Panda381/BarePi/_www/img/BarePi_TestLed5_m.jpg

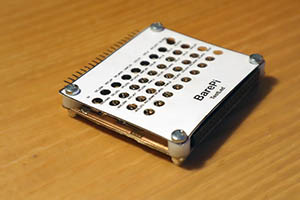
_www/img/BarePi_TestLed5_m.jpg
