Panda381/BarePi/_www/img/BarePi_TestLed1_m.jpg

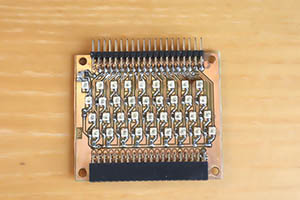
_www/img/BarePi_TestLed1_m.jpg
