Panda381/BarePi/_www/img/BarePi.jpg

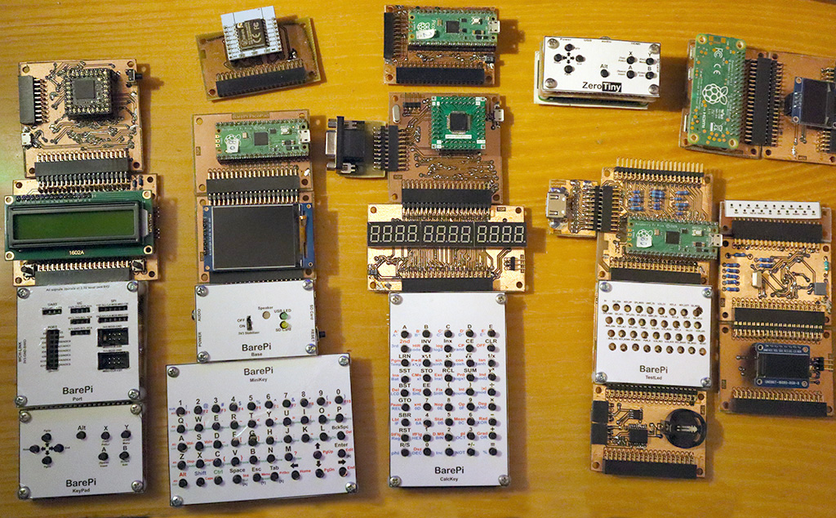
_www/img/BarePi.jpg
