Panda381/BarePi/_www/img/BarePi_Base1.jpg

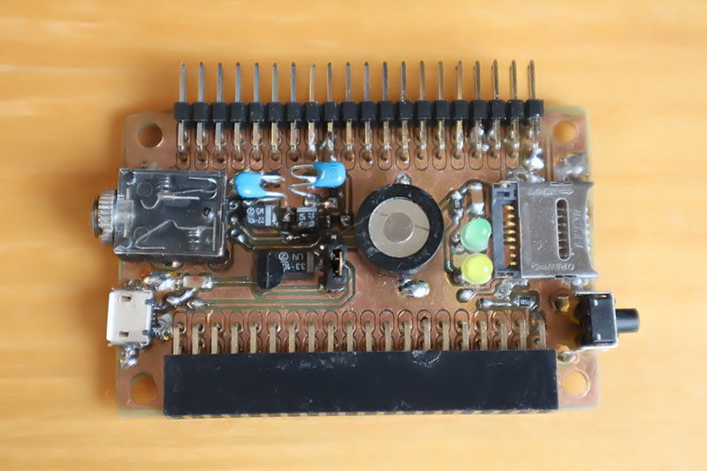
_www/img/BarePi_Base1.jpg
