Panda381/BarePi/_www/img/BarePi_Base3.jpg

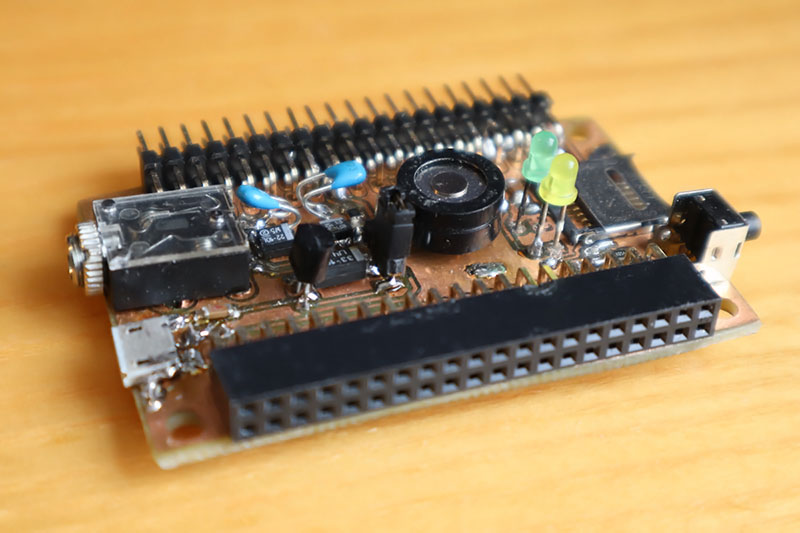
_www/img/BarePi_Base3.jpg
