Panda381/BarePi/Base/BarePi_Base_3D.jpg

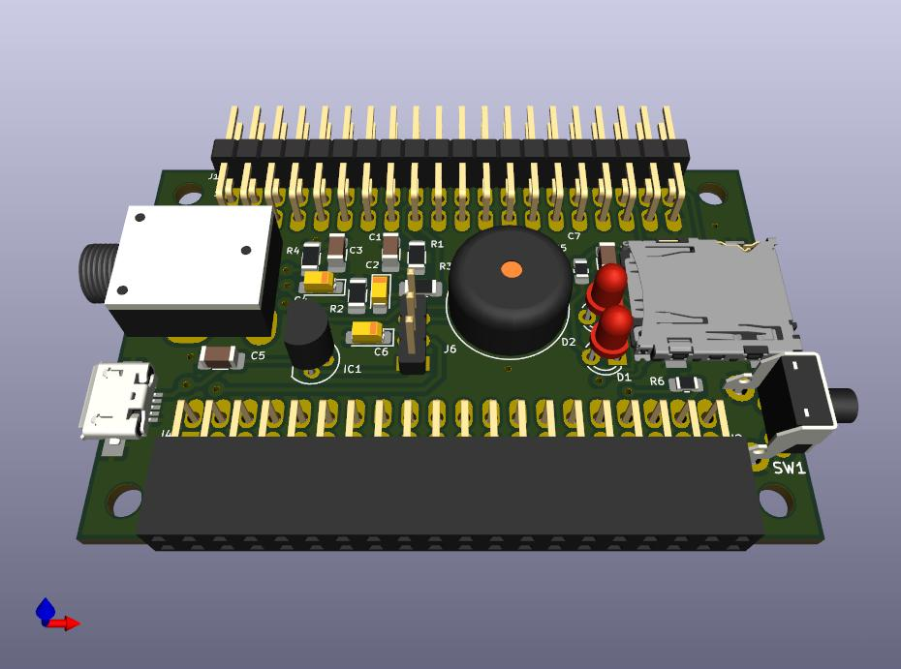
_www/img/BarePi_Base_3D.jpg
