Panda381/BarePi/_www/img/BarePi_Base_3D_bottom_m.jpg

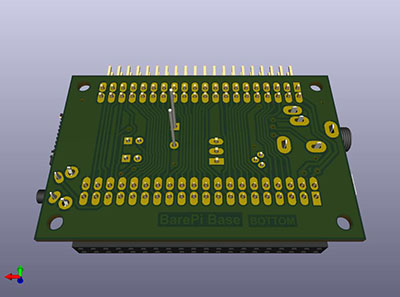
_www/img/BarePi_Base_3D_bottom_m.jpg
