Panda381/BarePi/Base/BarePi_Base_bottom.png

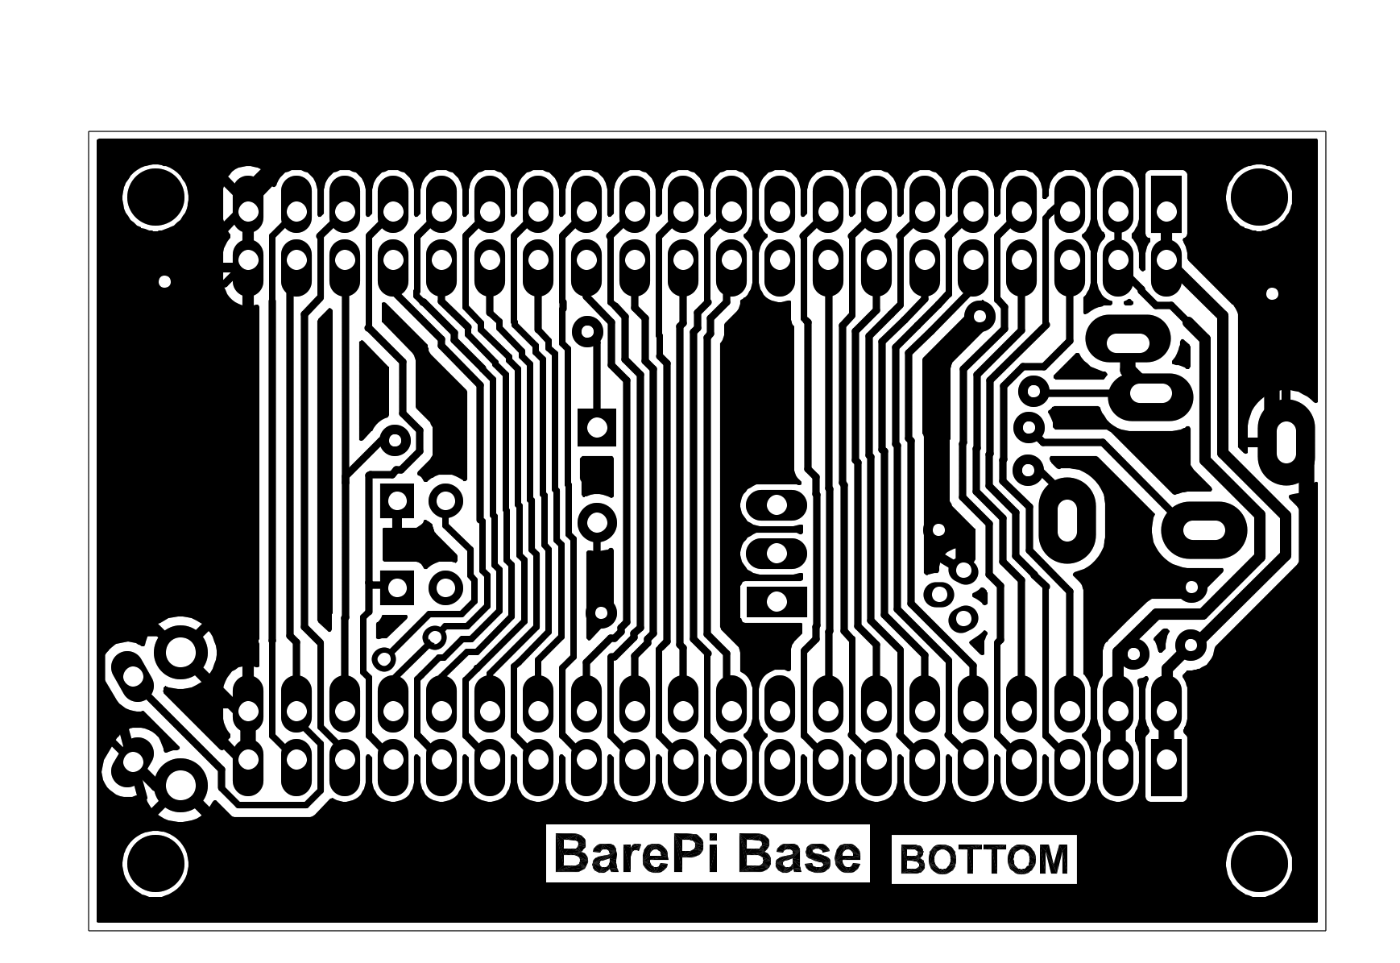
_www/img/BarePi_Base_bottom.png
