Panda381/BarePi/Base/BarePi_Base_diagram.png

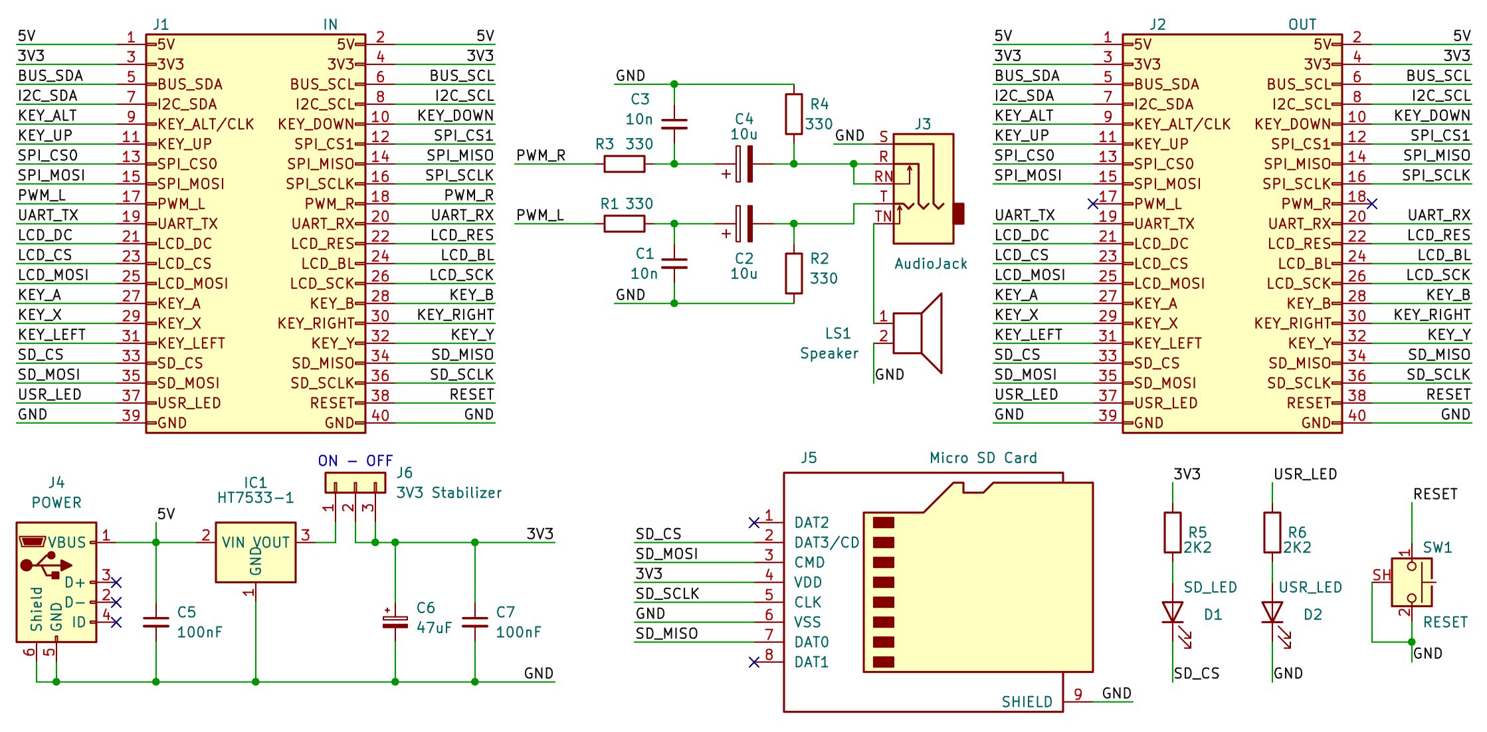
_www/img/BarePi_Base_diagram.png
