Panda381/BarePi/_www/img/BarePi_Base_label_m.jpg

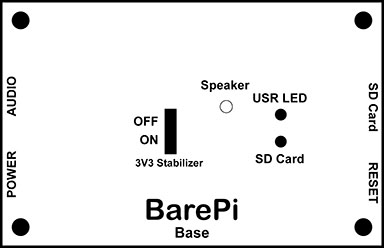
_www/img/BarePi_Base_label_m.jpg
