Panda381/BarePi/_www/img/BarePi_BusExp1.jpg

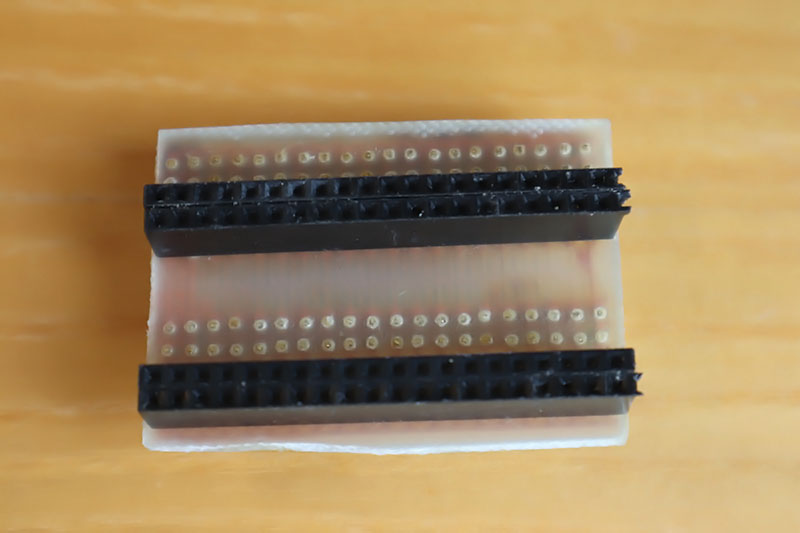
_www/img/BarePi_BusExp1.jpg
