Panda381/BarePi/_www/img/BarePi_BusExp2_m.jpg

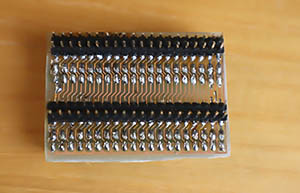
_www/img/BarePi_BusExp2_m.jpg
