Panda381/BarePi/_www/img/BarePi_BusExp3.jpg

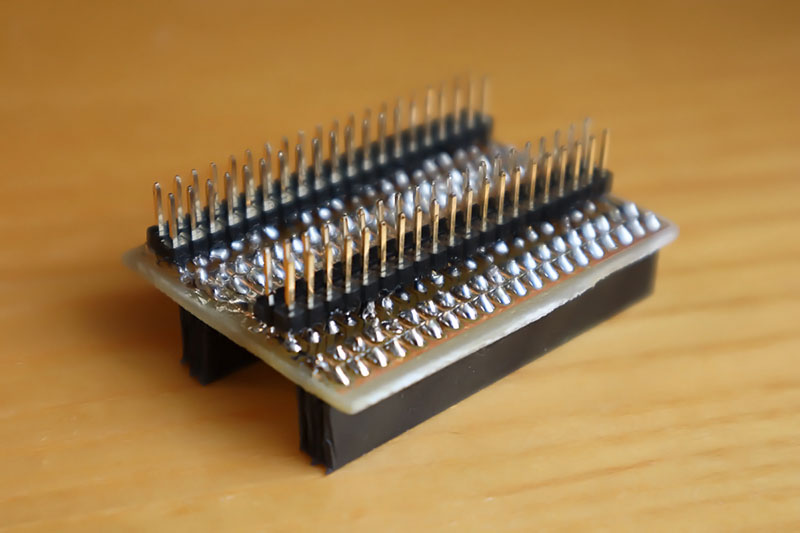
_www/img/BarePi_BusExp3.jpg
