Panda381/BarePi/BusExp/BarePi_BusExp_3D_bottom.jpg

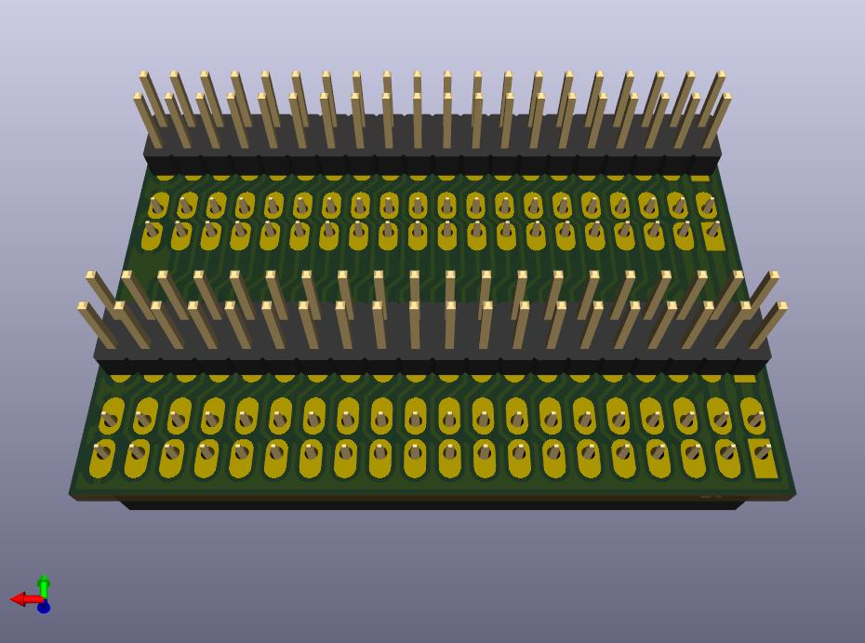
_www/img/BarePi_BusExp_3D_bottom.jpg
