Panda381/BarePi/_www/img/BarePi_BusExp_bottom_m.jpg

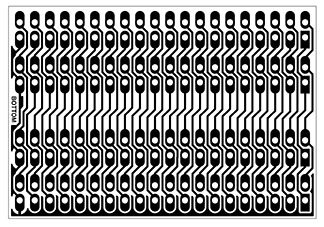
_www/img/BarePi_BusExp_bottom_m.jpg
