Panda381/BarePi/_www/img/BarePi_BusExp_diagram_m.jpg

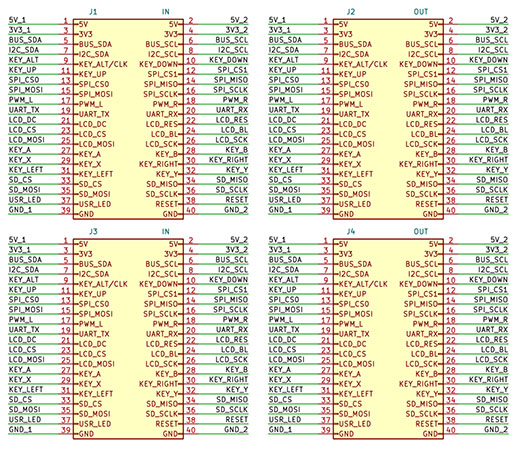
_www/img/BarePi_BusExp_diagram_m.jpg
