Panda381/BarePi/_www/img/BarePi_BusExp_top_m.jpg

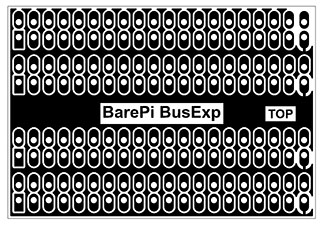
_www/img/BarePi_BusExp_top_m.jpg
