Panda381/BarePi/_www/img/BarePi_CalcKey2_m.jpg

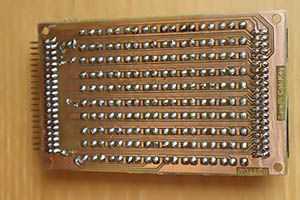
_www/img/BarePi_CalcKey2_m.jpg
