Panda381/BarePi/_www/img/BarePi_CalcKey3.jpg

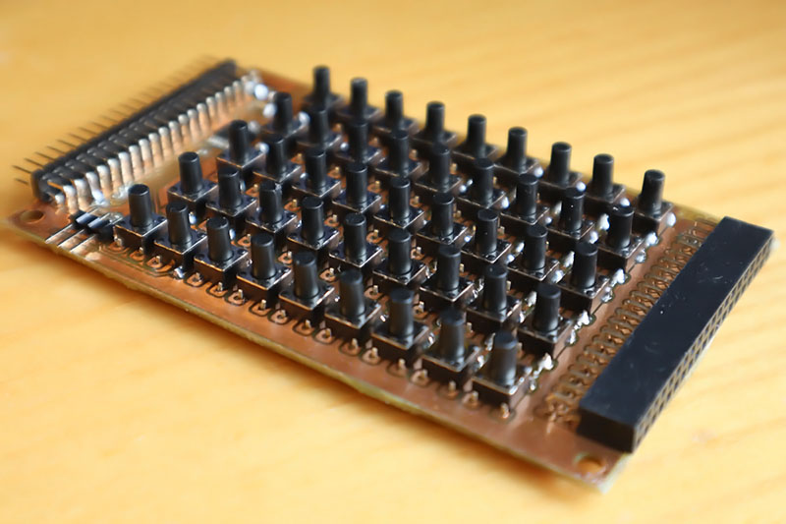
_www/img/BarePi_CalcKey3.jpg
