Panda381/BarePi/CalcKey/BarePi_CalcKey_bottom.png

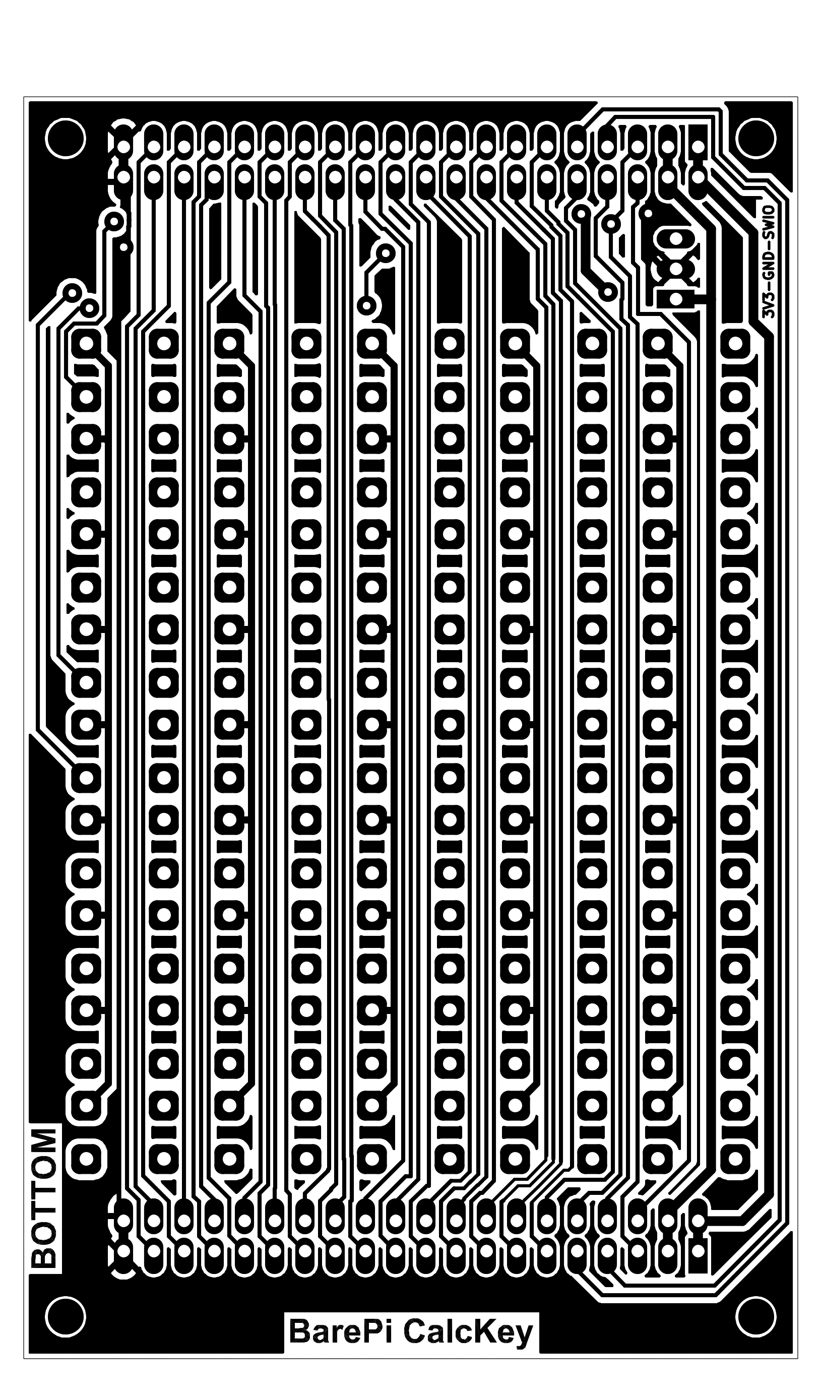
_www/img/BarePi_CalcKey_bottom.png
