Panda381/BarePi/_www/img/BarePi_CalcKey_mounting_m.jpg

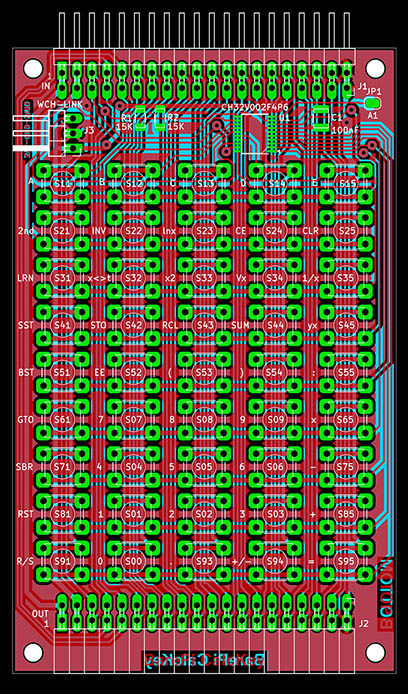
_www/img/BarePi_CalcKey_mounting_m.jpg
