Panda381/BarePi/CalcKey/BarePi_CalcKey_top.png

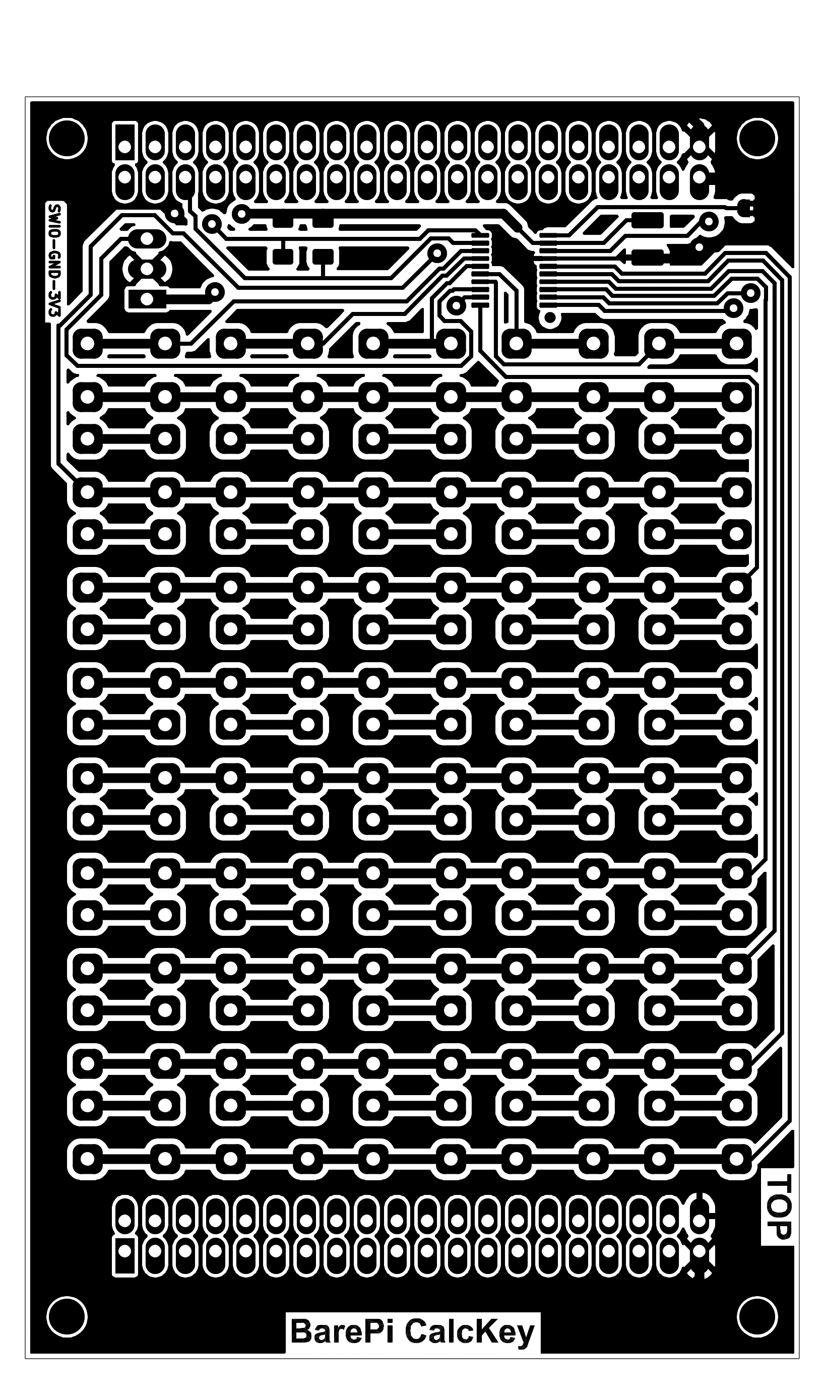
_www/img/BarePi_CalcKey_top.png
