Panda381/BarePi/_www/img/BarePi_DispHDMI1.jpg

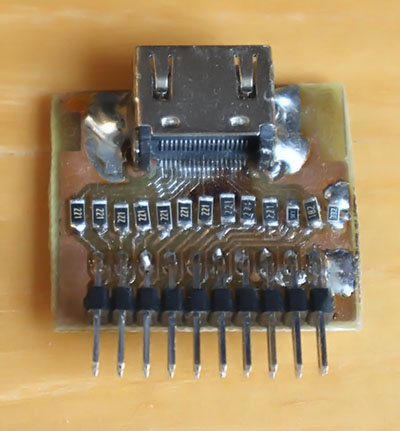
_www/img/BarePi_DispHDMI1.jpg
