Panda381/BarePi/DispHDMI/BarePi_DispHDMI_3D.jpg

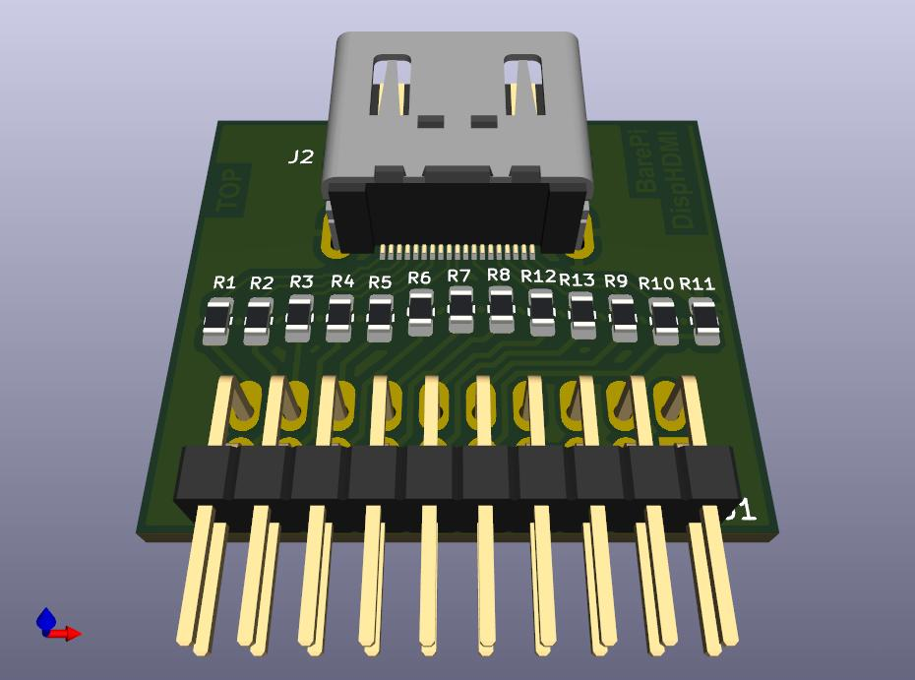
_www/img/BarePi_DispHDMI_3D.jpg
