Panda381/BarePi/DispHDMI/BarePi_DispHDMI_bottom.png

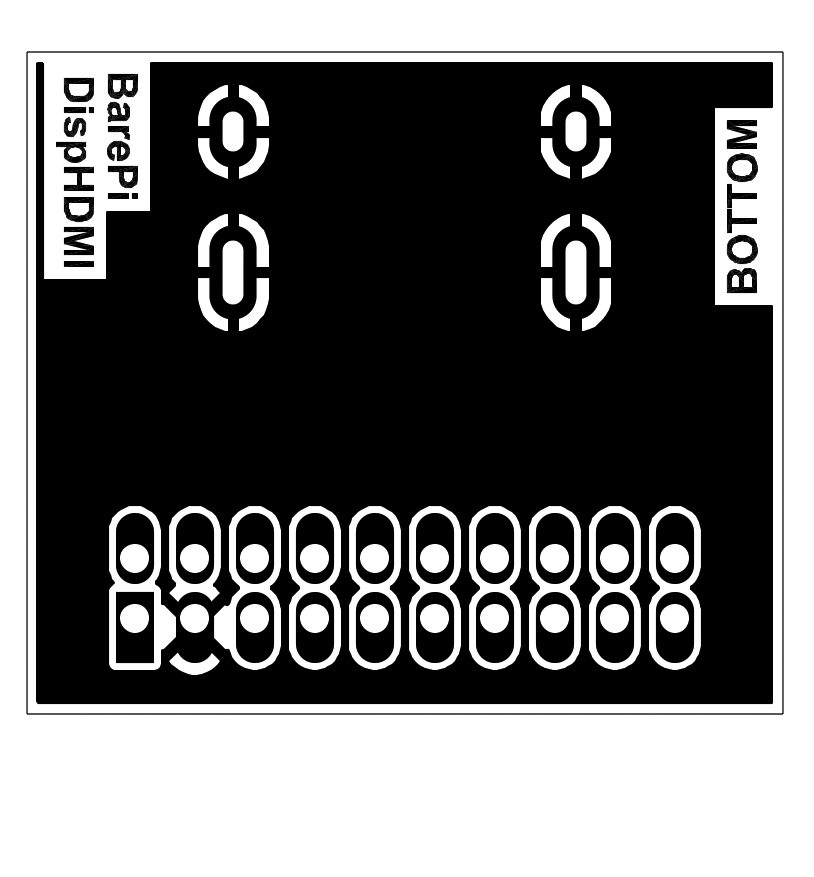
_www/img/BarePi_DispHDMI_bottom.png
