Panda381/BarePi/DispHDMI/BarePi_DispHDMI_diagram.png

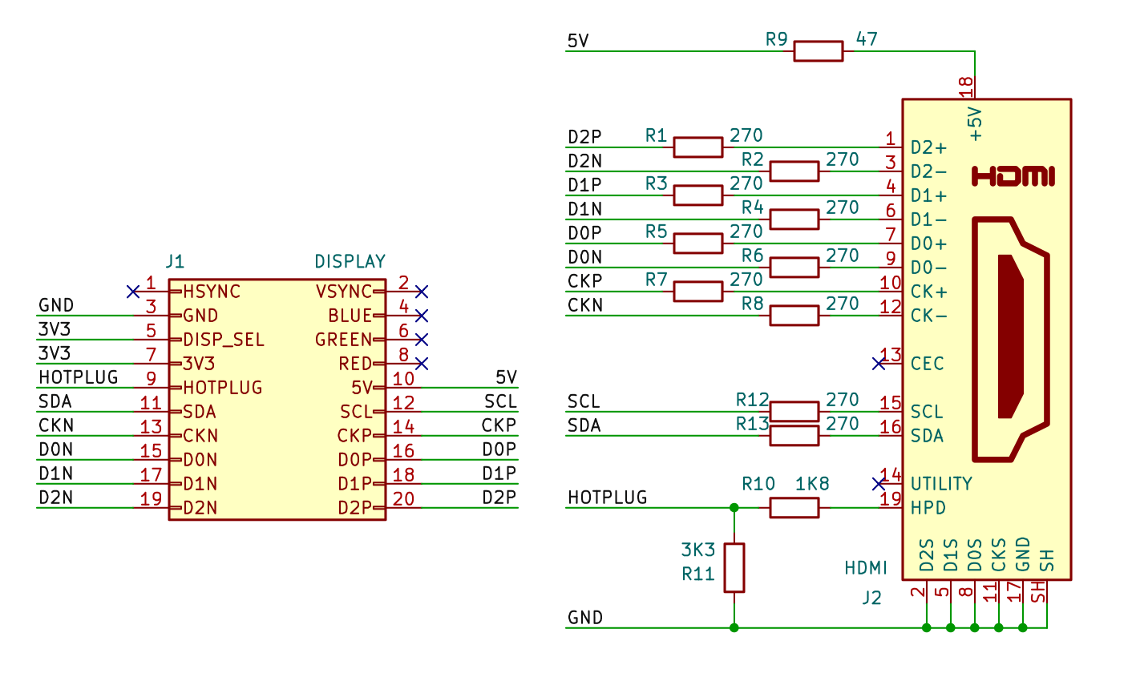
_www/img/BarePi_DispHDMI_diagram.png
