Panda381/BarePi/DispHDMI/BarePi_DispHDMI_mounting.jpg

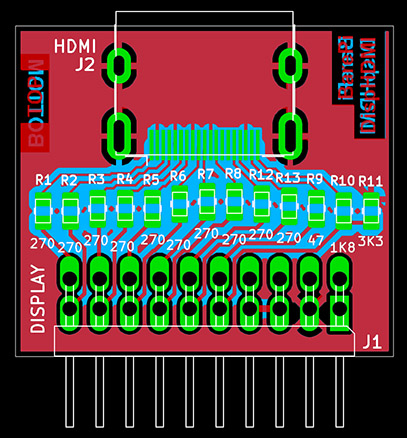
_www/img/BarePi_DispHDMI_mounting.jpg
