Panda381/BarePi/DispHDMI/BarePi_DispHDMI_top.png

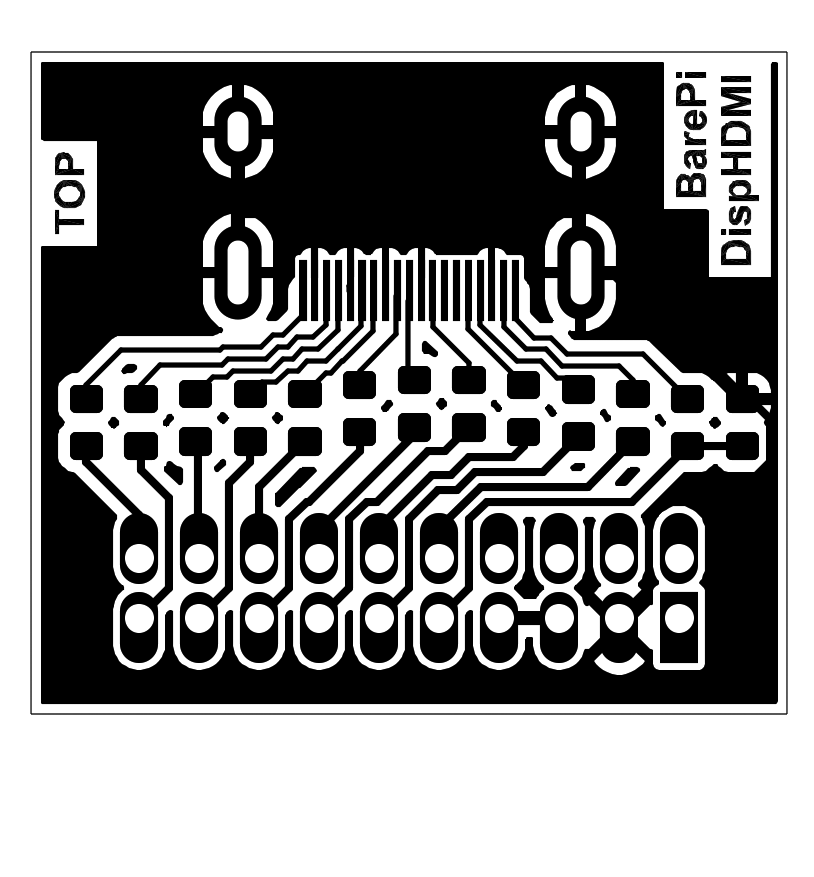
_www/img/BarePi_DispHDMI_top.png
