Panda381/BarePi/_www/img/BarePi_disppins2_m.jpg

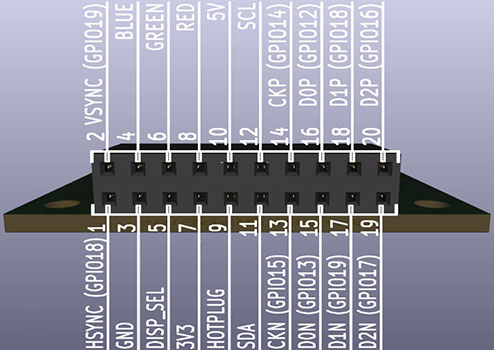
_www/img/BarePi_disppins2_m.jpg
