Panda381/BarePi/_www/img/BarePi_disppins.png

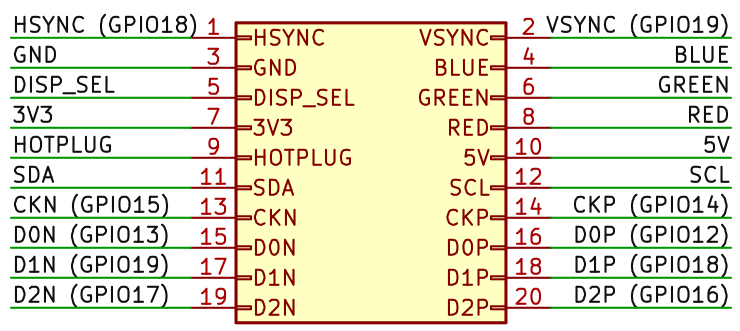
_www/img/BarePi_disppins.png
