Panda381/BarePi/_www/img/BarePi_DispVGA1_m.jpg

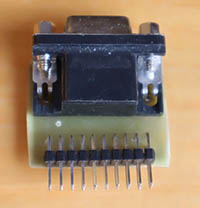
_www/img/BarePi_DispVGA1_m.jpg
