Panda381/BarePi/_www/img/BarePi_DispVGA2.jpg

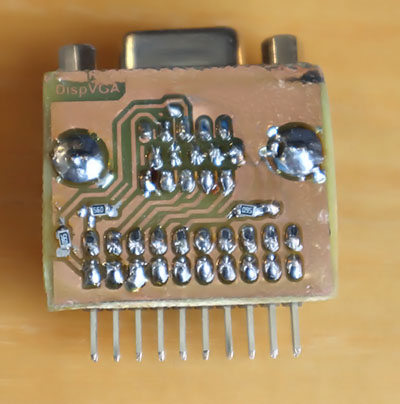
_www/img/BarePi_DispVGA2.jpg
