Panda381/BarePi/_www/img/BarePi_DispVGA_3D_bottom_m.jpg

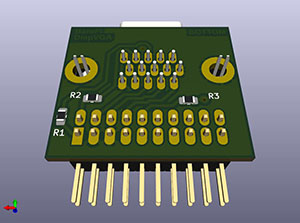
_www/img/BarePi_DispVGA_3D_bottom_m.jpg
