Panda381/BarePi/_www/img/BarePi_DispVGA_diagram_m.jpg

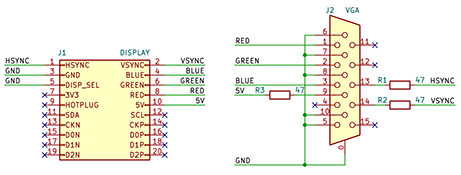
_www/img/BarePi_DispVGA_diagram_m.jpg
