Panda381/BarePi/DispVGA/BarePi_DispVGA_mounting.jpg

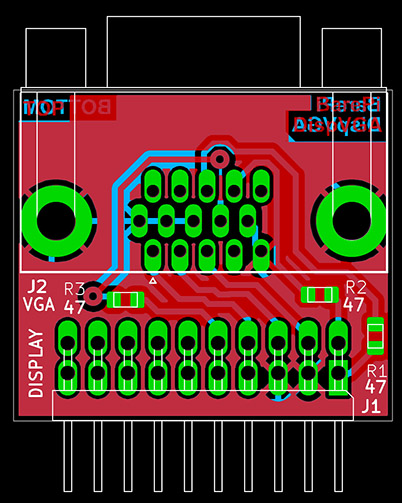
_www/img/BarePi_DispVGA_mounting.jpg
