Panda381/BarePi/_www/img/BarePi_ExtDisp1.jpg

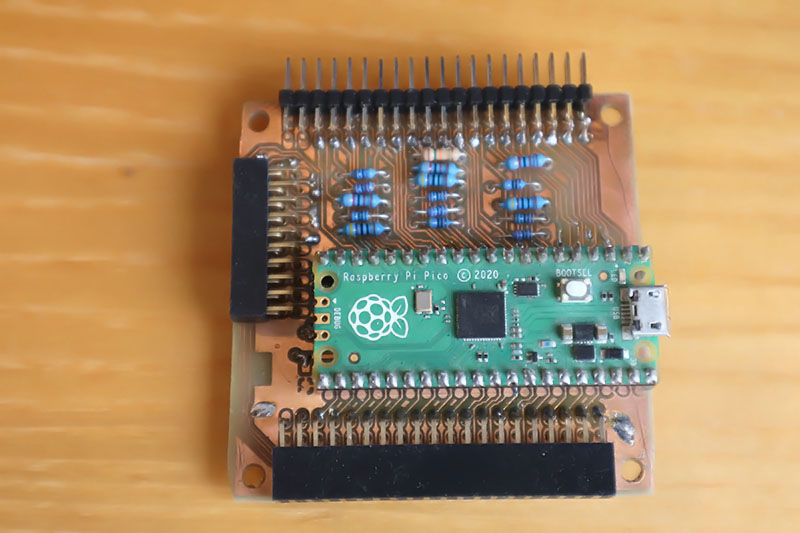
_www/img/BarePi_ExtDisp1.jpg
