Panda381/BarePi/_www/img/BarePi_ExtDisp3_m.jpg

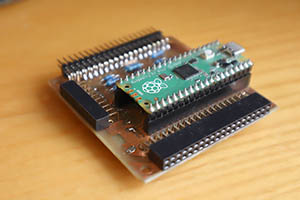
_www/img/BarePi_ExtDisp3_m.jpg
