Panda381/BarePi/_www/img/BarePi_ExtDisp.jpg

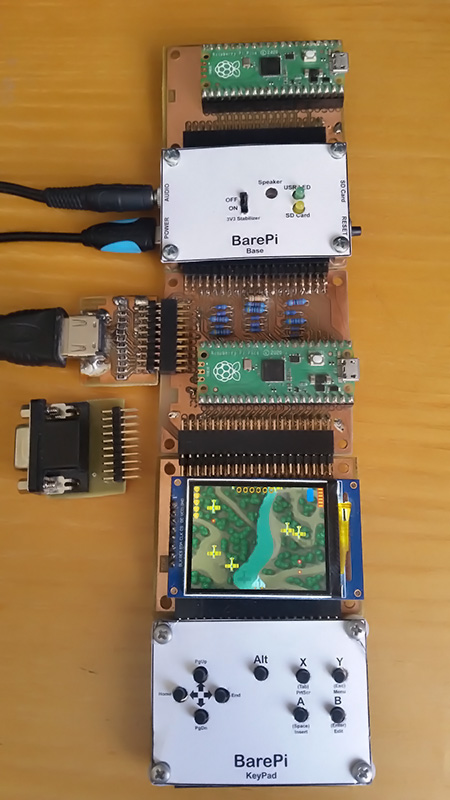
_www/img/BarePi_ExtDisp.jpg
