Panda381/BarePi/ExtDisp/BarePi_ExtDisp_3D.jpg

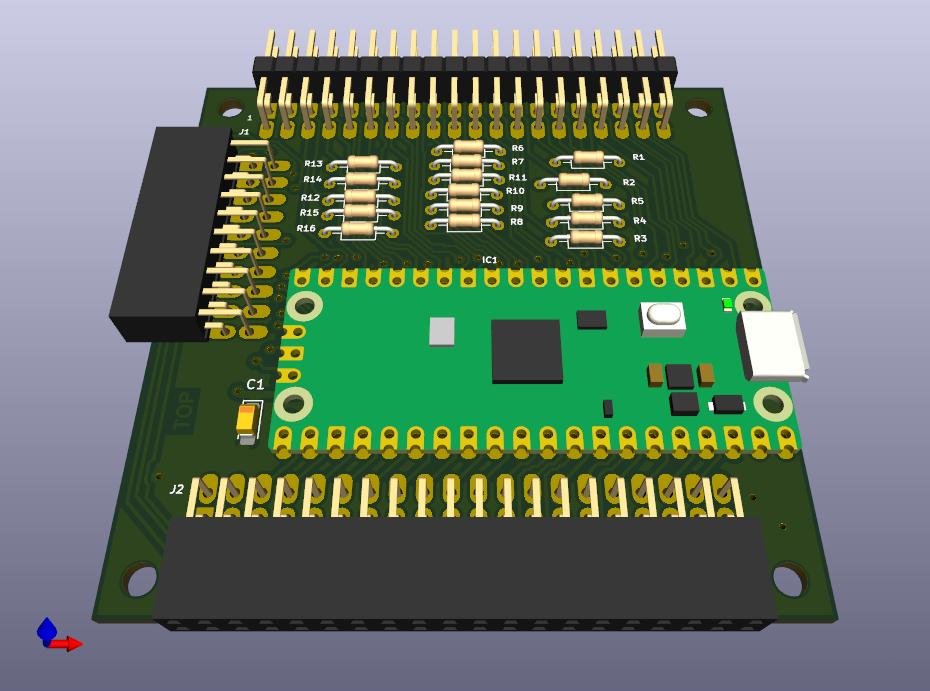
_www/img/BarePi_ExtDisp_3D.jpg
