Panda381/BarePi/ExtDisp/BarePi_ExtDisp_bottom.png

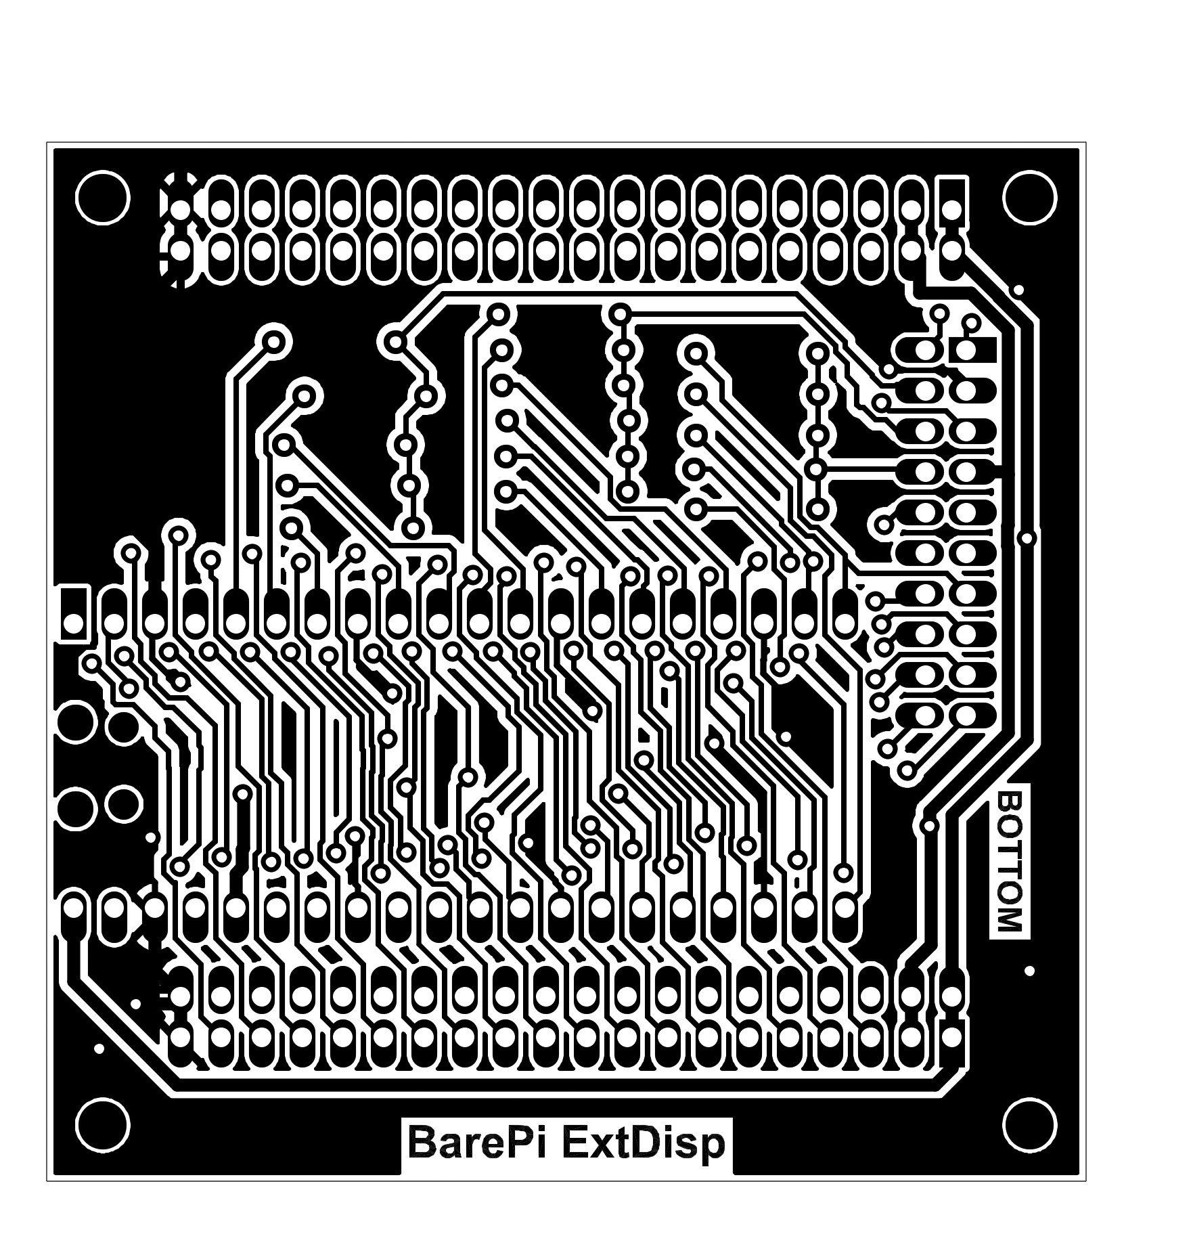
_www/img/BarePi_ExtDisp_bottom.png
