Panda381/BarePi/ExtDisp/BarePi_ExtDisp_diagram.png

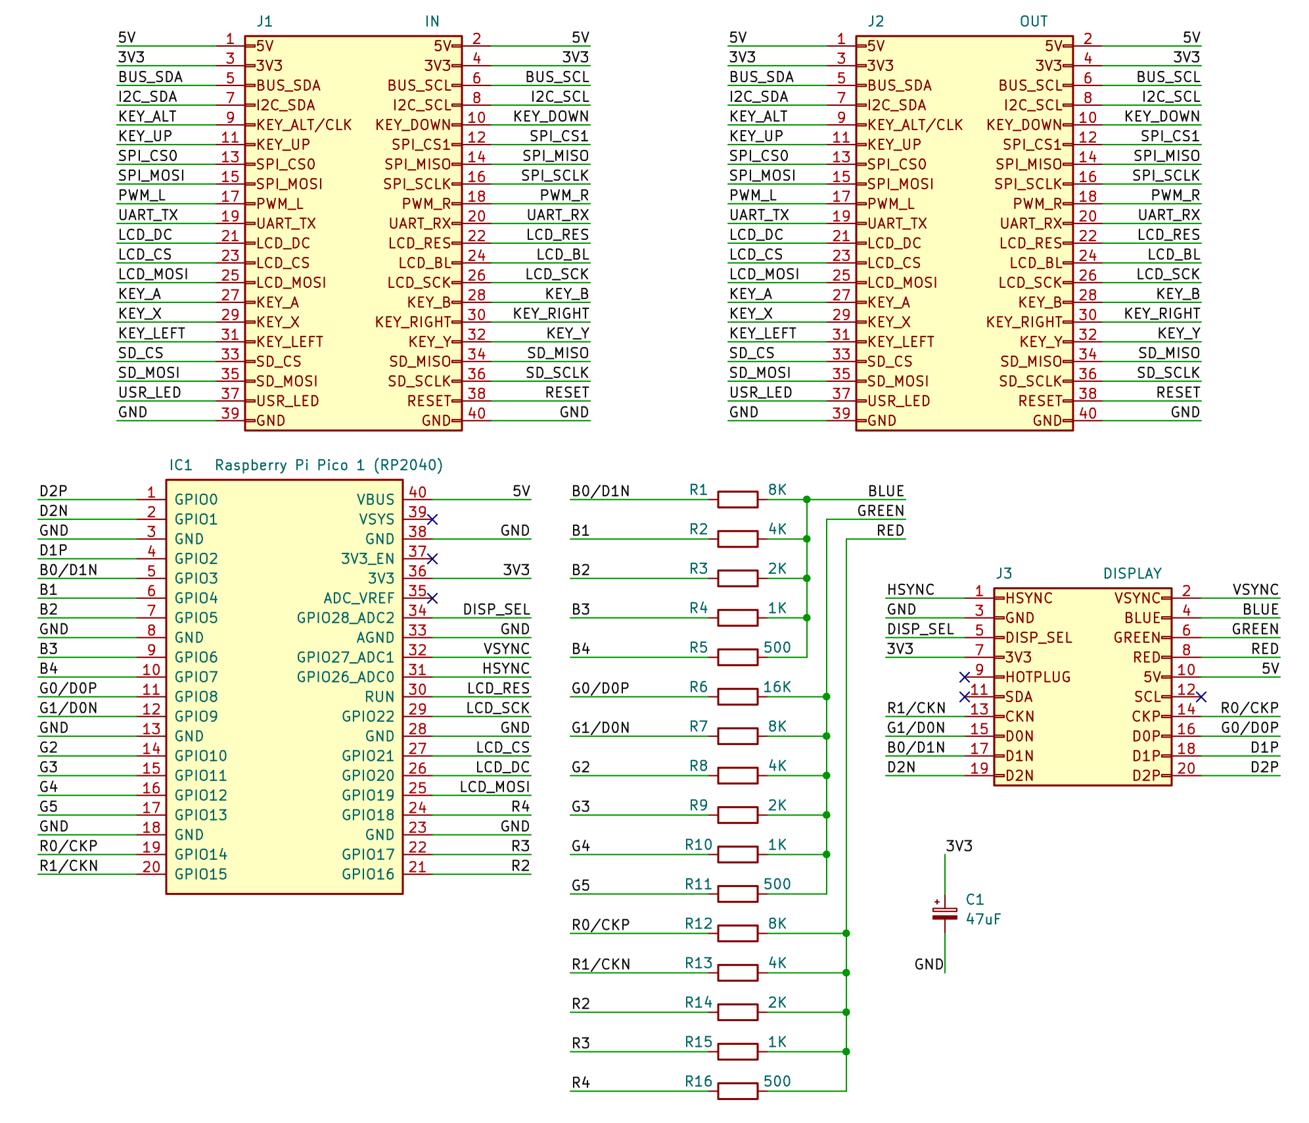
_www/img/BarePi_ExtDisp_diagram.png
