Panda381/BarePi/_www/img/BarePi_ExtDisp_label_m.jpg

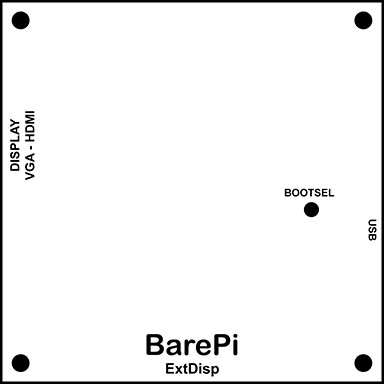
_www/img/BarePi_ExtDisp_label_m.jpg
