Panda381/BarePi/ExtDisp/BarePi_ExtDisp_mounting.jpg

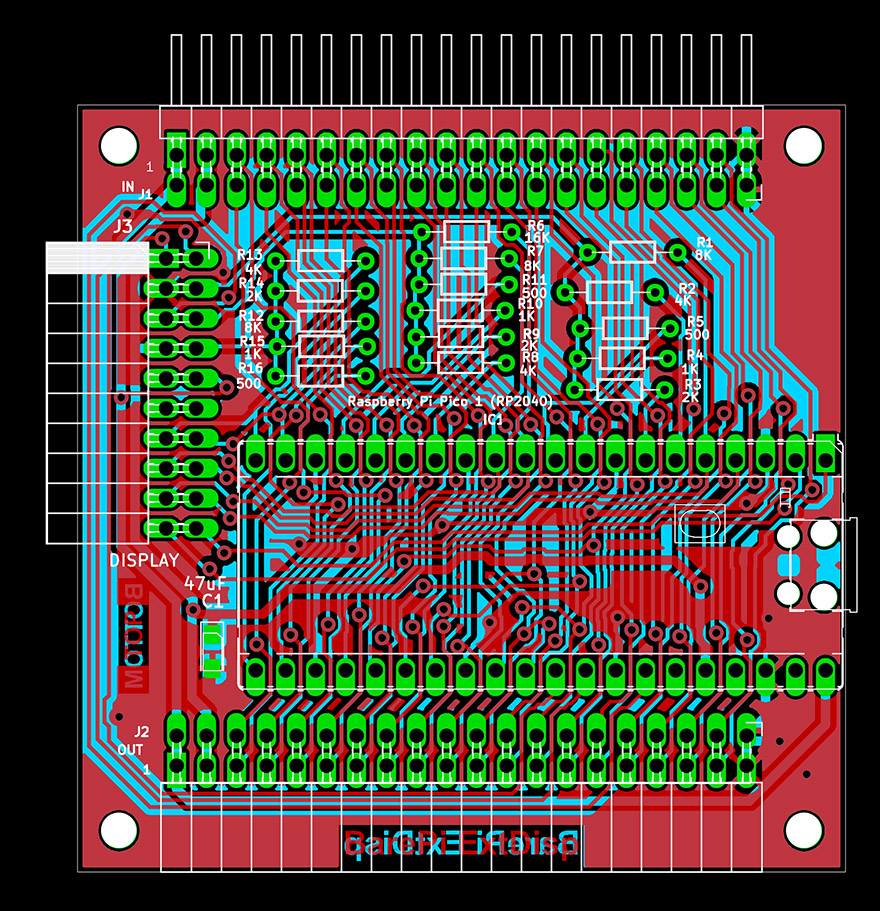
_www/img/BarePi_ExtDisp_mounting.jpg
