Panda381/BarePi/_www/img/BarePi_ExtDisp_top_m.jpg

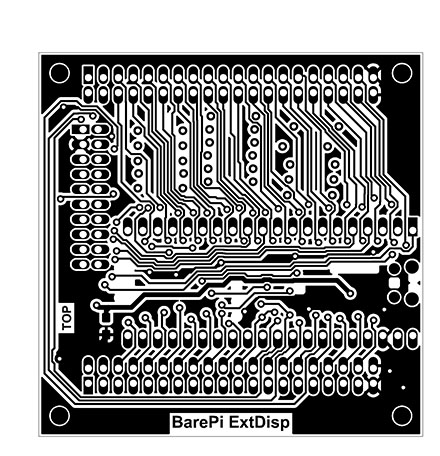
_www/img/BarePi_ExtDisp_top_m.jpg
