Panda381/BarePi/_www/img/BarePi_KeyPad1_m.jpg

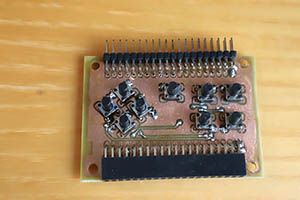
_www/img/BarePi_KeyPad1_m.jpg
