Panda381/BarePi/_www/img/BarePi_KeyPad2.jpg

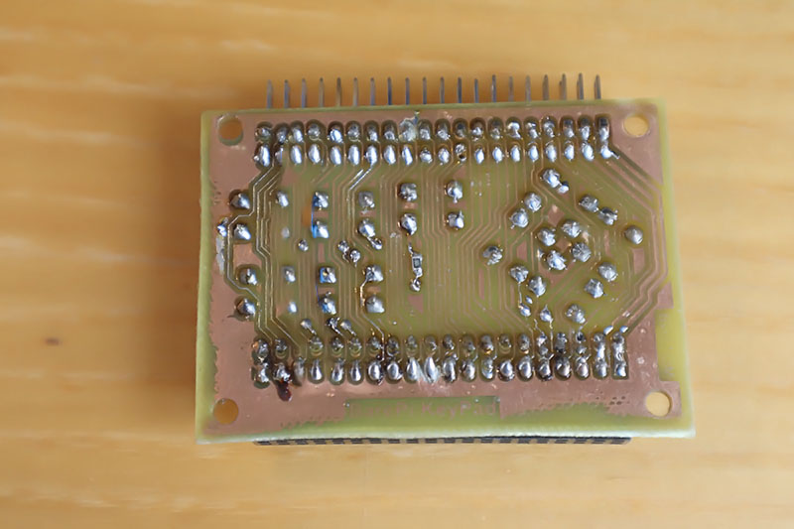
_www/img/BarePi_KeyPad2.jpg
