Panda381/BarePi/_www/img/BarePi_KeyPad3_m.jpg

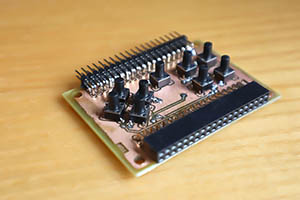
_www/img/BarePi_KeyPad3_m.jpg
