Panda381/BarePi/_www/img/BarePi_KeyPad5.jpg

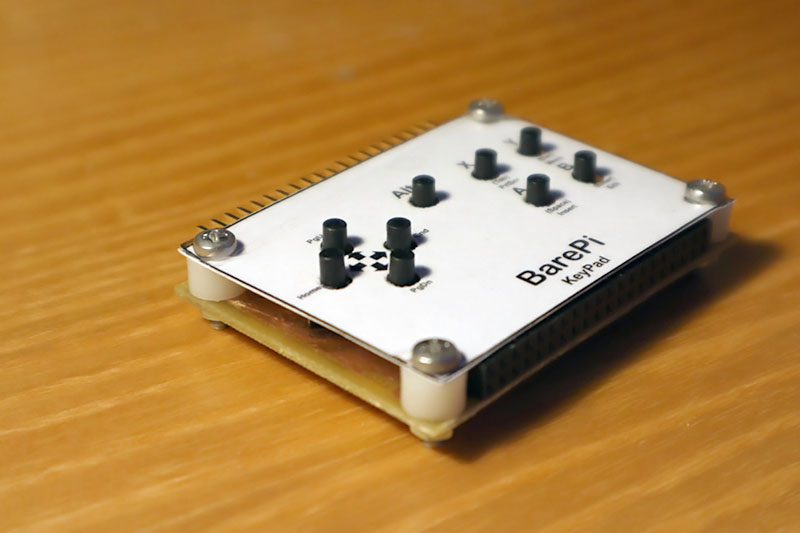
_www/img/BarePi_KeyPad5.jpg
