Panda381/BarePi/_www/img/BarePi_KeyPad_3D_bottom_m.jpg

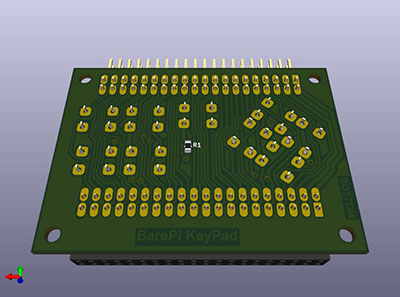
_www/img/BarePi_KeyPad_3D_bottom_m.jpg
