Panda381/BarePi/KeyPad/BarePi_KeyPad_bottom.png

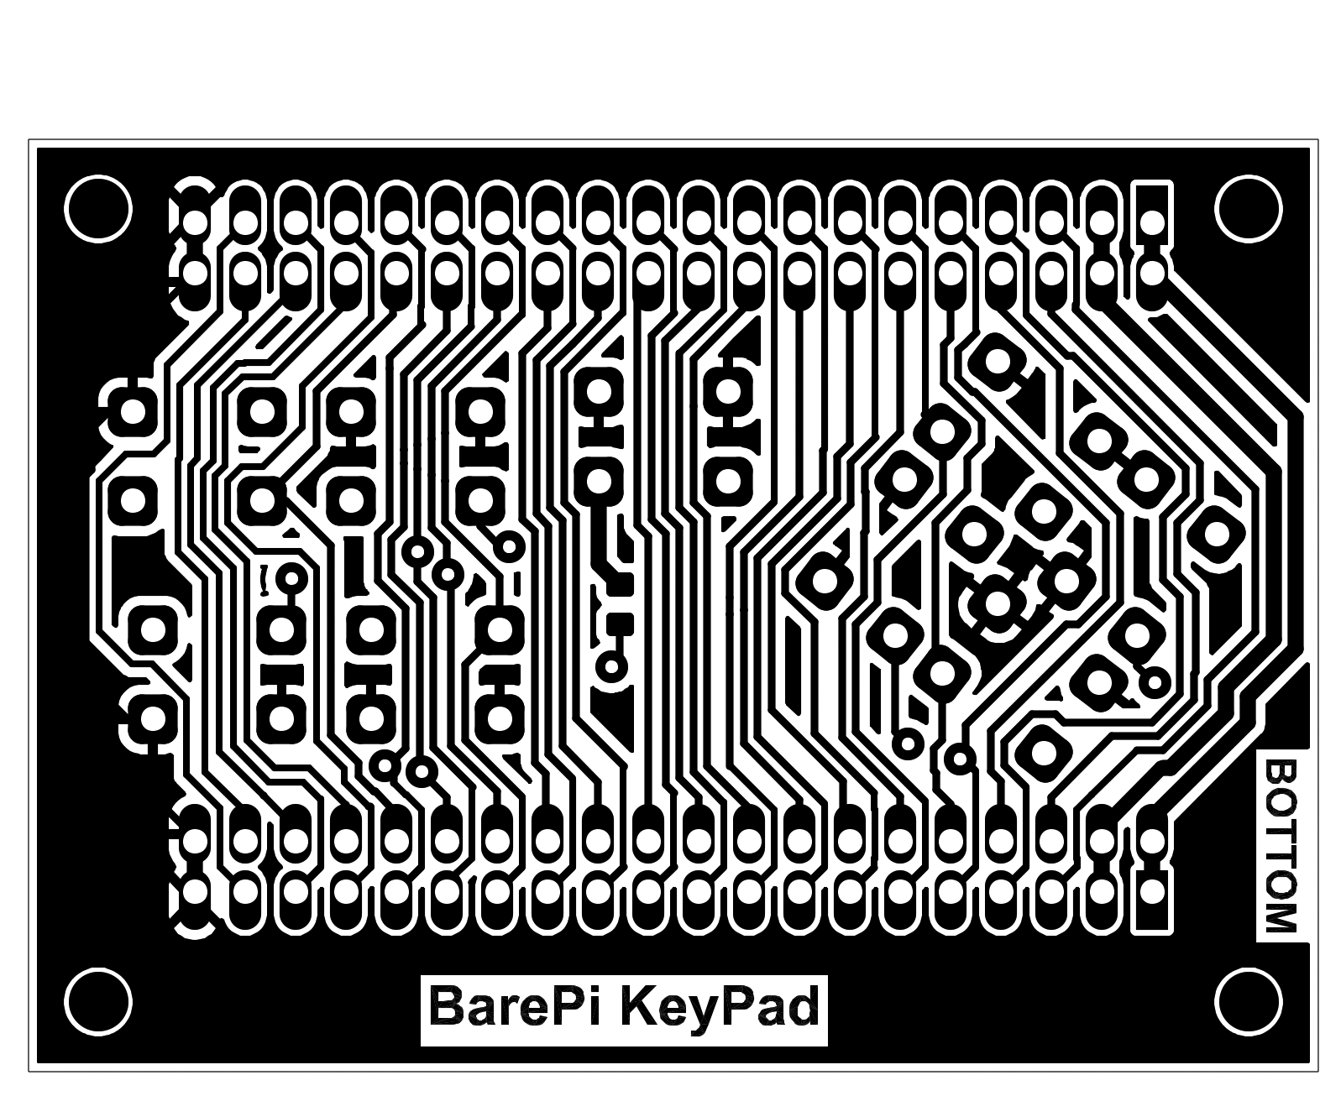
_www/img/BarePi_KeyPad_bottom.png
