Panda381/BarePi/KeyPad/BarePi_KeyPad_label.png

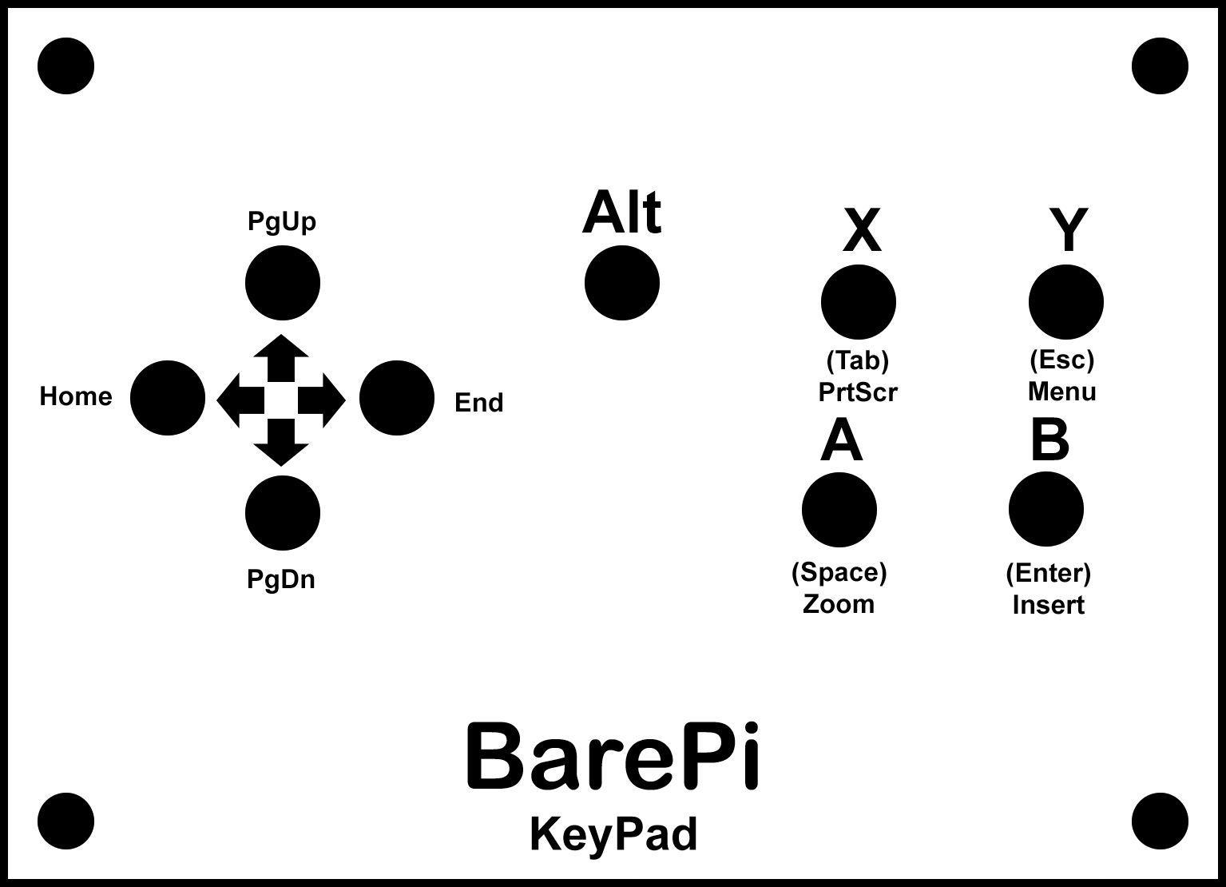
_www/img/BarePi_KeyPad_label.png
