Panda381/BarePi/_www/img/BarePi_KeyPad_mounting_m.jpg

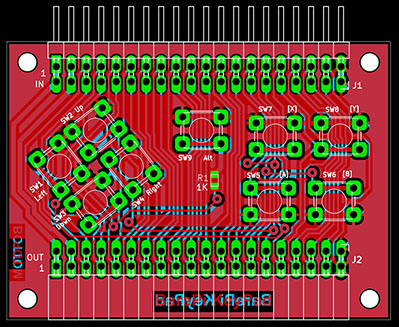
_www/img/BarePi_KeyPad_mounting_m.jpg
