Panda381/BarePi/KeyPad/BarePi_KeyPad_top.png

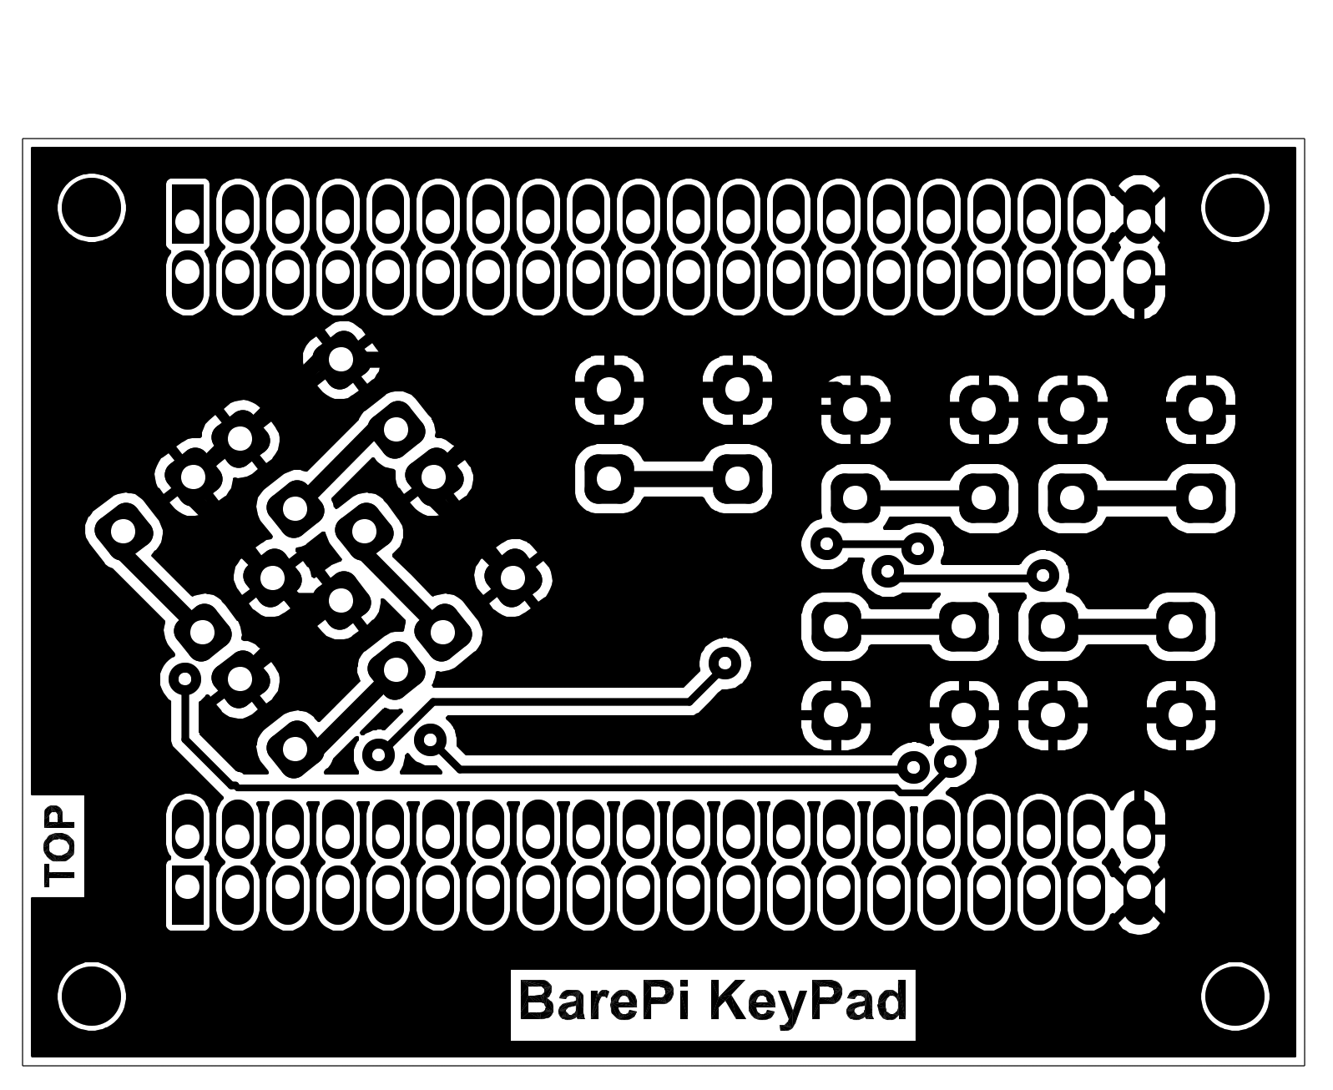
_www/img/BarePi_KeyPad_top.png
