Panda381/BarePi/LCD16x2/BarePi_LCD16x2_3D_bottom.jpg

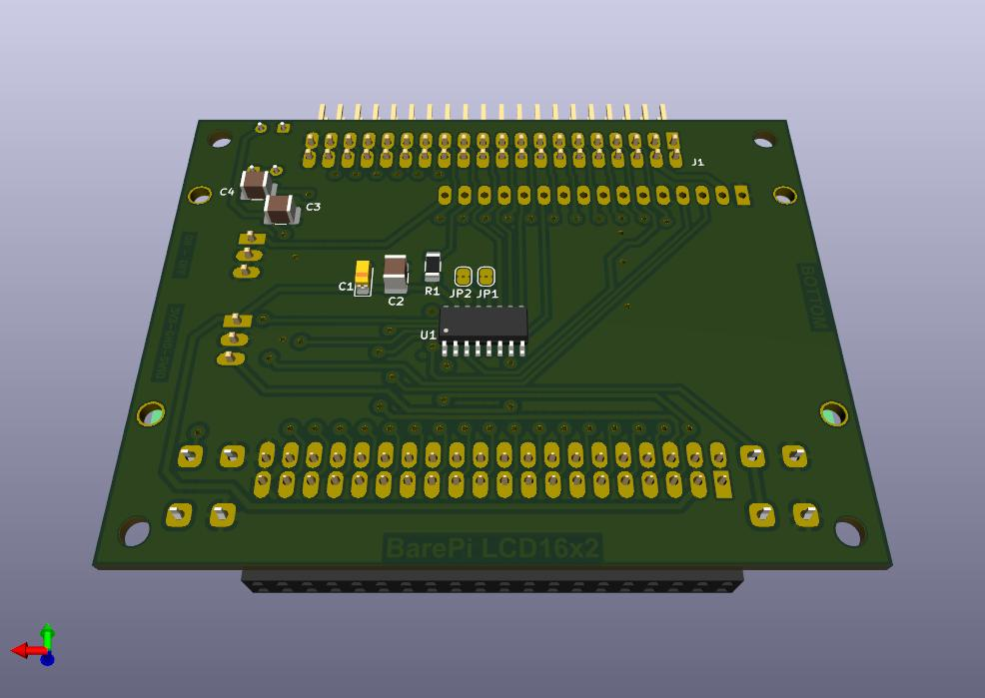
_www/img/BarePi_LCD16x2_3D_bottom.jpg
