Panda381/BarePi/LCD16x2/BarePi_LCD16x2_bottom.png

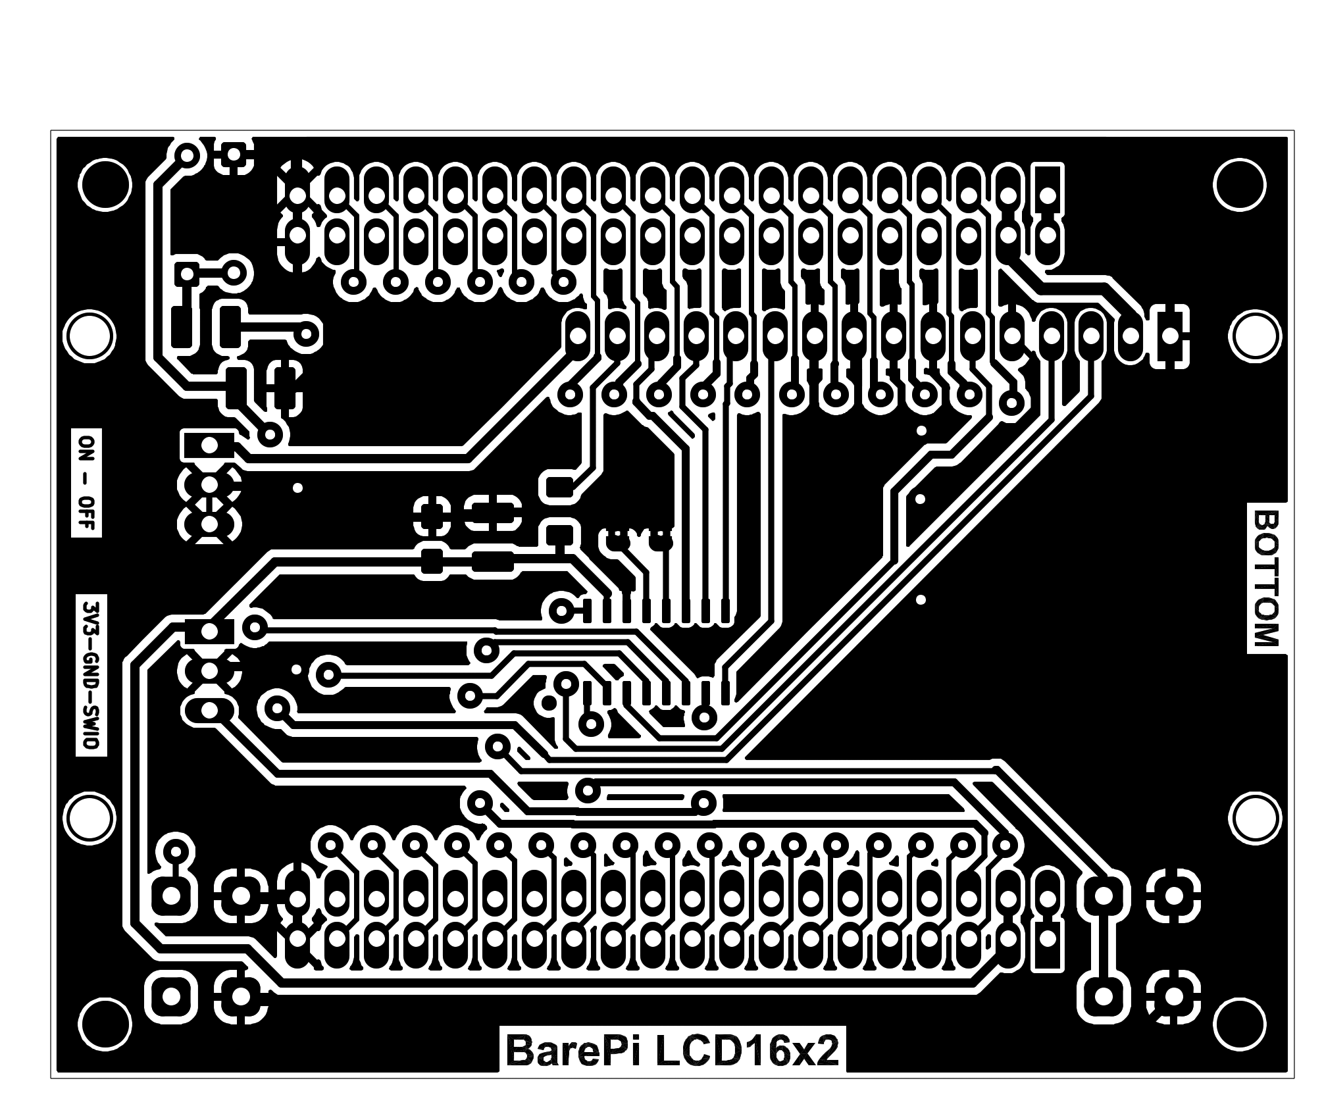
_www/img/BarePi_LCD16x2_bottom.png
