Panda381/BarePi/_www/img/BarePi_LCD16x21.jpg

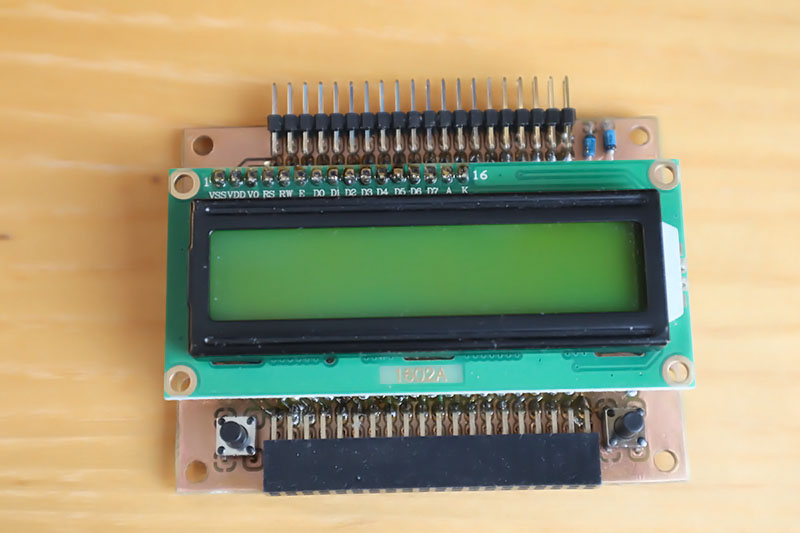
_www/img/BarePi_LCD16x21.jpg
