Panda381/BarePi/_www/img/BarePi_LCD16x23.jpg

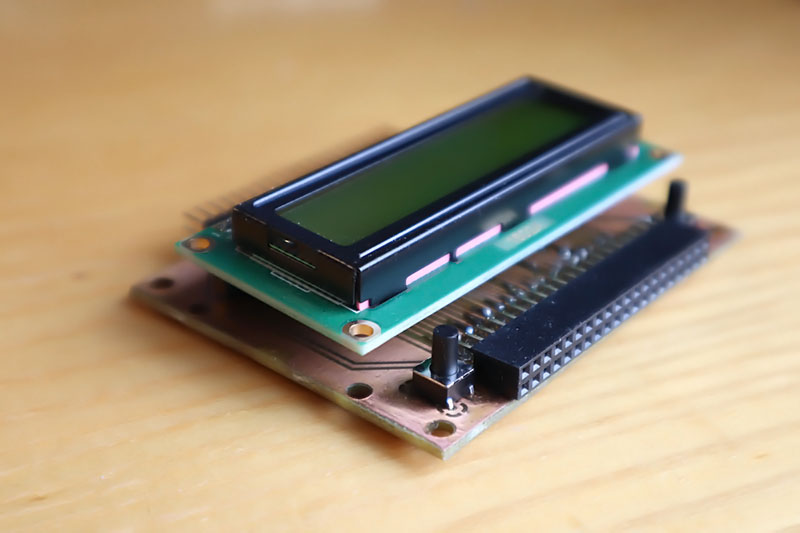
_www/img/BarePi_LCD16x23.jpg
