Panda381/BarePi/LCD160x80/BarePi_LCD160x80_3D.jpg

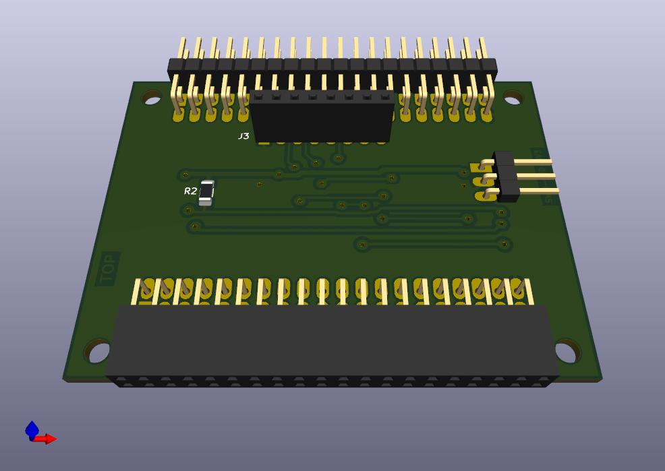
_www/img/BarePi_LCD160x80_3D.jpg
