Panda381/BarePi/LCD160x80/BarePi_LCD160x80_label.png

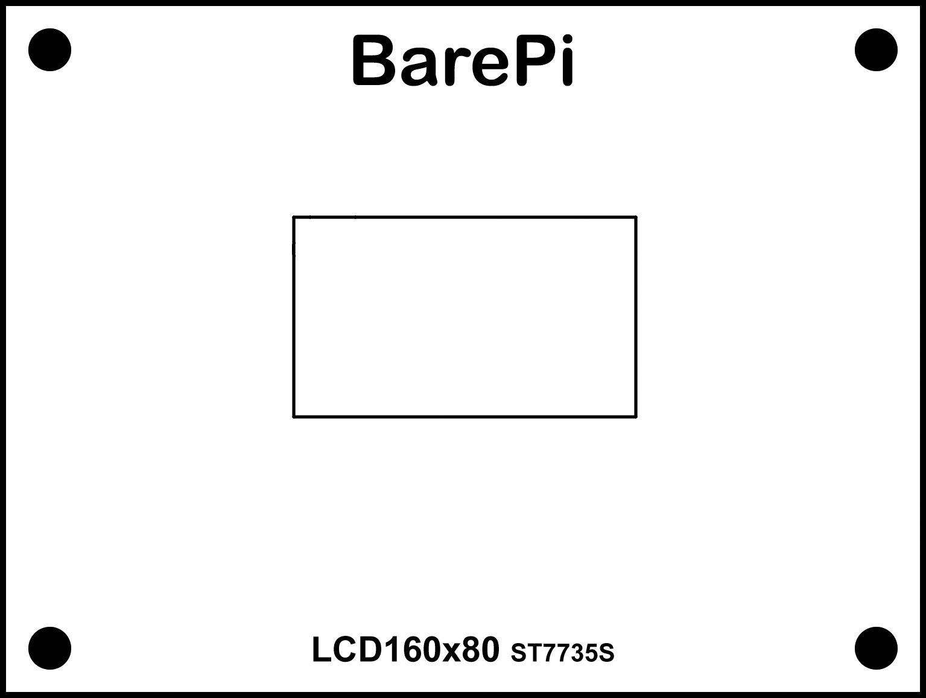
_www/img/BarePi_LCD160x80_label.png
