Panda381/BarePi/_www/img/BarePi_LCD160x80_mounting_m.jpg

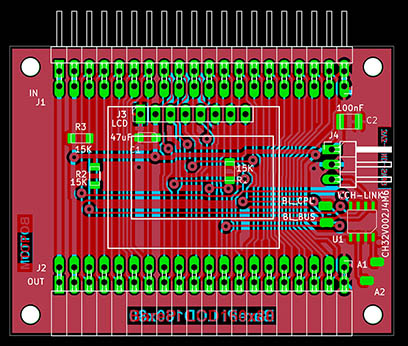
_www/img/BarePi_LCD160x80_mounting_m.jpg
