Panda381/BarePi/_www/img/BarePi_LCD160x801_m.jpg

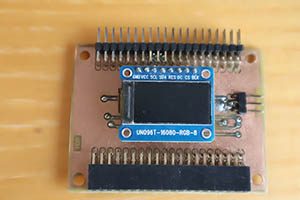
_www/img/BarePi_LCD160x801_m.jpg
