Panda381/BarePi/_www/img/BarePi_LCD160x802.jpg

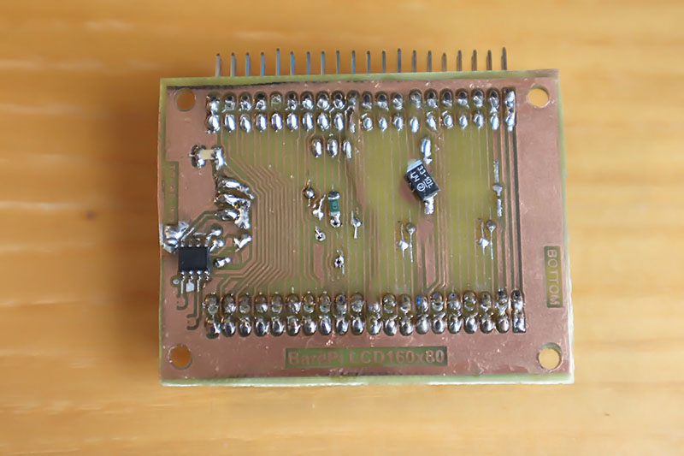
_www/img/BarePi_LCD160x802.jpg
