Panda381/BarePi/_www/img/BarePi_LCD160x803.jpg

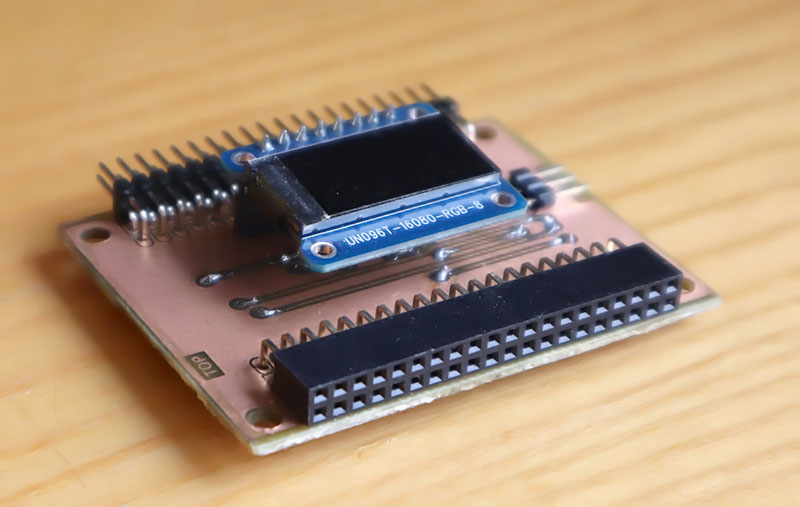
_www/img/BarePi_LCD160x803.jpg
