Panda381/BarePi/LCD320x240/BarePi_LCD320x240_3D.jpg

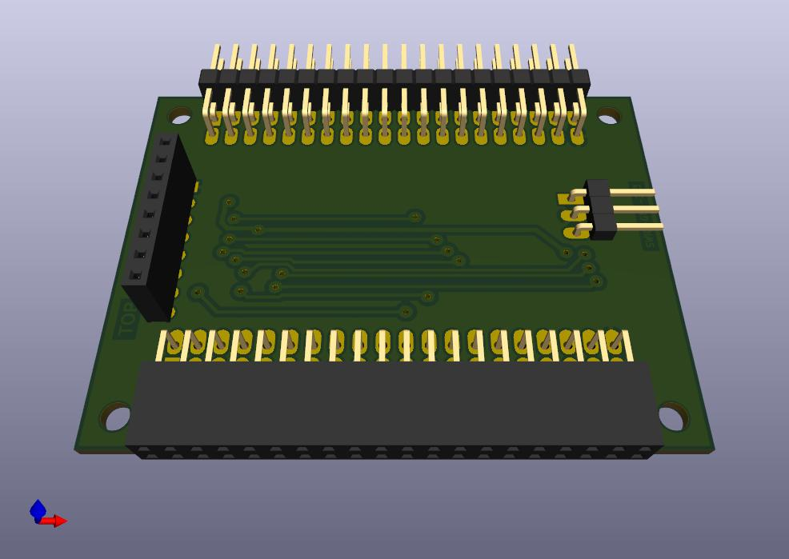
_www/img/BarePi_LCD320x240_3D.jpg
