Panda381/BarePi/LCD320x240/BarePi_LCD320x240_bottom.png

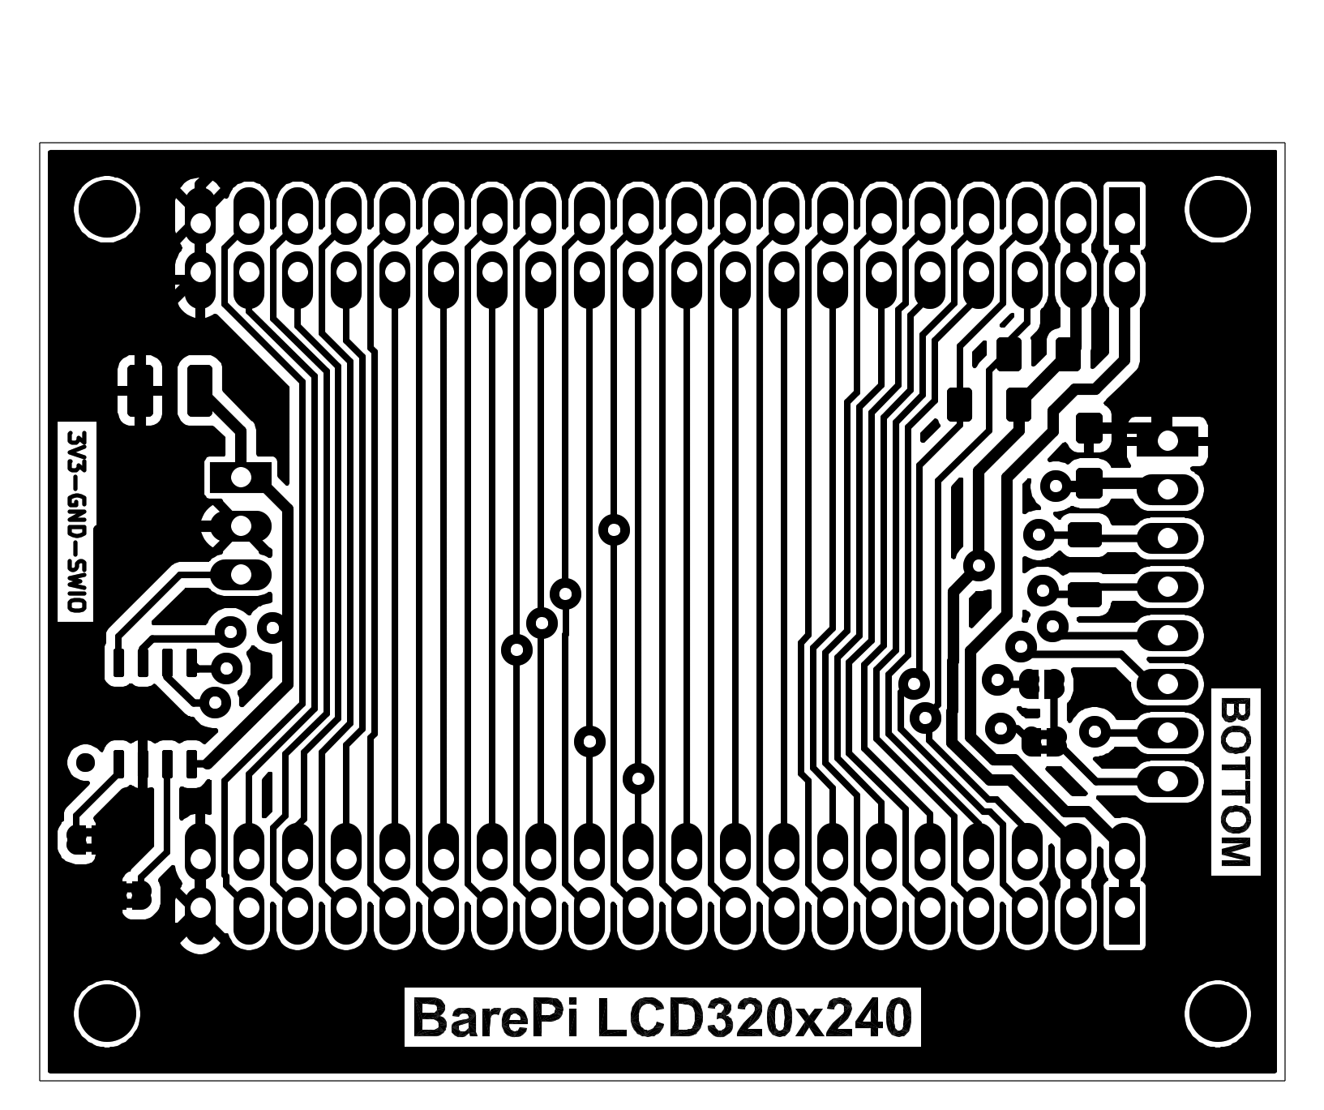
_www/img/BarePi_LCD320x240_bottom.png
