Panda381/BarePi/_www/img/BarePi_LCD320x240_mounting.jpg

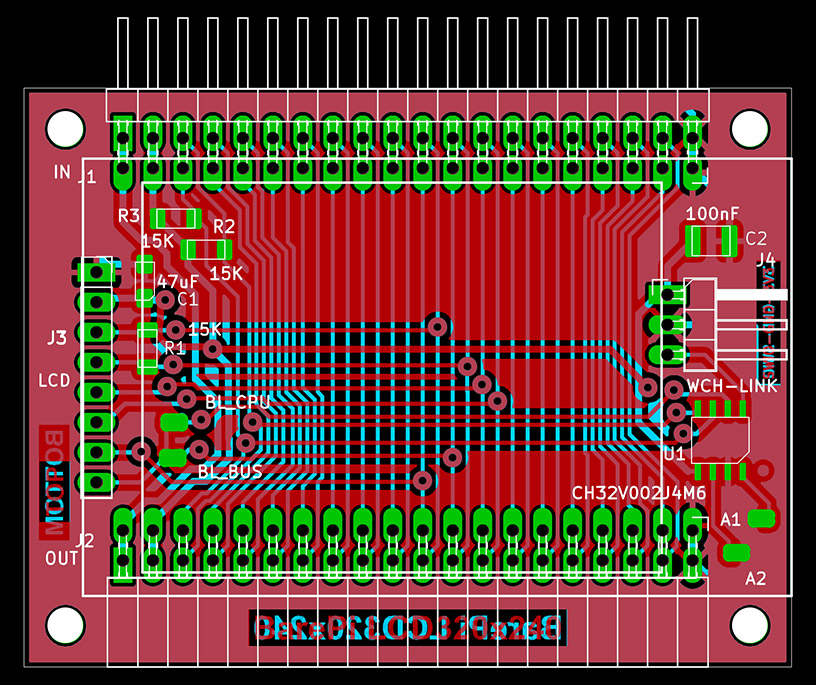
_www/img/BarePi_LCD320x240_mounting.jpg
