Panda381/BarePi/_www/img/BarePi_LCD320x2401_m.jpg

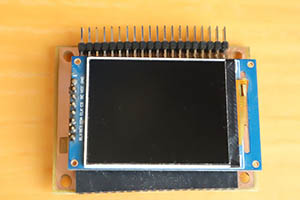
_www/img/BarePi_LCD320x2401_m.jpg
