Panda381/BarePi/LED12/BarePi_LED12_3D.jpg

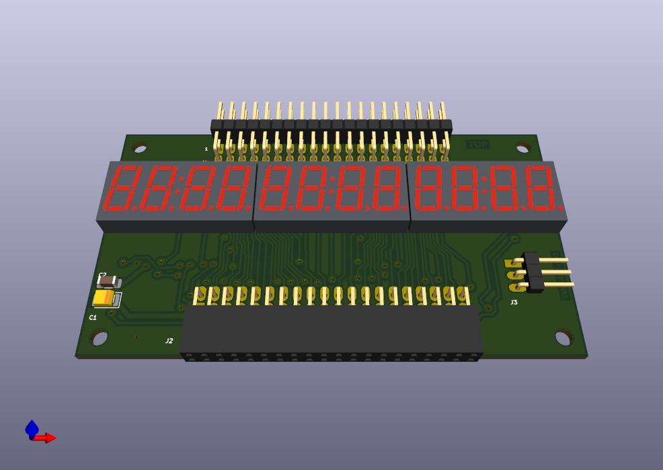
_www/img/BarePi_LED12_3D.jpg
