Panda381/BarePi/LED12/BarePi_LED12_bottom.png

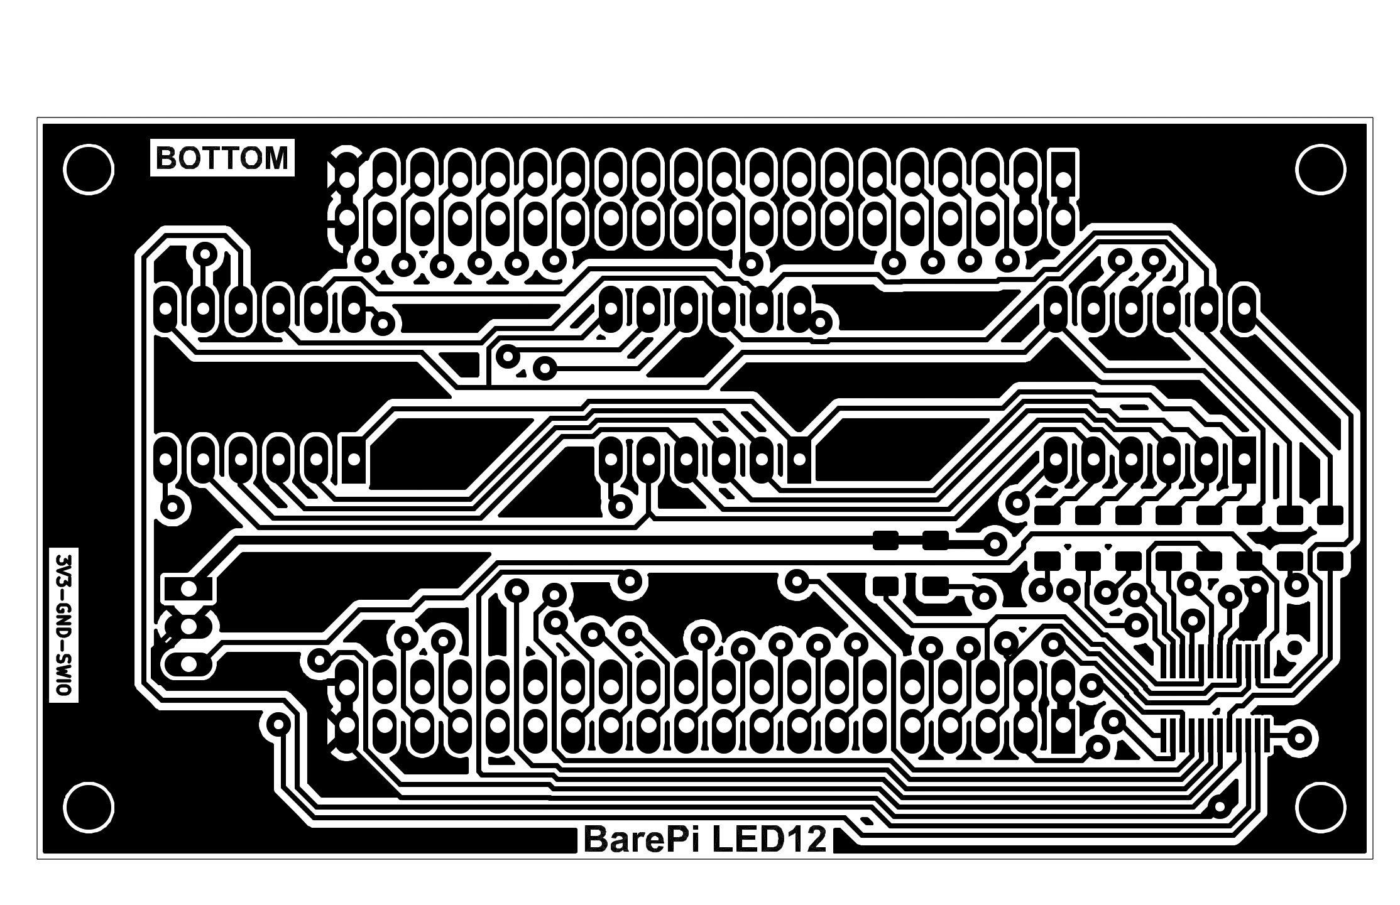
_www/img/BarePi_LED12_bottom.png
