Panda381/BarePi/_www/img/BarePi_LED12_diagram_m.jpg

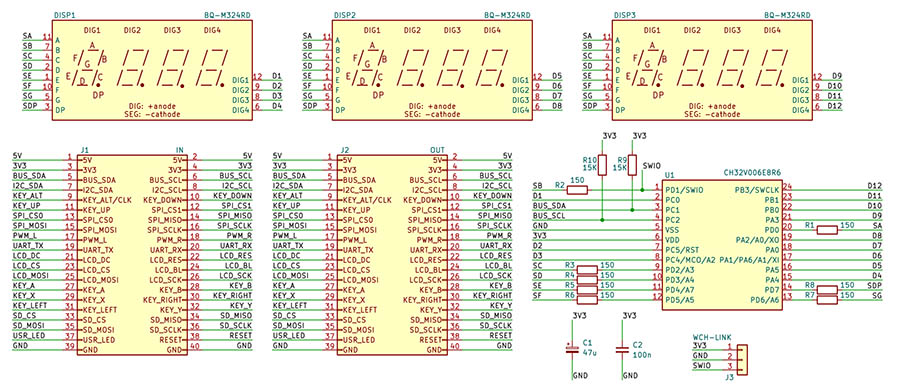
_www/img/BarePi_LED12_diagram_m.jpg
