Panda381/BarePi/_www/img/BarePi_LED121.jpg

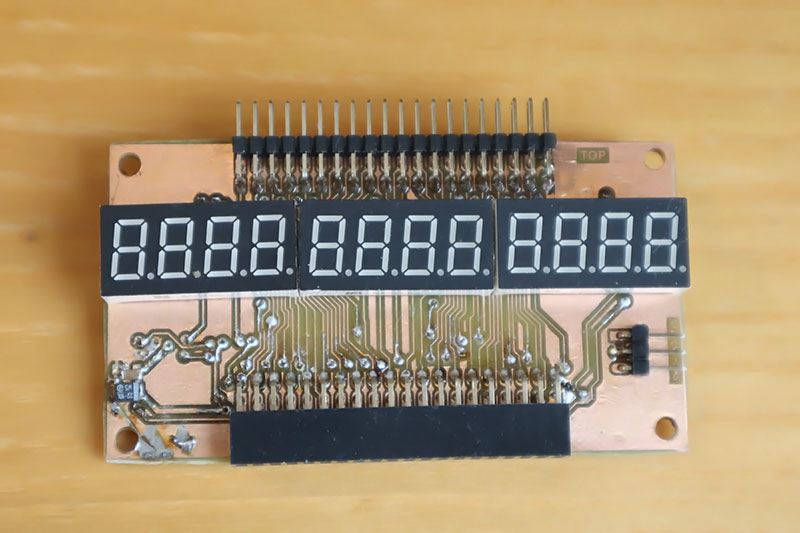
_www/img/BarePi_LED121.jpg
