Panda381/BarePi/_www/img/BarePi_LED123.jpg

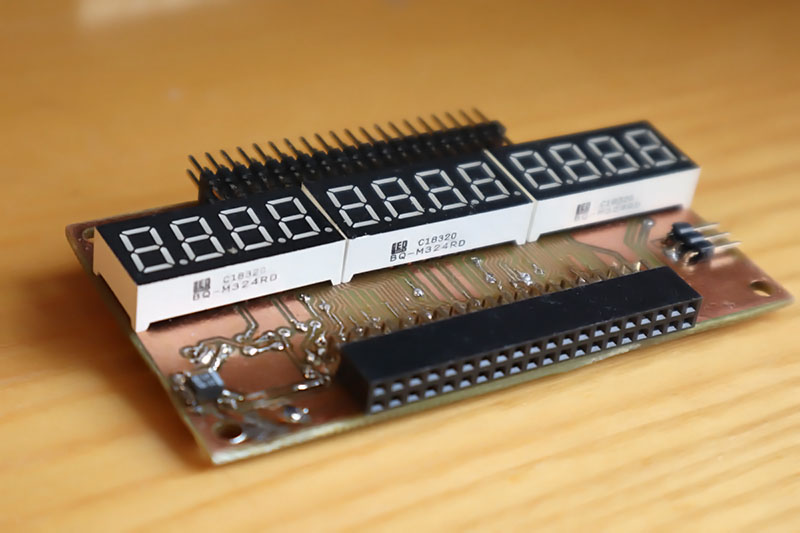
_www/img/BarePi_LED123.jpg
