Panda381/BarePi/_www/img/BarePi_MegaTinyJoypad2.jpg

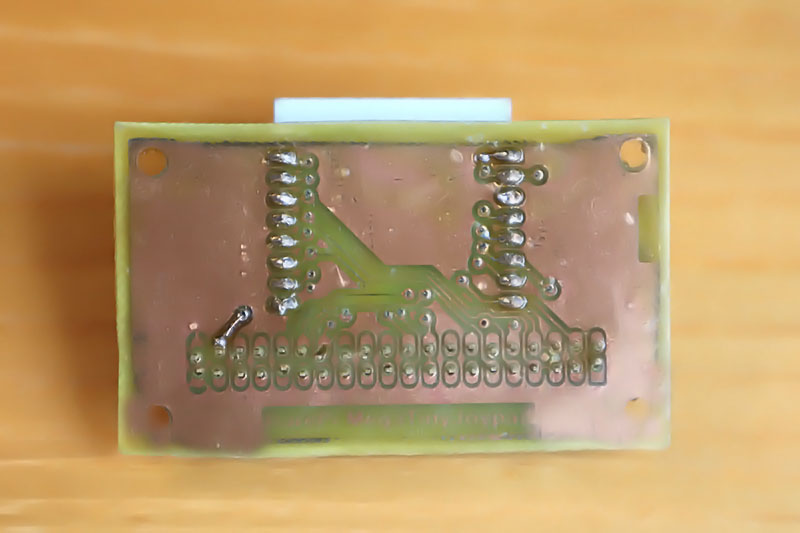
_www/img/BarePi_MegaTinyJoypad2.jpg
