Panda381/BarePi/_www/img/BarePi_MegaTinyJoypad3.jpg

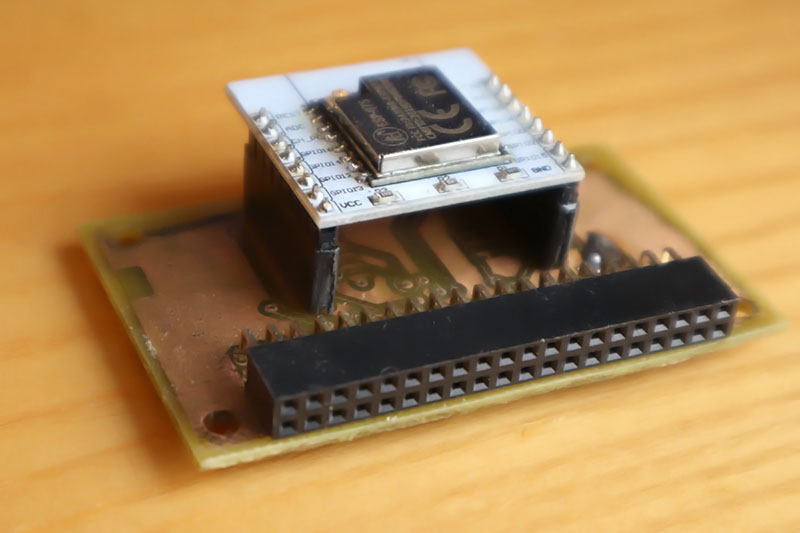
_www/img/BarePi_MegaTinyJoypad3.jpg
