Panda381/BarePi/MegaTinyJoypad/BarePi_MegaTinyJoypad_bottom.png

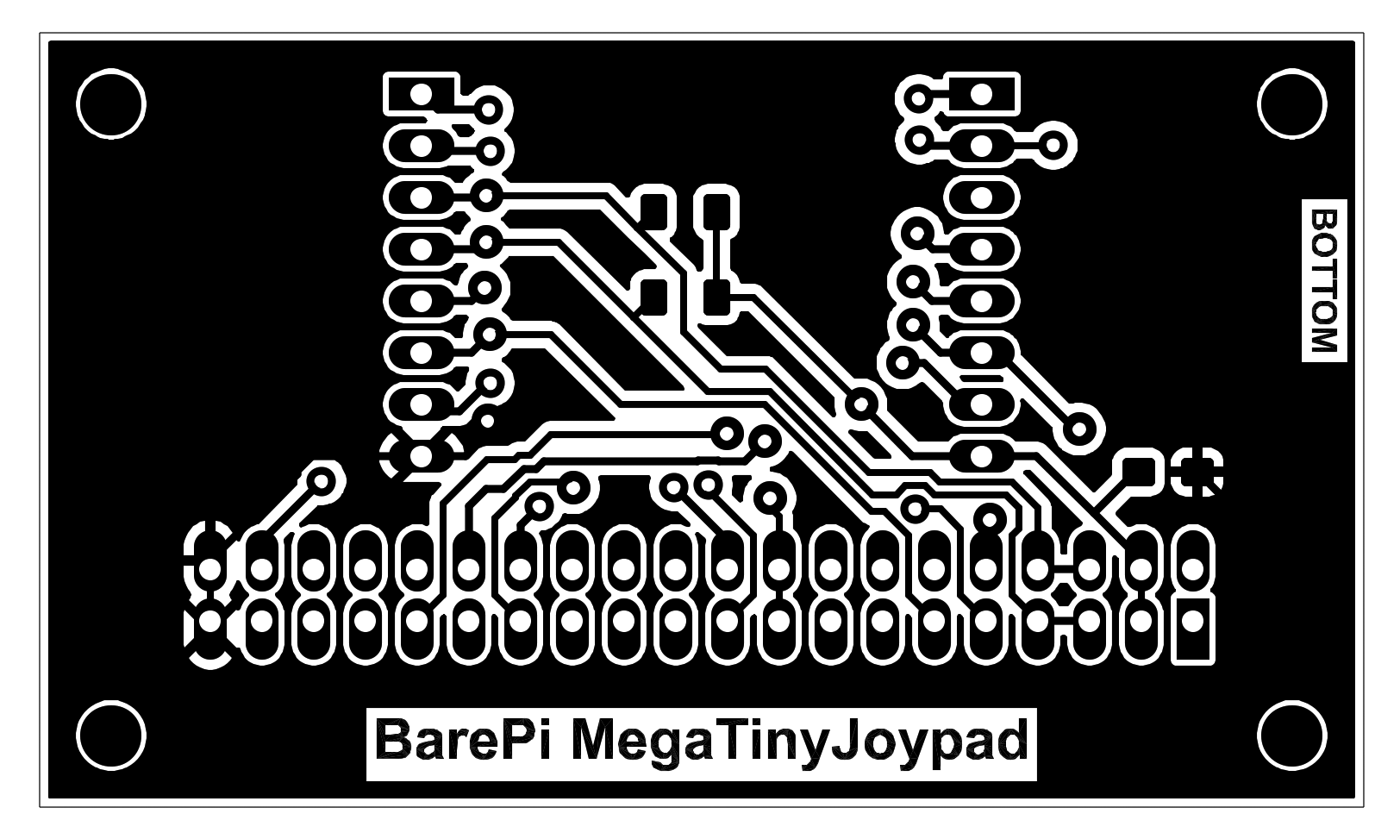
_www/img/BarePi_MegaTinyJoypad_bottom.png
