Panda381/BarePi/MegaTinyJoypad/BarePi_MegaTinyJoypad_diagram.png

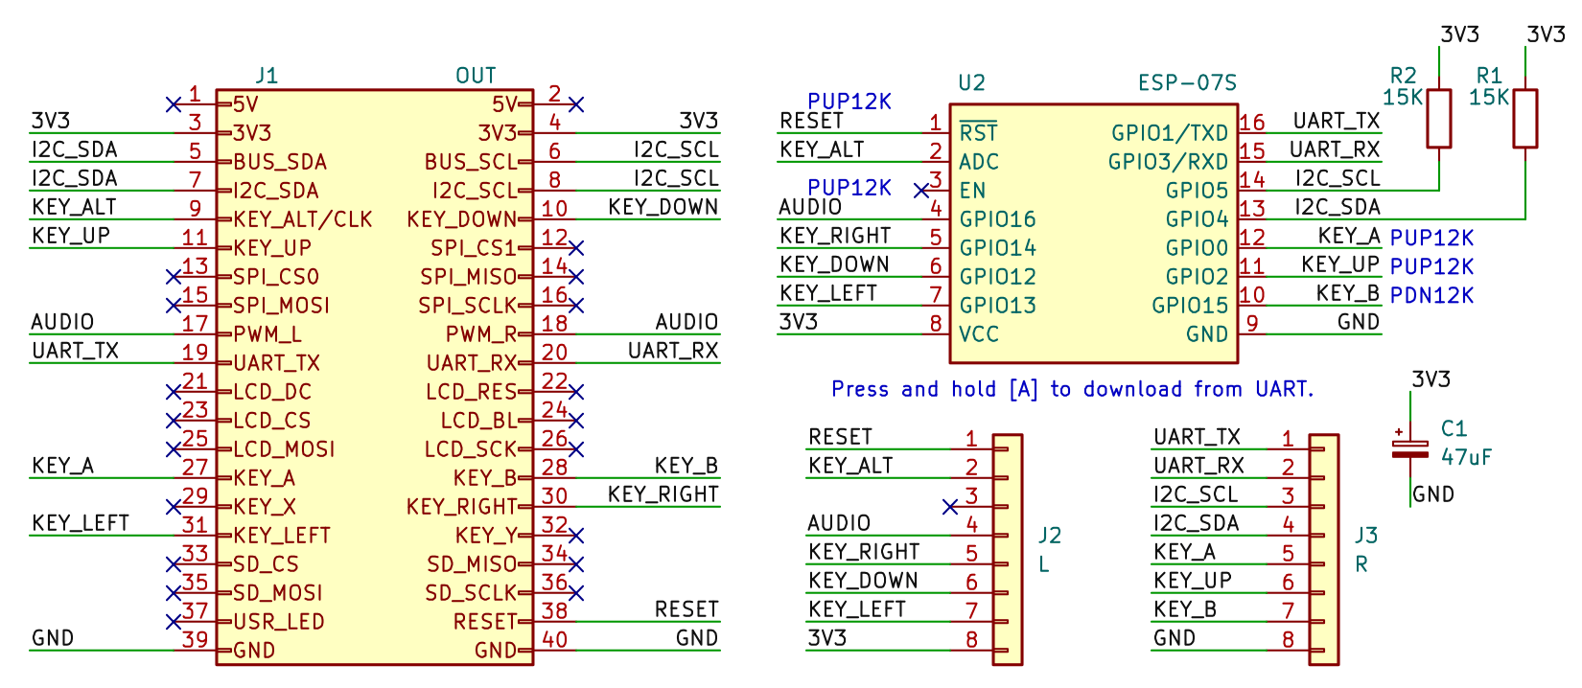
_www/img/BarePi_MegaTinyJoypad_diagram.png
