Panda381/BarePi/_www/img/BarePi_MegaTinyJoypad_mounting_m.jpg

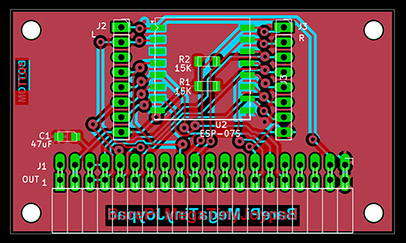
_www/img/BarePi_MegaTinyJoypad_mounting_m.jpg
