Panda381/BarePi/_www/img/BarePi_MegaTinyJoypad_panel_m.jpg

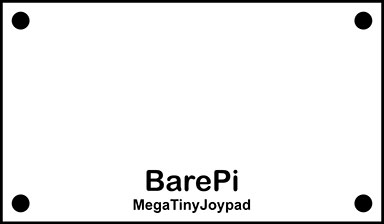
_www/img/BarePi_MegaTinyJoypad_panel_m.jpg
