Panda381/BarePi/_www/img/BarePi_MiniKey1.jpg

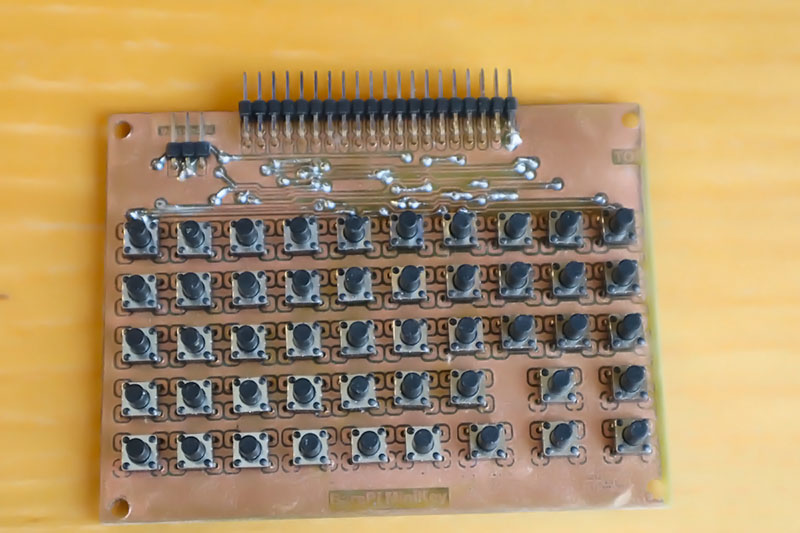
_www/img/BarePi_MiniKey1.jpg
