Panda381/BarePi/_www/img/BarePi_MiniKey3.jpg

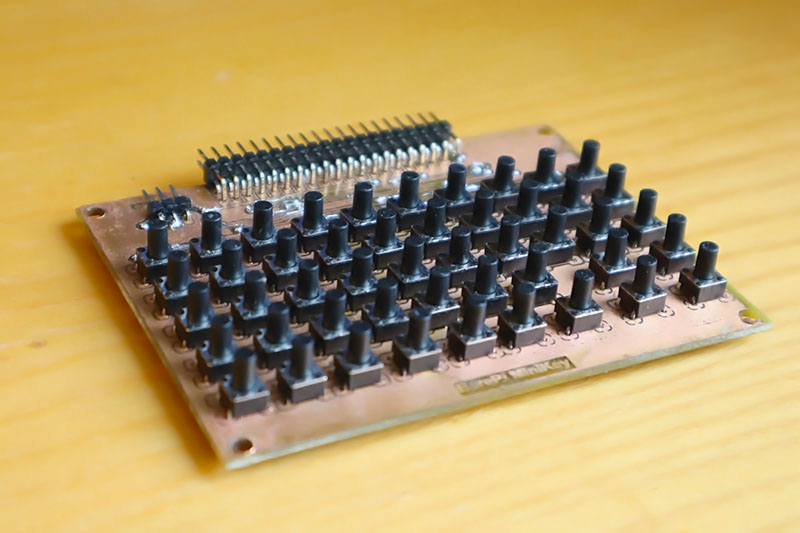
_www/img/BarePi_MiniKey3.jpg
