Panda381/BarePi/_www/img/BarePi_MiniKey5.jpg

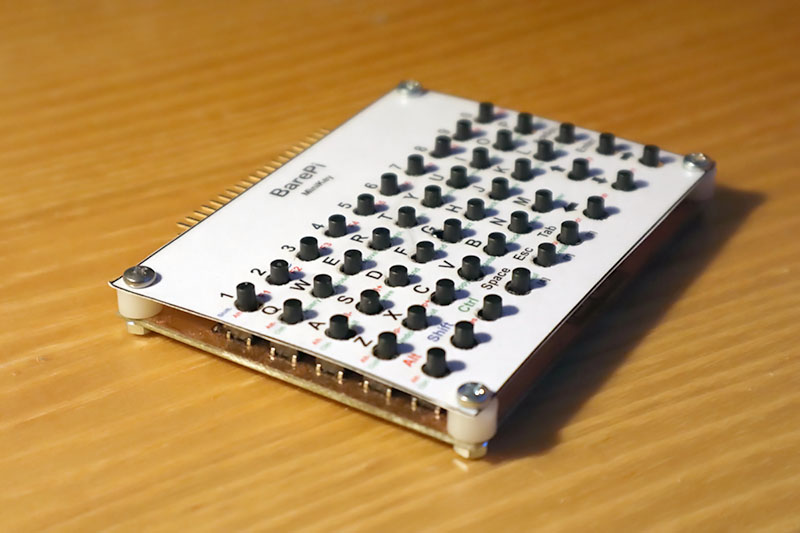
_www/img/BarePi_MiniKey5.jpg
