Panda381/BarePi/MiniKey/BarePi_MiniKey_3D.jpg

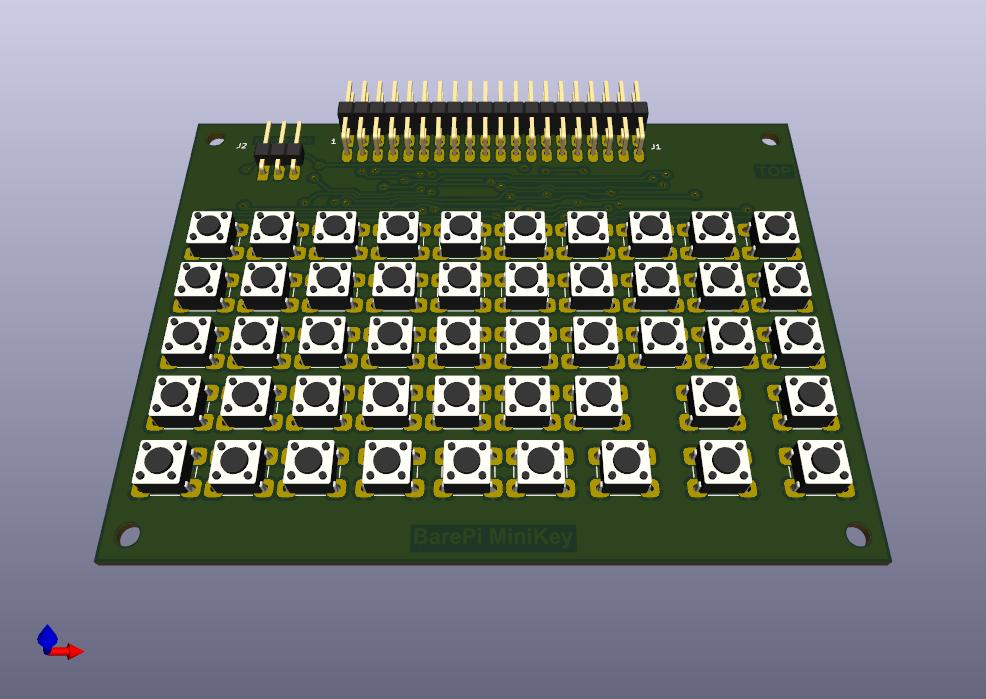
_www/img/BarePi_MiniKey_3D.jpg
