Panda381/BarePi/MiniKey/BarePi_MiniKey_bottom.png

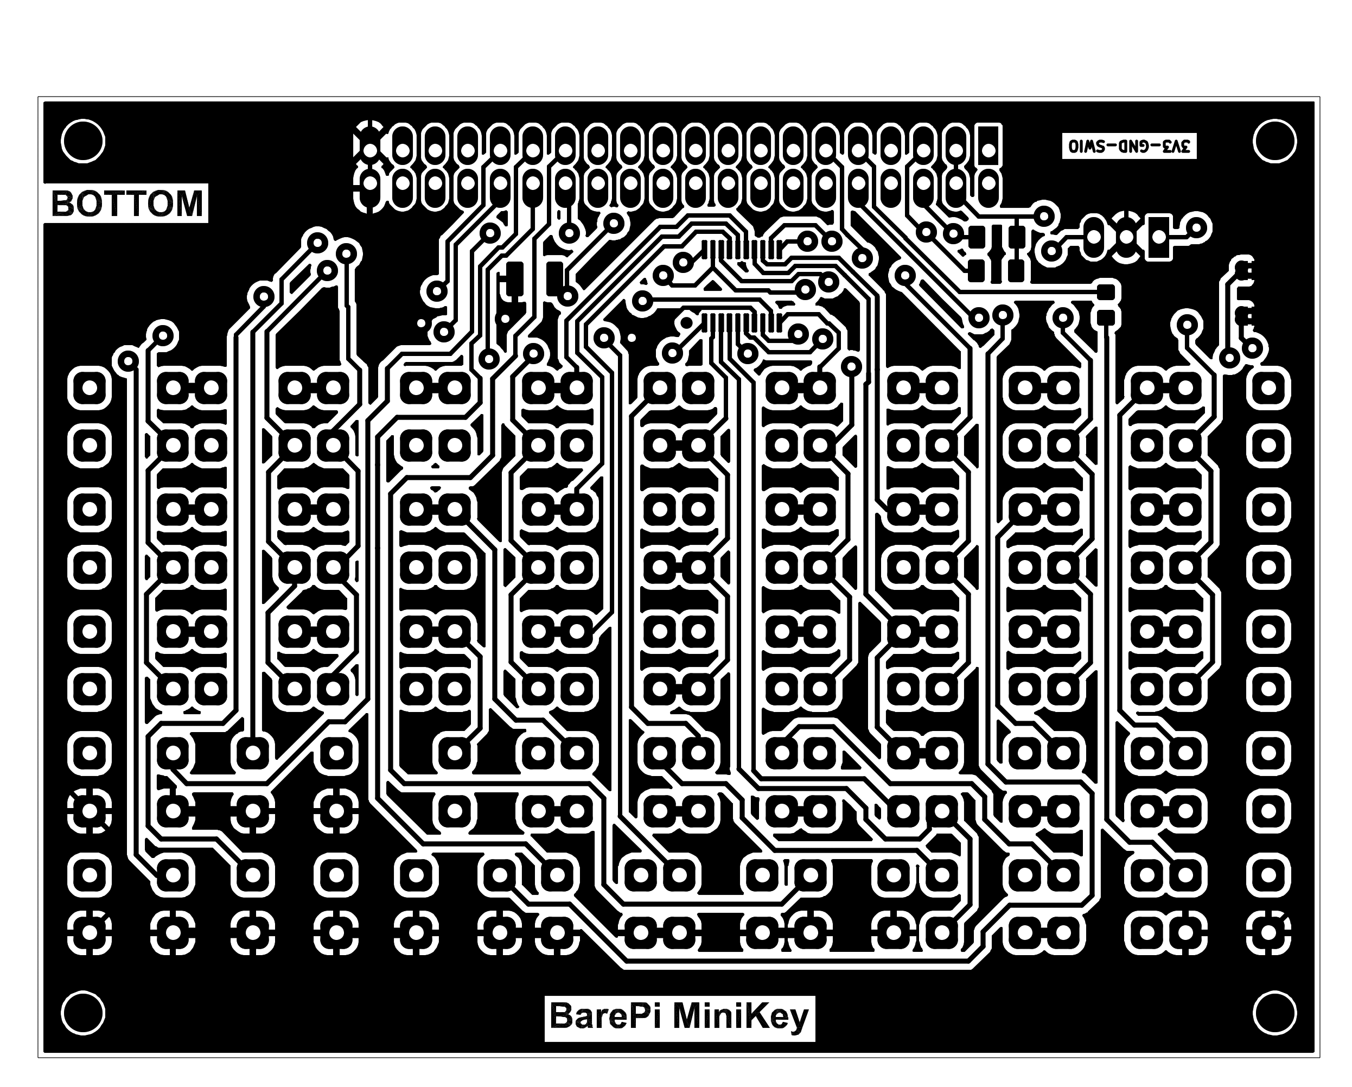
_www/img/BarePi_MiniKey_bottom.png
