Panda381/BarePi/MiniKey/BarePi_MiniKey_mounting.jpg

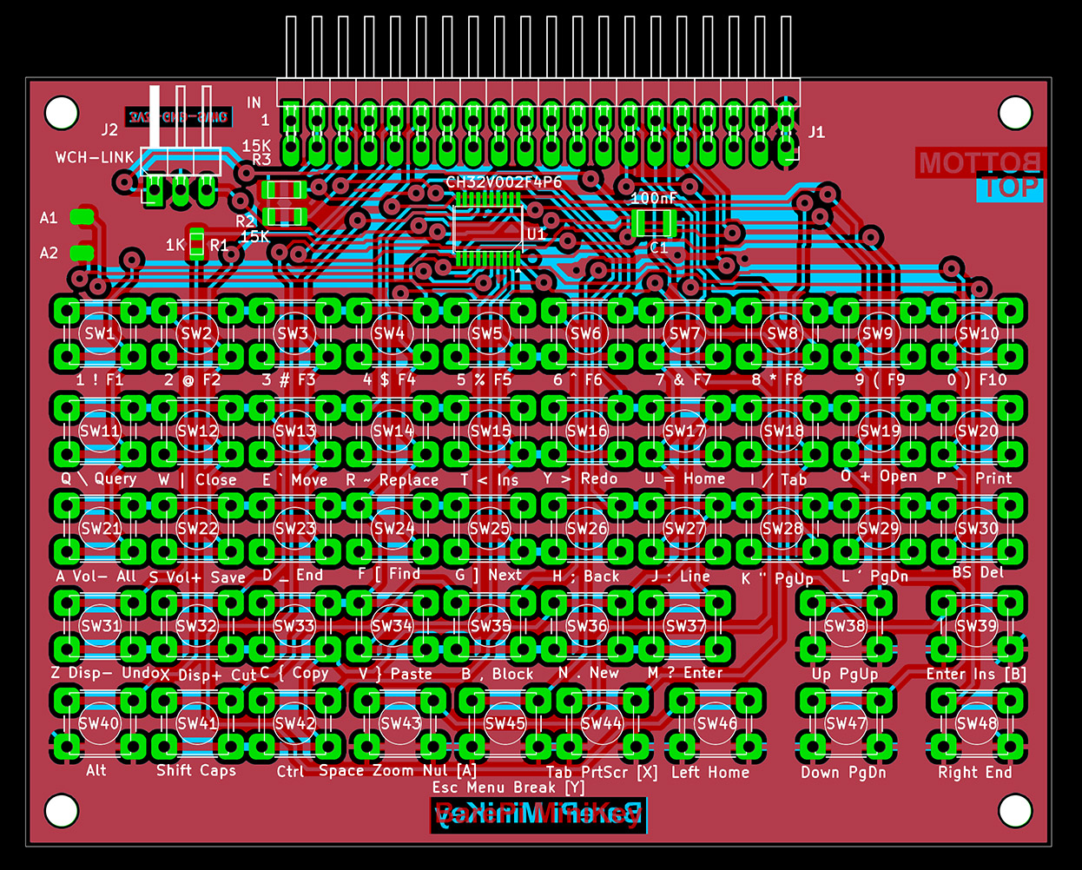
_www/img/BarePi_MiniKey_mounting.jpg
