Panda381/BarePi/_www/img/BarePi_MiniKey_panel_m.jpg

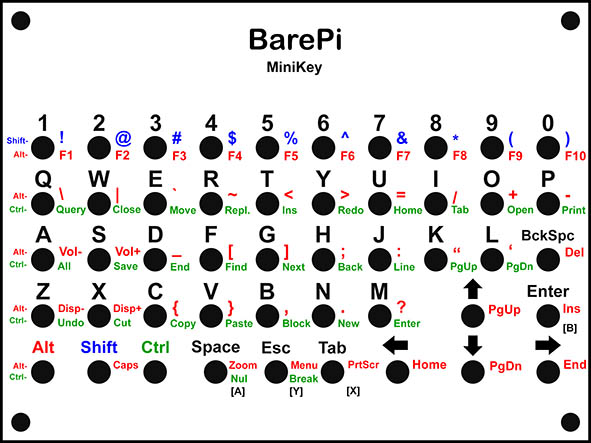
_www/img/BarePi_MiniKey_panel_m.jpg
