Panda381/BarePi/MiniKey/BarePi_MiniKey_top.png

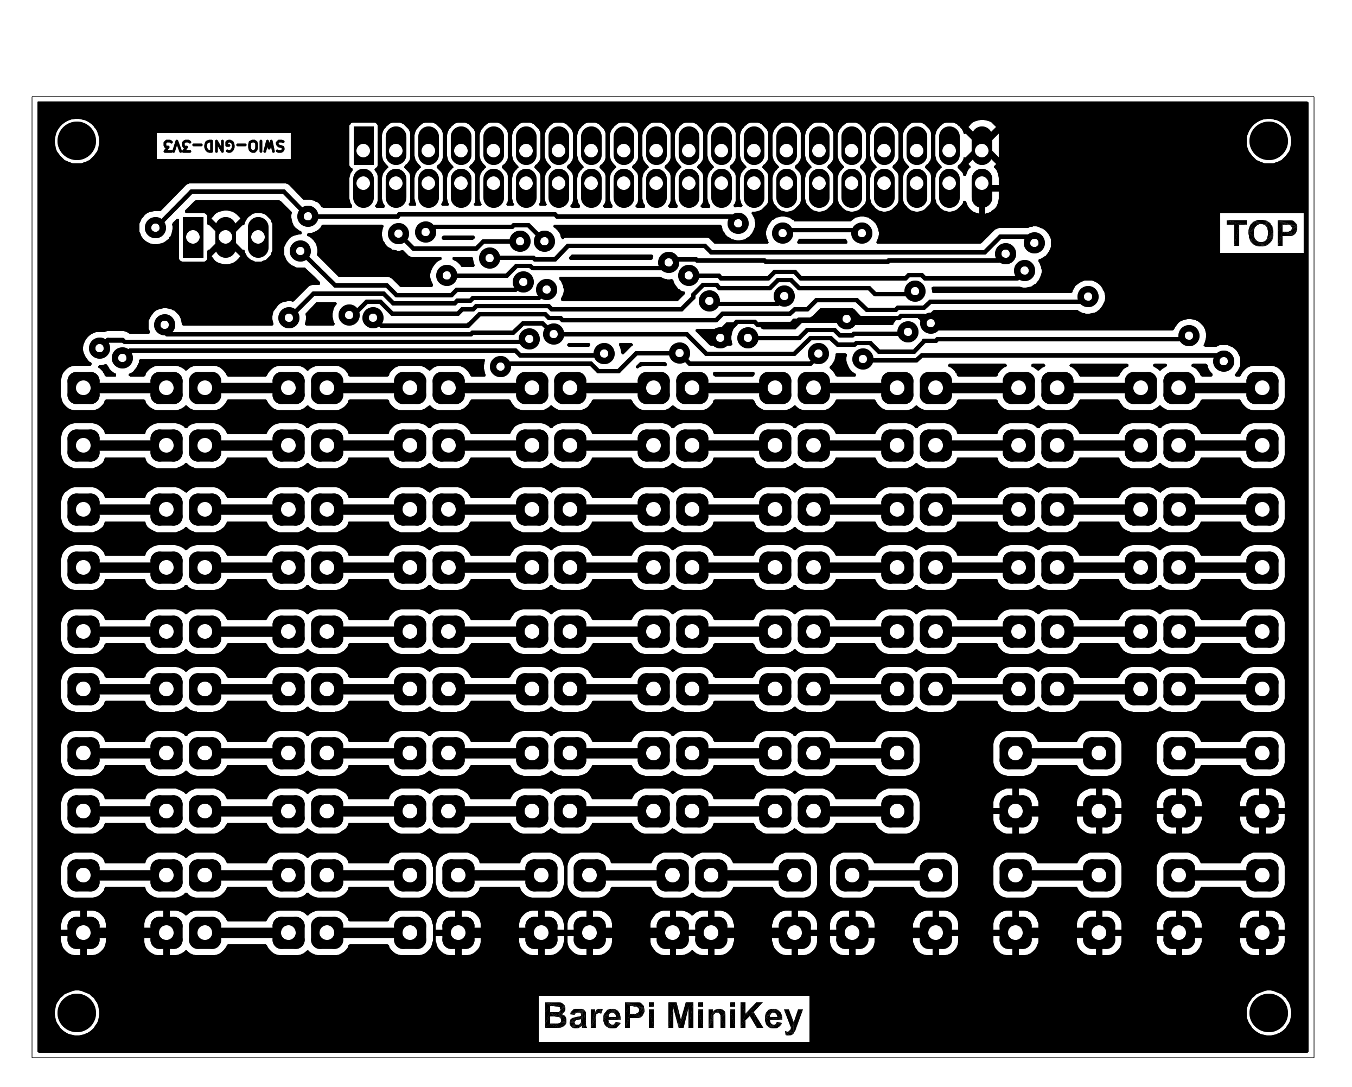
_www/img/BarePi_MiniKey_top.png
