Panda381/BarePi/OLED128x64/BarePi_OLED128x64_3D_bottom.jpg

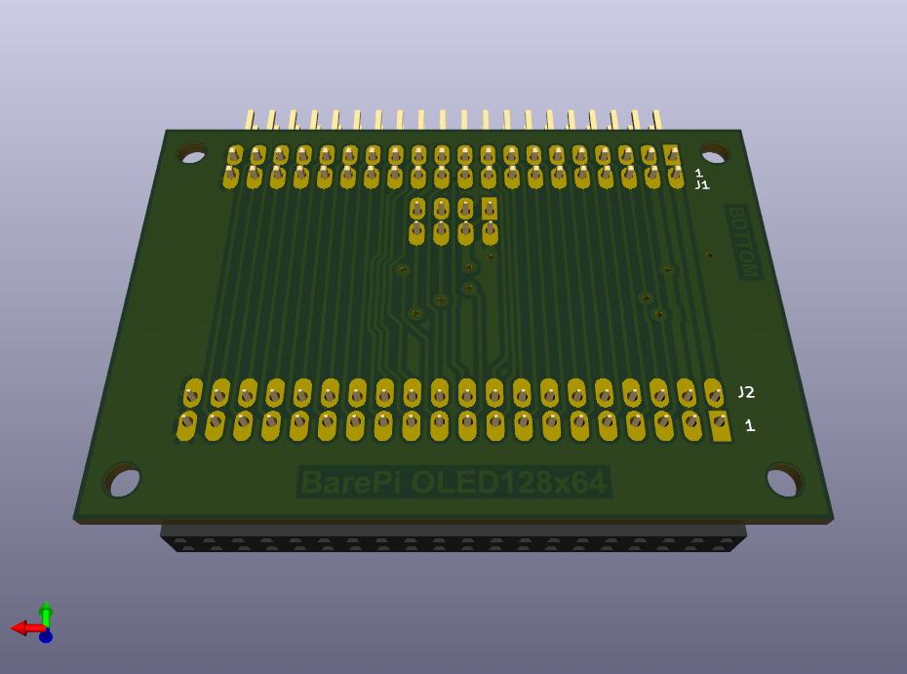
_www/img/BarePi_OLED128x64_3D_bottom.jpg
