Panda381/BarePi/_www/img/BarePi_OLED128x64_3D_m.jpg

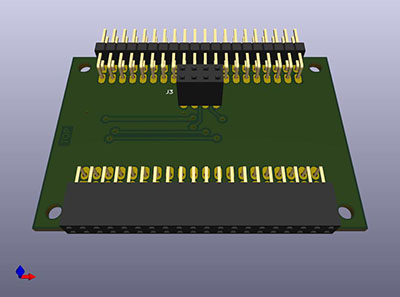
_www/img/BarePi_OLED128x64_3D_m.jpg
