Panda381/BarePi/OLED128x64/BarePi_OLED128x64_label_GND_VDD.png

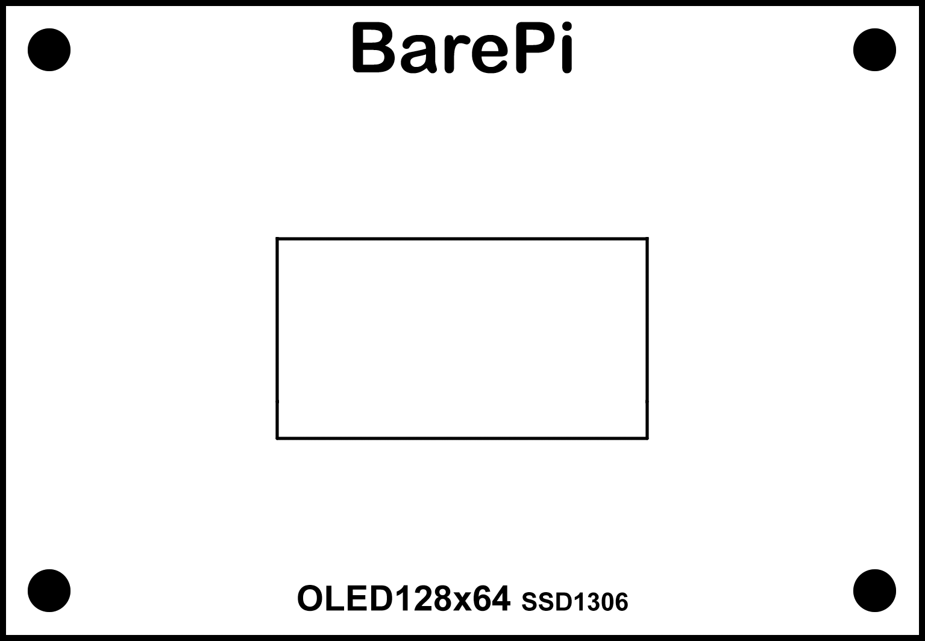
_www/img/BarePi_OLED128x64_label_GND_VDD.png
