Panda381/BarePi/OLED128x64/BarePi_OLED128x64_top.png

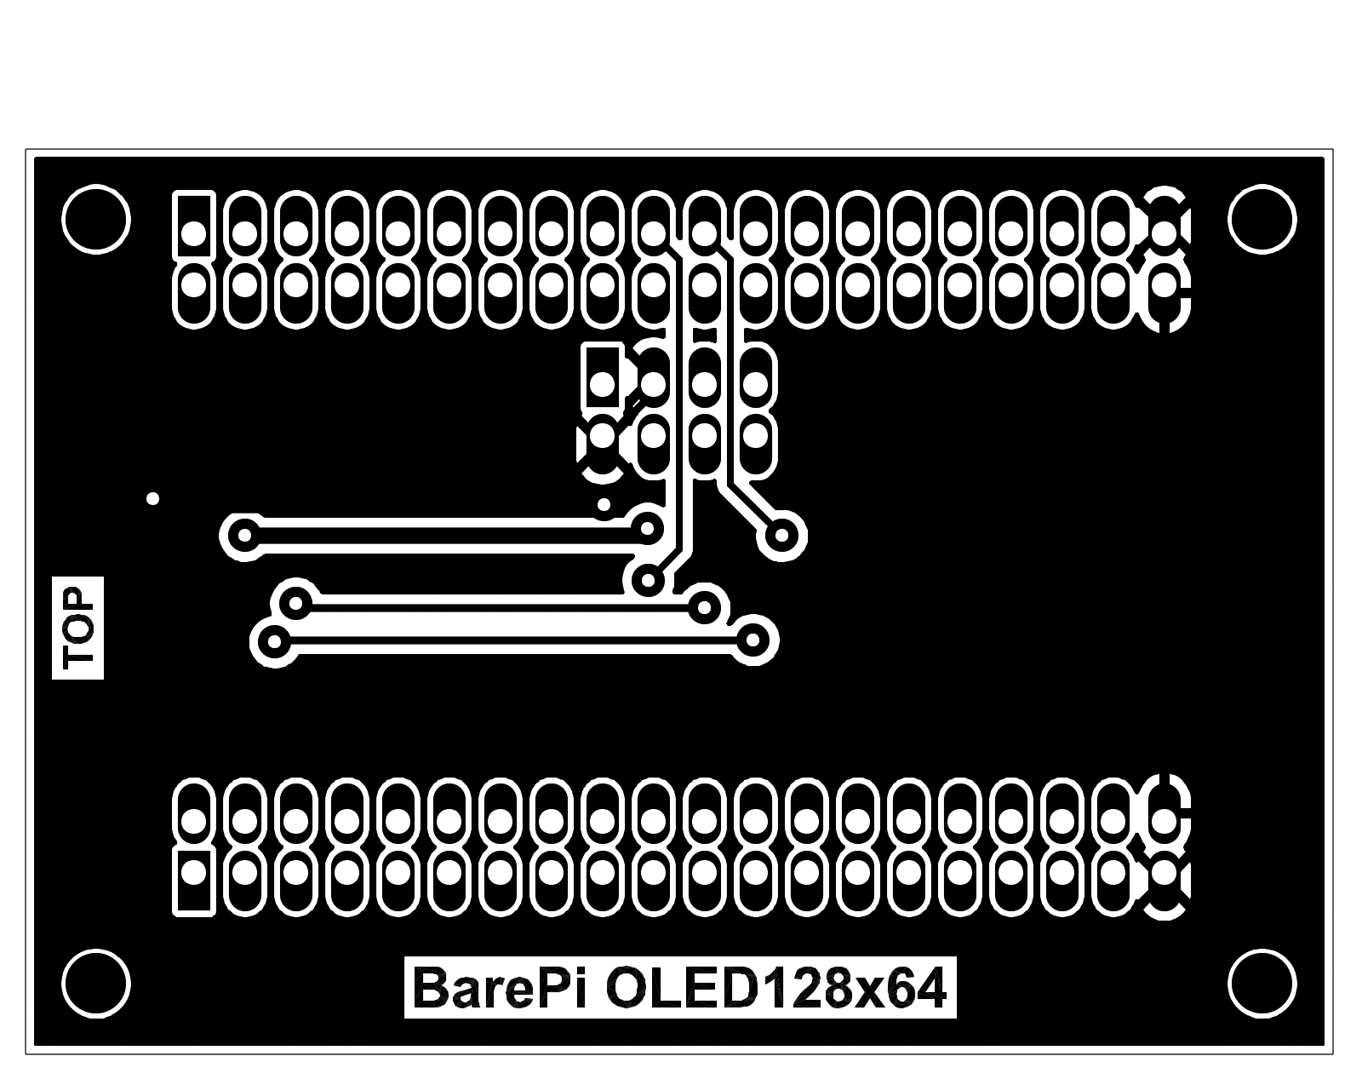
_www/img/BarePi_OLED128x64_top.png
