Panda381/BarePi/_www/img/BarePi_OLED128x641_m.jpg

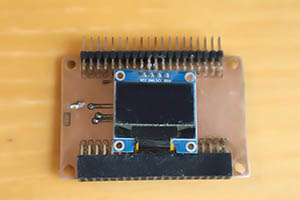
_www/img/BarePi_OLED128x641_m.jpg
