Panda381/BarePi/_www/img/BarePi_OLED128x642_m.jpg

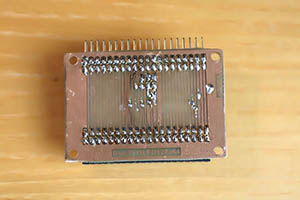
_www/img/BarePi_OLED128x642_m.jpg
