Panda381/BarePi/_www/img/BarePi_PGA2350_m.jpg

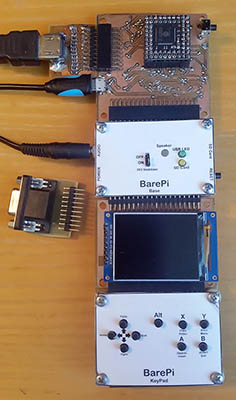
_www/img/BarePi_PGA2350_m.jpg
