Panda381/BarePi/PGA2350/BarePi_PGA2350_top.png

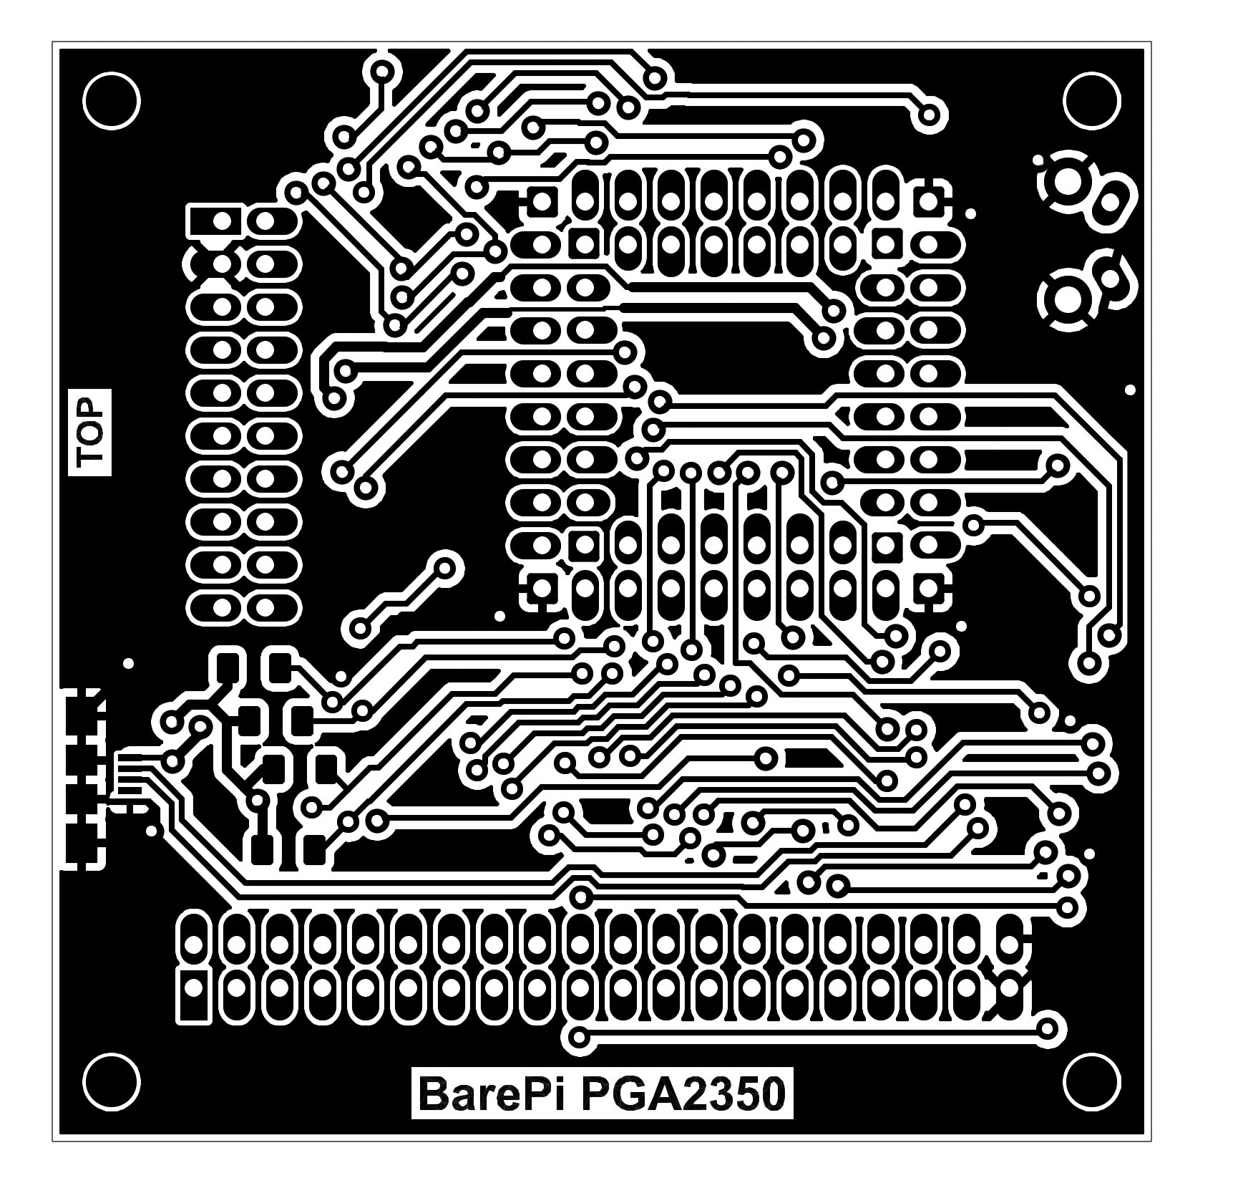
_www/img/BarePi_PGA2350_top.png
