Panda381/BarePi/_www/img/BarePi_PGA23501_m.jpg

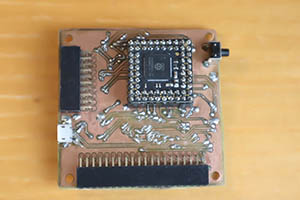
_www/img/BarePi_PGA23501_m.jpg
