Panda381/BarePi/_www/img/BarePi_PGA23503.jpg

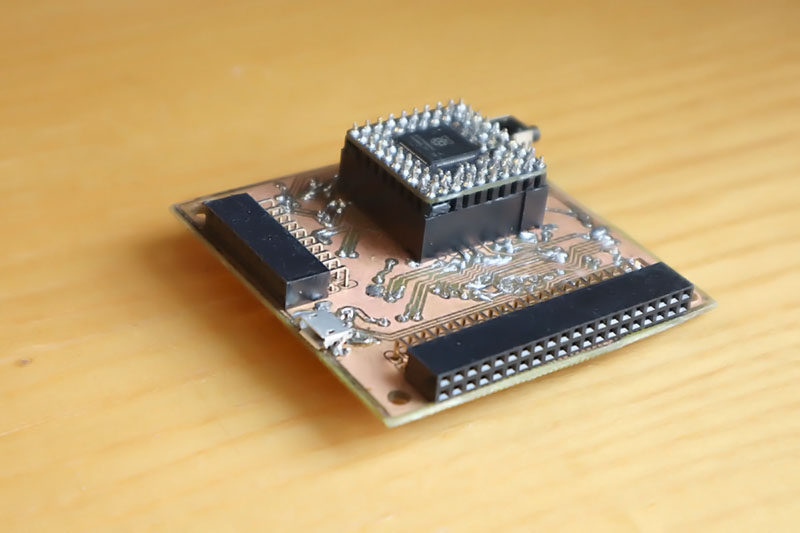
_www/img/BarePi_PGA23503.jpg
