Panda381/BarePi/_www/img/BarePi_PicoPad3.jpg

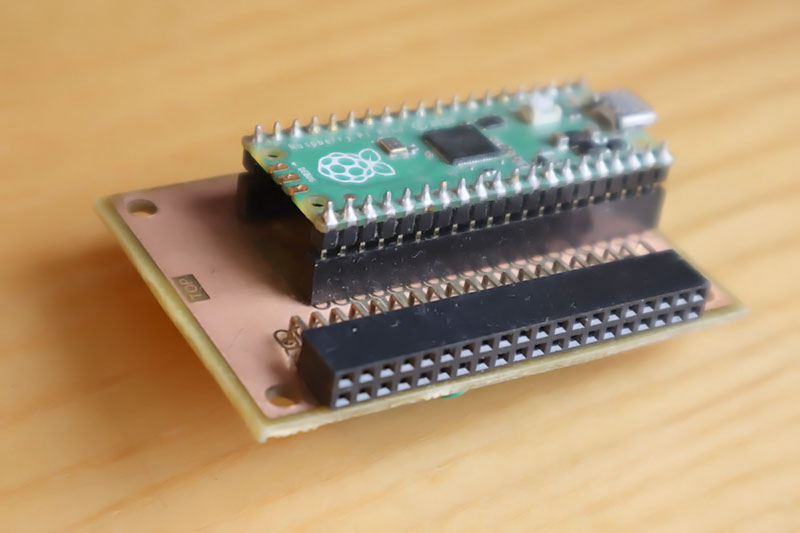
_www/img/BarePi_PicoPad3.jpg
