Panda381/BarePi/_www/img/BarePi_PicoPad.jpg

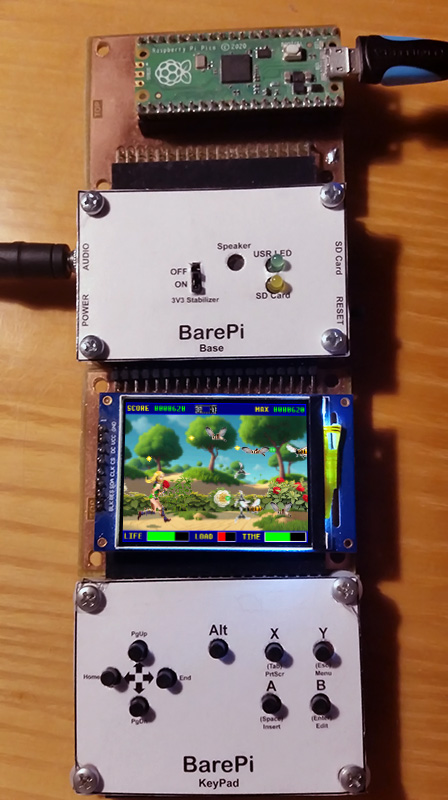
_www/img/BarePi_PicoPad.jpg
