Panda381/BarePi/_www/img/BarePi_PicoPad_bottom_m.jpg

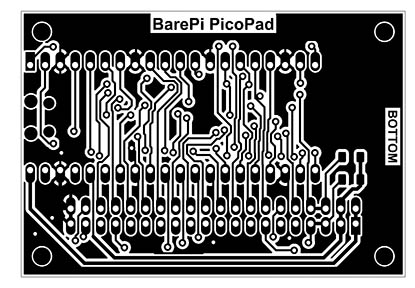
_www/img/BarePi_PicoPad_bottom_m.jpg
