Panda381/BarePi/_www/img/BarePi_PicoPad_diagram_m.jpg

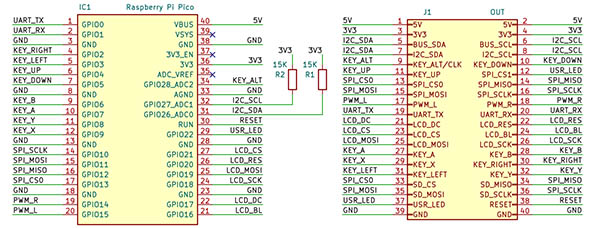
_www/img/BarePi_PicoPad_diagram_m.jpg
