Panda381/BarePi/_www/img/BarePi_PicoPadApps_m.jpg

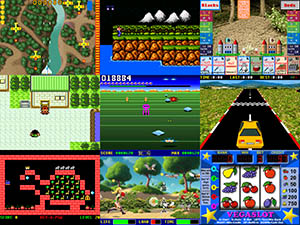
_www/img/BarePi_PicoPadApps_m.jpg
