Panda381/BarePi/_www/img/BarePi_PicoPadHSTX1.jpg

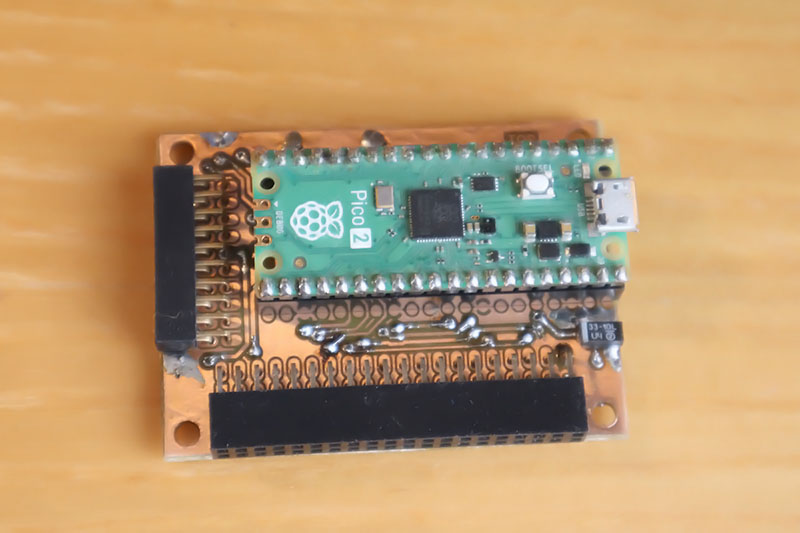
_www/img/BarePi_PicoPadHSTX1.jpg
