Panda381/BarePi/_www/img/BarePi_PicoPadHSTX2_m.jpg

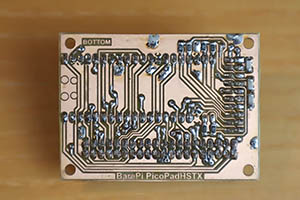
_www/img/BarePi_PicoPadHSTX2_m.jpg
