Panda381/BarePi/_www/img/BarePi_PicoPadHSTX3.jpg

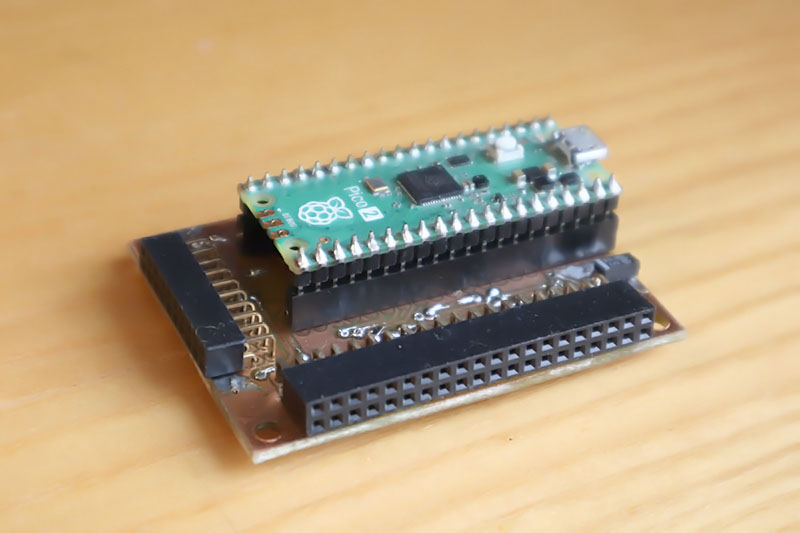
_www/img/BarePi_PicoPadHSTX3.jpg
