Panda381/BarePi/PicoPadHSTX/BarePi_PicoPadHSTX_3D_bottom.jpg

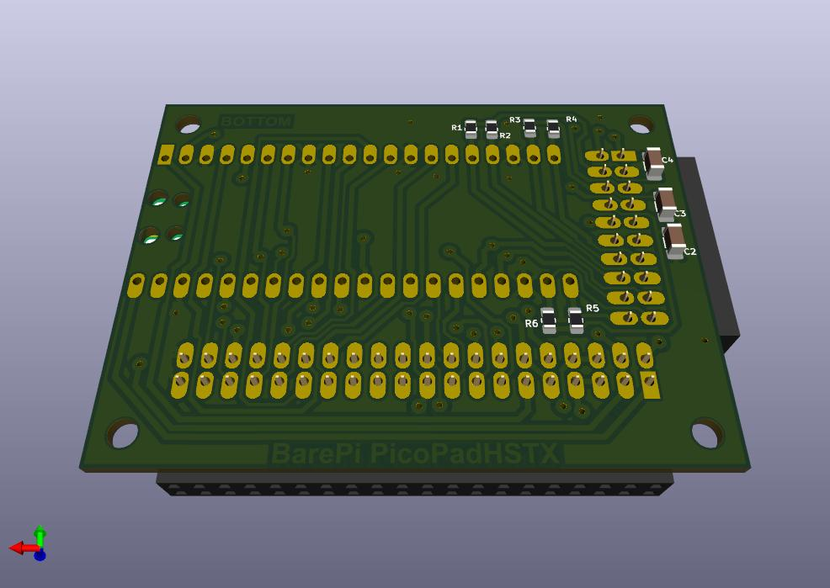
_www/img/BarePi_PicoPadHSTX_3D_bottom.jpg
