Panda381/BarePi/PicoPadHSTX/BarePi_PicoPadHSTX_bottom.png

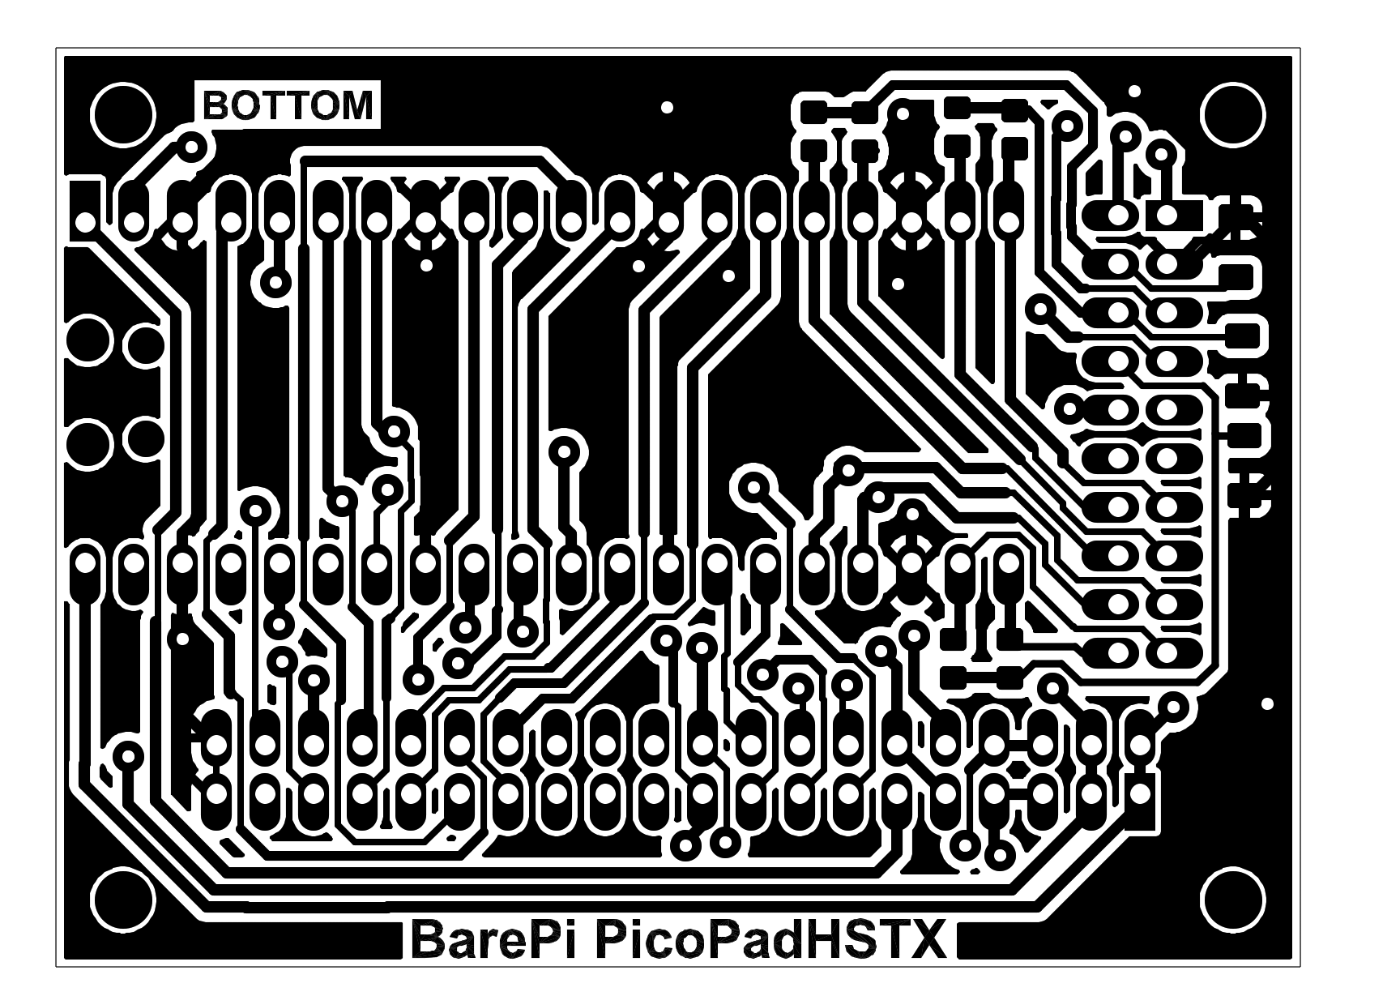
_www/img/BarePi_PicoPadHSTX_bottom.png
