Panda381/BarePi/_www/img/BarePi_PicoPadHSTX_diagram_m.jpg

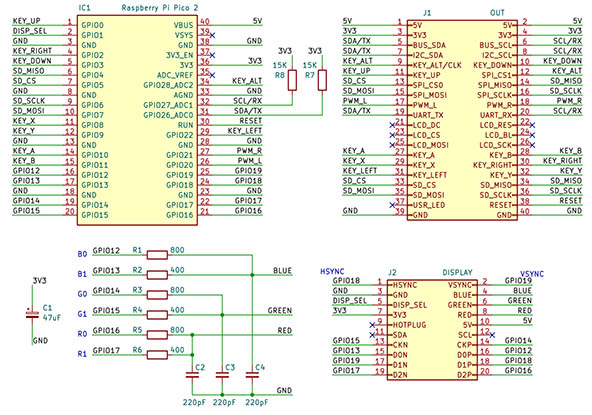
_www/img/BarePi_PicoPadHSTX_diagram_m.jpg
