Panda381/BarePi/PicoPadHSTX/BarePi_PicoPadHSTX_label.png

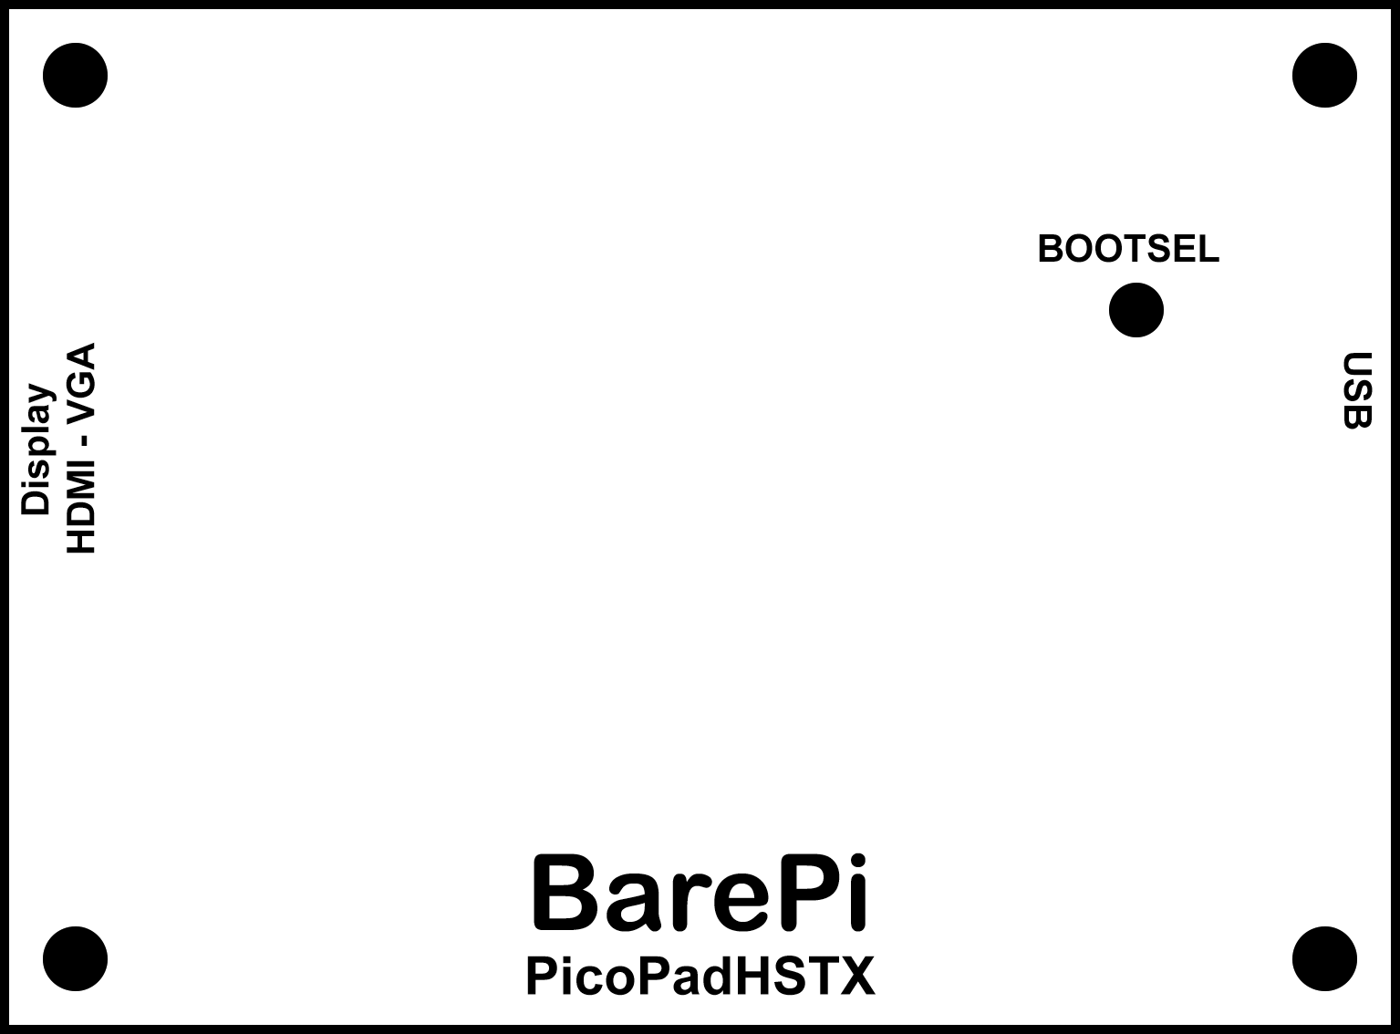
_www/img/BarePi_PicoPadHSTX_label.png
