Panda381/BarePi/_www/img/BarePi_PicoPadHSTX_m.jpg

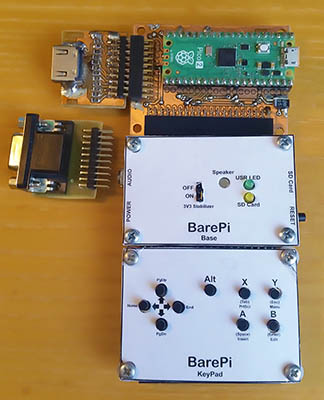
_www/img/BarePi_PicoPadHSTX_m.jpg
