Panda381/BarePi/_www/img/BarePi_PicoPadHSTX_top_m.jpg

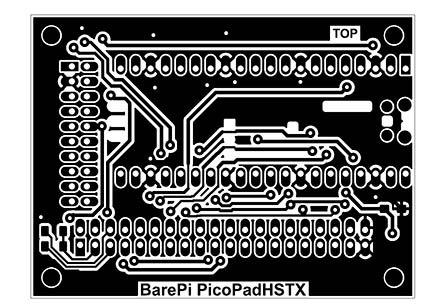
_www/img/BarePi_PicoPadHSTX_top_m.jpg
