Panda381/BarePi/_www/img/BarePi_PidiBoy2_m.jpg

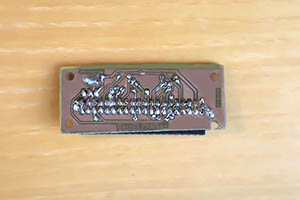
_www/img/BarePi_PidiBoy2_m.jpg
