Panda381/BarePi/_www/img/BarePi_PidiBoy.jpg

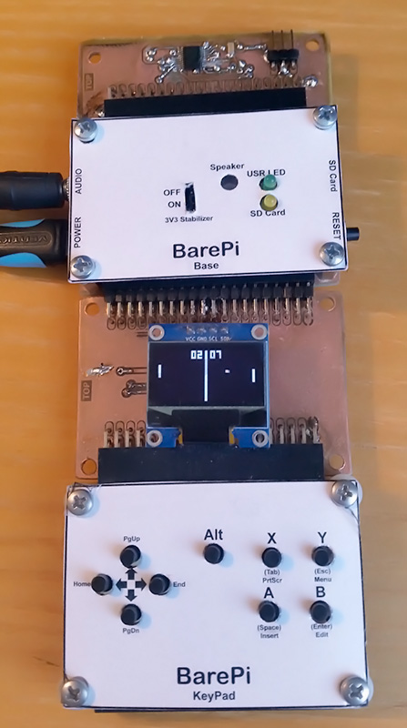
_www/img/BarePi_PidiBoy.jpg
