Panda381/BarePi/PidiBoy/BarePi_PidiBoy_3D.jpg

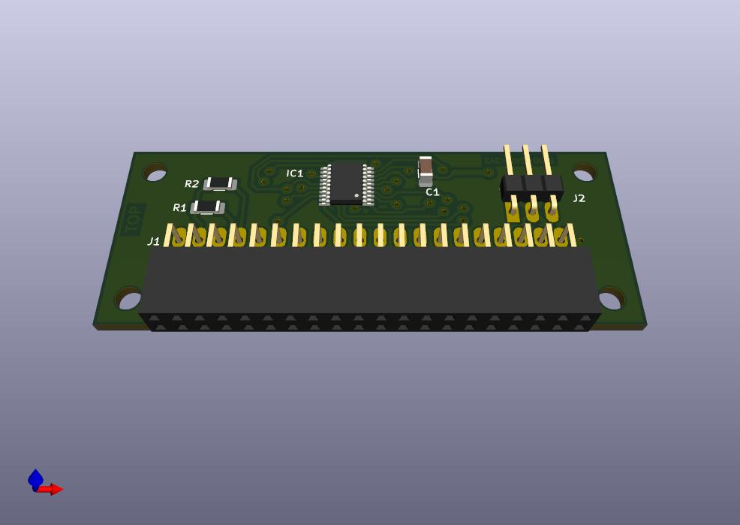
_www/img/BarePi_PidiBoy_3D.jpg
