Panda381/BarePi/PidiBoy/BarePi_PidiBoy_bottom.png

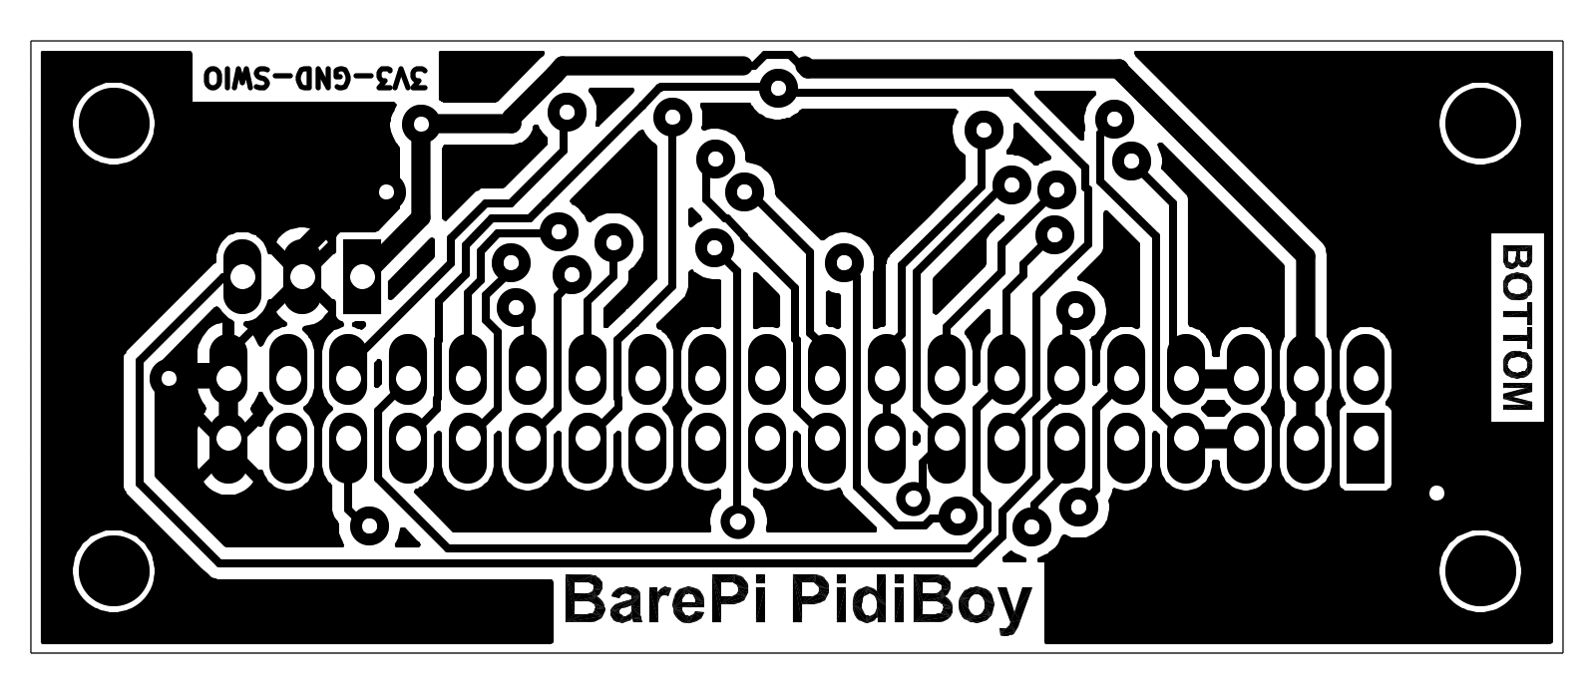
_www/img/BarePi_PidiBoy_bottom.png
