Panda381/BarePi/PidiBoy/BarePi_PidiBoy_diagram.png

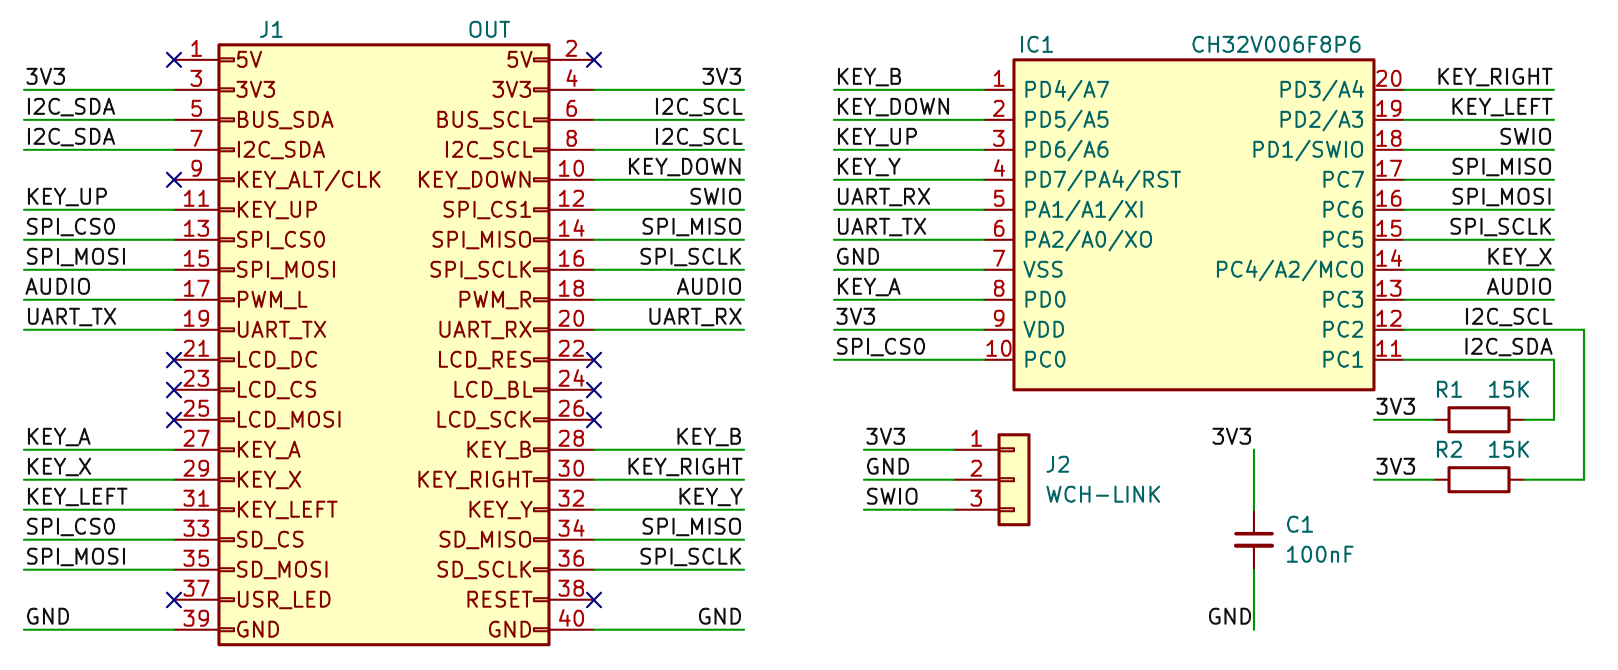
_www/img/BarePi_PidiBoy_diagram.png
