Panda381/BarePi/_www/img/BarePi_PidiBoy_mounting_m.jpg

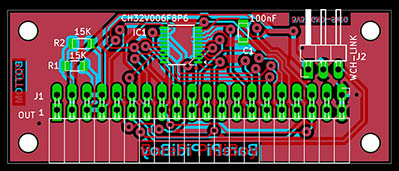
_www/img/BarePi_PidiBoy_mounting_m.jpg
