Panda381/BarePi/PidiBoy/BarePi_PidiBoy_top.png

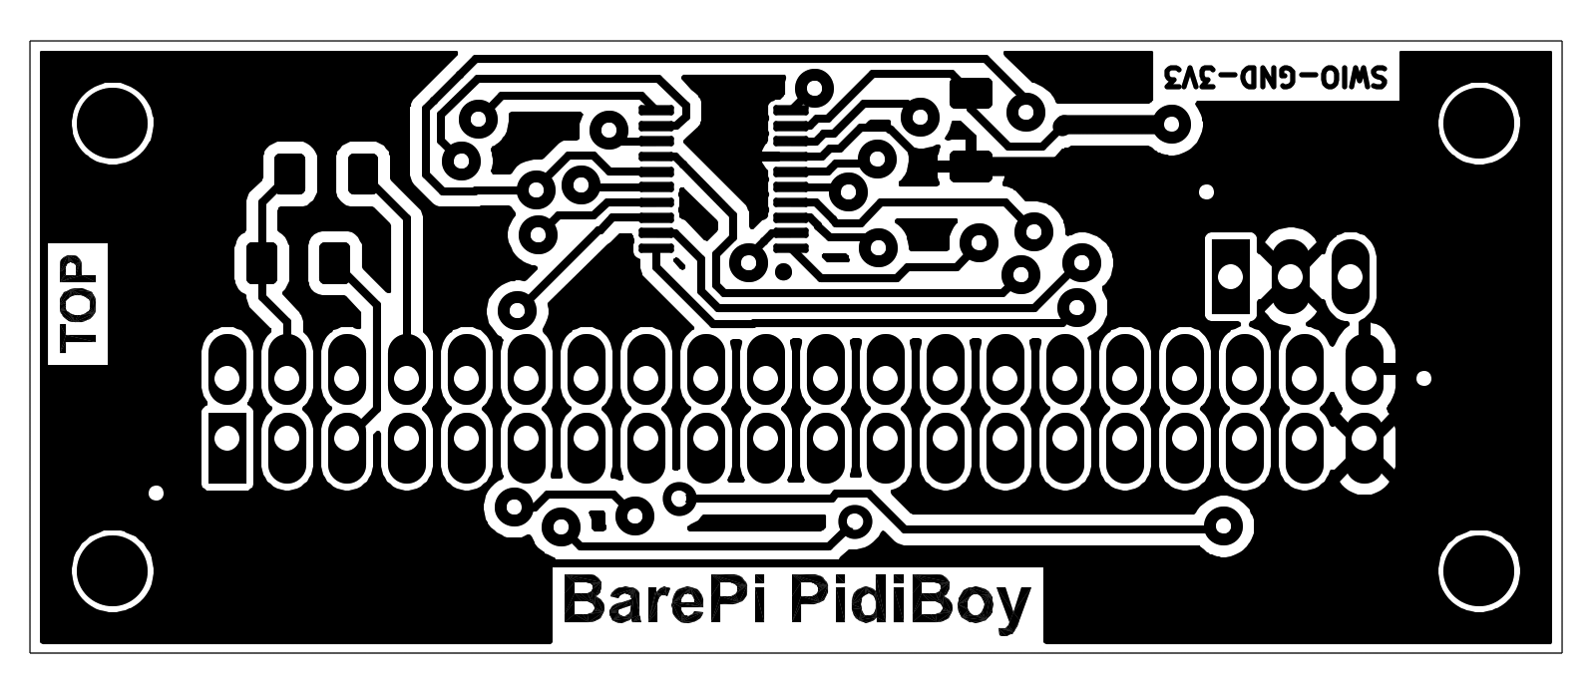
_www/img/BarePi_PidiBoy_top.png
