Panda381/BarePi/_www/img/BarePi_PidiBoyApps.jpg

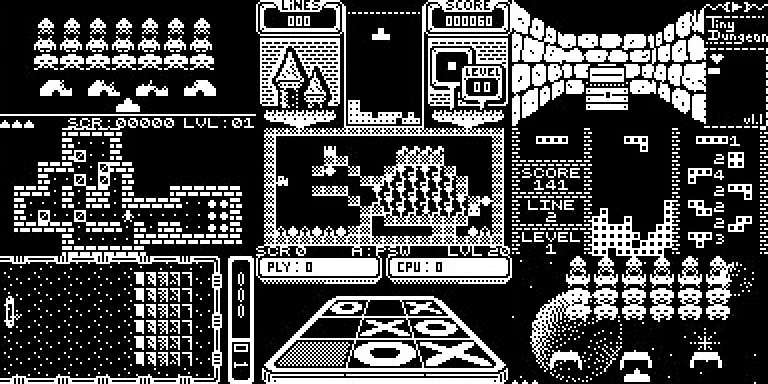
_www/img/BarePi_PidiBoyApps.jpg
