Panda381/BarePi/_www/img/BarePi_PidiMet1.jpg

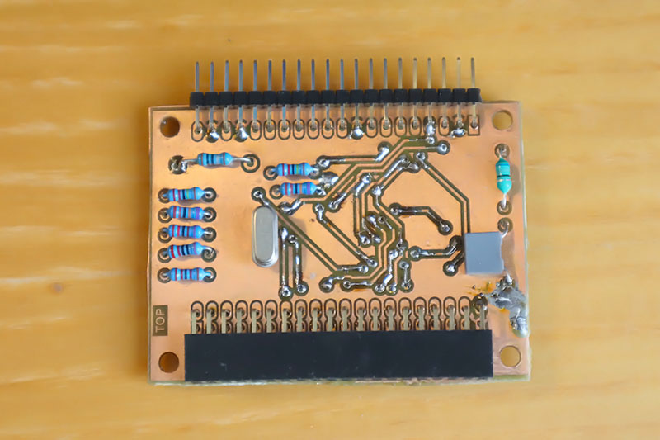
_www/img/BarePi_PidiMet1.jpg
