Panda381/BarePi/_www/img/BarePi_PidiMet2.jpg

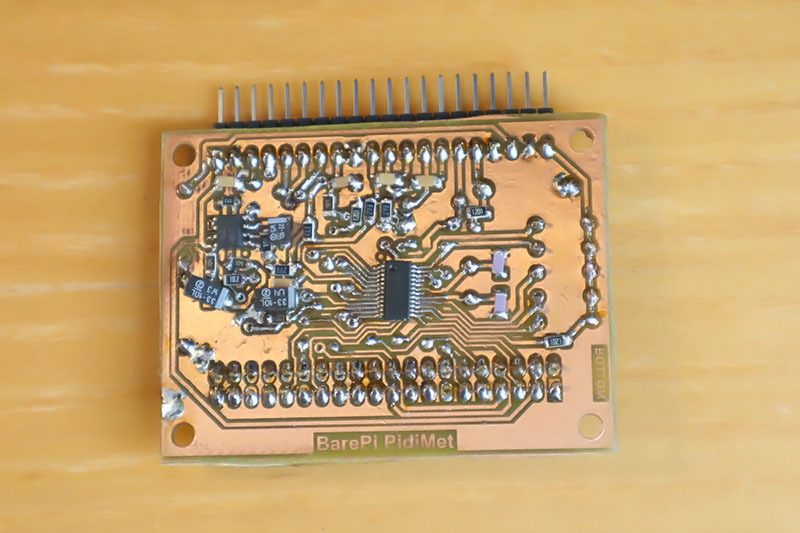
_www/img/BarePi_PidiMet2.jpg
