Panda381/BarePi/PidiMet/BarePi_PidiMet_3D_bottom.jpg

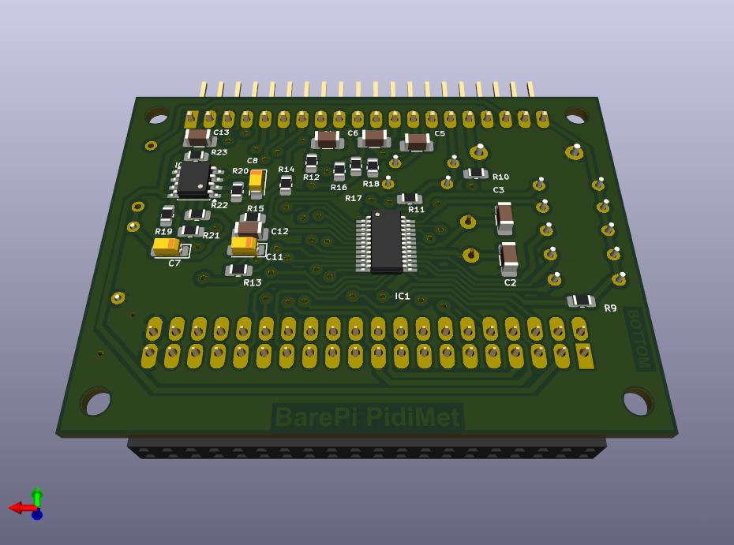
_www/img/BarePi_PidiMet_3D_bottom.jpg
