Panda381/BarePi/PidiMet/BarePi_PidiMet_bottom.png

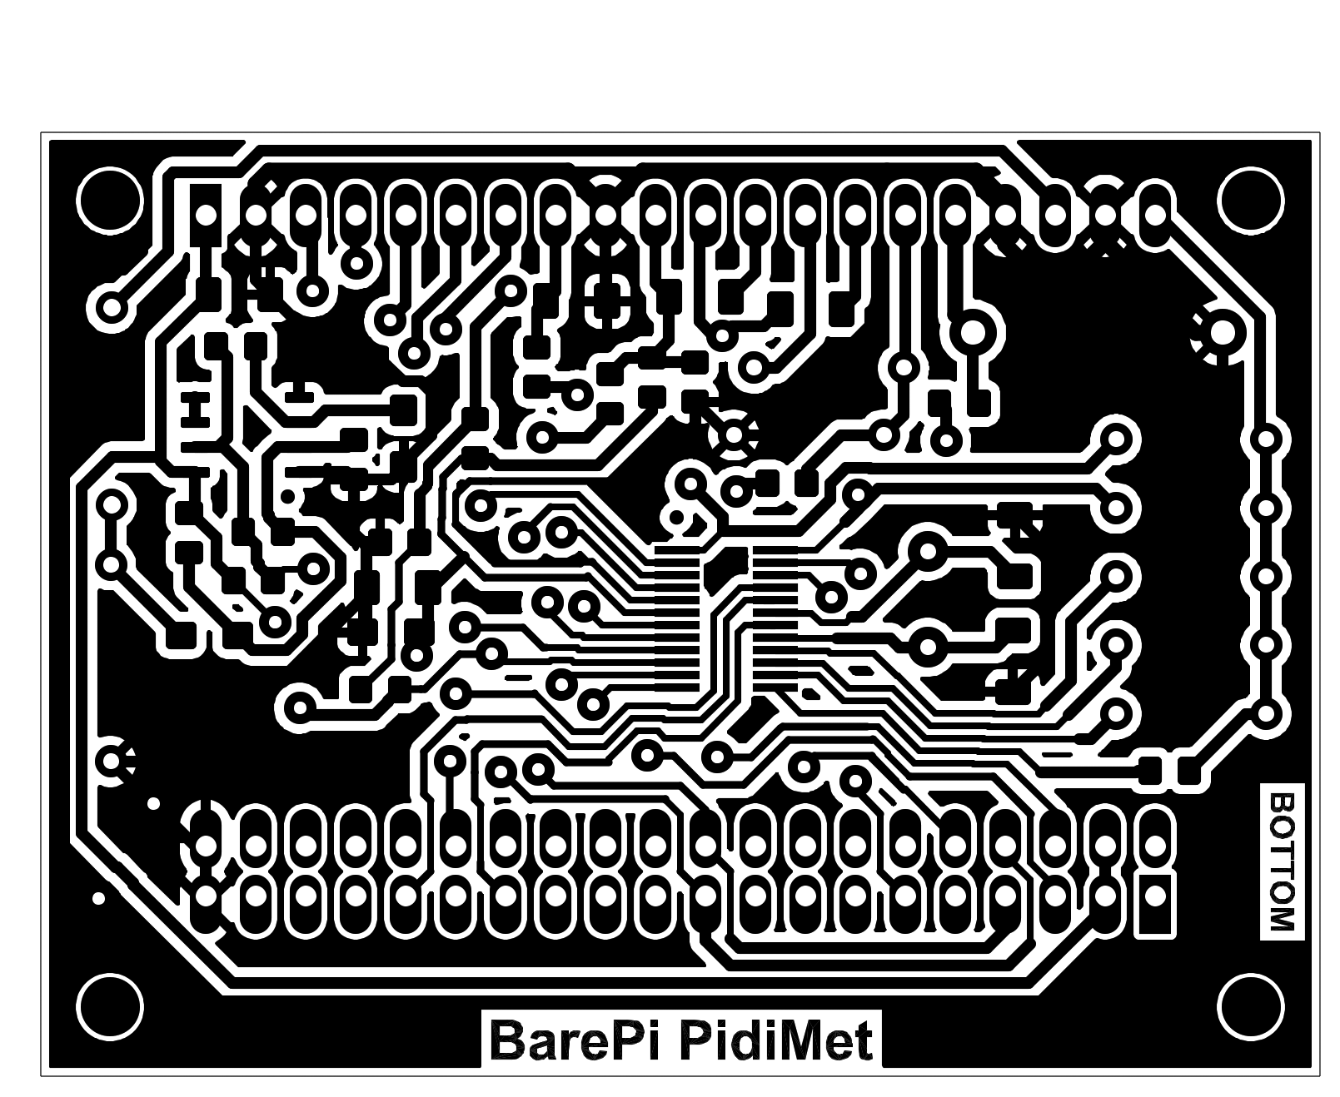
_www/img/BarePi_PidiMet_bottom.png
