Panda381/BarePi/PidiMet/BarePi_PidiMet_diagram.png

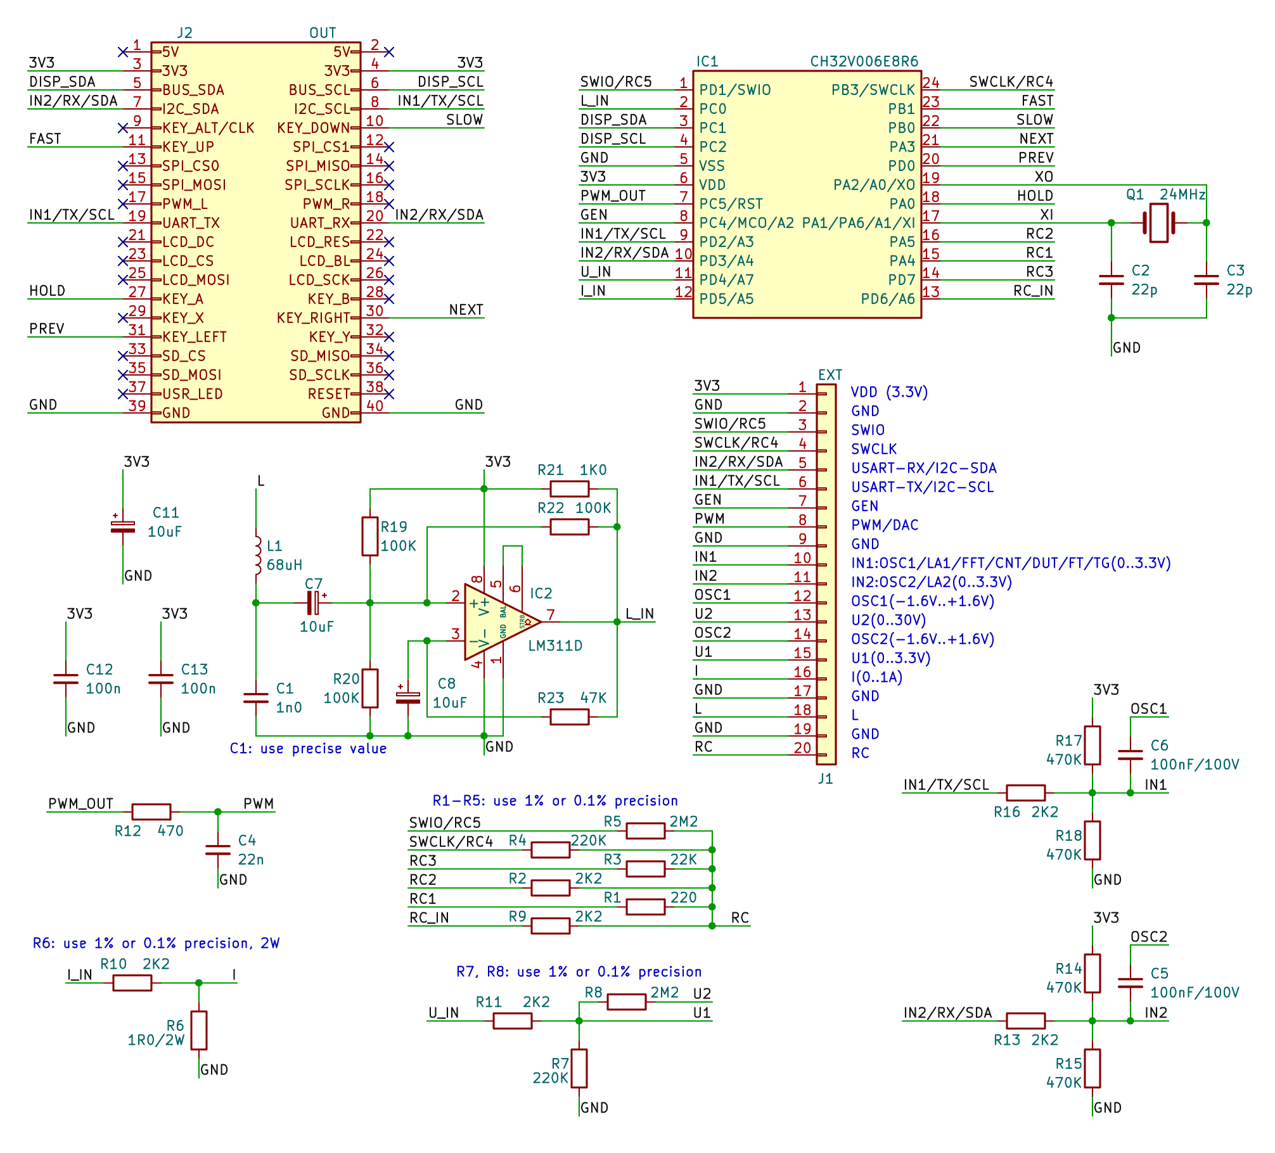
_www/img/BarePi_PidiMet_diagram.png
