Panda381/BarePi/_www/img/BarePi_PidiMet_m.jpg

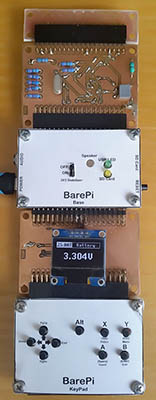
_www/img/BarePi_PidiMet_m.jpg
