Panda381/BarePi/PidiMet/BarePi_PidiMet_mounting.jpg

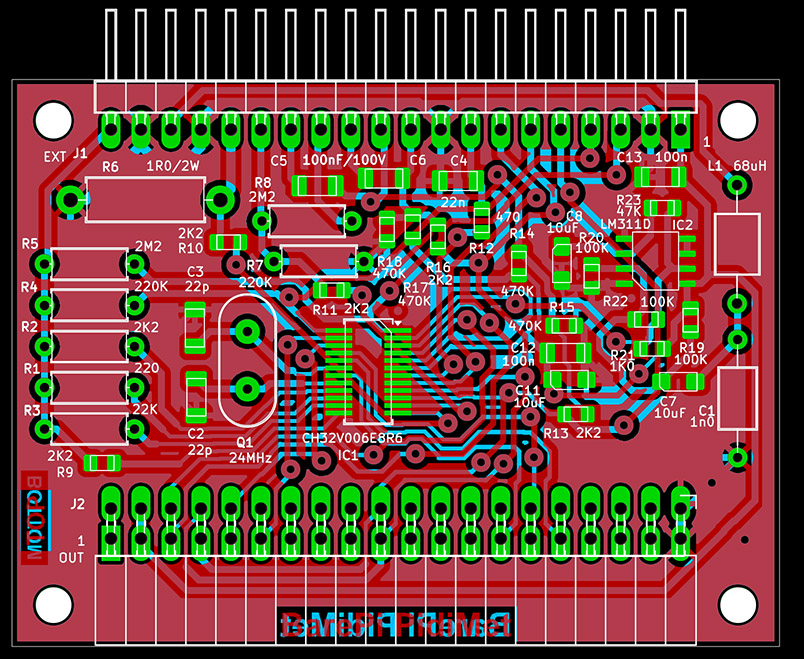
_www/img/BarePi_PidiMet_mounting.jpg
