Panda381/BarePi/_www/img/BarePi_PidiMetAdapter1_m.jpg

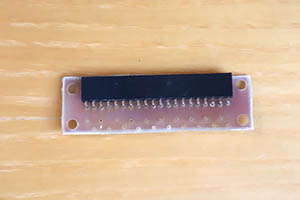
_www/img/BarePi_PidiMetAdapter1_m.jpg
