Panda381/BarePi/_www/img/BarePi_PidiMetAdapter3.jpg

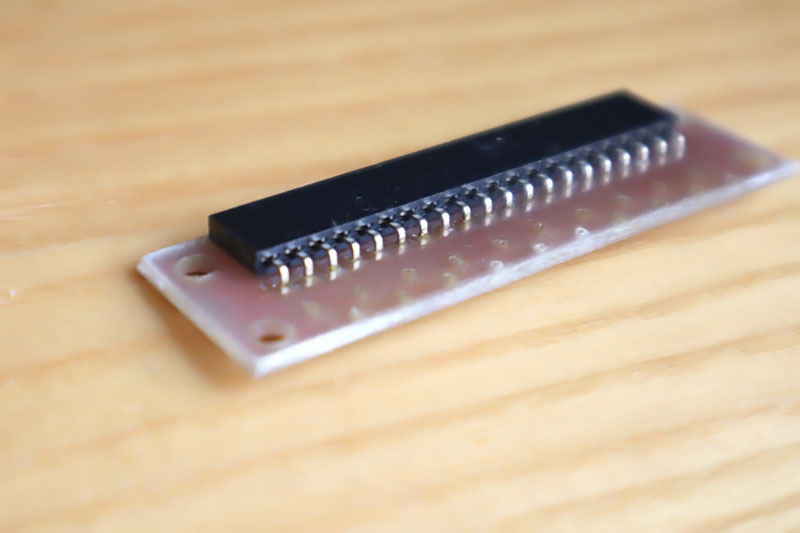
_www/img/BarePi_PidiMetAdapter3.jpg
