Panda381/BarePi/_www/img/BarePi_PidiMetAdapter_diagram_m.jpg

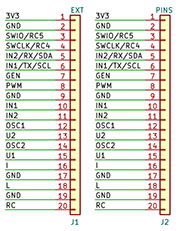
_www/img/BarePi_PidiMetAdapter_diagram_m.jpg
