Panda381/BarePi/_www/img/BarePi_PidiMetAdapter_mounting_m.jpg

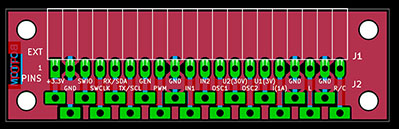
_www/img/BarePi_PidiMetAdapter_mounting_m.jpg
