Panda381/BarePi/_www/img/BarePi_PidiMetAdapter_top_m.jpg

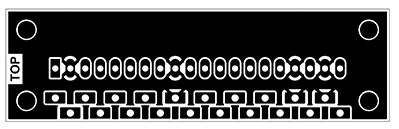
_www/img/BarePi_PidiMetAdapter_top_m.jpg
