Panda381/BarePi/_www/img/BarePi_PidiMetModes.jpg

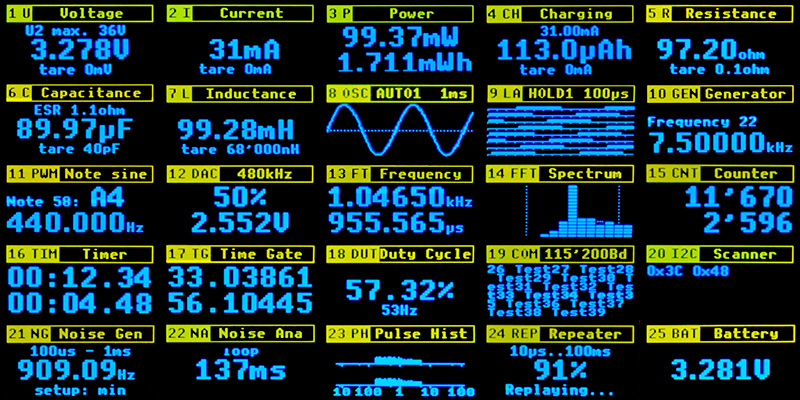
_www/img/BarePi_PidiMetModes.jpg
