Panda381/BarePi/_www/img/BarePi_PidiPad2.jpg

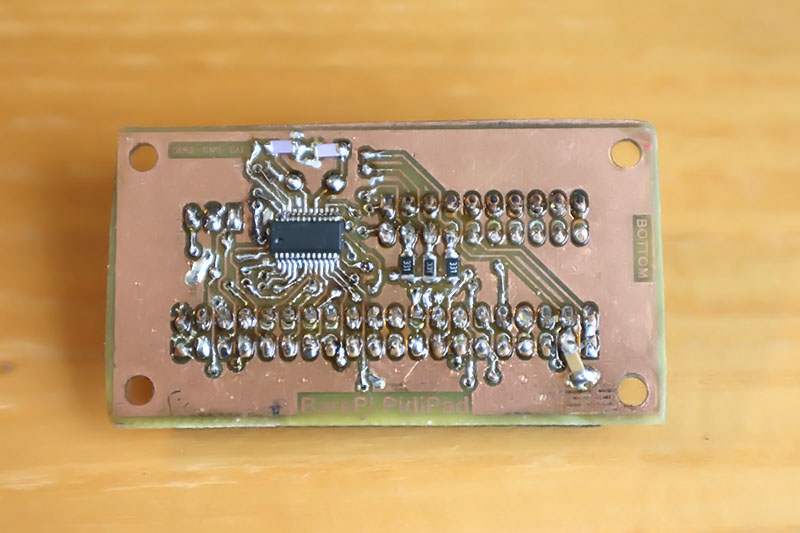
_www/img/BarePi_PidiPad2.jpg
