Panda381/BarePi/_www/img/BarePi_PidiPad3_m.jpg

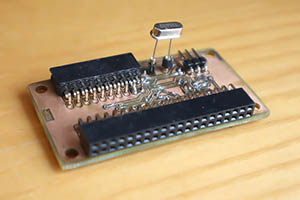
_www/img/BarePi_PidiPad3_m.jpg
