Panda381/BarePi/_www/img/BarePi_PidiPad.jpg

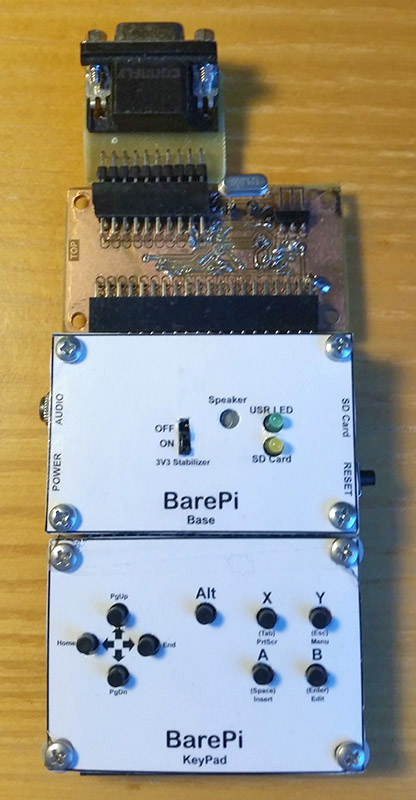
_www/img/BarePi_PidiPad.jpg
