Panda381/BarePi/_www/img/BarePi_PidiPad_diagram.png

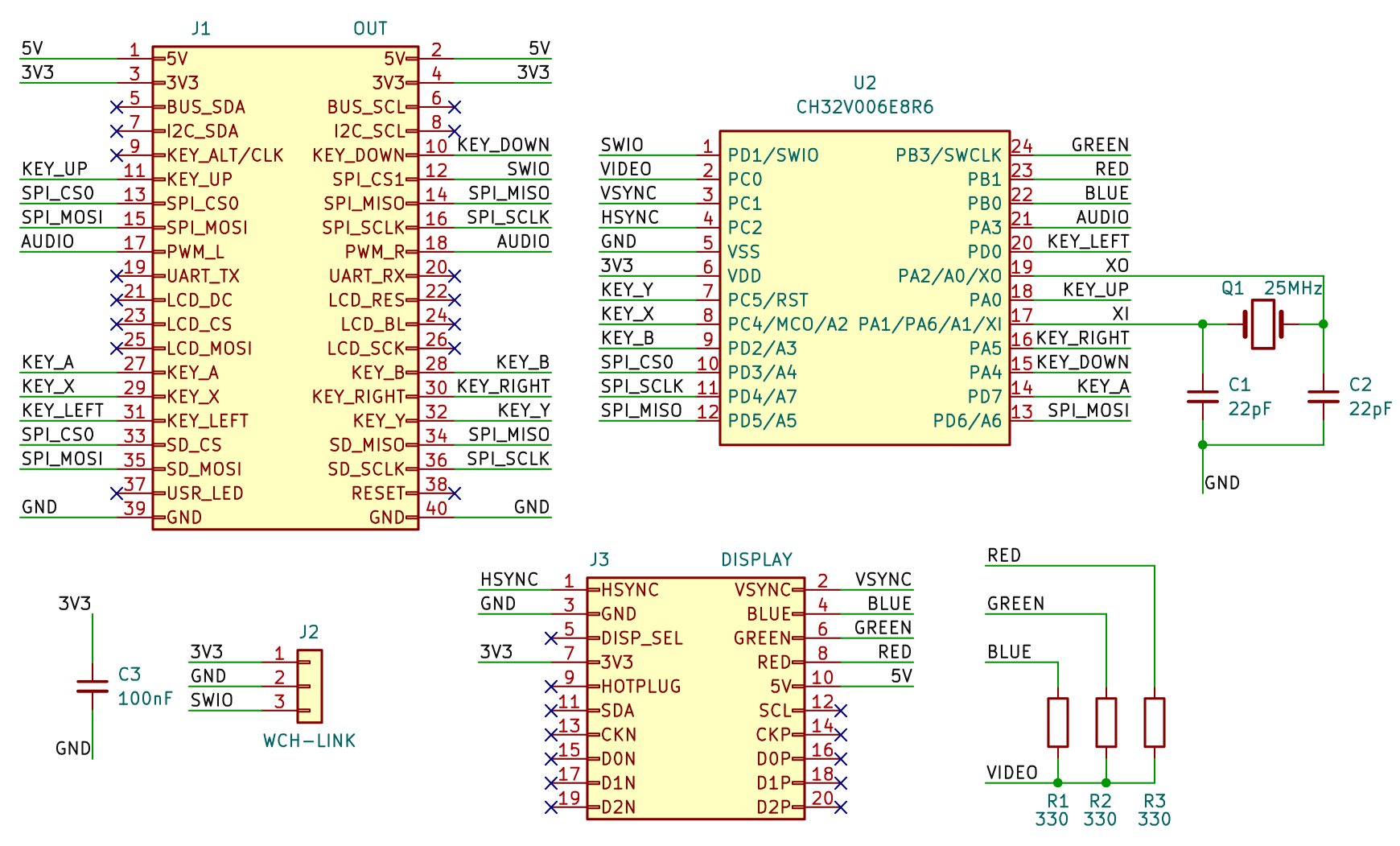
_www/img/BarePi_PidiPad_diagram.png
