Panda381/BarePi/PidiPad/BarePi_PidiPad_mounting.jpg

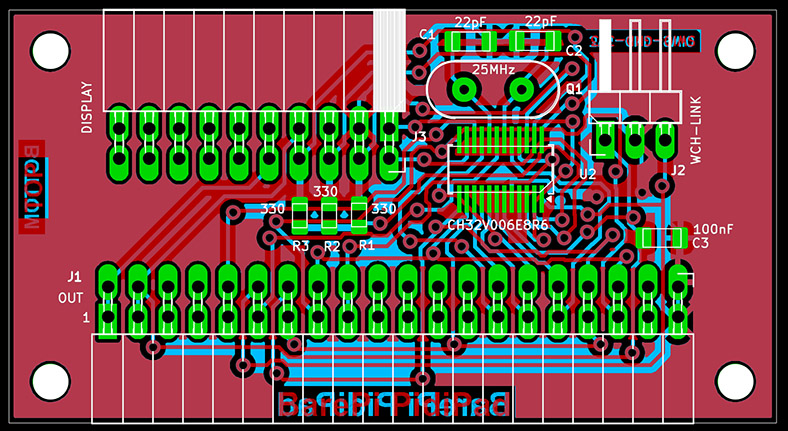
_www/img/BarePi_PidiPad_mounting.jpg
