Panda381/BarePi/_www/img/BarePi_PidiPad_mounting_m.jpg

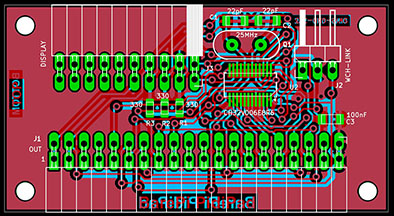
_www/img/BarePi_PidiPad_mounting_m.jpg
