Panda381/BarePi/PidiPad/BarePi_PidiPad_panel.png

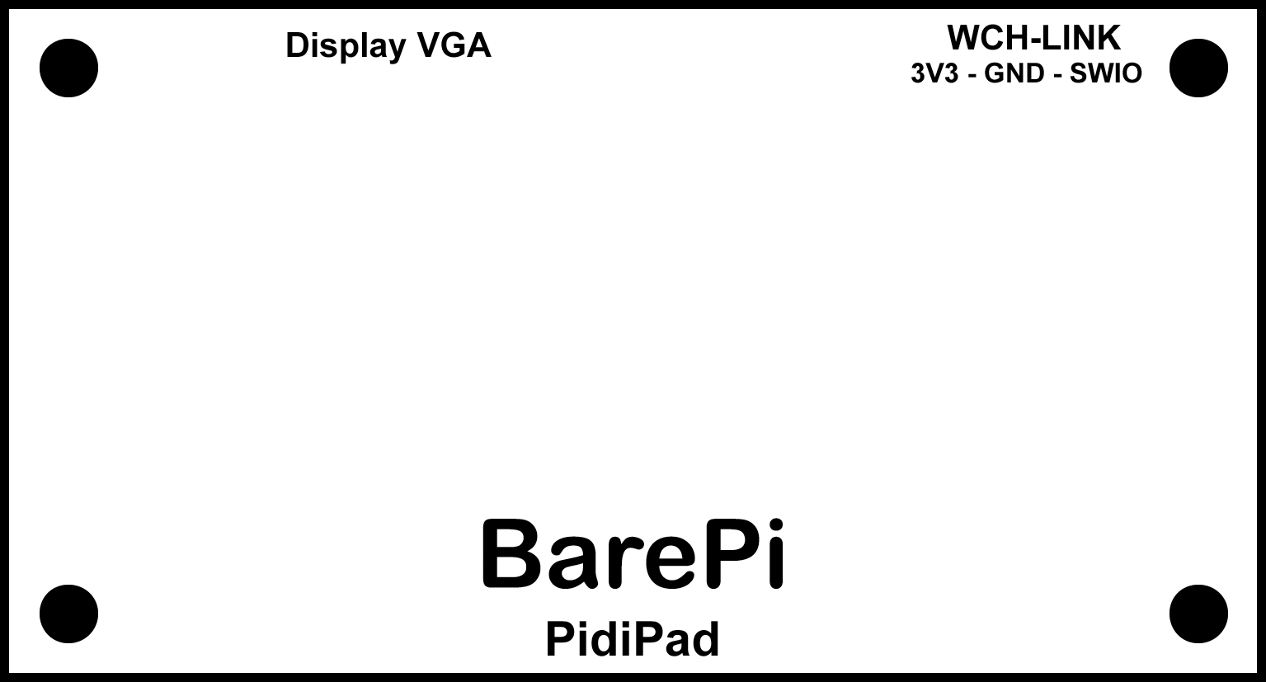
_www/img/BarePi_PidiPad_panel.png
