Panda381/BarePi/_www/img/BarePi_PidiPadAps.jpg

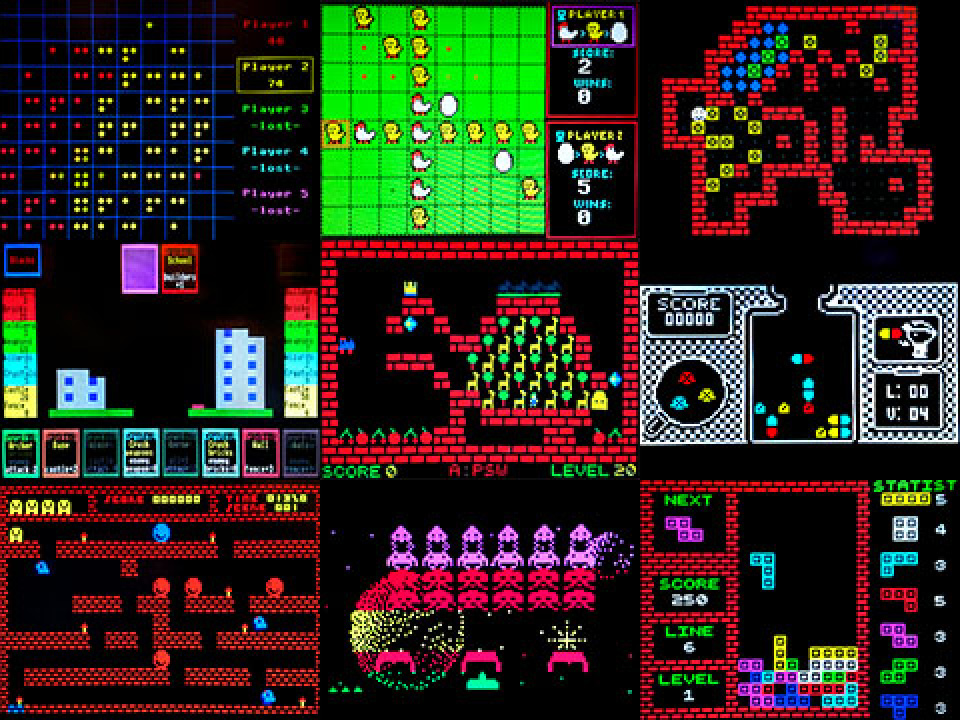
_www/img/BarePi_PidiPadAps.jpg
