Panda381/BarePi/_www/img/BarePi_pins2.jpg

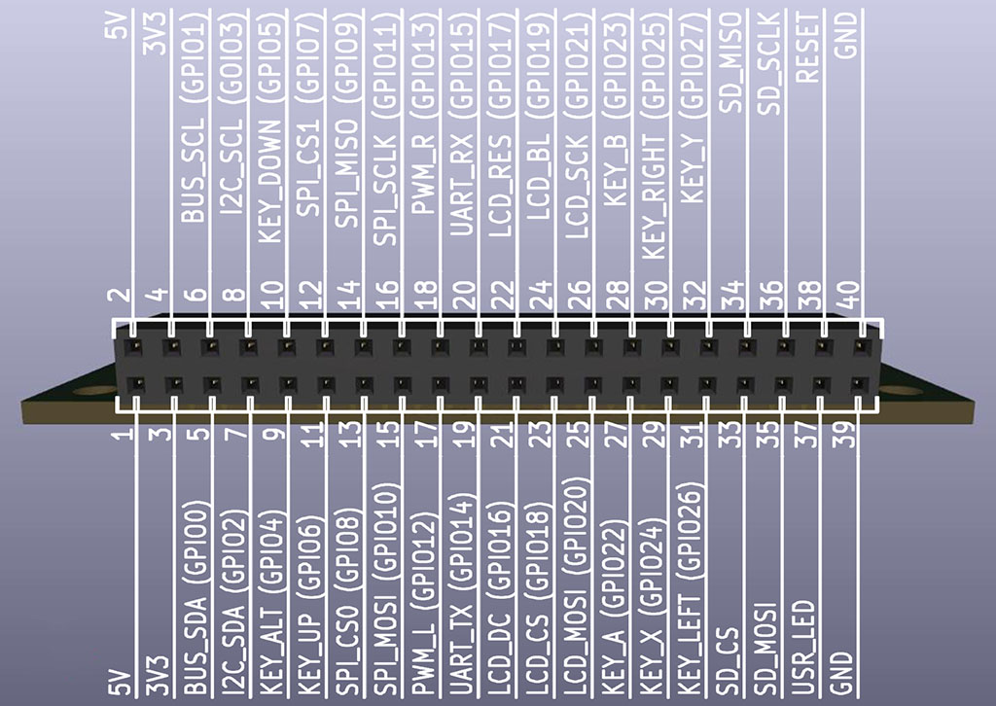
_www/img/BarePi_pins2.jpg
