Panda381/BarePi/_www/img/BarePi_Port3.jpg

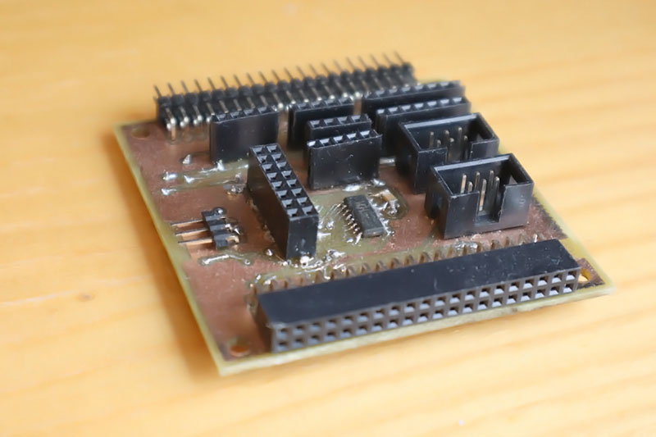
_www/img/BarePi_Port3.jpg
