Panda381/BarePi/_www/img/BarePi_Port5.jpg

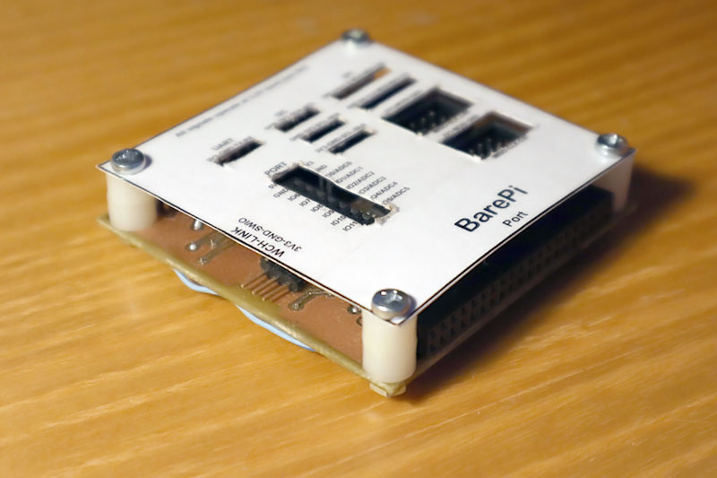
_www/img/BarePi_Port5.jpg
