Panda381/BarePi/Port/BarePi_Port_3D.jpg

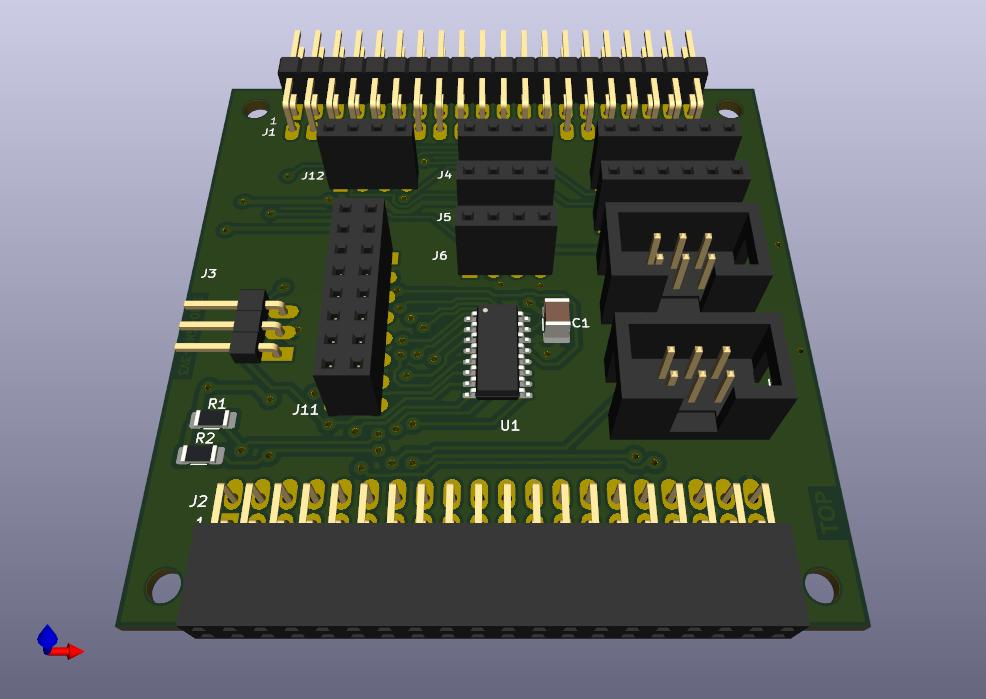
_www/img/BarePi_Port_3D.jpg
