Panda381/BarePi/Port/BarePi_Port_bottom.png

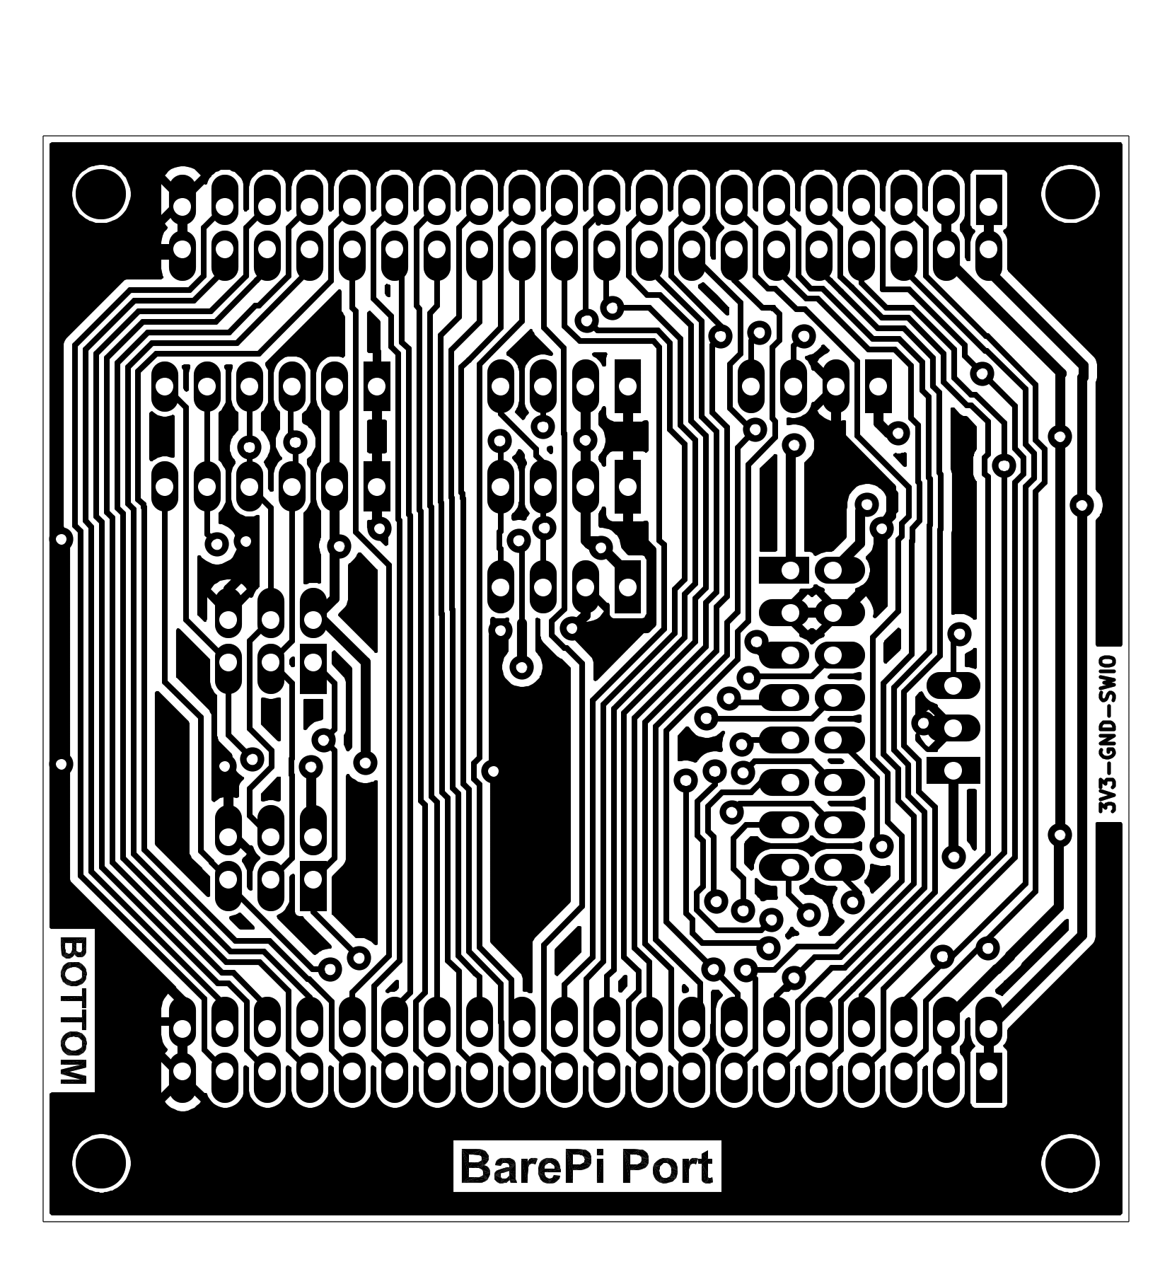
_www/img/BarePi_Port_bottom.png
