Panda381/BarePi/Port/BarePi_Port_label.png

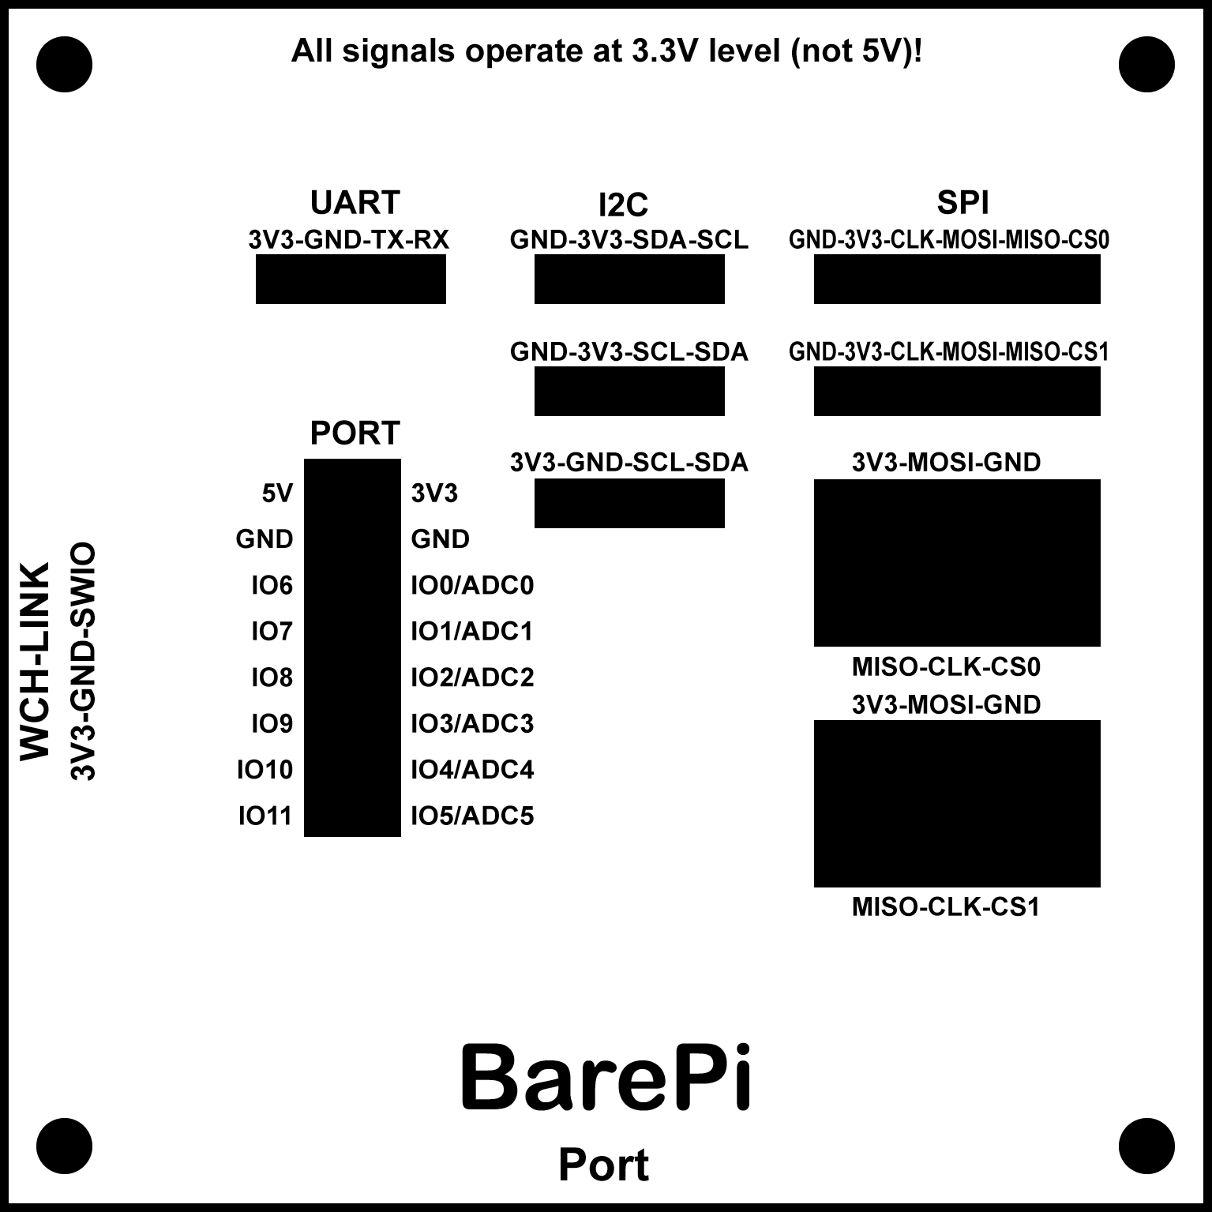
_www/img/BarePi_Port_label.png
