Panda381/BarePi/Port/BarePi_Port_mounting.jpg

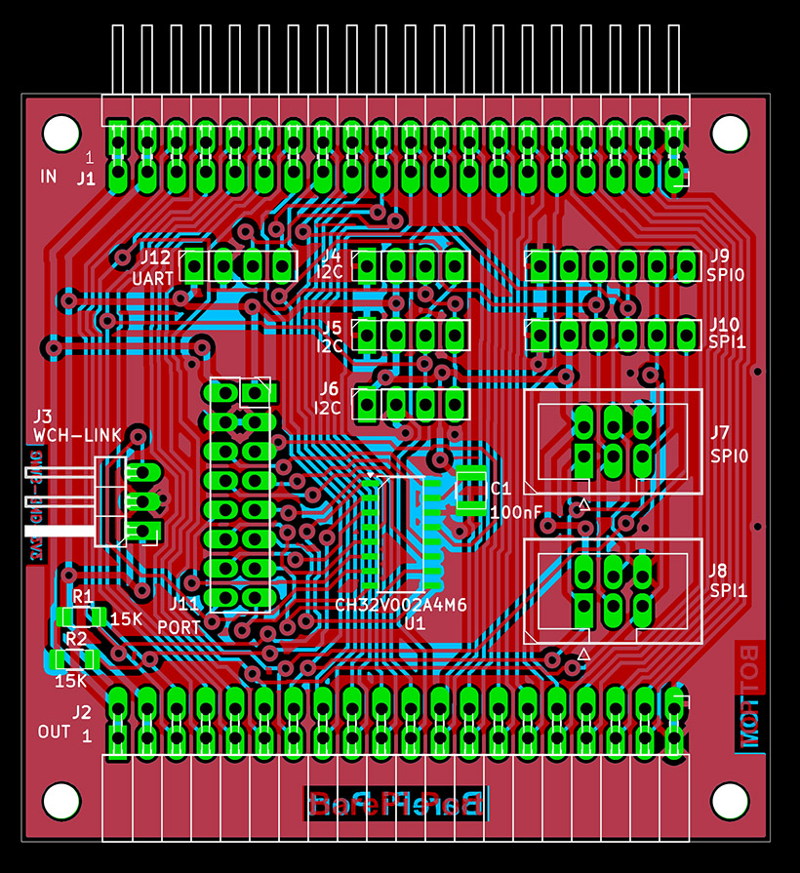
_www/img/BarePi_Port_mounting.jpg
