Panda381/BarePi/_www/img/BarePi_Port_top_m.jpg

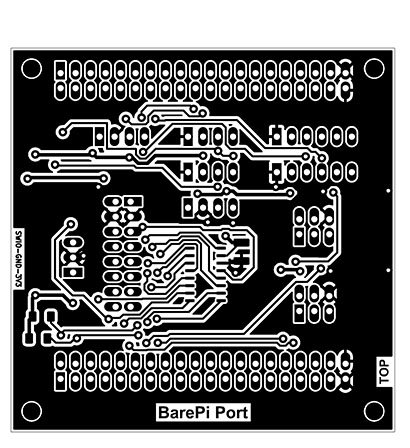
_www/img/BarePi_Port_top_m.jpg
