Panda381/BarePi/_www/img/BarePi_RTC1_m.jpg

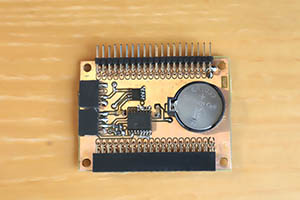
_www/img/BarePi_RTC1_m.jpg
