Panda381/BarePi/_www/img/BarePi_RTC_3D.jpg

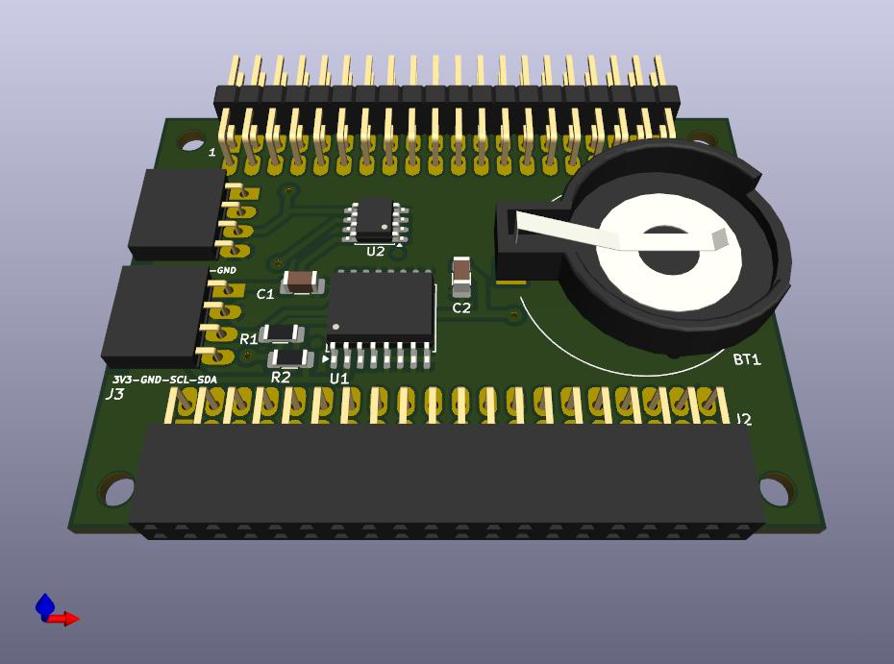
_www/img/BarePi_RTC_3D.jpg
