Panda381/BarePi/_www/img/BarePi_RTC_3D_bottom.jpg

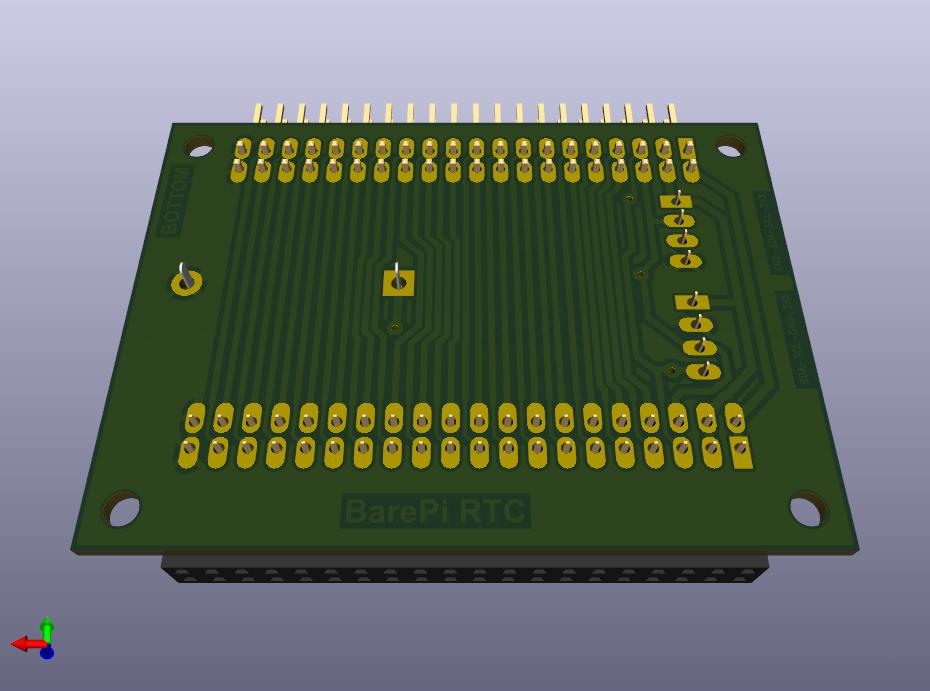
_www/img/BarePi_RTC_3D_bottom.jpg
