Panda381/BarePi/_www/img/BarePi_RTC_diagram.png

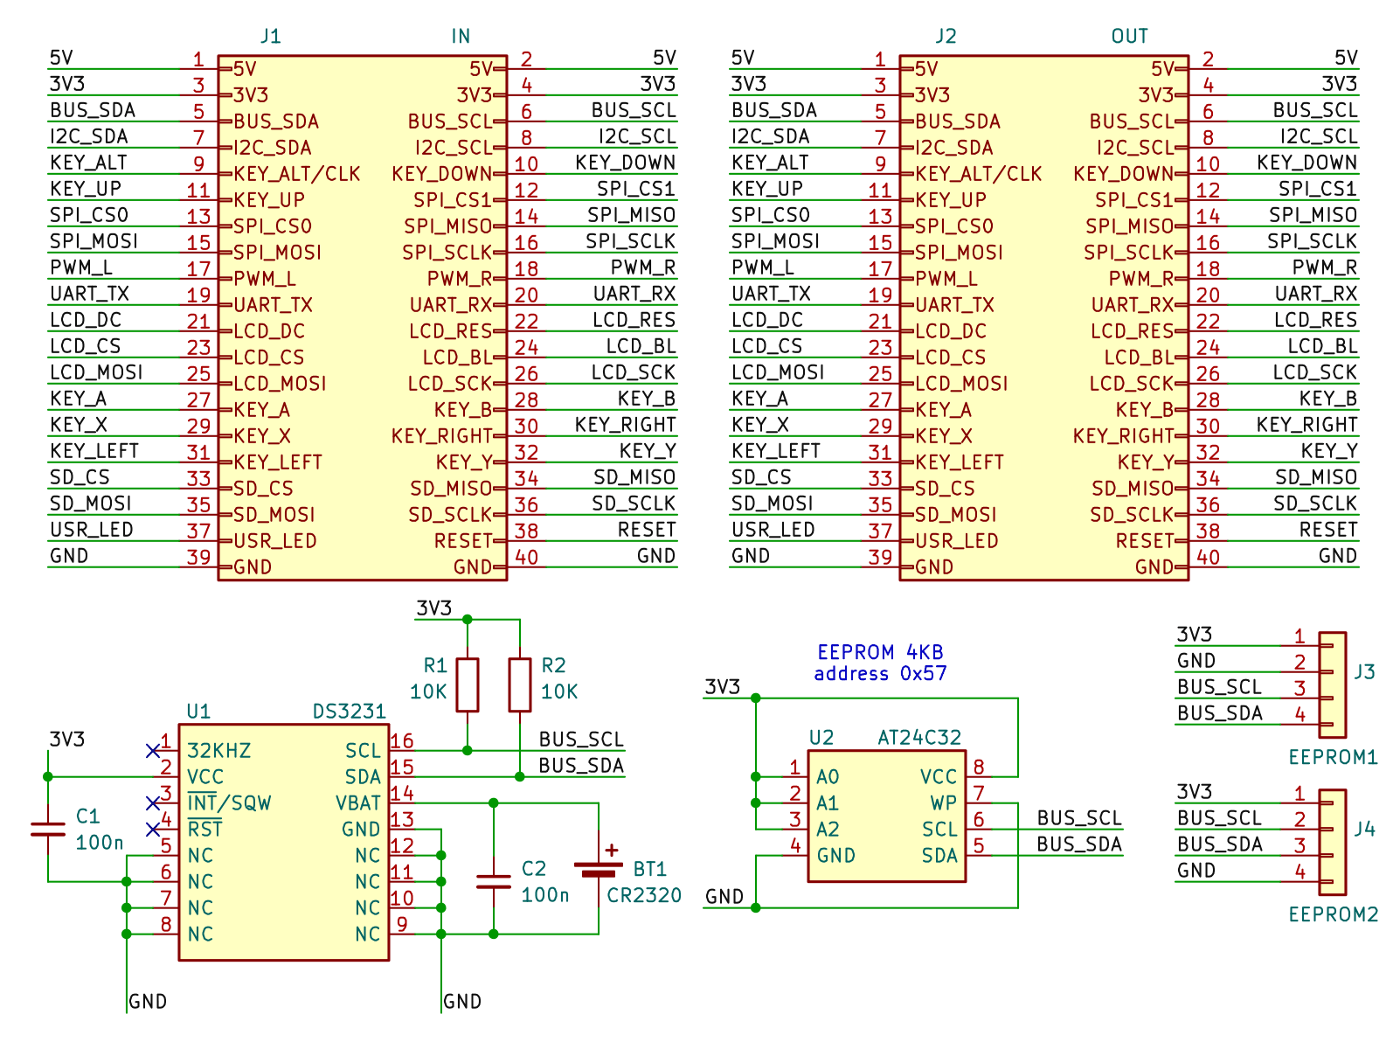
_www/img/BarePi_RTC_diagram.png
