Panda381/BarePi/_www/img/BarePi_RTC_top_m.jpg

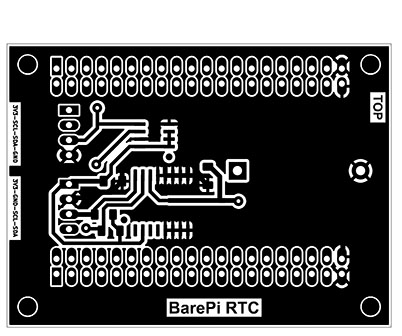
_www/img/BarePi_RTC_top_m.jpg
