Panda381/BarePi/_www/img/BarePi_SumoPad1_m.jpg

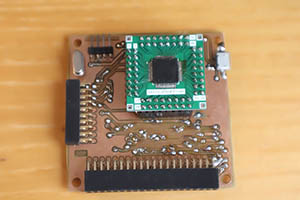
_www/img/BarePi_SumoPad1_m.jpg
