Panda381/BarePi/_www/img/BarePi_SumoPad3_m.jpg

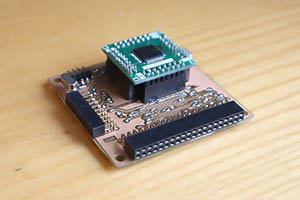
_www/img/BarePi_SumoPad3_m.jpg
