Panda381/BarePi/SumoPad/BarePi_SumoPad_3D_bottom.jpg

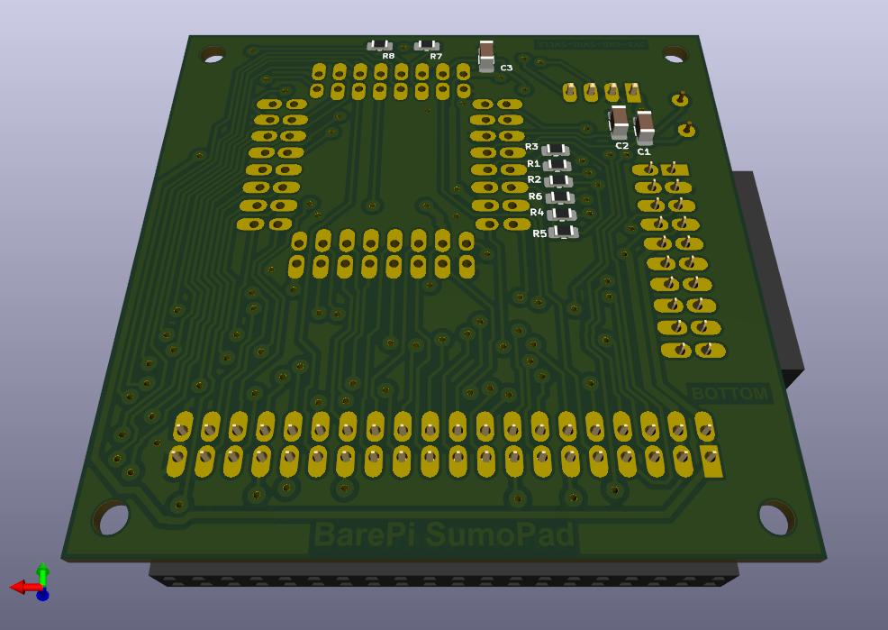
_www/img/BarePi_SumoPad_3D_bottom.jpg
