Panda381/BarePi/SumoPad/BarePi_SumoPad_bottom.png

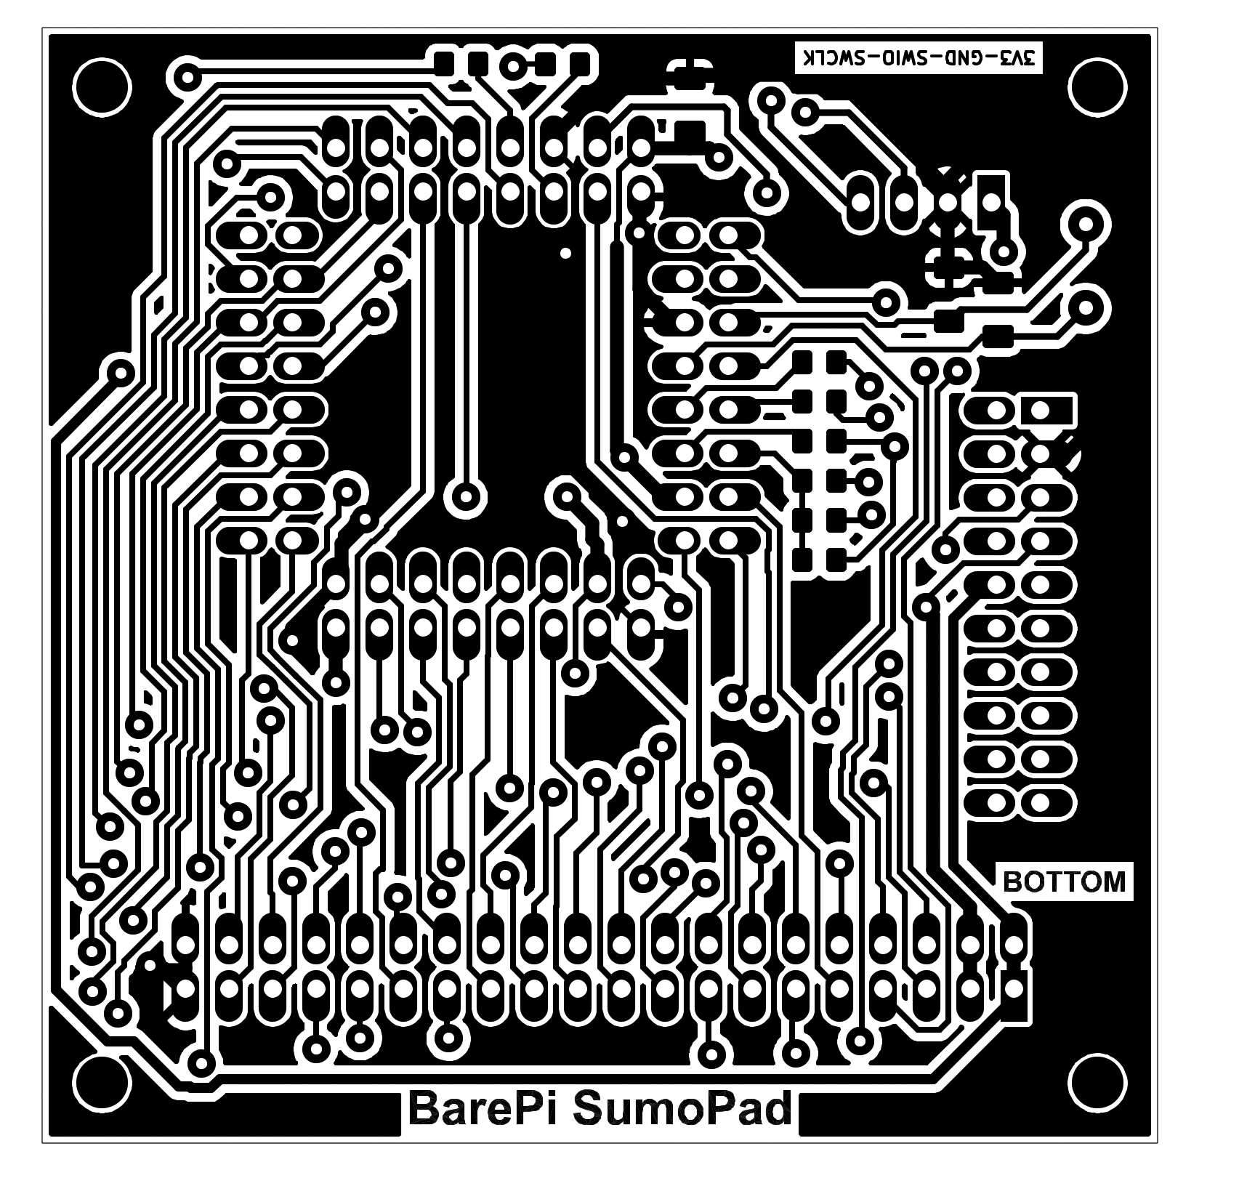
_www/img/BarePi_SumoPad_bottom.png
