Panda381/BarePi/_www/img/BarePi_SumoPad_mounting_m.jpg

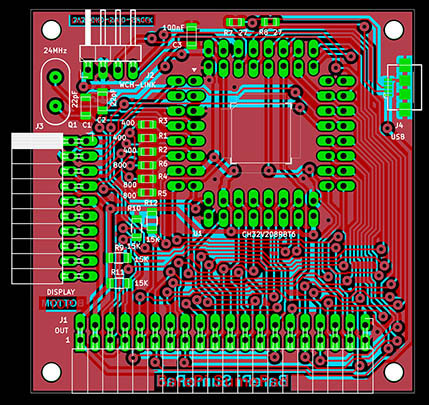
_www/img/BarePi_SumoPad_mounting_m.jpg
