Panda381/BarePi/_www/img/BarePi_TinyJoypad1.jpg

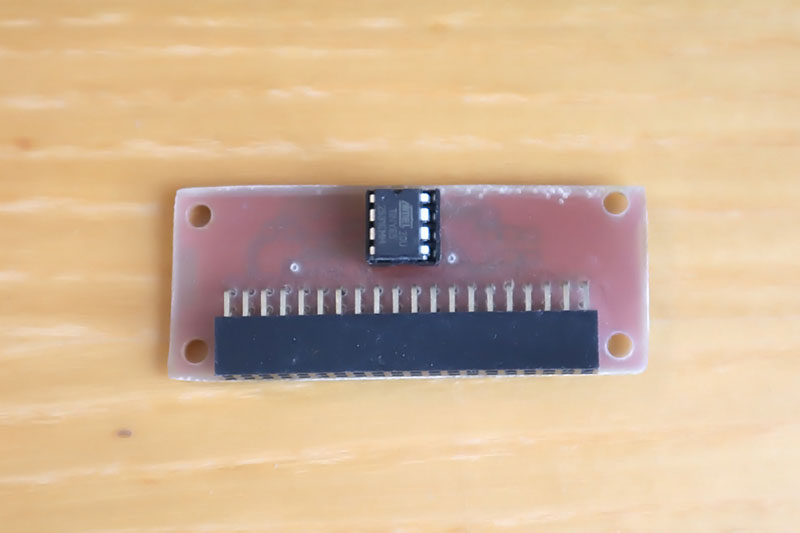
_www/img/BarePi_TinyJoypad1.jpg
