Panda381/BarePi/_www/img/BarePi_TinyJoypad3_m.jpg

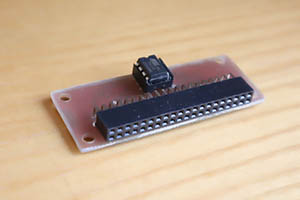
_www/img/BarePi_TinyJoypad3_m.jpg
