Panda381/BarePi/_www/img/BarePi_TinyJoypad.jpg

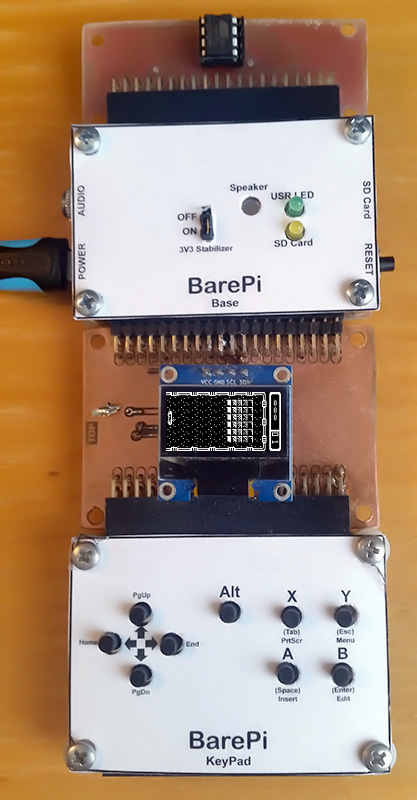
_www/img/BarePi_TinyJoypad.jpg
