Panda381/BarePi/TinyJoypad/BarePi_TinyJoypad_3D.jpg

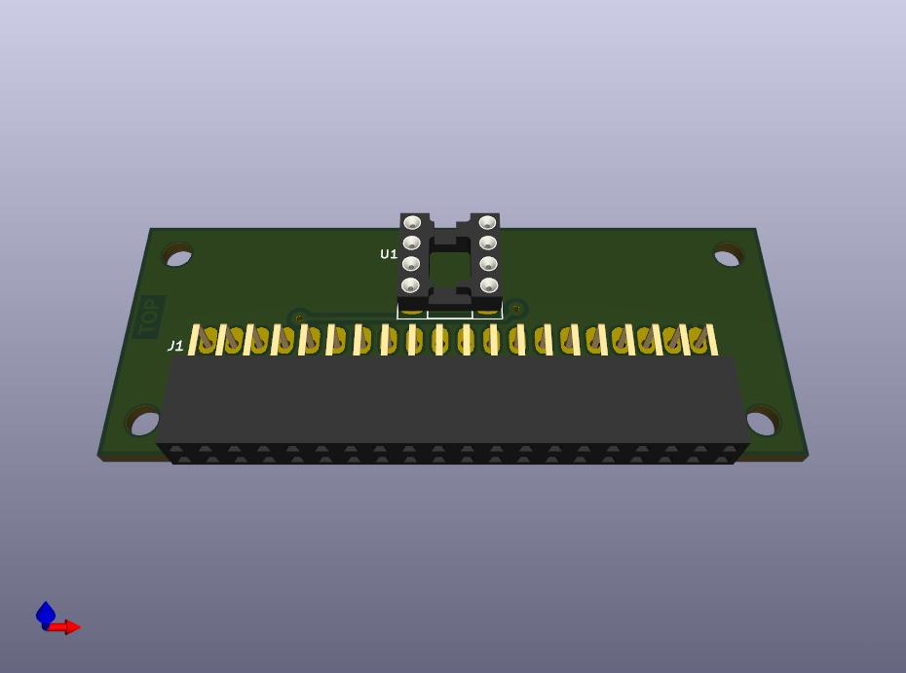
_www/img/BarePi_TinyJoypad_3D.jpg
