Panda381/BarePi/_www/img/BarePi_TinyJoypad_3D_m.jpg

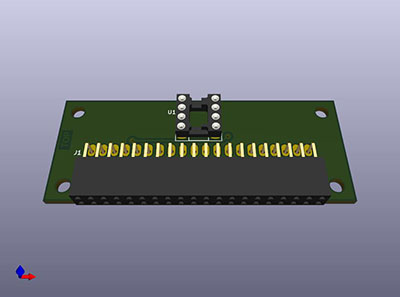
_www/img/BarePi_TinyJoypad_3D_m.jpg
