Panda381/BarePi/_www/img/BarePi_TinyJoypad_bottom_m.jpg

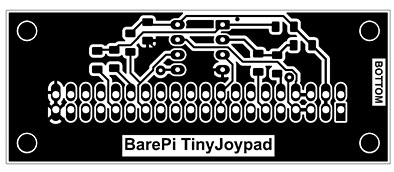
_www/img/BarePi_TinyJoypad_bottom_m.jpg
