Panda381/BarePi/TinyJoypad/BarePi_TinyJoypad_top.png

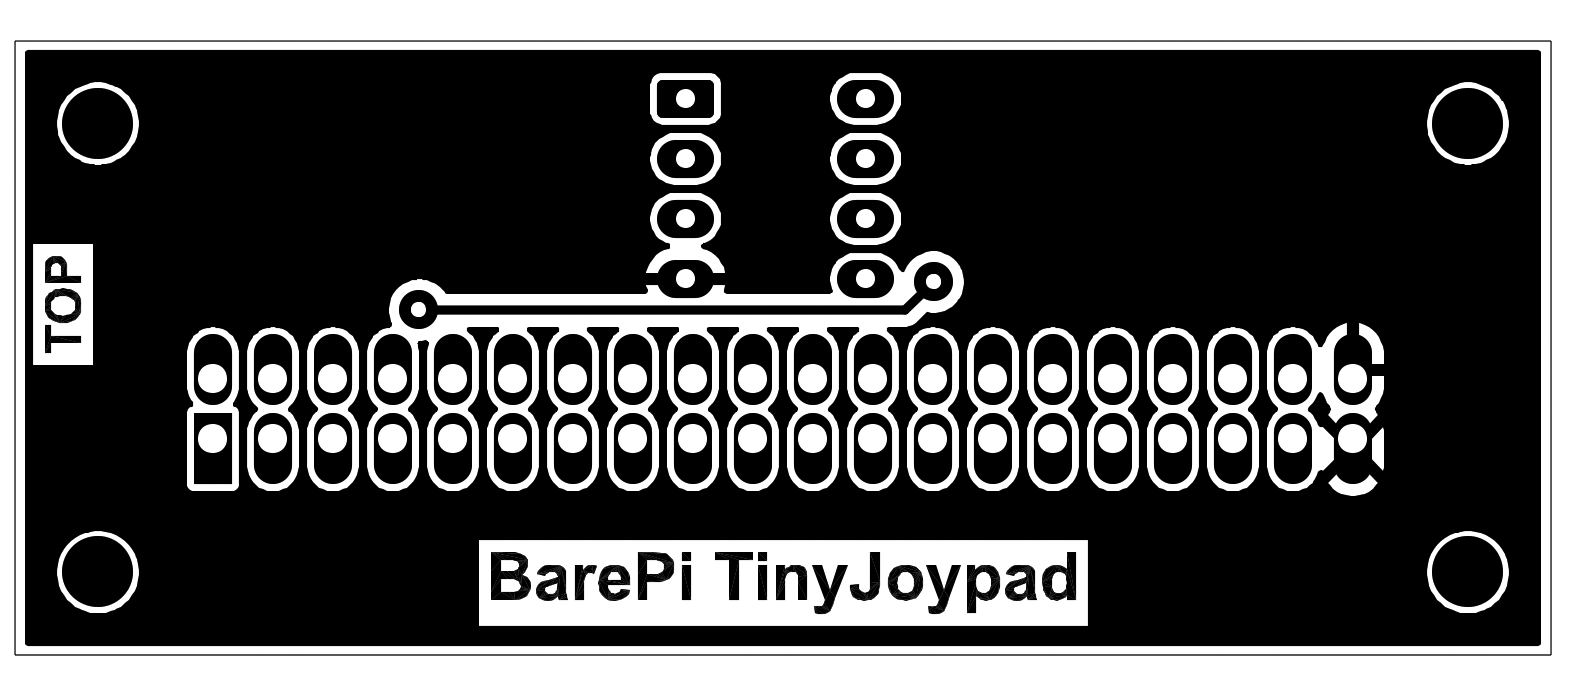
_www/img/BarePi_TinyJoypad_top.png
