Panda381/BarePi/_www/img/BarePi_TinyJoypadApps.jpg

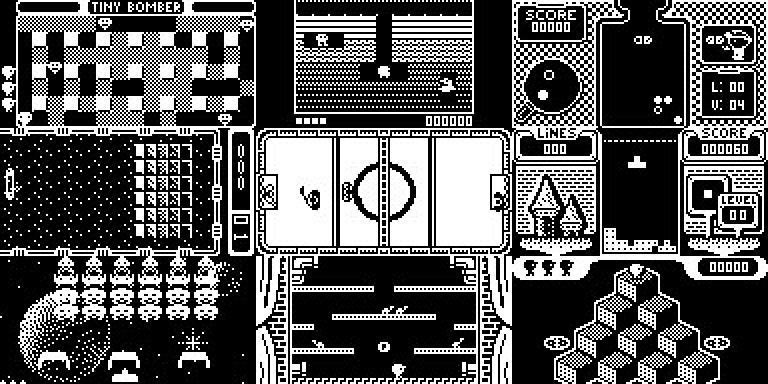
_www/img/BarePi_TinyJoypadApps.jpg
