Panda381/BarePi/_www/img/BarePi_TweetyBoy1_m.jpg

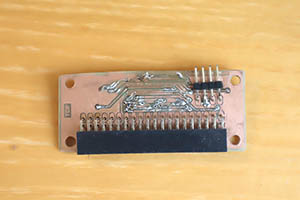
_www/img/BarePi_TweetyBoy1_m.jpg
