Panda381/BarePi/_www/img/BarePi_TweetyBoy2_m.jpg

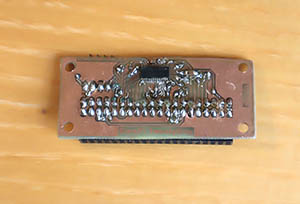
_www/img/BarePi_TweetyBoy2_m.jpg
