Panda381/BarePi/_www/img/BarePi_TweetyBoy3_m.jpg

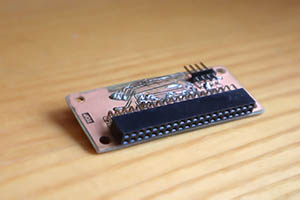
_www/img/BarePi_TweetyBoy3_m.jpg
