Panda381/BarePi/TweetyBoy/BarePi_TweetyBoy_bottom.png

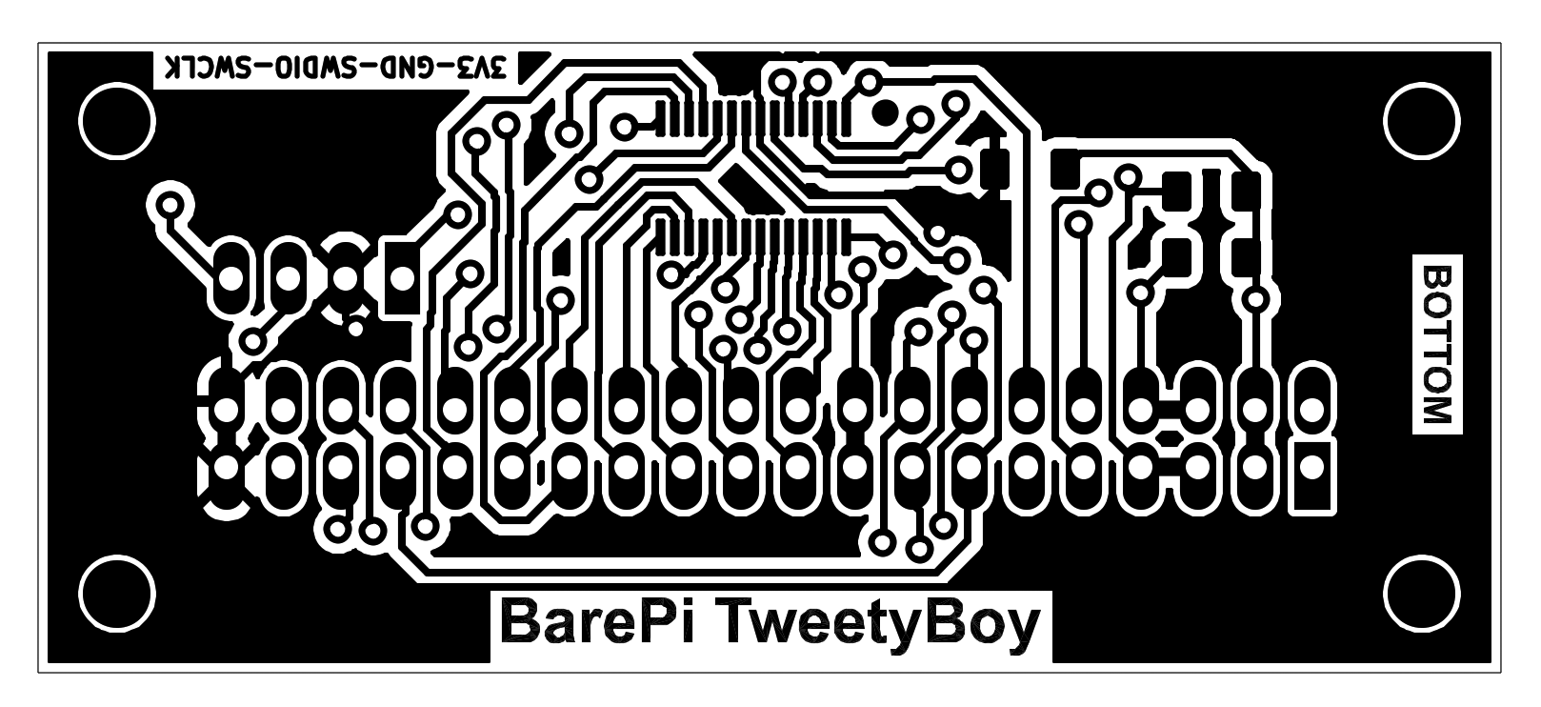
_www/img/BarePi_TweetyBoy_bottom.png
