Panda381/BarePi/TweetyBoy/BarePi_TweetyBoy_diagram.png

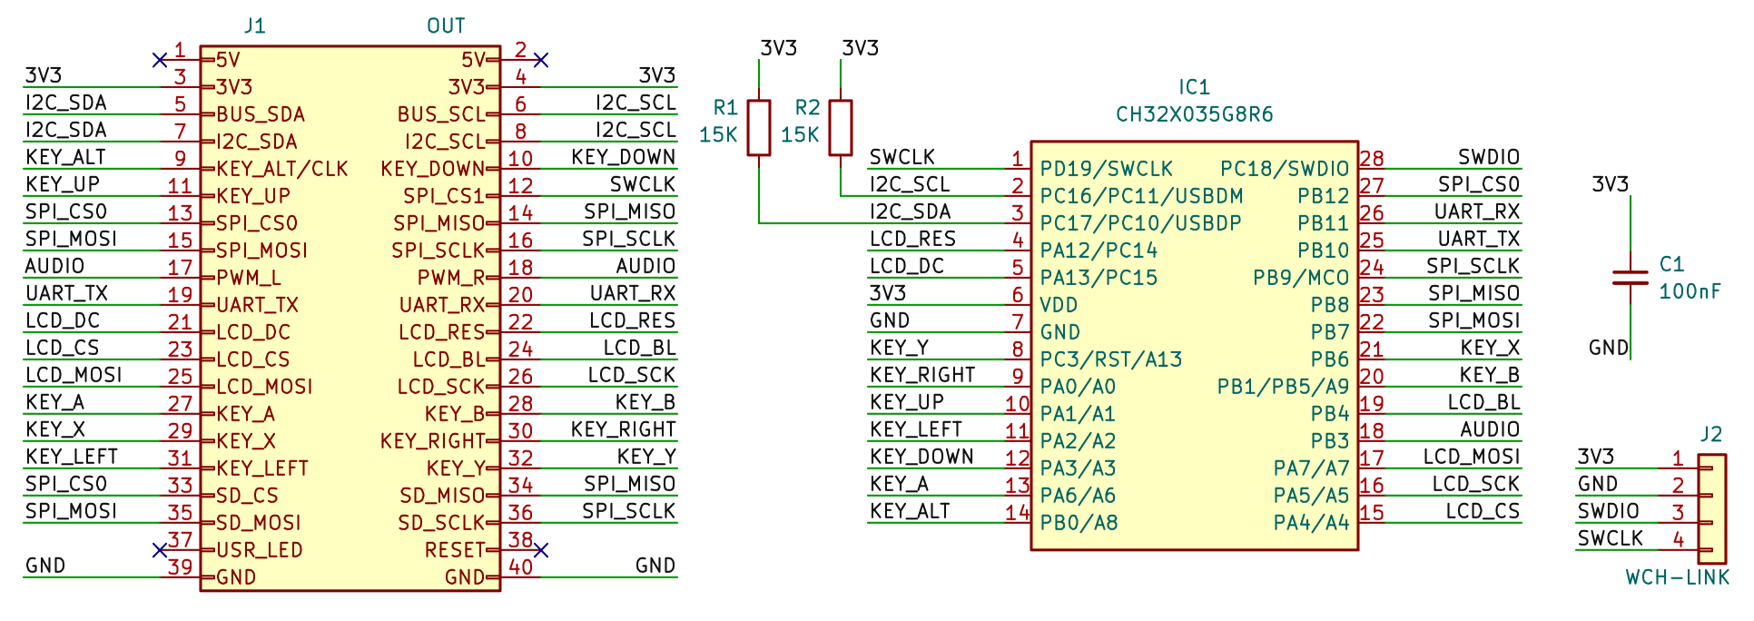
_www/img/BarePi_TweetyBoy_diagram.png
