Panda381/BarePi/_www/img/BarePi_TweetyBoy_mounting_m.jpg

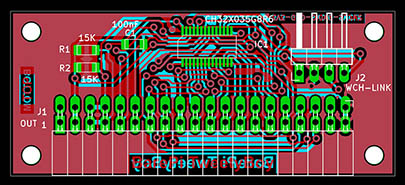
_www/img/BarePi_TweetyBoy_mounting_m.jpg
