Panda381/BarePi/_www/img/BarePi_TweetyBoy_panel_m.jpg

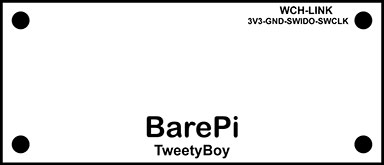
_www/img/BarePi_TweetyBoy_panel_m.jpg
