Panda381/BarePi/TweetyBoy/BarePi_TweetyBoy_top.png

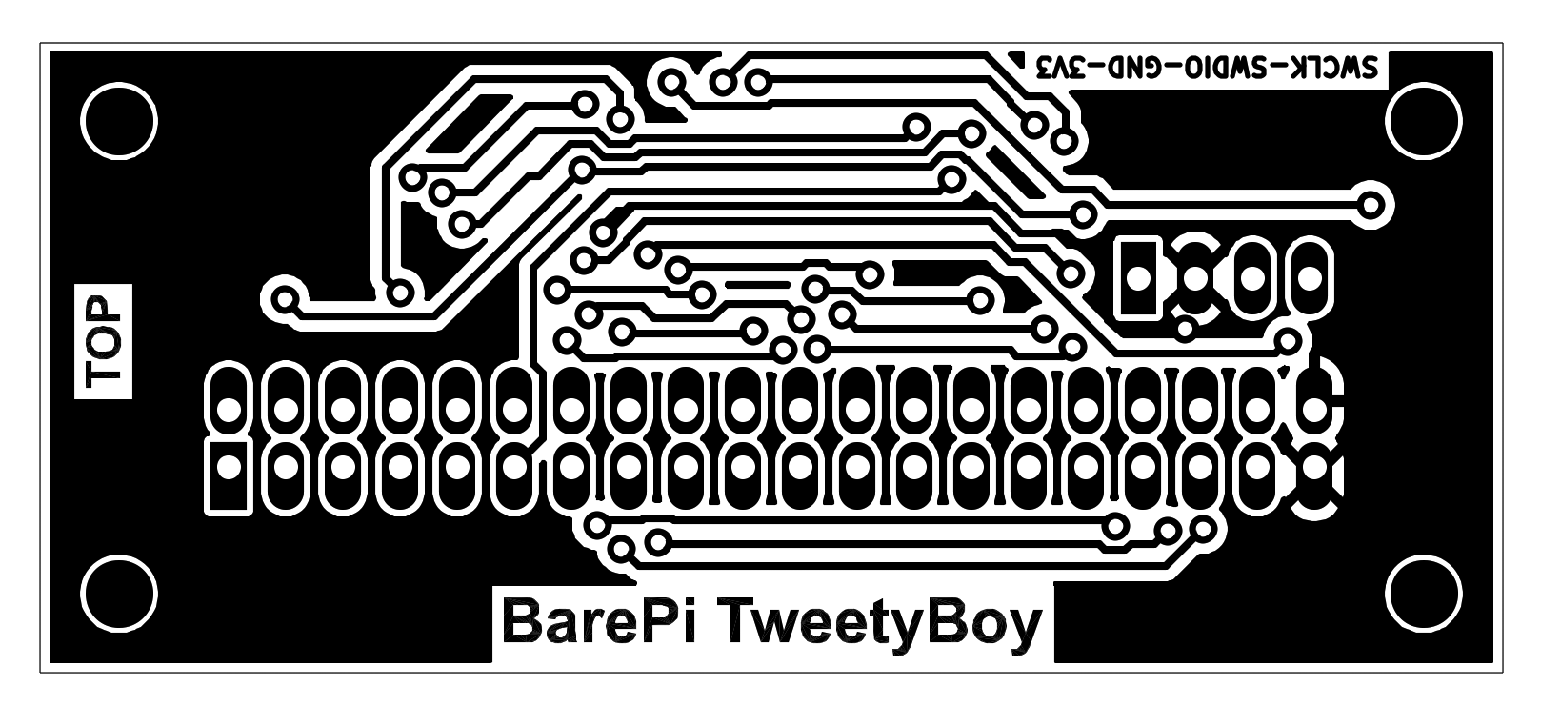
_www/img/BarePi_TweetyBoy_top.png
