Panda381/BarePi/_www/img/BarePi_TweetyBoyApps.jpg

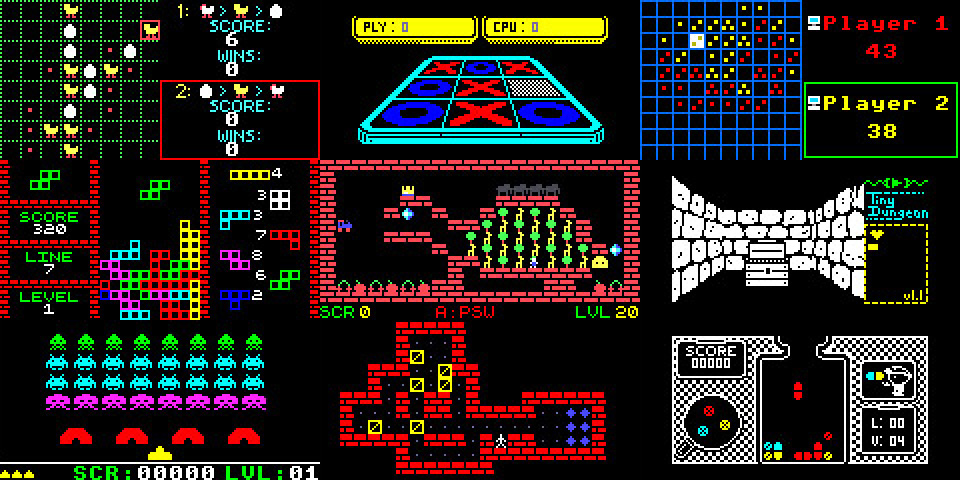
_www/img/BarePi_TweetyBoyApps.jpg
