Panda381/BarePi/_www/img/BarePi_Zero1.jpg

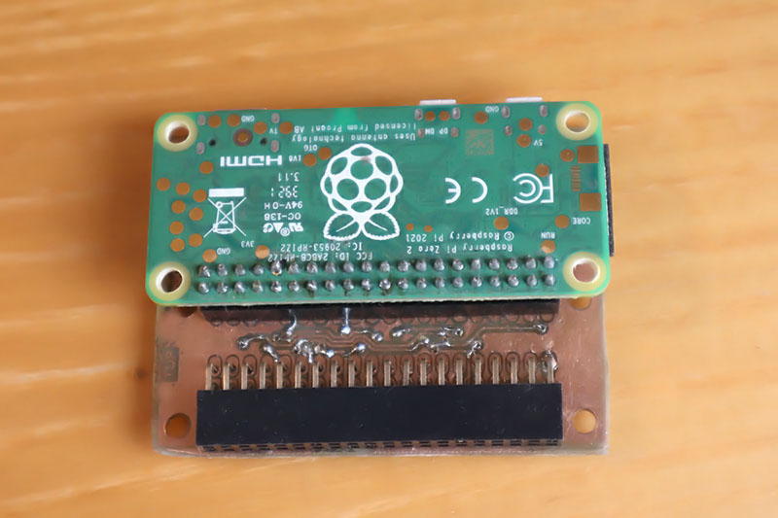
_www/img/BarePi_Zero1.jpg
