Panda381/BarePi/_www/img/BarePi_Zero2.jpg

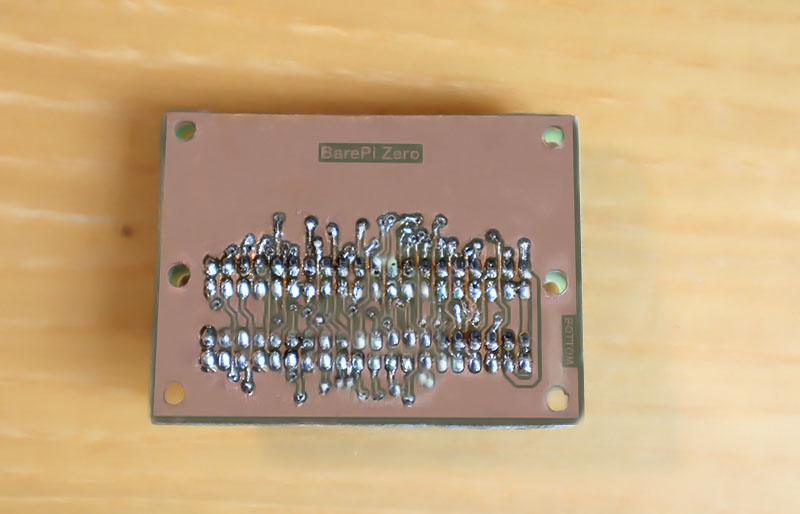
_www/img/BarePi_Zero2.jpg
