Panda381/BarePi/_www/img/BarePi_Zero4.jpg

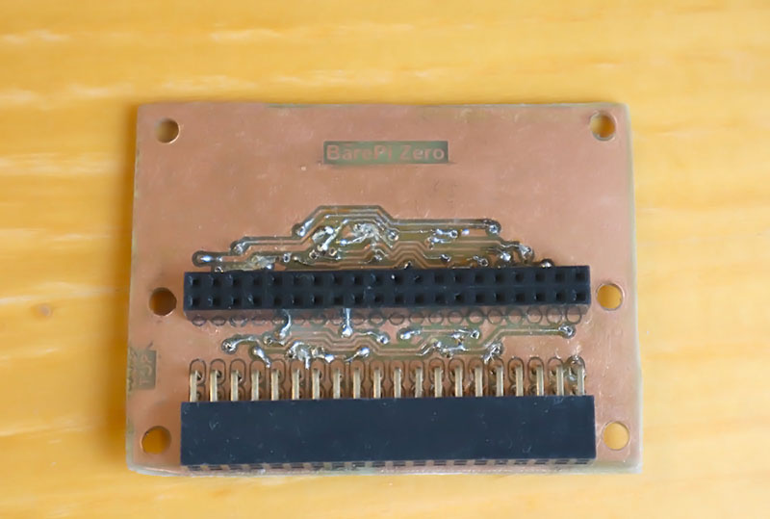
_www/img/BarePi_Zero4.jpg
