Panda381/BarePi/Zero/BarePi_Zero_3D.jpg

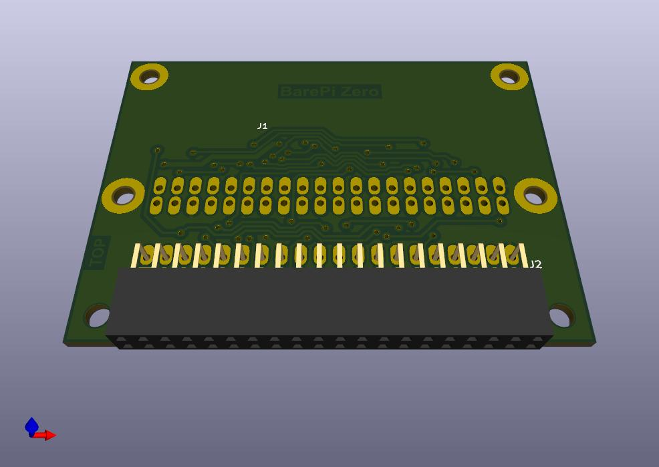
_www/img/BarePi_Zero_3D.jpg
