Panda381/BarePi/Zero/BarePi_Zero_3D_bottom.jpg

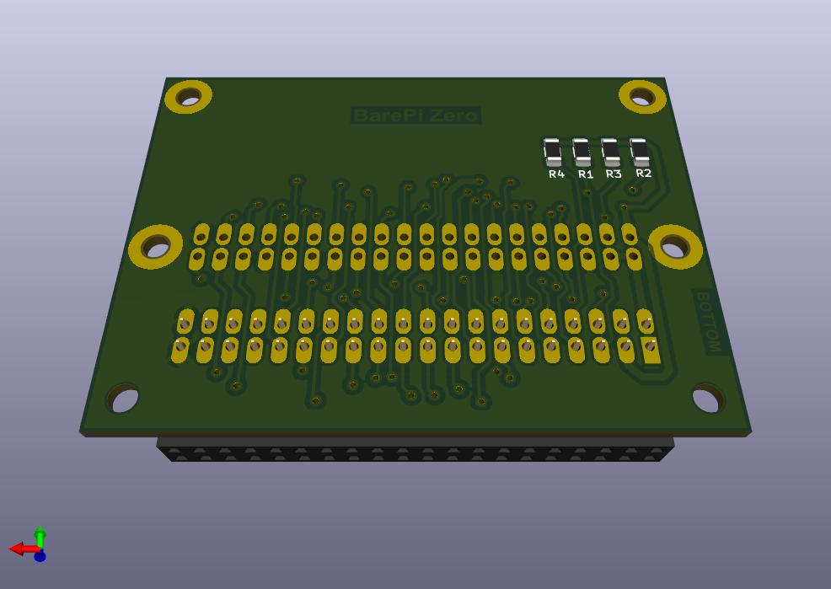
_www/img/BarePi_Zero_3D_bottom.jpg
