Panda381/BarePi/_www/img/BarePi_Zero_bottom_m.jpg

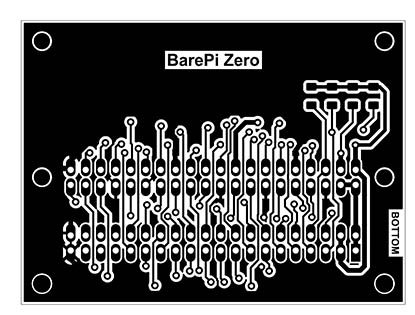
_www/img/BarePi_Zero_bottom_m.jpg
