Panda381/BarePi/Zero/BarePi_Zero_diagram.png

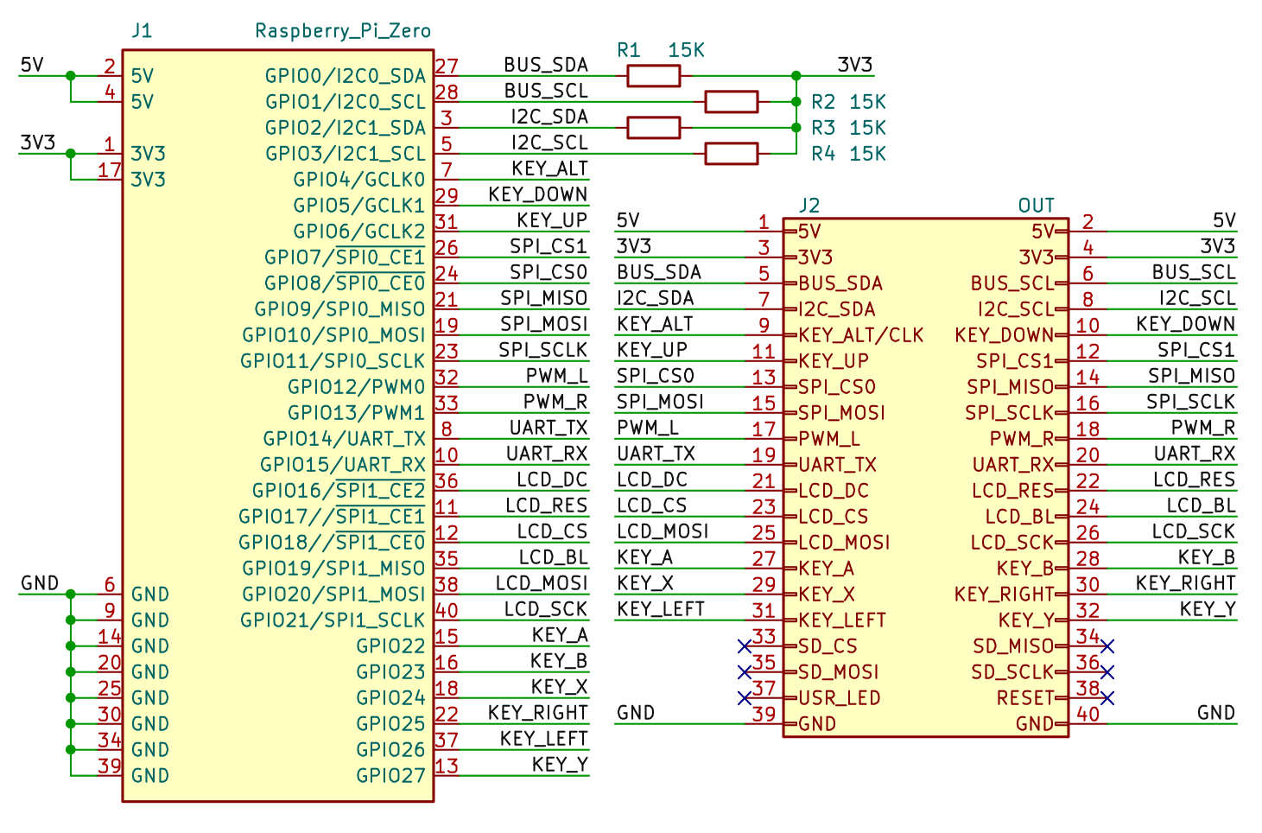
_www/img/BarePi_Zero_diagram.png
