Panda381/BarePi/_www/img/BarePi_Zero_label_m.jpg

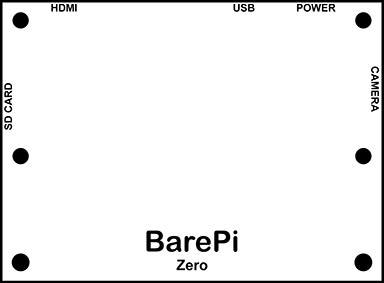
_www/img/BarePi_Zero_label_m.jpg
