Panda381/BarePi/_www/img/BarePi_Zero_mounting_m.jpg

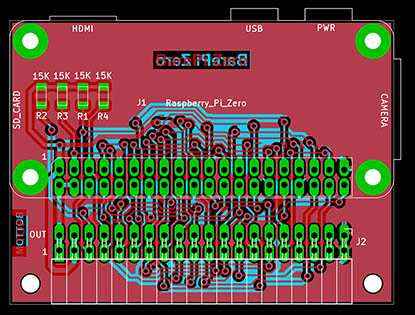
_www/img/BarePi_Zero_mounting_m.jpg
