Panda381/BarePi/_www/img/BarePi_Zero_top_m.jpg

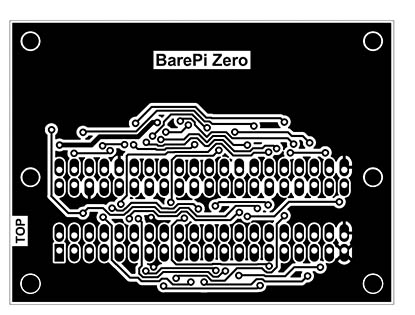
_www/img/BarePi_Zero_top_m.jpg
