Panda381/BarePi/_www/img/BarePi_ZeroTiny2.jpg

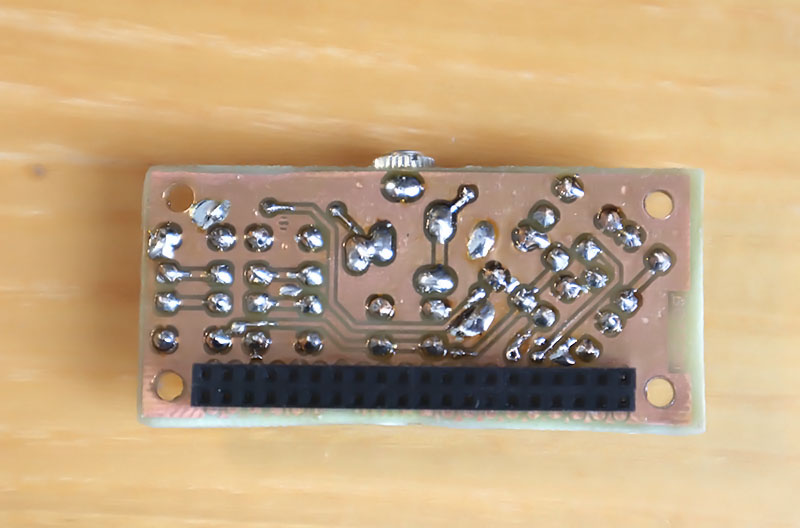
_www/img/BarePi_ZeroTiny2.jpg
