Panda381/BarePi/_www/img/BarePi_ZeroTiny3.jpg

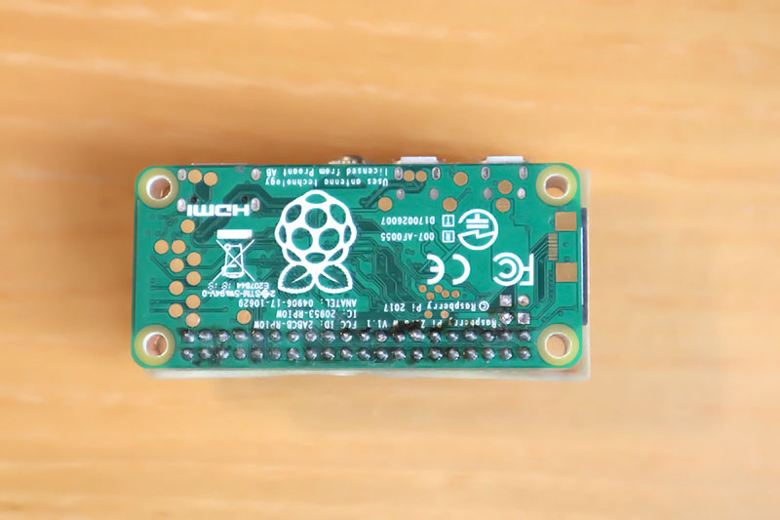
_www/img/BarePi_ZeroTiny3.jpg
