Panda381/BarePi/_www/img/MegaTinyJoypad_diagram.jpg

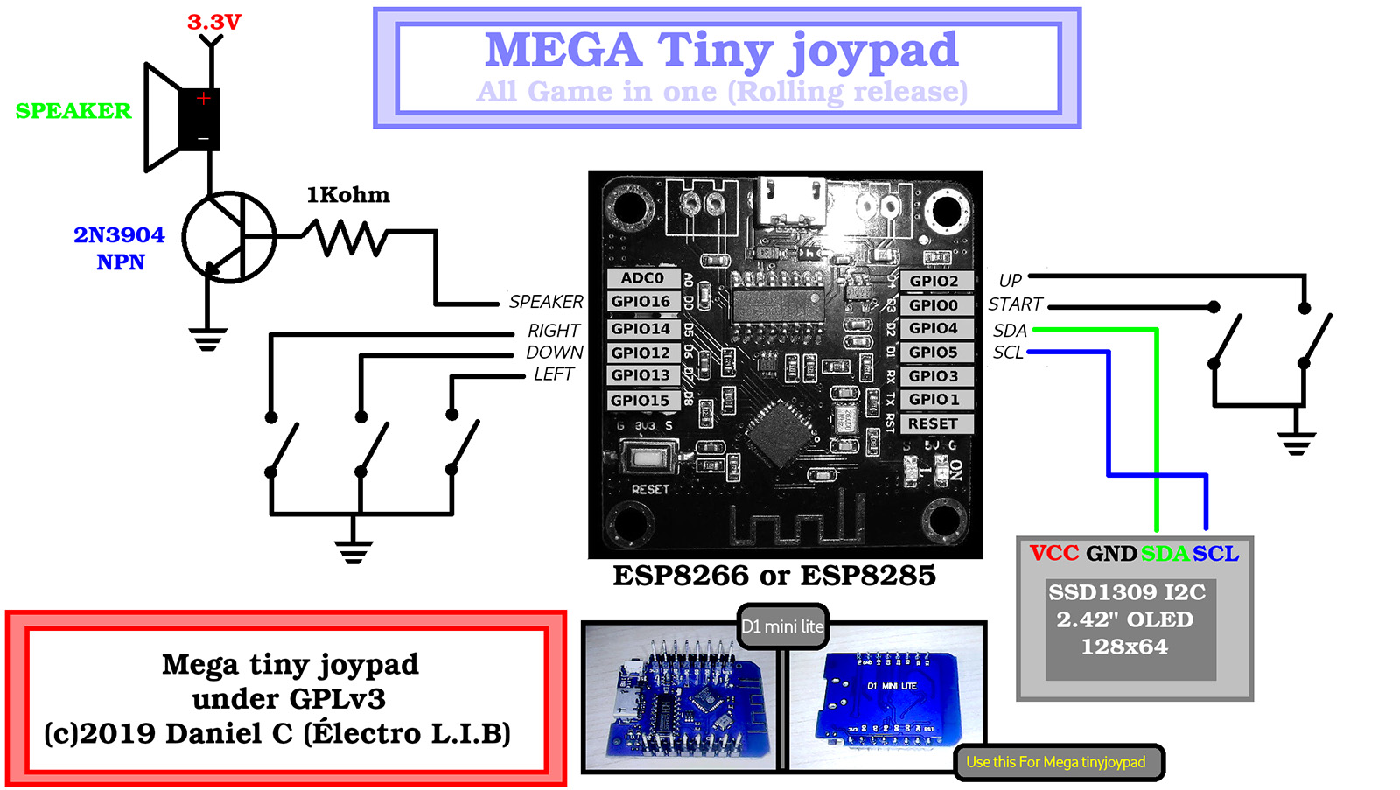
_www/img/MegaTinyJoypad_diagram.jpg
