Panda381/BarePi/_www/img/PicoPad_diagram_m.jpg

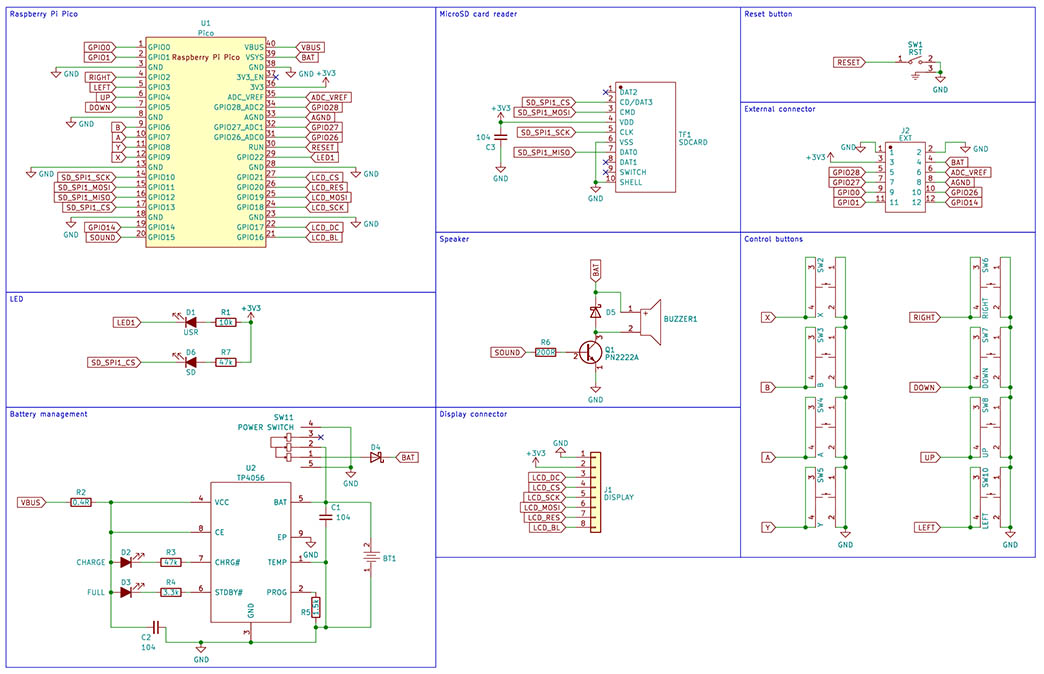
_www/img/PicoPad_diagram_m.jpg
