Panda381/BarePi/_www/img/PidiMet_diagram.png

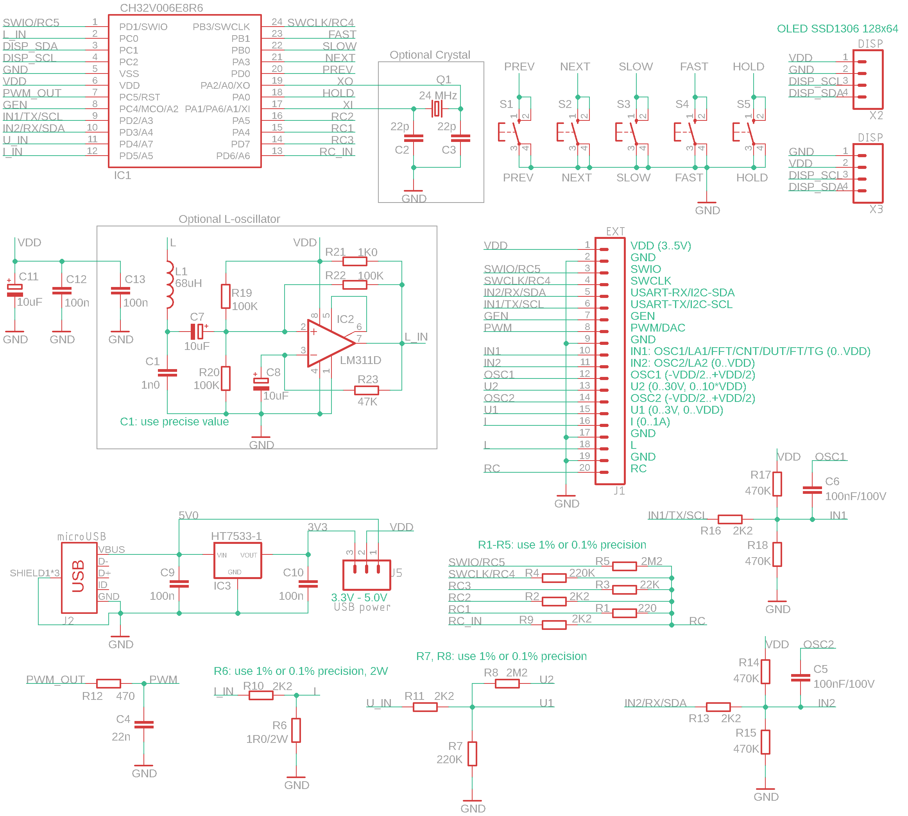
_www/img/PidiMet_diagram.png
