Panda381/BarePi/_www/img/TinyJoypad_diagram_m.jpg

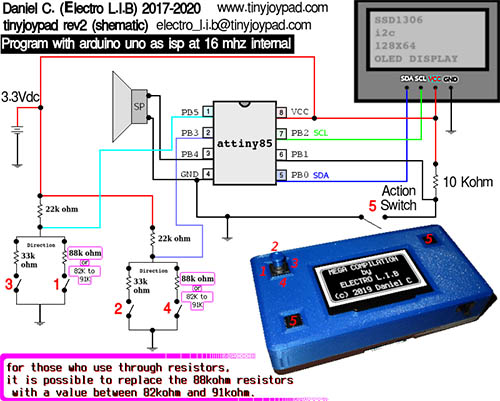
_www/img/TinyJoypad_diagram_m.jpg
