Panda381/BarePi/_www/img/TweetyBoy_diagram_m.jpg

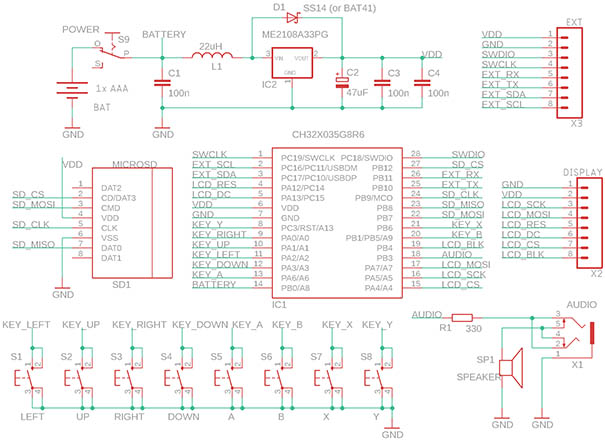
_www/img/TweetyBoy_diagram_m.jpg
