Panda381/BarePi/_www/img/BarePi_TestLed2.jpg

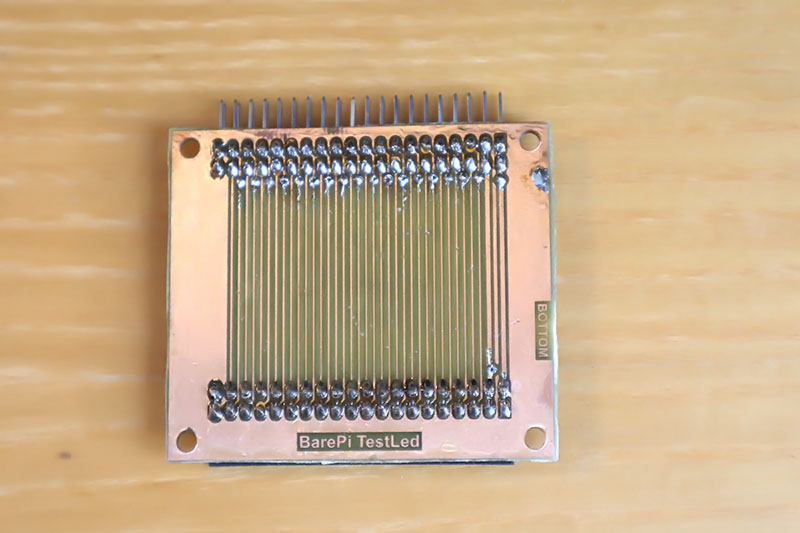
_www/img/BarePi_TestLed2.jpg
