Panda381/BarePi/_www/img/BarePi_TestLed3.jpg

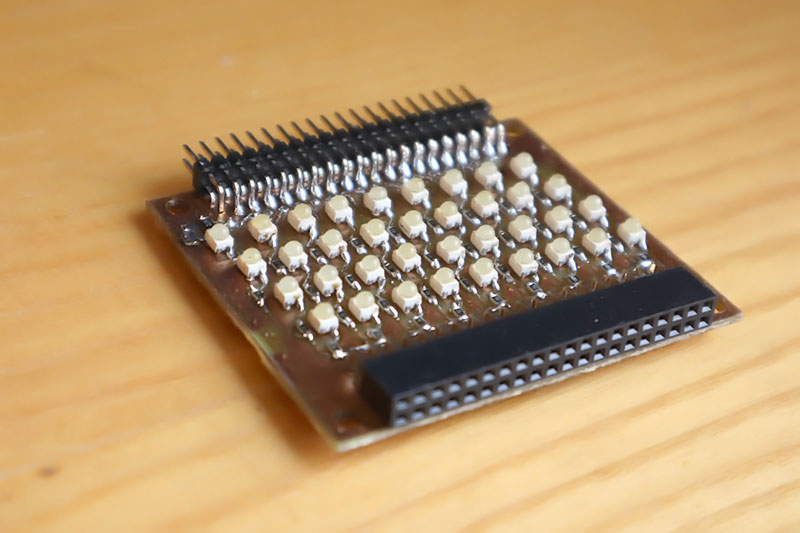
_www/img/BarePi_TestLed3.jpg
