Panda381/BarePi/TestLed/BarePi_TestLed_diagram.png

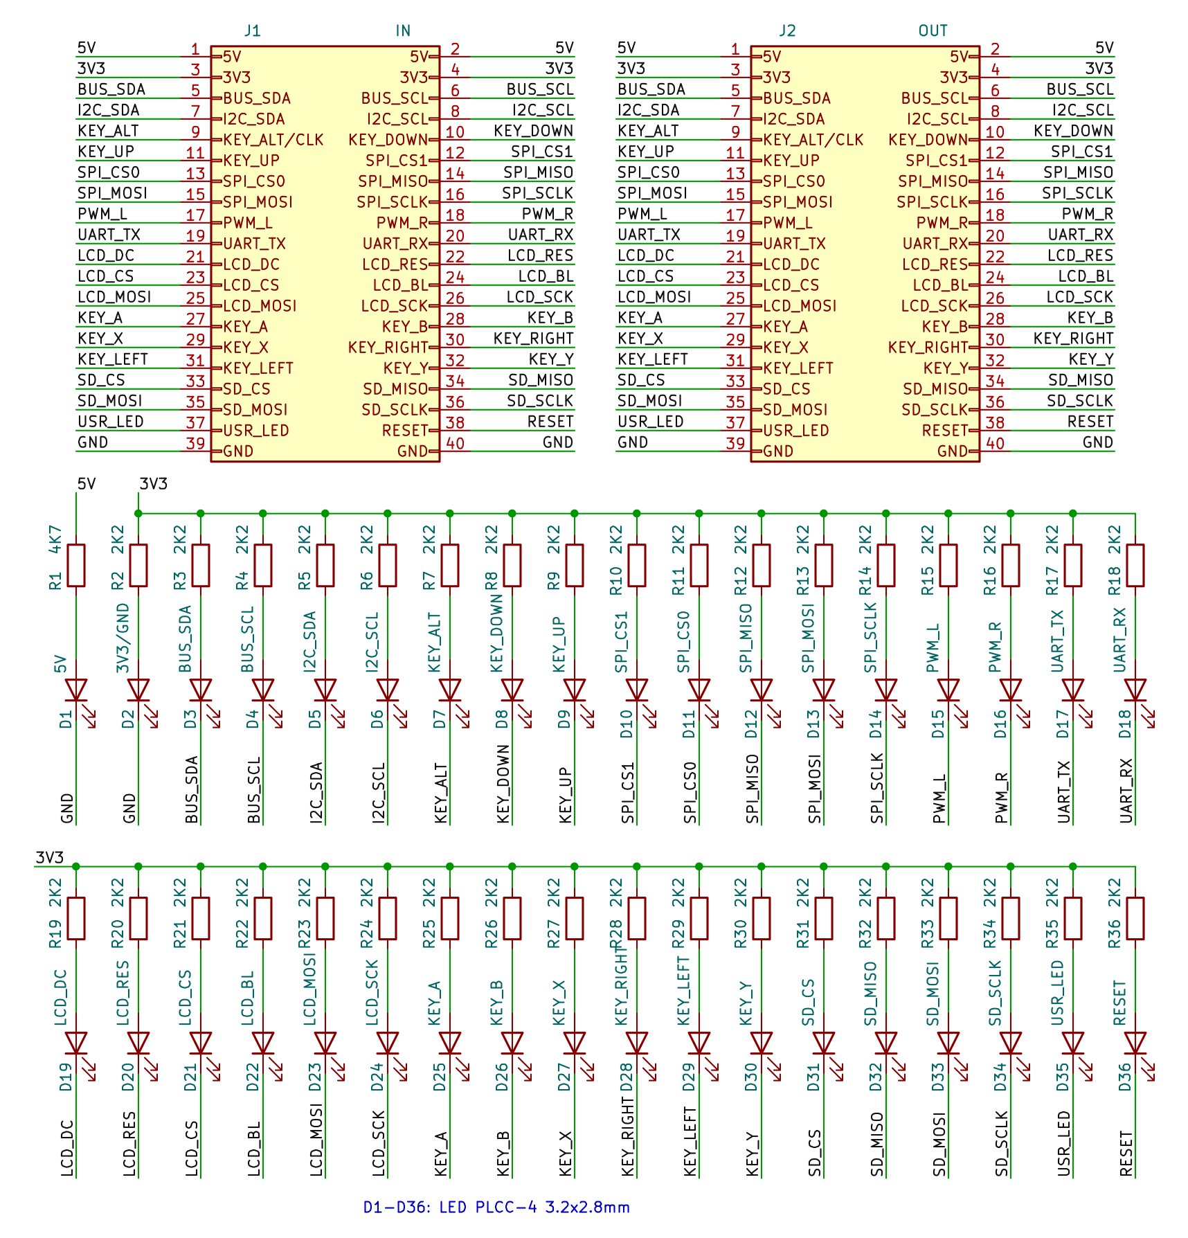
_www/img/BarePi_TestLed_diagram.png
