Panda381/BarePi/TestLed/BarePi_TestLed_label.png

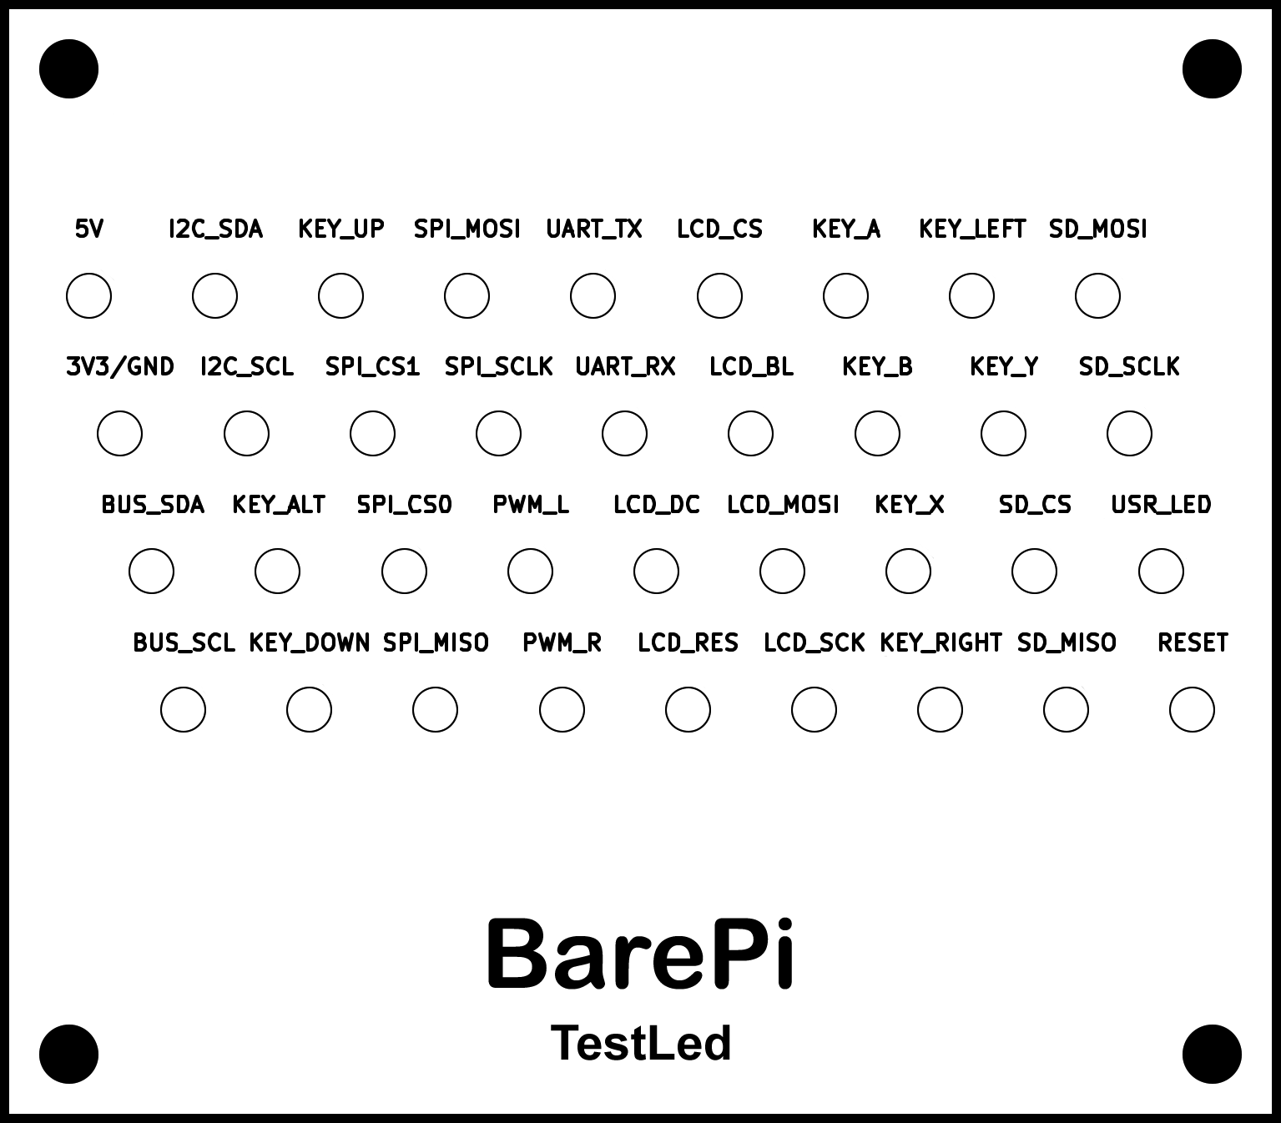
_www/img/BarePi_TestLed_label.png
