Panda381/BarePi/_www/img/BarePi_TestLed_label_m.jpg

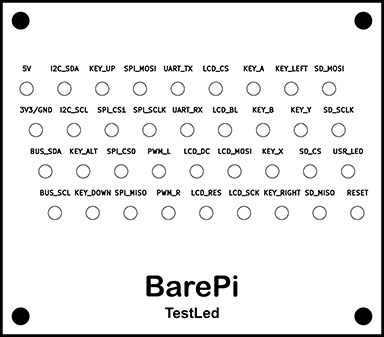
_www/img/BarePi_TestLed_label_m.jpg
