Panda381/BarePi/TestLed/BarePi_TestLed_mounting.jpg

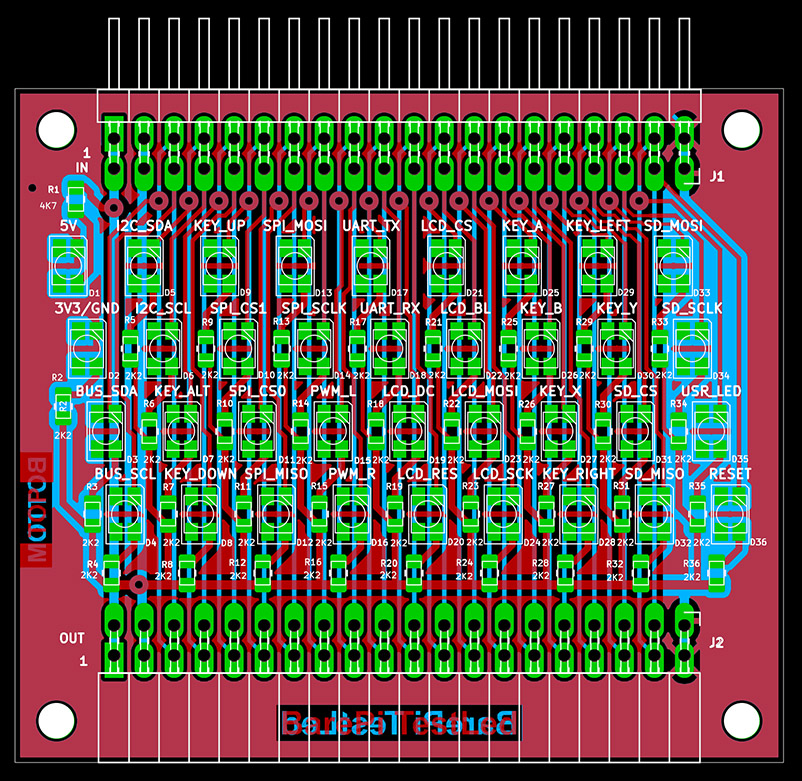
_www/img/BarePi_TestLed_mounting.jpg
