Panda381/BarePi/_www/img/BarePi_TestLed_mounting_m.jpg

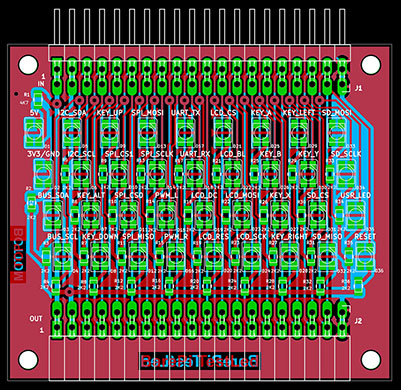
_www/img/BarePi_TestLed_mounting_m.jpg
