Panda381/BarePi/TestLed/BarePi_TestLed_top.png

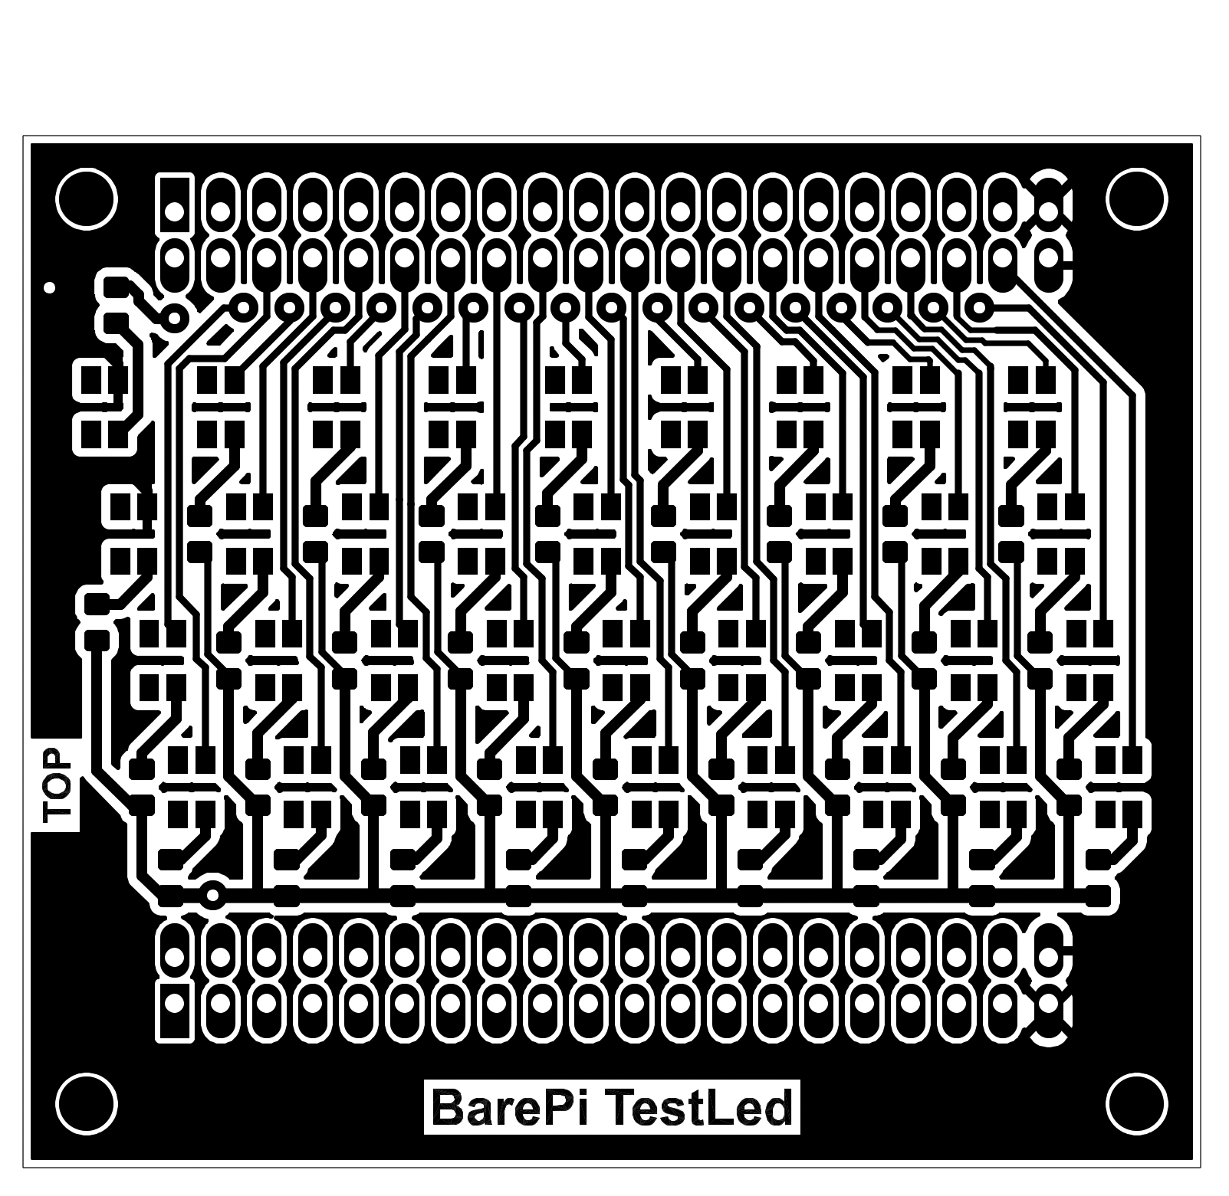
_www/img/BarePi_TestLed_top.png
