Panda381/BarePi/_www/img/BarePi_TestLed_top_m.jpg

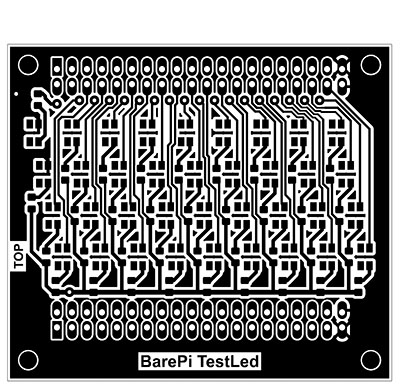
_www/img/BarePi_TestLed_top_m.jpg
