Panda381/BarePi/TestLed/BarePi_TestLed_doc.png

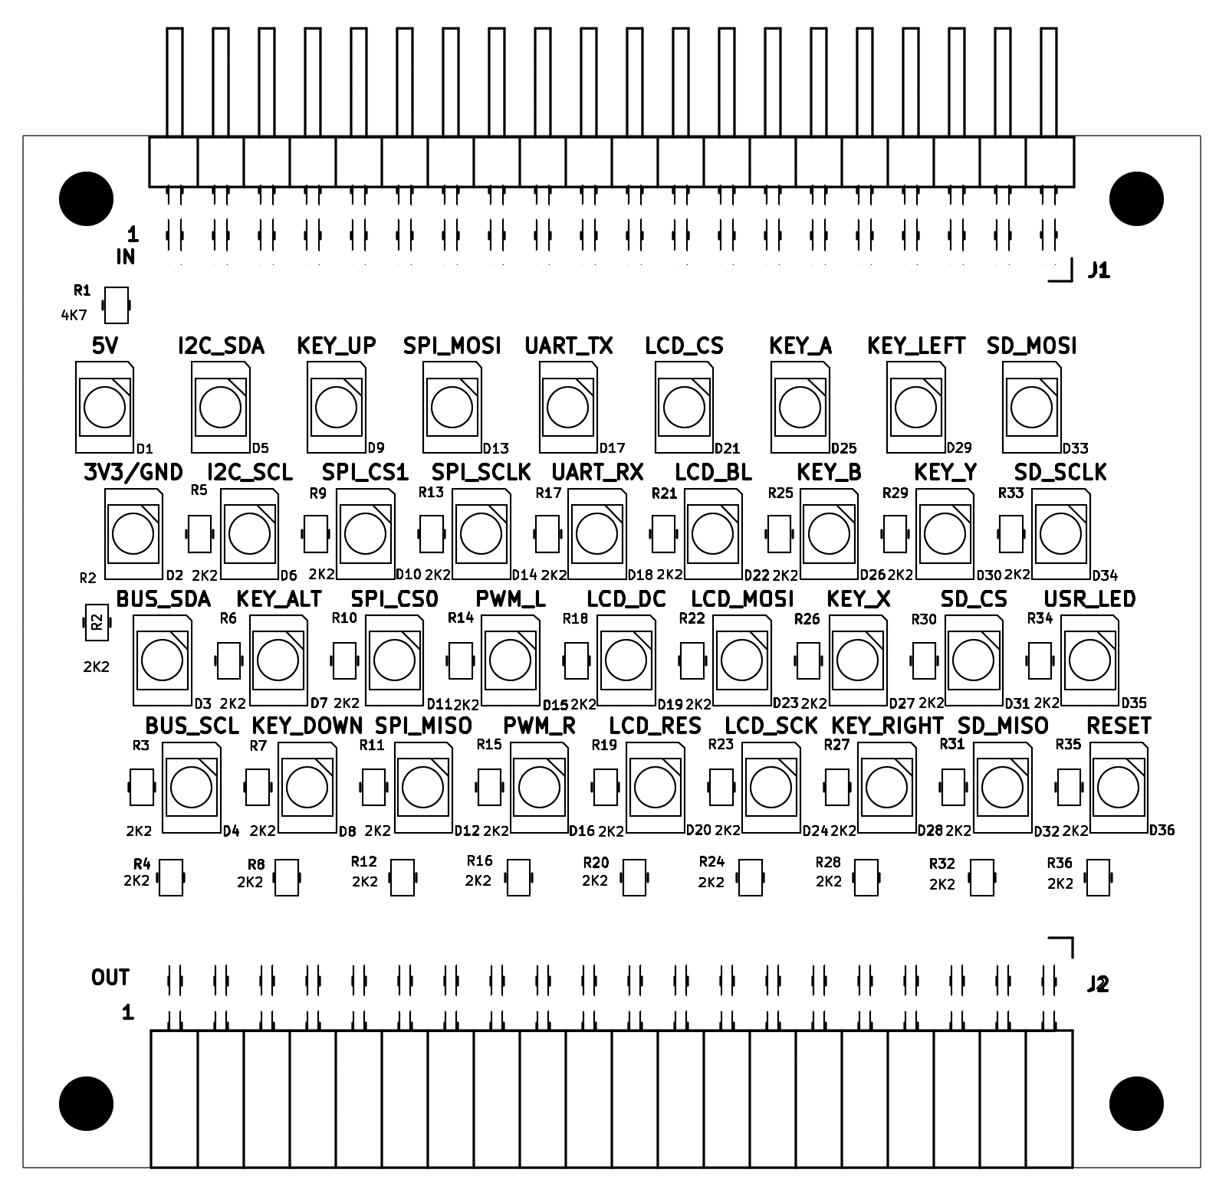
TestLed/BarePi_TestLed_doc.png
