Panda381/BarePi/TestLed/BarePi_TestLed_pads.png

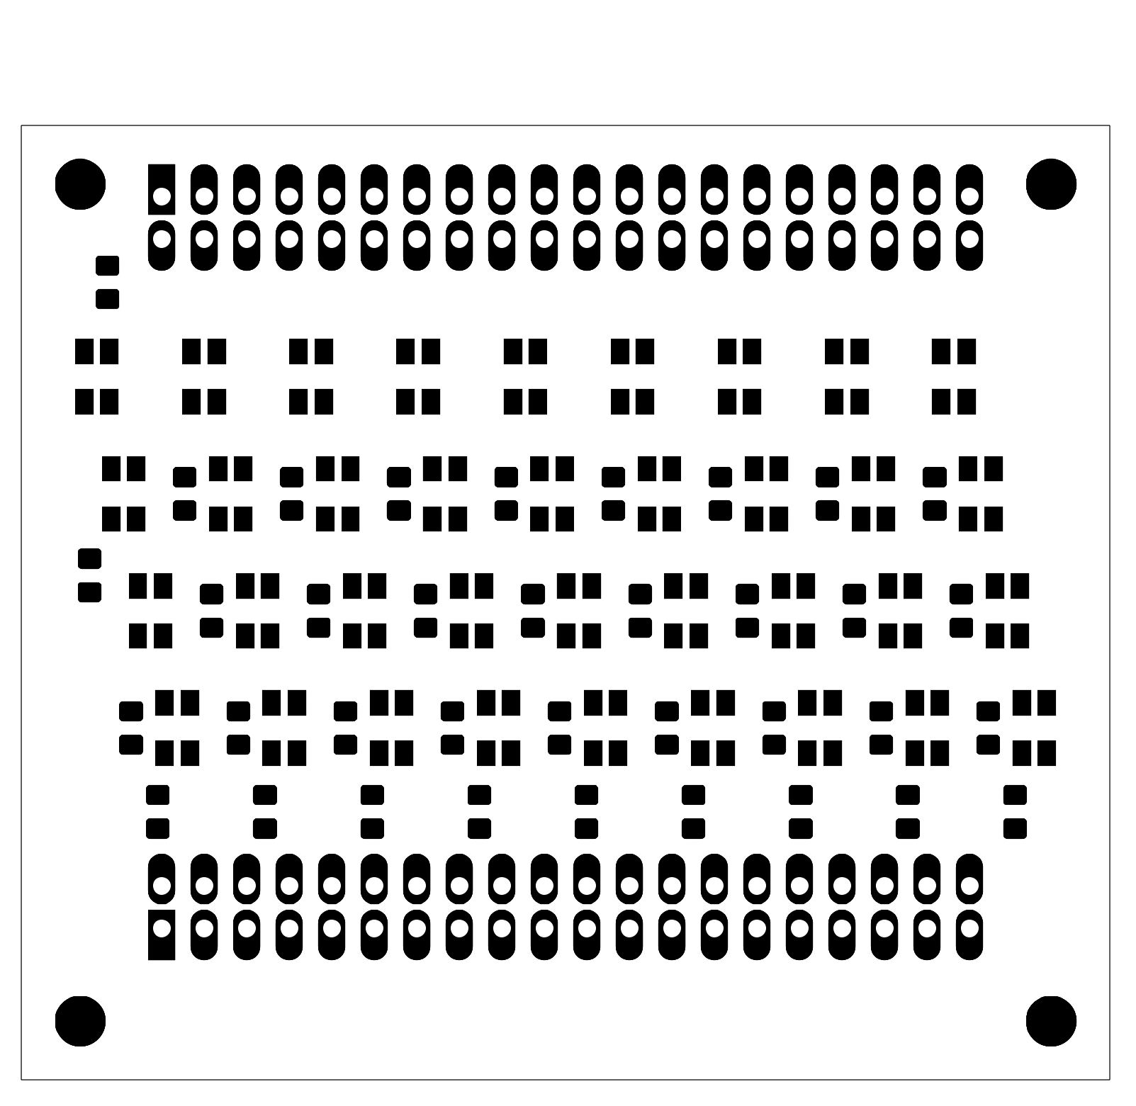
TestLed/BarePi_TestLed_pads.png
