Panda381/BarePi/PicoPadHSTX/KiCAD/BarePi_PicoPadHSTX.kicad_pcb

## KiCad design PicoPadHSTX/KiCAD/BarePi_PicoPadHSTX.kicad_pcb (2026-07-18)

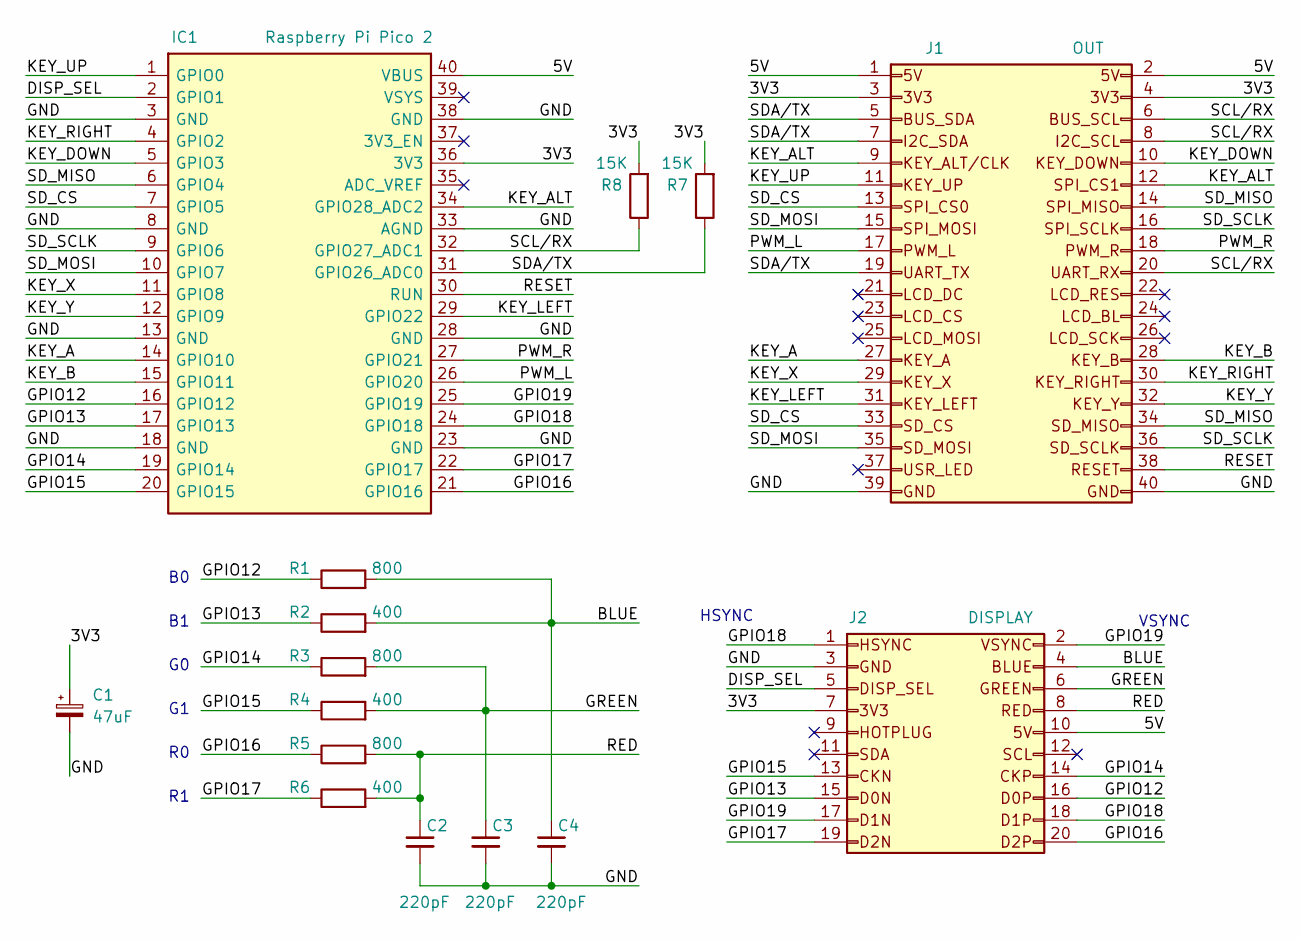
[picture p242: schematic BarePi_PicoPadHSTX.kicad_sch]

Parts:
C1: 47uF; CP_EIA-3216-18_Kemet-A_HandSolder
C2, C3, C4: 220pF; C_1206_3216Metric_Pad1.33x1.80mm_HandSolder
IC1: Raspberry Pi Pico 2; Raspberry_Pi_Pico_Common_Unspecified
J1: OUT; Raspberry_OUT_PinSocket_2x20_P2.54mm_Horizontal
J2: DISPLAY; Raspberry_OUT_PinSocket_2x10_P2.54mm_Horizontal
R1, R3, R5: 800; R_0805_2012Metric_Pad1.20x1.40mm_HandSolder
R2, R4, R6: 400; R_0805_2012Metric_Pad1.20x1.40mm_HandSolder
R7, R8: 15K; R_1206_3216Metric_Pad1.30x1.75mm_HandSolder

Connections:
/3V3: C1.1, IC1.36 (3V3), J1.3, J1.4, J2.7, R7.2, R8.2
/5V: IC1.40 (VBUS), J1.1, J1.2, J2.10
/BLUE: C4.1, J2.4, R1.2, R2.2
/DISP_SEL: IC1.2 (GPIO1), J2.5
/GND: C1.2, C2.2, C3.2, C4.2, IC1.3 (GND), IC1.8 (GND), IC1.13 (GND), IC1.18 (GND), IC1.23 (GND), IC1.28 (GND), IC1.33 (AGND), IC1.38 (GND), J1.39, J1.40, J2.3
/GPIO12: IC1.16 (GPIO12), J2.16, R1.1
/GPIO13: IC1.17 (GPIO13), J2.15, R2.1
/GPIO14: IC1.19 (GPIO14), J2.14, R3.1
/GPIO15: IC1.20 (GPIO15), J2.13, R4.1
/GPIO16: IC1.21 (GPIO16), J2.20, R5.1
/GPIO17: IC1.22 (GPIO17), J2.19, R6.1
/GPIO18: IC1.24 (GPIO18), J2.1, J2.18
/GPIO19: IC1.25 (GPIO19), J2.2, J2.17
/GREEN: C3.1, J2.6, R3.2, R4.2
/KEY_A: IC1.14 (GPIO10), J1.27
/KEY_ALT: IC1.34 (GPIO28_ADC2), J1.9, J1.12
/KEY_B: IC1.15 (GPIO11), J1.28
/KEY_DOWN: IC1.5 (GPIO3), J1.10
/KEY_LEFT: IC1.29 (GPIO22), J1.31
/KEY_RIGHT: IC1.4 (GPIO2), J1.30
/KEY_UP: IC1.1 (GPIO0), J1.11
/KEY_X: IC1.11 (GPIO8), J1.29
/KEY_Y: IC1.12 (GPIO9), J1.32
/PWM_L: IC1.26 (GPIO20), J1.17
/PWM_R: IC1.27 (GPIO21), J1.18
/RED: C2.1, J2.8, R5.2, R6.2
/RESET: IC1.30 (RUN), J1.38
/SCL/RX: IC1.32 (GPIO27_ADC1), J1.6, J1.8, J1.20, R8.1
/SDA/TX: IC1.31 (GPIO26_ADC0), J1.5, J1.7, J1.19, R7.1
/SD_CS: IC1.7 (GPIO5), J1.13, J1.33
/SD_MISO: IC1.6 (GPIO4), J1.14, J1.34
/SD_MOSI: IC1.10 (GPIO7), J1.15, J1.35
/SD_SCLK: IC1.9 (GPIO6), J1.16, J1.36

Notes on the sheet:
VSYNC
HSYNC

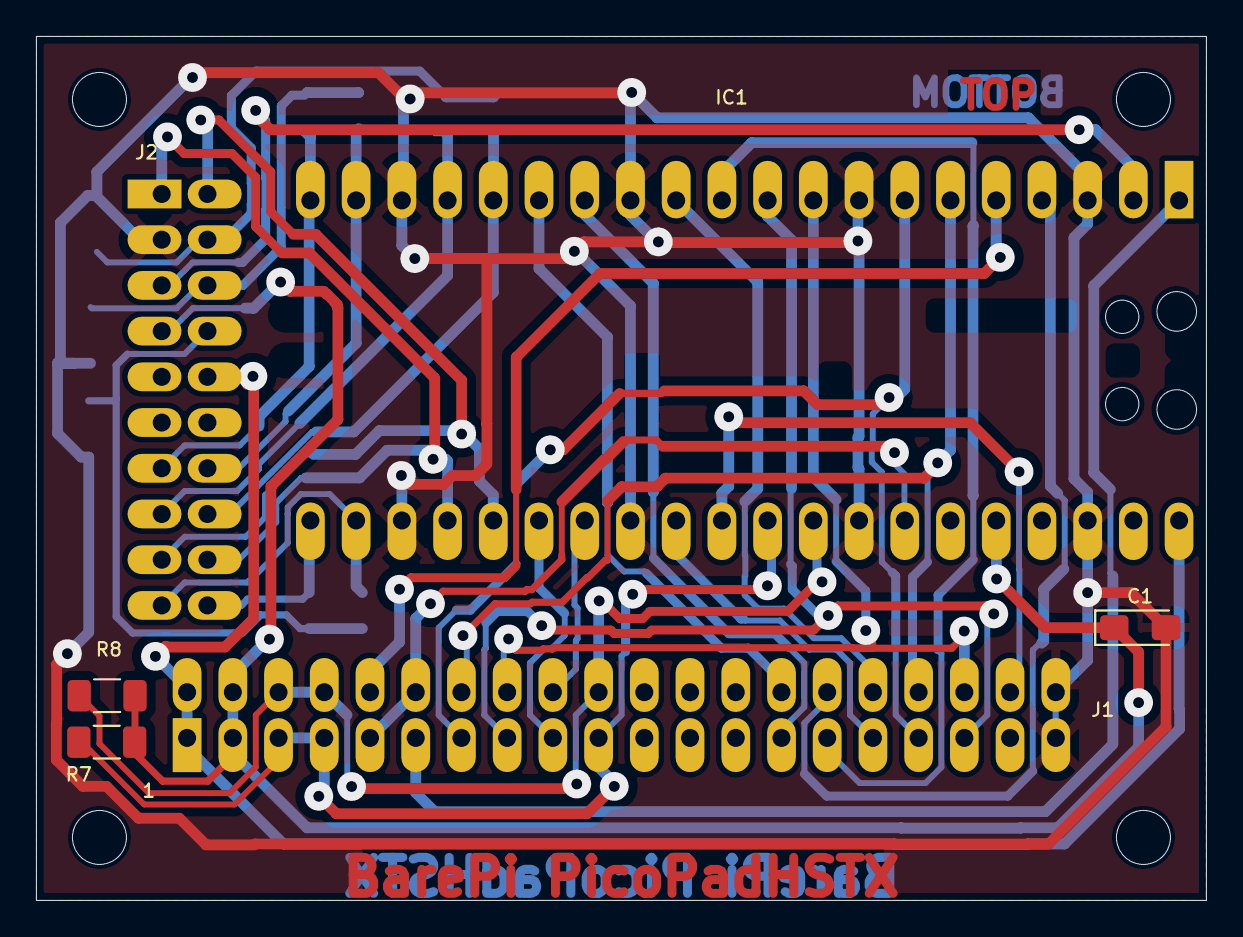
[picture p243: board BarePi_PicoPadHSTX.kicad_pcb from above]

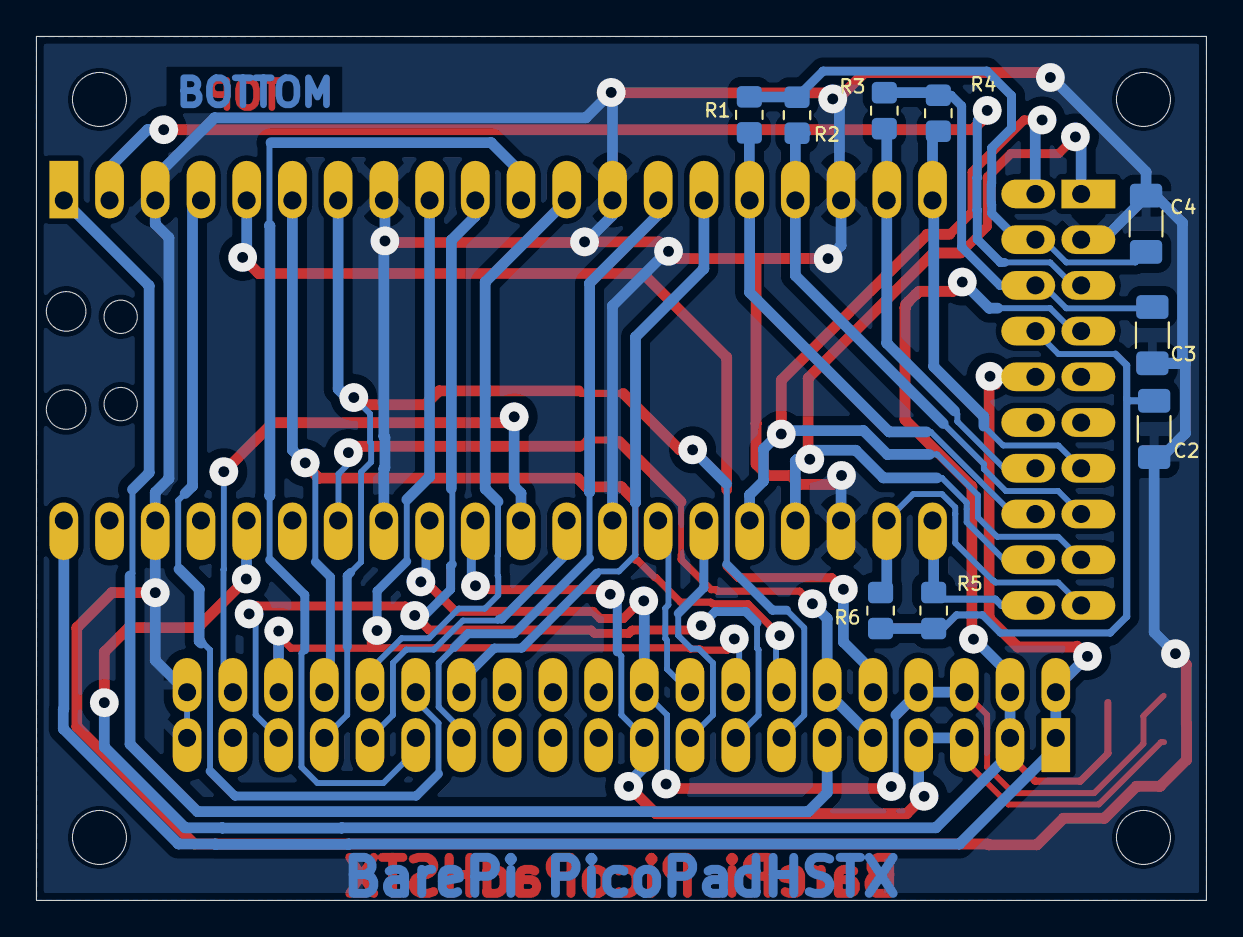
[picture p244: board BarePi_PicoPadHSTX.kicad_pcb from below]

Board: 2 copper layers, 65.0 x 48.0 mm, 15 parts (9 on the bottom side), 33 nets.
