Panda381/BarePi/MegaTinyJoypad/KiCAD/BarePi_MegaTinyJoypad.kicad_pcb

## KiCad design MegaTinyJoypad/KiCAD/BarePi_MegaTinyJoypad.kicad_pcb (2026-07-18)

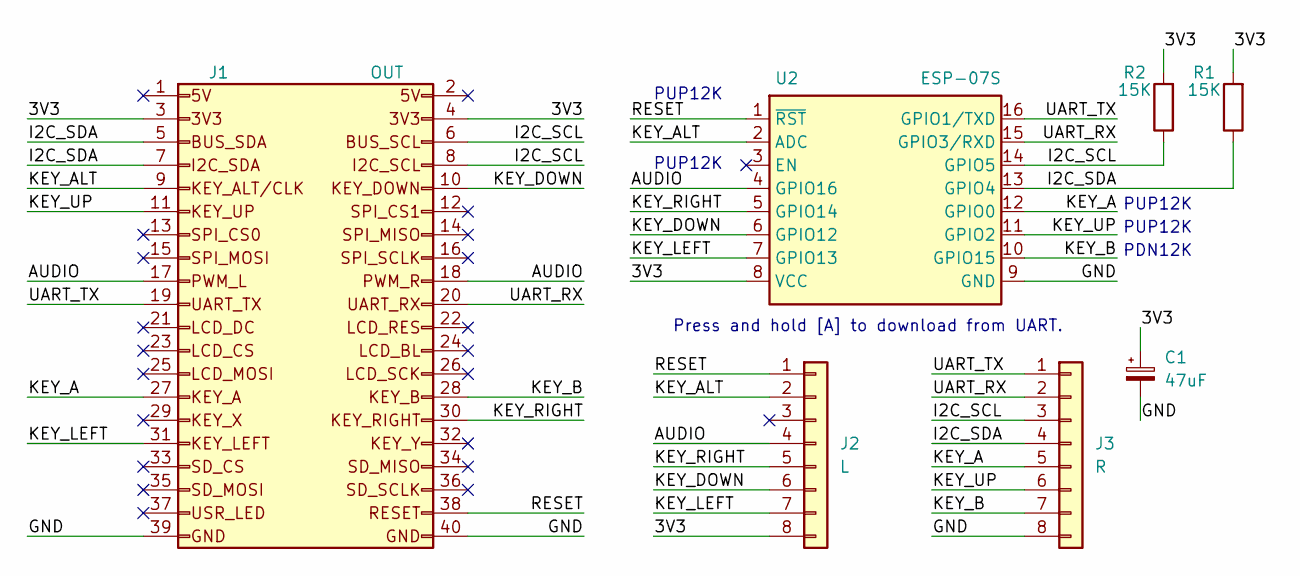
[picture p245: schematic BarePi_MegaTinyJoypad.kicad_sch]

Parts:
C1: 47uF; CP_EIA-3216-18_Kemet-A_HandSolder
J1: OUT; Raspberry_OUT_PinSocket_2x20_P2.54mm_Horizontal
J2: L; Raspberry_PinSocket_1x08_P2.54mm_Vertical
J3: R; Raspberry_PinSocket_1x08_P2.54mm_Vertical
R1, R2: 15K; R_1206_3216Metric_Pad1.30x1.75mm_HandSolder
U2: ESP-07S; Raspberry_ESP-07

Connections:
/3V3: C1.1, J1.3, J1.4, J2.8, R1.2, R2.2, U2.8 (VCC)
/AUDIO: J1.17, J1.18, J2.4, U2.4 (GPIO16)
/GND: C1.2, J1.39, J1.40, J3.8, U2.9 (GND)
/I2C_SCL: J1.6, J1.8, J3.3, R2.1, U2.14 (GPIO5)
/I2C_SDA: J1.5, J1.7, J3.4, R1.1, U2.13 (GPIO4)
/KEY_A: J1.27, J3.5, U2.12 (GPIO0)
/KEY_ALT: J1.9, J2.2, U2.2 (ADC)
/KEY_B: J1.28, J3.7, U2.10 (GPIO15)
/KEY_DOWN: J1.10, J2.6, U2.6 (GPIO12)
/KEY_LEFT: J1.31, J2.7, U2.7 (GPIO13)
/KEY_RIGHT: J1.30, J2.5, U2.5 (GPIO14)
/KEY_UP: J1.11, J3.6, U2.11 (GPIO2)
/RESET: J1.38, J2.1, U2.1 (~RST)
/UART_RX: J1.20, J3.2, U2.15 (GPIO3/RXD)
/UART_TX: J1.19, J3.1, U2.16 (GPIO1/TXD)

Notes on the sheet:
PUP12K
PDN12K
Press and hold [A] to download from UART.

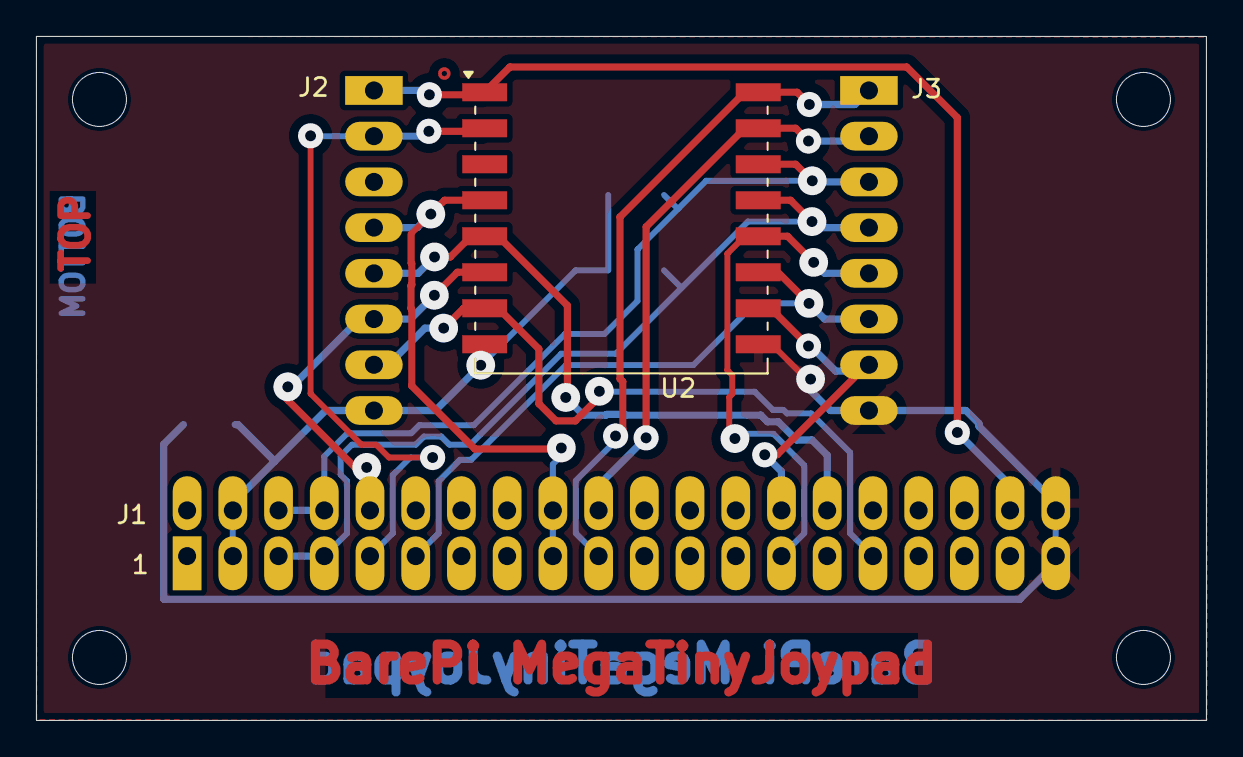
[picture p246: board BarePi_MegaTinyJoypad.kicad_pcb from above]

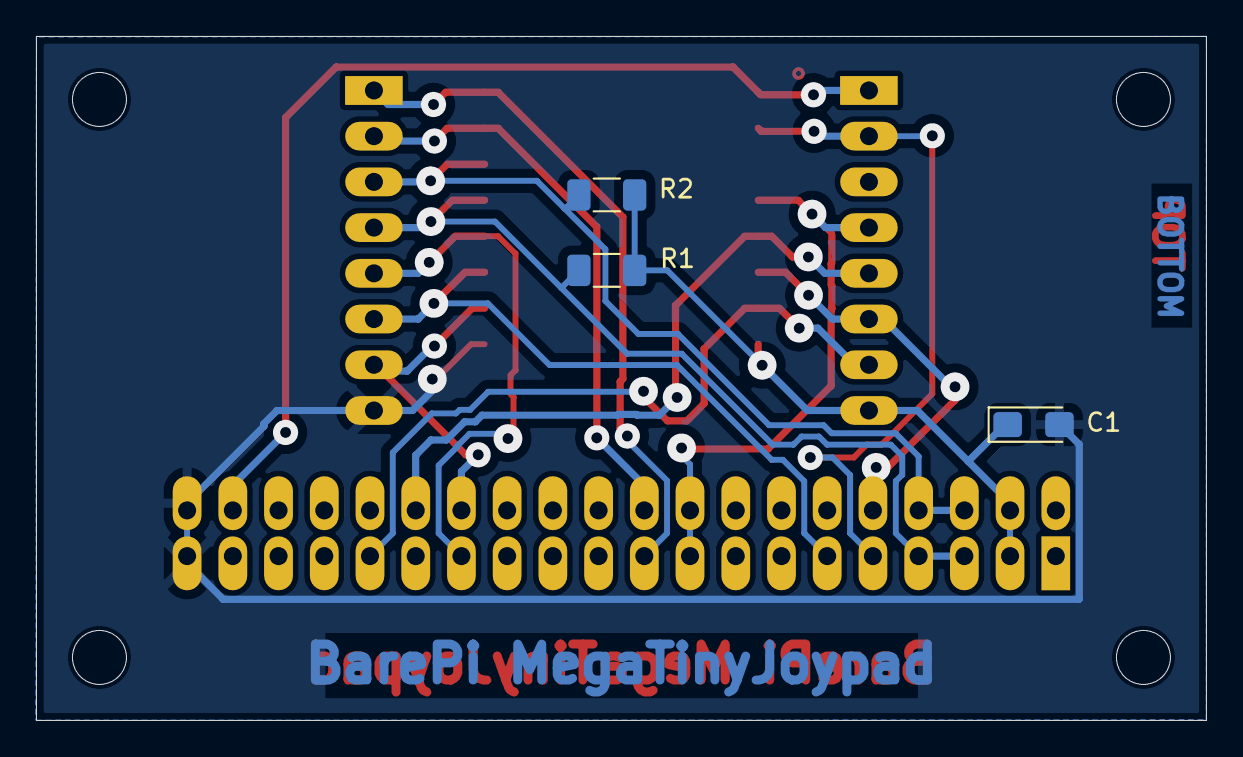
[picture p247: board BarePi_MegaTinyJoypad.kicad_pcb from below]

Board: 2 copper layers, 65.0 x 38.0 mm, 7 parts (3 on the bottom side), 15 nets.
