Panda381/BarePi/SumoPad/KiCAD/BarePi_SumoPad.kicad_pcb

## KiCad design SumoPad/KiCAD/BarePi_SumoPad.kicad_pcb (2026-07-18)

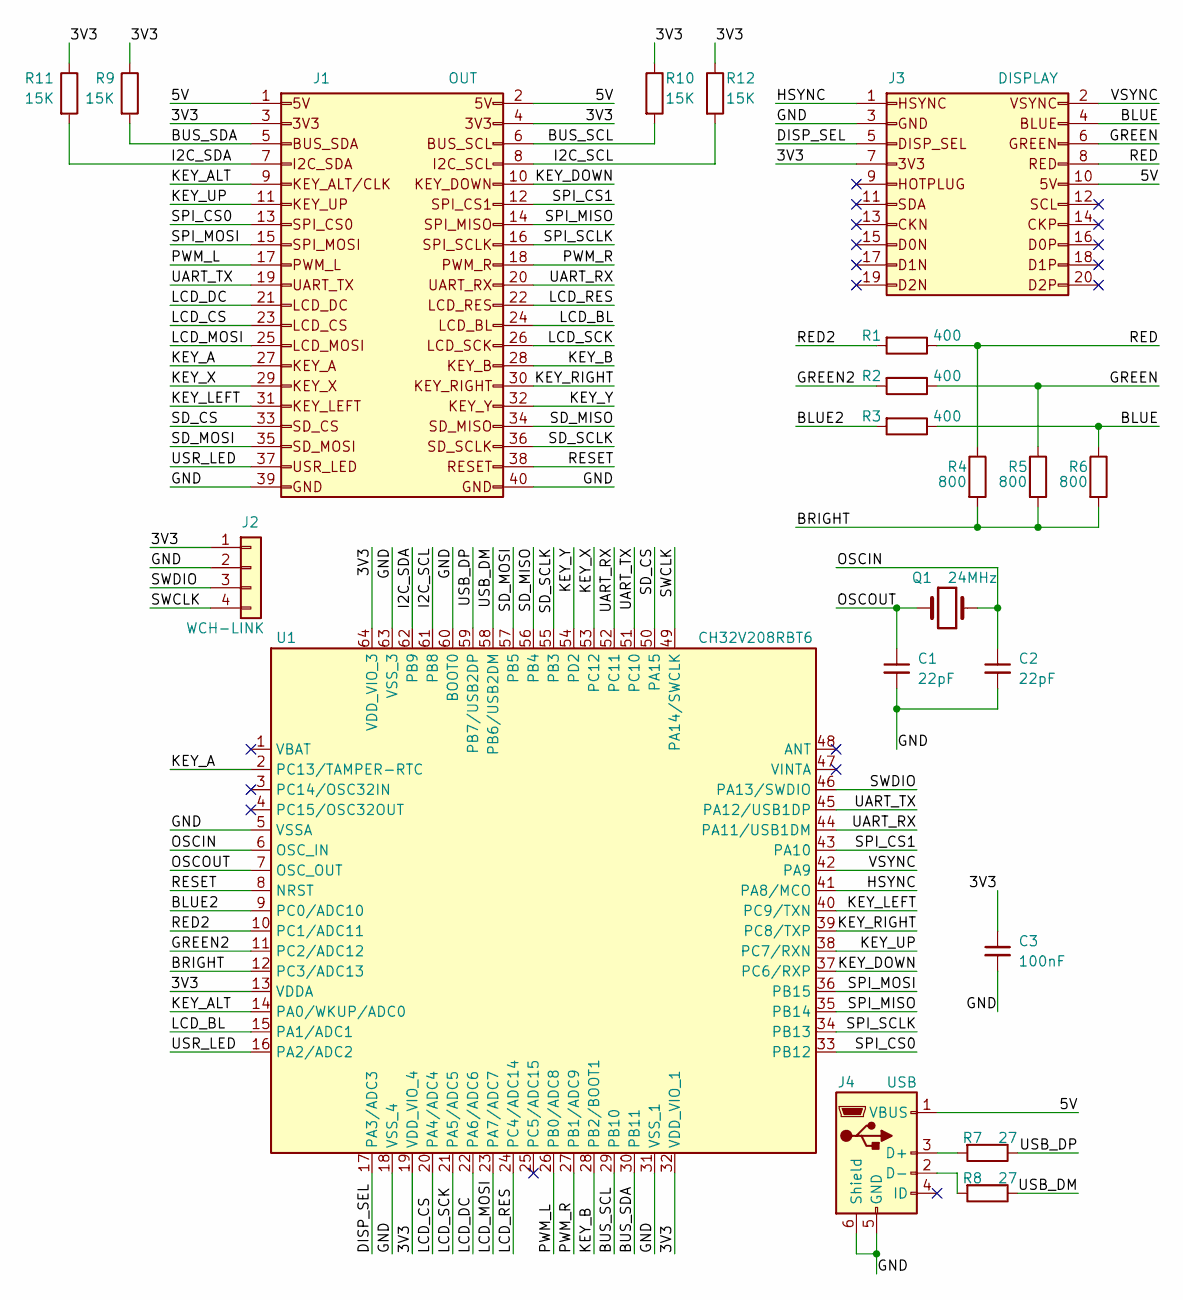
[picture p248: schematic BarePi_SumoPad.kicad_sch]

Parts:
C1, C2: 22pF; C_1206_3216Metric_Pad1.33x1.80mm_HandSolder
C3: 100nF; C_1206_3216Metric_Pad1.33x1.80mm_HandSolder
J1: OUT; Raspberry_OUT_PinSocket_2x20_P2.54mm_Horizontal
J2: WCH-LINK; Raspberry_PinHeader_1x04_P2.54mm_Horizontal
J3: DISPLAY; Raspberry_OUT_PinSocket_2x10_P2.54mm_Horizontal
J4: USB; Raspberry_USB_Micro-B_Amphenol_10104110_Horizontal
Q1: 24MHz; Raspberry_Crystal_HC49-4H_Vertical
R1, R2, R3: 400; R_0805_2012Metric_Pad1.20x1.40mm_HandSolder
R4, R5, R6: 800; R_0805_2012Metric_Pad1.20x1.40mm_HandSolder
R7, R8: 27; R_0805_2012Metric_Pad1.20x1.40mm_HandSolder
R9, R10, R11, R12: 15K; R_1206_3216Metric_Pad1.30x1.75mm_HandSolder
U1: CH32V208RBT6; Raspberry_LQFP-64_10x10mm_P0.5mm_adapter

Connections:
/3V3: C3.1, J1.3, J1.4, J2.1, J3.7, R9.1, R10.1, R11.1, R12.1, U1.13 (VDDA), U1.19 (VDD_VIO_4), U1.32 (VDD_VIO_1), U1.64 (VDD_VIO_3)
/5V: J1.1, J1.2, J3.10, J4.1 (VBUS)
/BLUE: J3.4, R3.1, R6.1
/BLUE2: R3.2, U1.9 (PC0/ADC10)
/BRIGHT: R4.2, R5.2, R6.2, U1.12 (PC3/ADC13)
/BUS_SCL: J1.6, R10.2, U1.29 (PB10)
/BUS_SDA: J1.5, R9.2, U1.30 (PB11)
/DISP_SEL: J3.5, U1.17 (PA3/ADC3)
/GND: C1.2, C2.2, C3.2, J1.39, J1.40, J2.2, J3.3, J4.5 (GND), J4.6 (Shield), U1.5 (VSSA), U1.18 (VSS_4), U1.31 (VSS_1), U1.60 (BOOT0), U1.63 (VSS_3)
/GREEN: J3.6, R2.1, R5.1
/GREEN2: R2.2, U1.11 (PC2/ADC12)
/HSYNC: J3.1, U1.41 (PA8/MCO)
/I2C_SCL: J1.8, R12.2, U1.61 (PB8)
/I2C_SDA: J1.7, R11.2, U1.62 (PB9)
/KEY_A: J1.27, U1.2 (PC13/TAMPER-RTC)
/KEY_ALT: J1.9, U1.14 (PA0/WKUP/ADC0)
/KEY_B: J1.28, U1.28 (PB2/BOOT1)
/KEY_DOWN: J1.10, U1.37 (PC6/RXP)
/KEY_LEFT: J1.31, U1.40 (PC9/TXN)
/KEY_RIGHT: J1.30, U1.39 (PC8/TXP)
/KEY_UP: J1.11, U1.38 (PC7/RXN)
/KEY_X: J1.29, U1.53 (PC12)
/KEY_Y: J1.32, U1.54 (PD2)
/LCD_BL: J1.24, U1.15 (PA1/ADC1)
/LCD_CS: J1.23, U1.20 (PA4/ADC4)
/LCD_DC: J1.21, U1.22 (PA6/ADC6)
/LCD_MOSI: J1.25, U1.23 (PA7/ADC7)
/LCD_RES: J1.22, U1.24 (PC4/ADC14)
/LCD_SCK: J1.26, U1.21 (PA5/ADC5)
/OSCIN: C2.1, Q1.2, U1.6 (OSC_IN)
/OSCOUT: C1.1, Q1.1, U1.7 (OSC_OUT)
/PWM_L: J1.17, U1.26 (PB0/ADC8)
/PWM_R: J1.18, U1.27 (PB1/ADC9)
/RED: J3.8, R1.1, R4.1
/RED2: R1.2, U1.10 (PC1/ADC11)
/RESET: J1.38, U1.8 (NRST)
/SD_CS: J1.33, U1.50 (PA15)
/SD_MISO: J1.34, U1.56 (PB4)
/SD_MOSI: J1.35, U1.57 (PB5)
/SD_SCLK: J1.36, U1.55 (PB3)
/SPI_CS0: J1.13, U1.33 (PB12)
/SPI_CS1: J1.12, U1.43 (PA10)
/SPI_MISO: J1.14, U1.35 (PB14)
/SPI_MOSI: J1.15, U1.36 (PB15)
/SPI_SCLK: J1.16, U1.34 (PB13)
/SWCLK: J2.4, U1.49 (PA14/SWCLK)
/SWDIO: J2.3, U1.46 (PA13/SWDIO)
/UART_RX: J1.20, U1.44 (PA11/USB1DM), U1.52 (PC11)
/UART_TX: J1.19, U1.45 (PA12/USB1DP), U1.51 (PC10)
/USB_DM: R8.1, U1.58 (PB6/USB2DM)
/USB_DP: R7.1, U1.59 (PB7/USB2DP)
/USR_LED: J1.37, U1.16 (PA2/ADC2)
/VSYNC: J3.2, U1.42 (PA9)
unnamed: J4.3 (D+), R7.2
unnamed: J4.2 (D-), R8.2

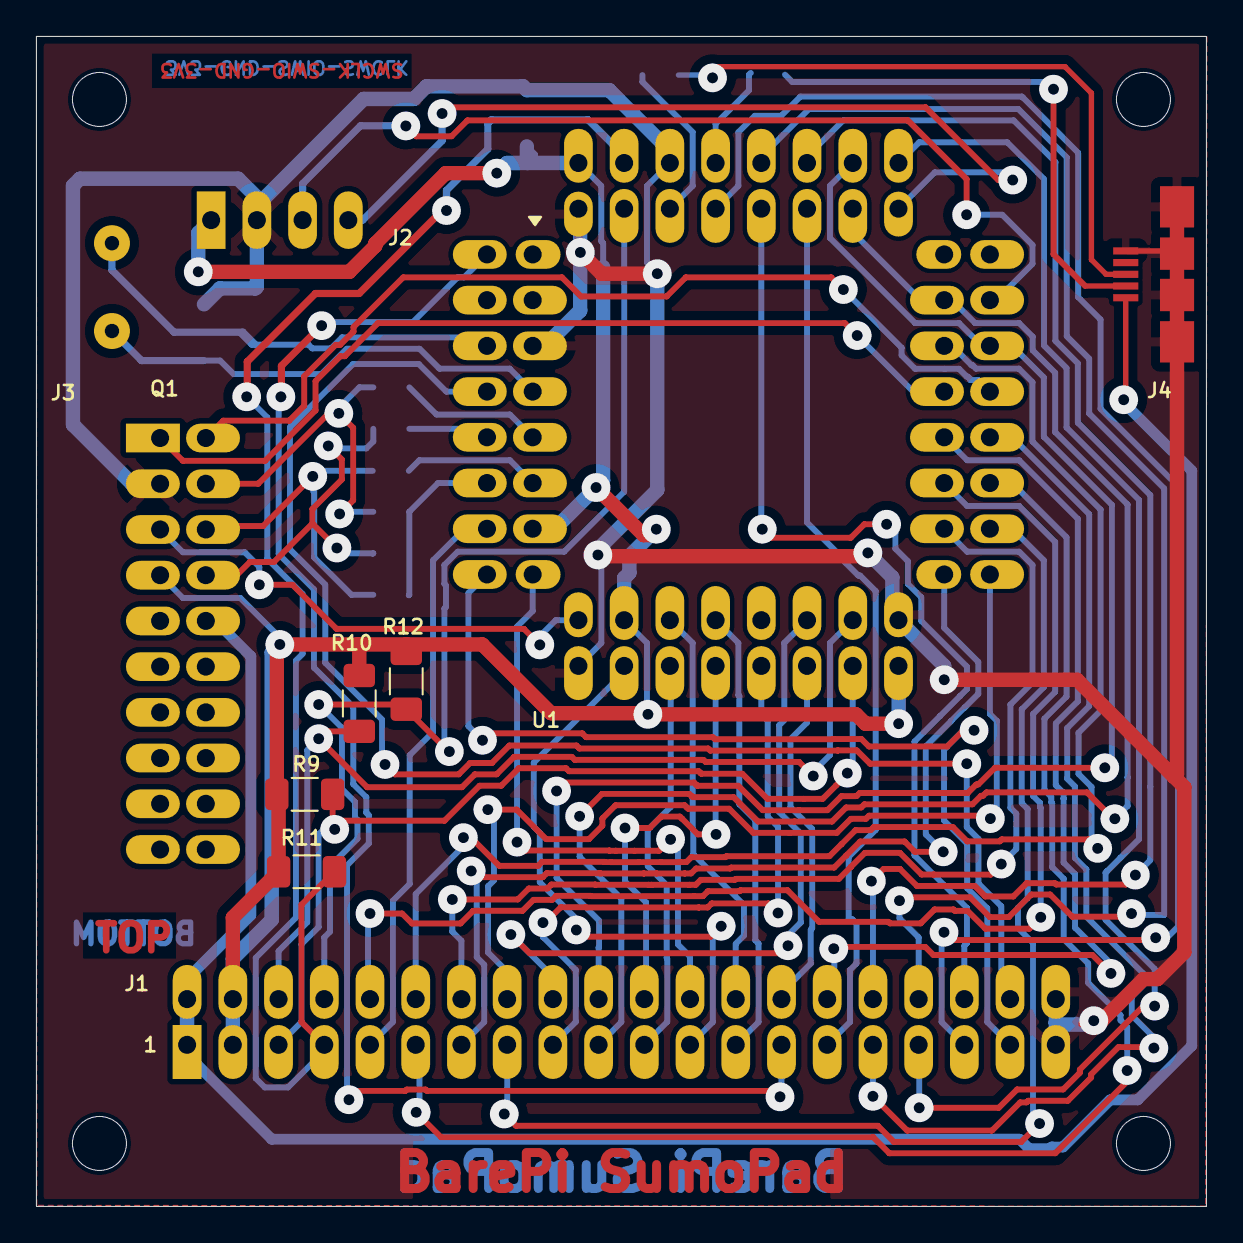
[picture p249: board BarePi_SumoPad.kicad_pcb from above]

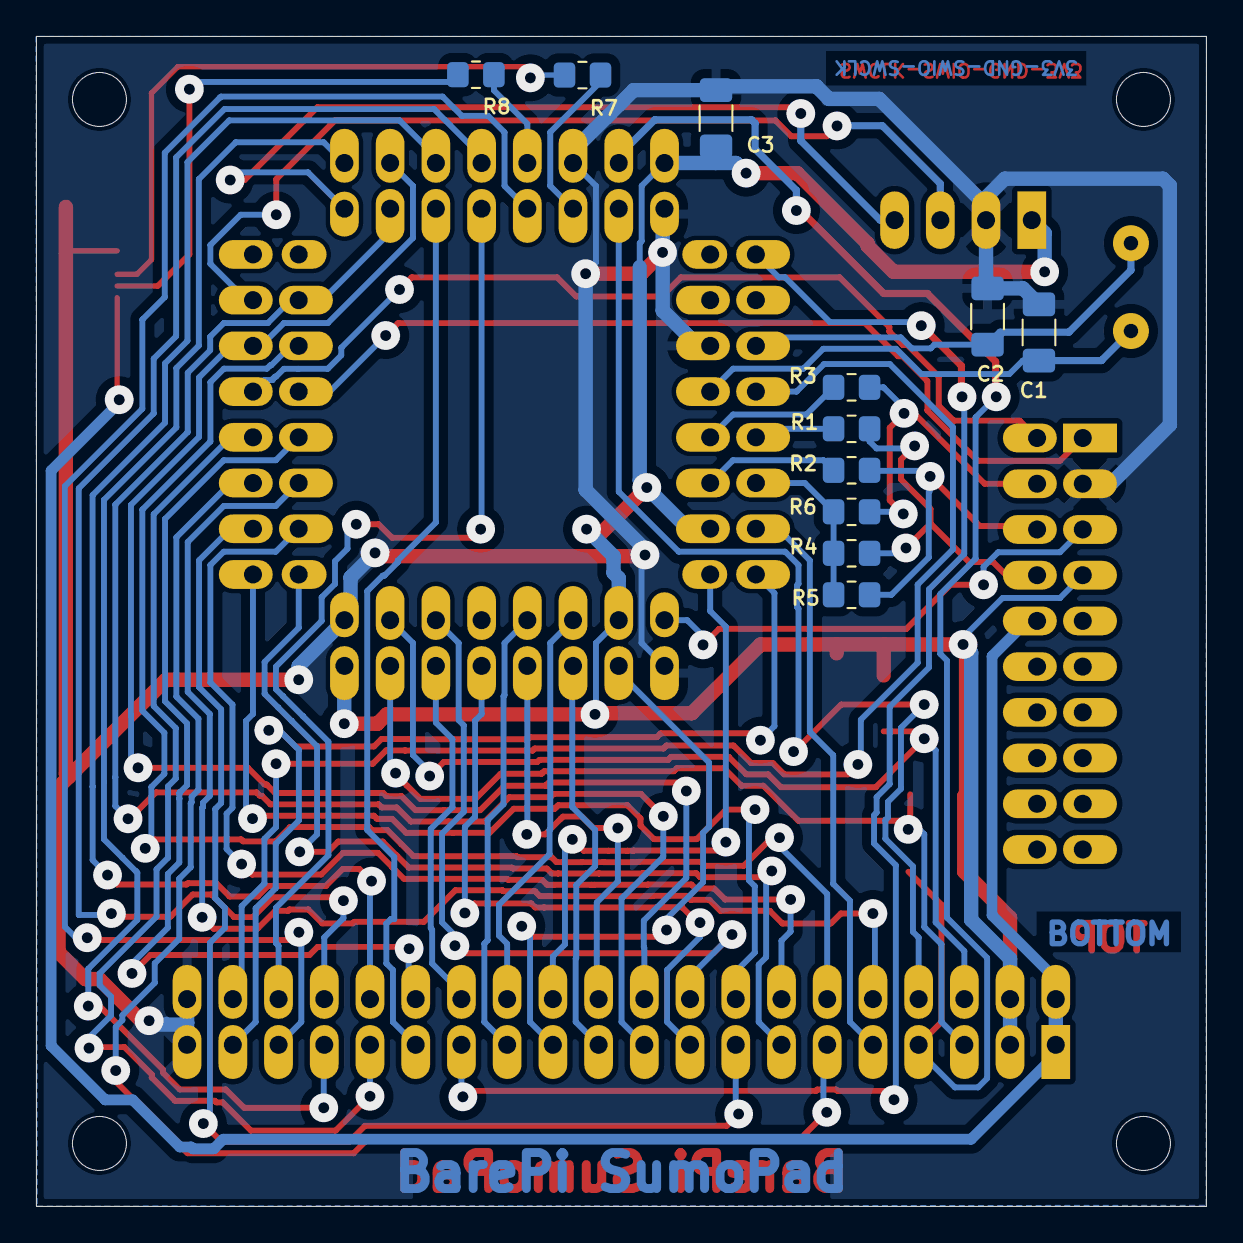
[picture p250: board BarePi_SumoPad.kicad_pcb from below]

Board: 2 copper layers, 65.0 x 65.0 mm, 21 parts (11 on the bottom side), 55 nets.
