Panda381/BarePi/Base/KiCAD/BarePi_Base.kicad_pcb

## KiCad design Base/KiCAD/BarePi_Base.kicad_pcb (2026-06-05)

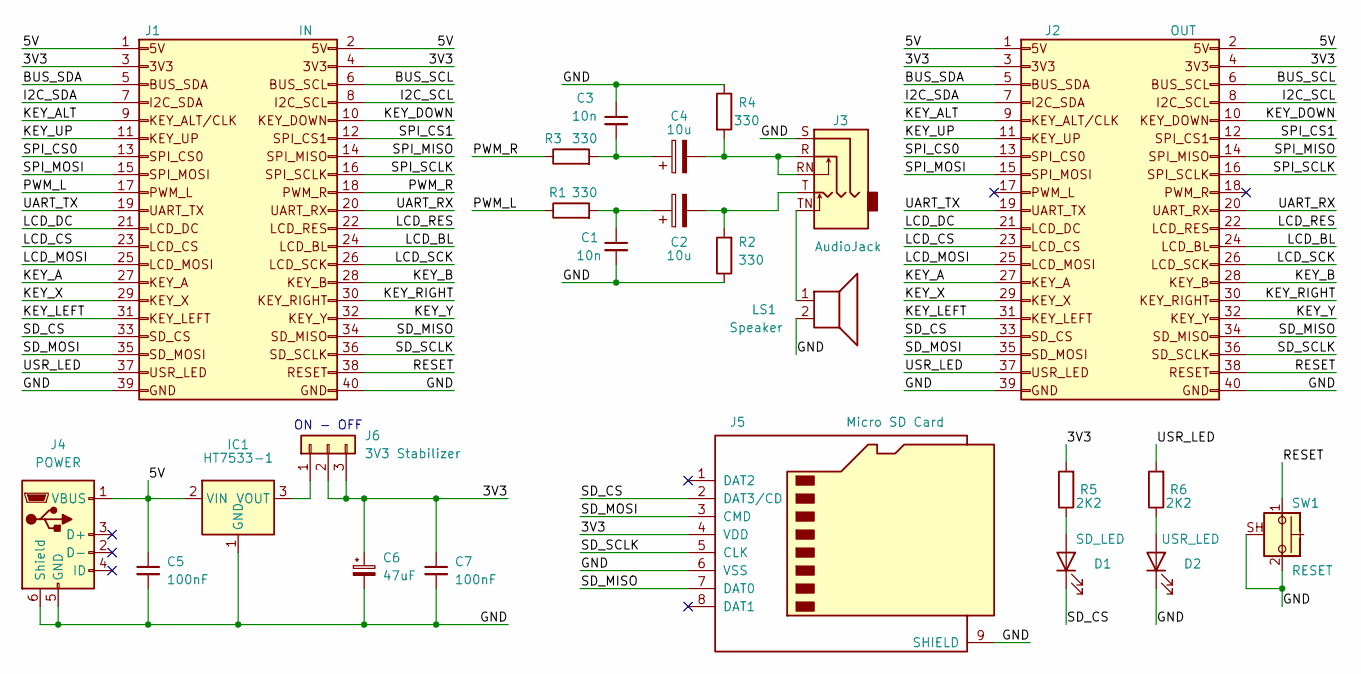
[picture p251: schematic BarePi_Base.kicad_sch]

Parts:
C1, C3: 10n; C_1206_3216Metric_Pad1.33x1.80mm_HandSolder
C2, C4: 10u; CP_EIA-3216-18_Kemet-A_HandSolder
C5, C7: 100nF; C_1206_3216Metric_Pad1.33x1.80mm_HandSolder
C6: 47uF; CP_EIA-3216-18_Kemet-A_HandSolder
D1: SD_LED; LED_D3.0mm
D2: USR_LED; LED_D3.0mm
IC1: HT7533-1; Raspberry_TO-92
J1: IN; Raspberry_IN_PinHeader_2x20_P2.54mm_Horizontal
J2: OUT; Raspberry_OUT_PinSocket_2x20_P2.54mm_Horizontal
J3: AudioJack; Jack_3.5mm_CUI_SJ1-3515N_Horizontal
J4: POWER; Raspberry_USB_Micro-B_Amphenol_10104110_Horizontal
J5: Micro SD Card; Raspberry_microSD_HC_Wuerth_Molex
J6: 3V3 Stabilizer; Raspberry_PinHeader_1x03_P2.54mm_Vertical
LS1: Speaker; Buzzer_TDK_PS1240P02BT_D12.2mm_H6.5mm
R1, R2, R3, R4: 330; R_1206_3216Metric_Pad1.30x1.75mm_HandSolder
R5, R6: 2K2; R_0805_2012Metric_Pad1.20x1.40mm_HandSolder
SW1: RESET; Raspberry_SW_SPST_Omron_B3F-315x_Angled

Connections:
/3V3: C6.1, C7.1, J1.3, J1.4, J2.3, J2.4, J5.4 (VDD), J6.2, J6.3, R5.2
/5V: C5.1, IC1.2 (VIN), J1.1, J1.2, J2.1, J2.2, J4.1 (VBUS)
/BUS_SCL: J1.6, J2.6
/BUS_SDA: J1.5, J2.5
/GND: C1.2, C3.1, C5.2, C6.2, C7.2, D2.1 (K), IC1.1 (GND), J1.39, J1.40, J2.39, J2.40, J3.S, J4.5 (GND), J4.6 (Shield), J5.6 (VSS), J5.9 (SHIELD), LS1.2, R2.1, R4.1, SW1.2, SW1.SH (B)
/I2C_SCL: J1.8, J2.8
/I2C_SDA: J1.7, J2.7
/KEY_A: J1.27, J2.27
/KEY_ALT: J1.9, J2.9
/KEY_B: J1.28, J2.28
/KEY_DOWN: J1.10, J2.10
/KEY_LEFT: J1.31, J2.31
/KEY_RIGHT: J1.30, J2.30
/KEY_UP: J1.11, J2.11
/KEY_X: J1.29, J2.29
/KEY_Y: J1.32, J2.32
/LCD_BL: J1.24, J2.24
/LCD_CS: J1.23, J2.23
/LCD_DC: J1.21, J2.21
/LCD_MOSI: J1.25, J2.25
/LCD_RES: J1.22, J2.22
/LCD_SCK: J1.26, J2.26
/PWM_L: J1.17, R1.1
/PWM_R: J1.18, R3.1
/RESET: J1.38, J2.38, SW1.1
/SD_CS: D1.1 (K), J1.33, J2.33, J5.2 (DAT3/CD)
/SD_MISO: J1.34, J2.34, J5.7 (DAT0)
/SD_MOSI: J1.35, J2.35, J5.3 (CMD)
/SD_SCLK: J1.36, J2.36, J5.5 (CLK)
/SPI_CS0: J1.13, J2.13
/SPI_CS1: J1.12, J2.12
/SPI_MISO: J1.14, J2.14
/SPI_MOSI: J1.15, J2.15
/SPI_SCLK: J1.16, J2.16
/UART_RX: J1.20, J2.20
/UART_TX: J1.19, J2.19
/USR_LED: J1.37, J2.37, R6.2
unnamed: C1.1, C2.1, R1.2
unnamed: C2.2, J3.T, R2.2
unnamed: C3.2, C4.1, R3.2
unnamed: C4.2, J3.R, J3.RN, R4.2
unnamed: D1.2 (A), R5.1
unnamed: D2.2 (A), R6.1
unnamed: IC1.3 (VOUT), J6.1
unnamed: J3.TN, LS1.1

Notes on the sheet:
ON - OFF
