Panda381/BarePi/Base/KiCAD/BarePi_Base.kicad_pcb

## KiCad design Base/KiCAD/BarePi_Base.kicad_pcb (continued)

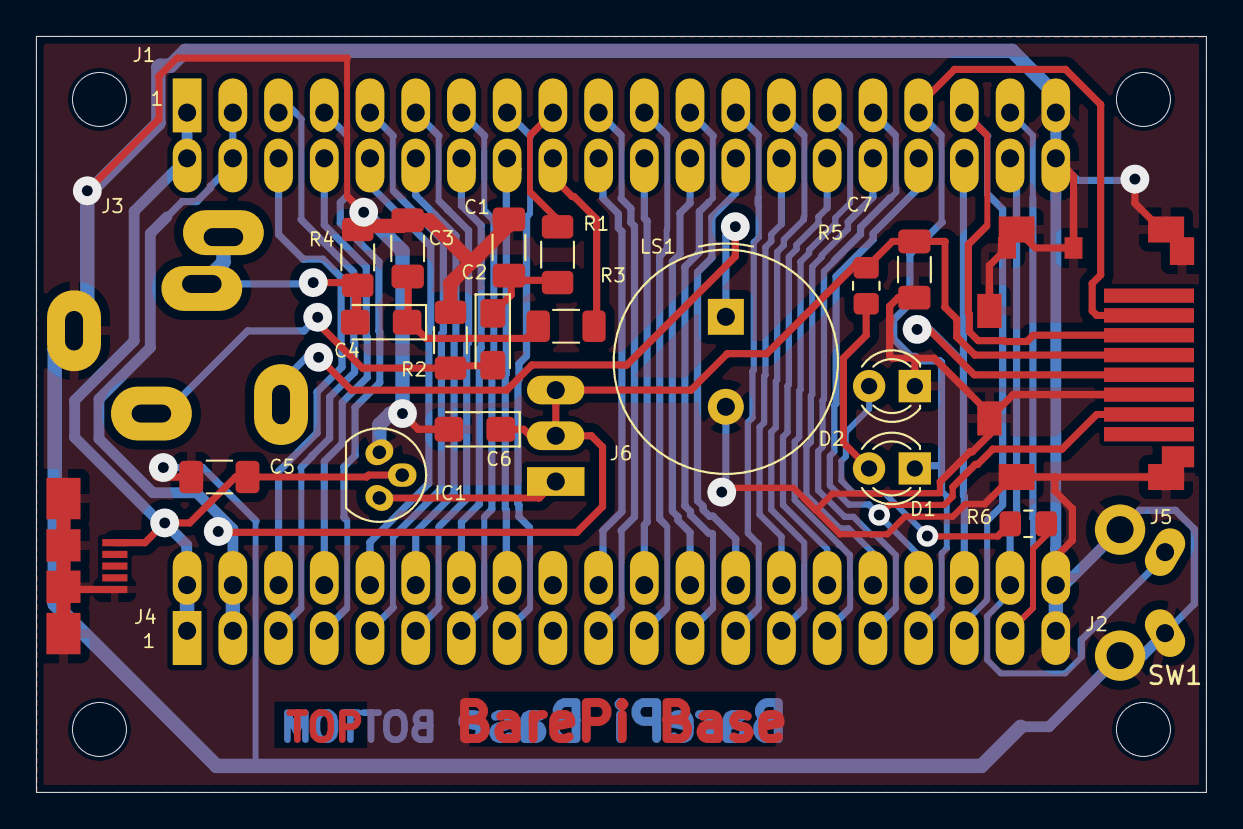
[picture p252: board BarePi_Base.kicad_pcb from above]

Board: 2 copper layers, 65.0 x 42.0 mm, 24 parts (0 on the bottom side), 45 nets.
