Panda381/BarePi/BusExp/KiCAD/BarePi_BusExp.kicad_pcb

## KiCad design BusExp/KiCAD/BarePi_BusExp.kicad_pcb (2026-06-05)

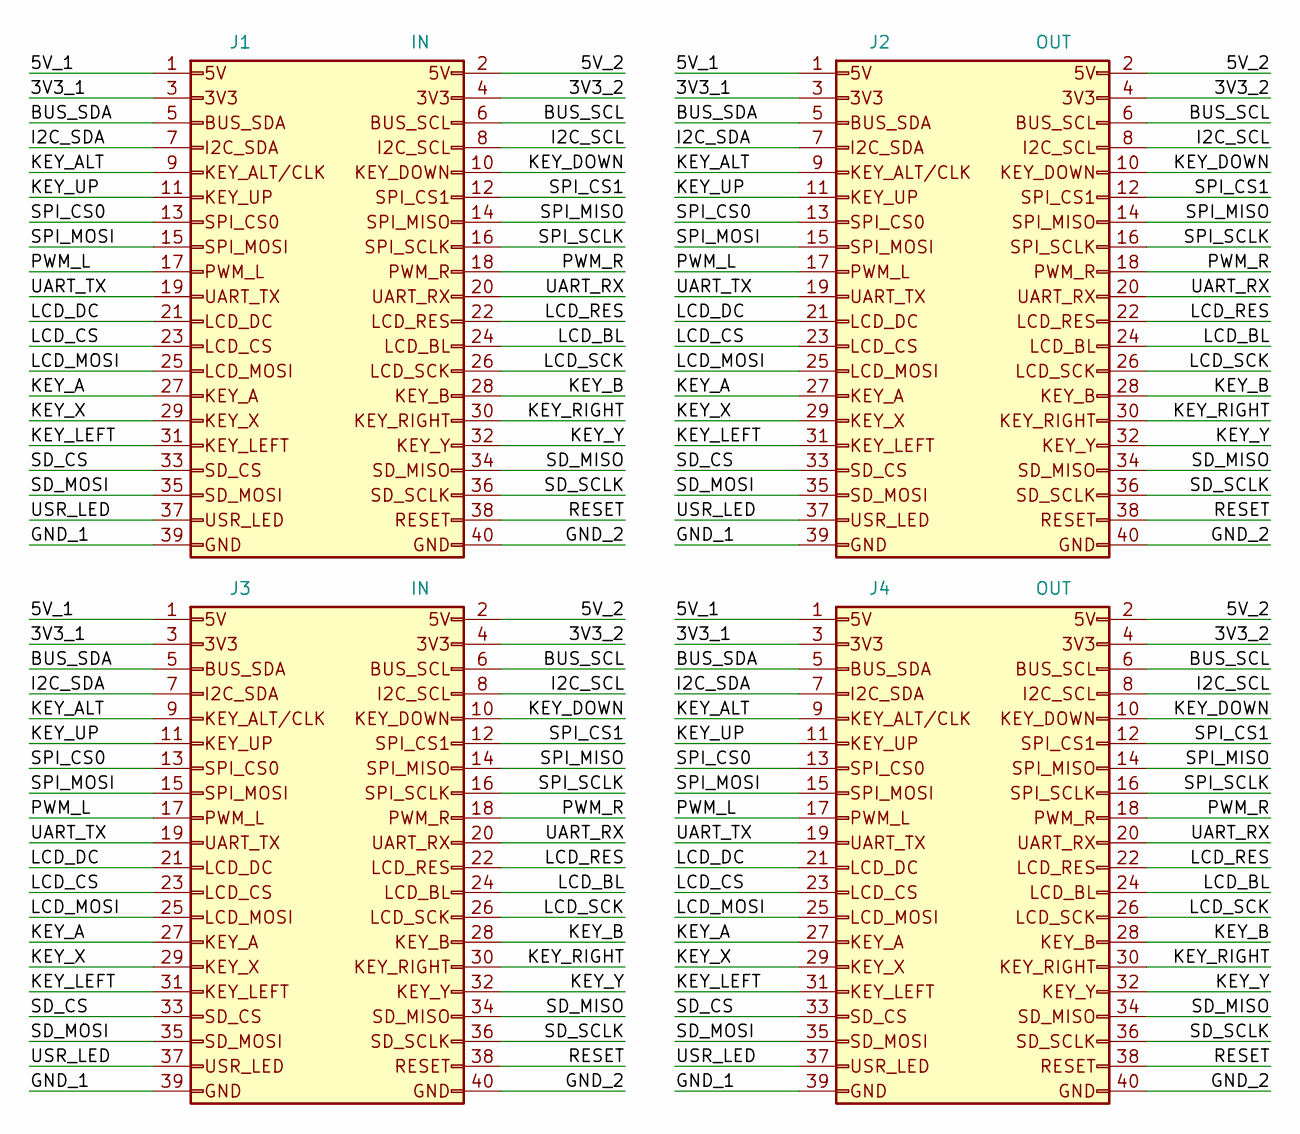
[picture p253: schematic BarePi_BusExp.kicad_sch]

Parts:
J1, J3: IN; Raspberry_IN_PinHeader_2x20_P2.54mm_Vertical
J2, J4: OUT; Raspberry_OUT_PinSocket_2x20_P2.54mm_Vertical

Connections:
/3V3_1: J1.3, J2.3, J3.3, J4.3
/3V3_2: J1.4, J2.4, J3.4, J4.4
/5V_1: J1.1, J2.1, J3.1, J4.1
/5V_2: J1.2, J2.2, J3.2, J4.2
/BUS_SCL: J1.6, J2.6, J3.6, J4.6
/BUS_SDA: J1.5, J2.5, J3.5, J4.5
/GND_1: J1.39, J2.39, J3.39, J4.39
/GND_2: J1.40, J2.40, J3.40, J4.40
/I2C_SCL: J1.8, J2.8, J3.8, J4.8
/I2C_SDA: J1.7, J2.7, J3.7, J4.7
/KEY_A: J1.27, J2.27, J3.27, J4.27
/KEY_ALT: J1.9, J2.9, J3.9, J4.9
/KEY_B: J1.28, J2.28, J3.28, J4.28
/KEY_DOWN: J1.10, J2.10, J3.10, J4.10
/KEY_LEFT: J1.31, J2.31, J3.31, J4.31
/KEY_RIGHT: J1.30, J2.30, J3.30, J4.30
/KEY_UP: J1.11, J2.11, J3.11, J4.11
/KEY_X: J1.29, J2.29, J3.29, J4.29
/KEY_Y: J1.32, J2.32, J3.32, J4.32
/LCD_BL: J1.24, J2.24, J3.24, J4.24
/LCD_CS: J1.23, J2.23, J3.23, J4.23
/LCD_DC: J1.21, J2.21, J3.21, J4.21
/LCD_MOSI: J1.25, J2.25, J3.25, J4.25
/LCD_RES: J1.22, J2.22, J3.22, J4.22
/LCD_SCK: J1.26, J2.26, J3.26, J4.26
/PWM_L: J1.17, J2.17, J3.17, J4.17
/PWM_R: J1.18, J2.18, J3.18, J4.18
/RESET: J1.38, J2.38, J3.38, J4.38
/SD_CS: J1.33, J2.33, J3.33, J4.33
/SD_MISO: J1.34, J2.34, J3.34, J4.34
/SD_MOSI: J1.35, J2.35, J3.35, J4.35
/SD_SCLK: J1.36, J2.36, J3.36, J4.36
/SPI_CS0: J1.13, J2.13, J3.13, J4.13
/SPI_CS1: J1.12, J2.12, J3.12, J4.12
/SPI_MISO: J1.14, J2.14, J3.14, J4.14
/SPI_MOSI: J1.15, J2.15, J3.15, J4.15
/SPI_SCLK: J1.16, J2.16, J3.16, J4.16
/UART_RX: J1.20, J2.20, J3.20, J4.20
/UART_TX: J1.19, J2.19, J3.19, J4.19
/USR_LED: J1.37, J2.37, J3.37, J4.37

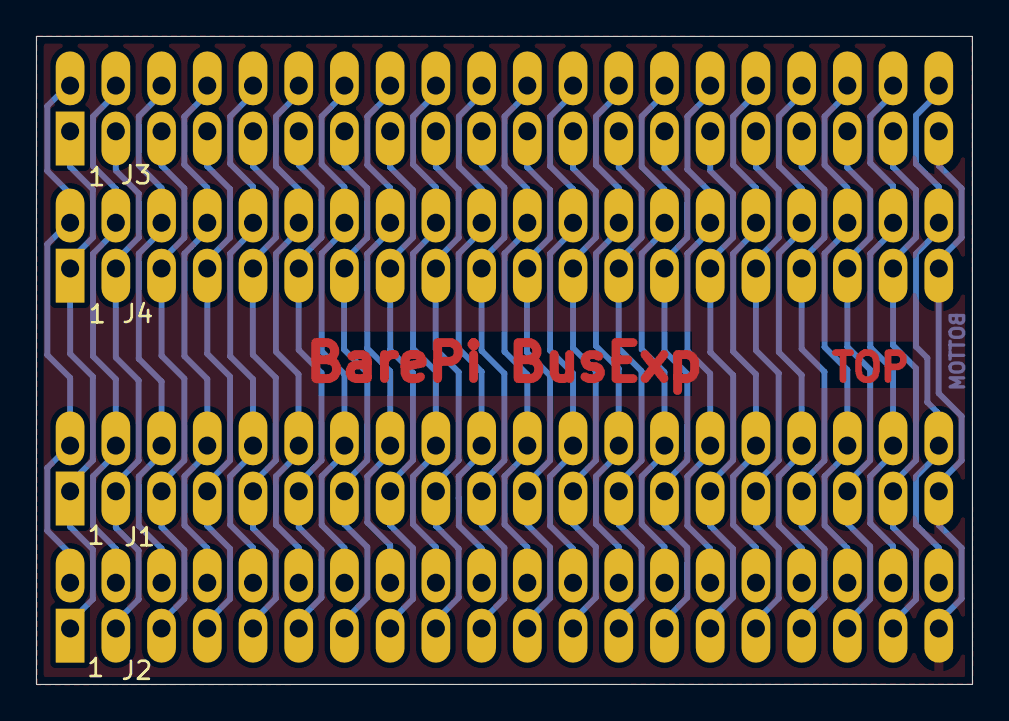
[picture p254: board BarePi_BusExp.kicad_pcb from above]

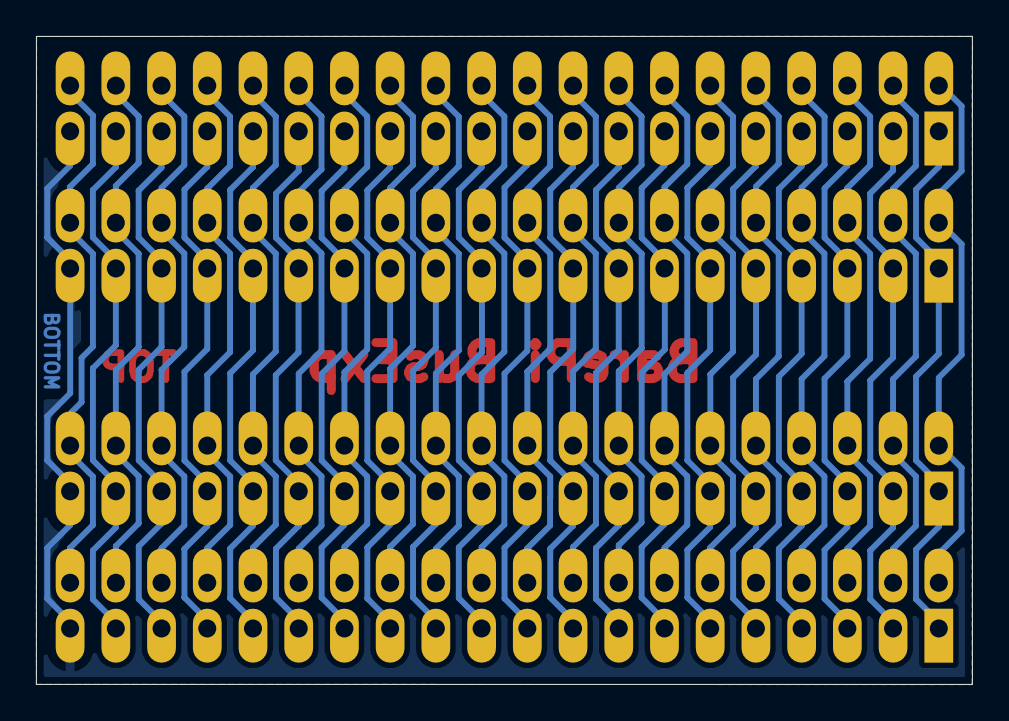
[picture p255: board BarePi_BusExp.kicad_pcb from below]

Board: 2 copper layers, 52.0 x 36.0 mm, 4 parts (2 on the bottom side), 40 nets.
