Panda381/BarePi/TestLed/KiCAD/BarePi_TestLed.kicad_pcb

## KiCad design TestLed/KiCAD/BarePi_TestLed.kicad_pcb (2026-06-03)

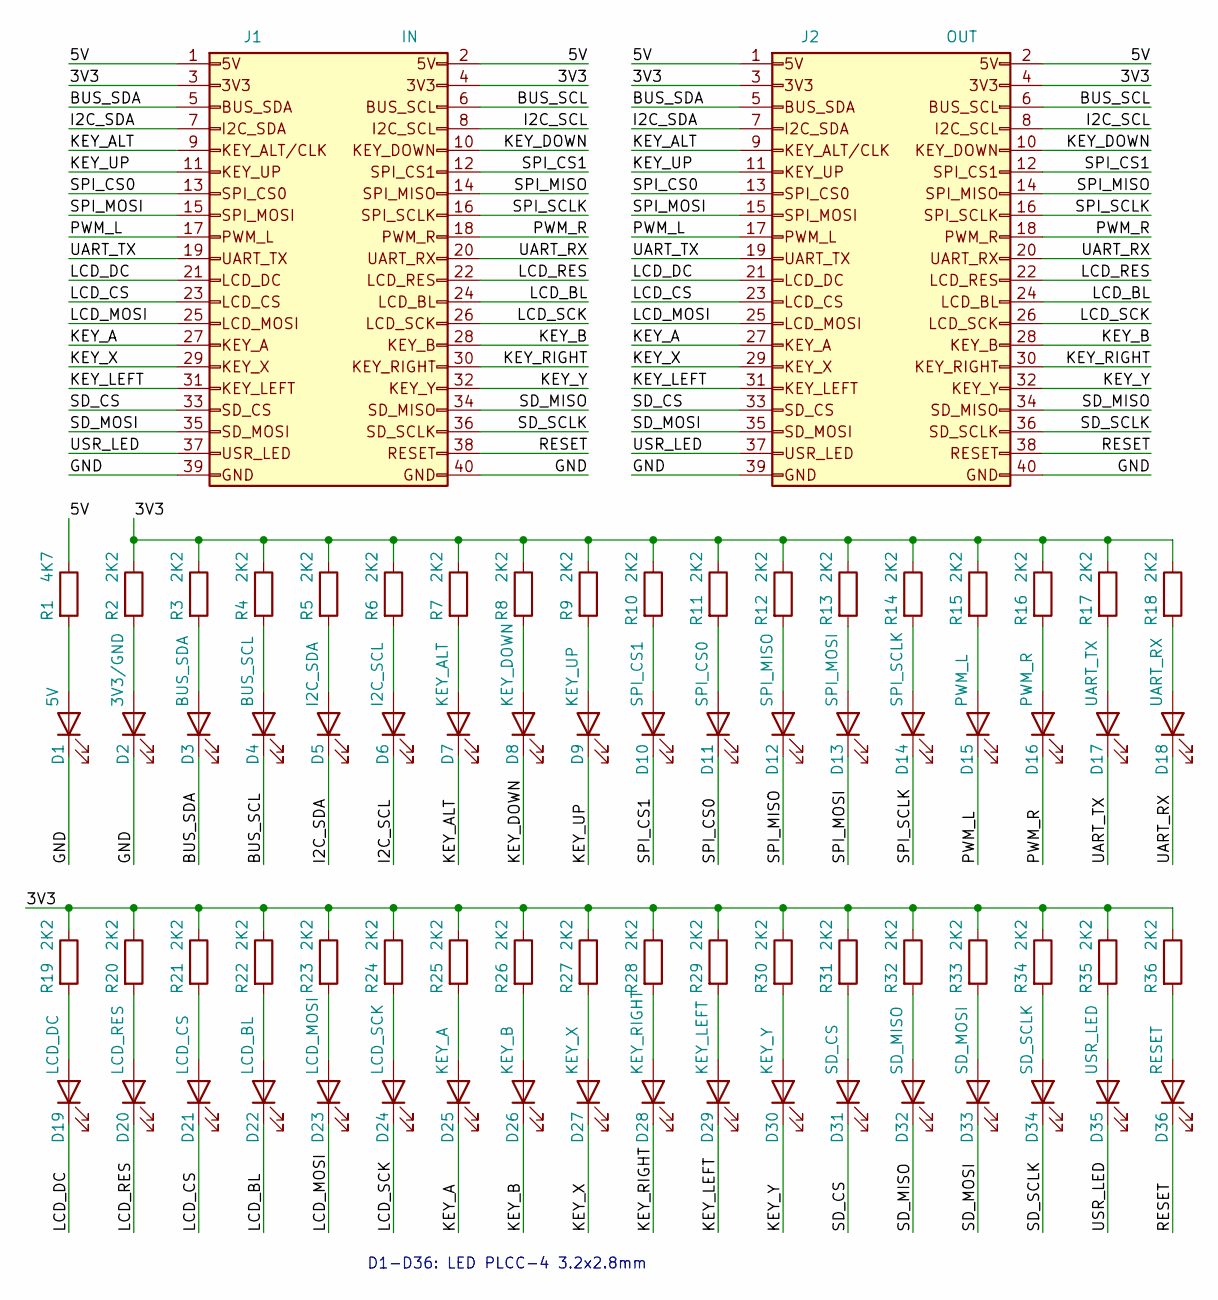
[picture p256: schematic BarePi_TestLed.kicad_sch]

Parts:
D1: 5V; Raspberry_LED_Avago_PLCC4_3.2x2.8mm_CW
D2: 3V3/GND; Raspberry_LED_Avago_PLCC4_3.2x2.8mm_CW
D3: BUS_SDA; Raspberry_LED_Avago_PLCC4_3.2x2.8mm_CW
D4: BUS_SCL; Raspberry_LED_Avago_PLCC4_3.2x2.8mm_CW
D5: I2C_SDA; Raspberry_LED_Avago_PLCC4_3.2x2.8mm_CW
D6: I2C_SCL; Raspberry_LED_Avago_PLCC4_3.2x2.8mm_CW
D7: KEY_ALT; Raspberry_LED_Avago_PLCC4_3.2x2.8mm_CW
D8: KEY_DOWN; Raspberry_LED_Avago_PLCC4_3.2x2.8mm_CW
D9: KEY_UP; Raspberry_LED_Avago_PLCC4_3.2x2.8mm_CW
D10: SPI_CS1; Raspberry_LED_Avago_PLCC4_3.2x2.8mm_CW
D11: SPI_CS0; Raspberry_LED_Avago_PLCC4_3.2x2.8mm_CW
D12: SPI_MISO; Raspberry_LED_Avago_PLCC4_3.2x2.8mm_CW
D13: SPI_MOSI; Raspberry_LED_Avago_PLCC4_3.2x2.8mm_CW
D14: SPI_SCLK; Raspberry_LED_Avago_PLCC4_3.2x2.8mm_CW
D15: PWM_L; Raspberry_LED_Avago_PLCC4_3.2x2.8mm_CW
D16: PWM_R; Raspberry_LED_Avago_PLCC4_3.2x2.8mm_CW
D17: UART_TX; Raspberry_LED_Avago_PLCC4_3.2x2.8mm_CW
D18: UART_RX; Raspberry_LED_Avago_PLCC4_3.2x2.8mm_CW
D19: LCD_DC; Raspberry_LED_Avago_PLCC4_3.2x2.8mm_CW
D20: LCD_RES; Raspberry_LED_Avago_PLCC4_3.2x2.8mm_CW
D21: LCD_CS; Raspberry_LED_Avago_PLCC4_3.2x2.8mm_CW
D22: LCD_BL; Raspberry_LED_Avago_PLCC4_3.2x2.8mm_CW
D23: LCD_MOSI; Raspberry_LED_Avago_PLCC4_3.2x2.8mm_CW
D24: LCD_SCK; Raspberry_LED_Avago_PLCC4_3.2x2.8mm_CW
D25: KEY_A; Raspberry_LED_Avago_PLCC4_3.2x2.8mm_CW
D26: KEY_B; Raspberry_LED_Avago_PLCC4_3.2x2.8mm_CW
D27: KEY_X; Raspberry_LED_Avago_PLCC4_3.2x2.8mm_CW
D28: KEY_RIGHT; Raspberry_LED_Avago_PLCC4_3.2x2.8mm_CW
D29: KEY_LEFT; Raspberry_LED_Avago_PLCC4_3.2x2.8mm_CW
D30: KEY_Y; Raspberry_LED_Avago_PLCC4_3.2x2.8mm_CW
D31: SD_CS; Raspberry_LED_Avago_PLCC4_3.2x2.8mm_CW
D32: SD_MISO; Raspberry_LED_Avago_PLCC4_3.2x2.8mm_CW
D33: SD_MOSI; Raspberry_LED_Avago_PLCC4_3.2x2.8mm_CW
D34: SD_SCLK; Raspberry_LED_Avago_PLCC4_3.2x2.8mm_CW
D35: USR_LED; Raspberry_LED_Avago_PLCC4_3.2x2.8mm_CW
D36: RESET; Raspberry_LED_Avago_PLCC4_3.2x2.8mm_CW
J1: IN; Raspberry_IN_PinHeader_2x20_P2.54mm_Horizontal
J2: OUT; Raspberry_OUT_PinSocket_2x20_P2.54mm_Horizontal
R1: 4K7; R_0805_2012Metric_Pad1.20x1.40mm_HandSolder
R2, R3, R4, R5, R6, R7, R8, R9, R10, R11, R12, R13, R14, R15, R16, R17, R18, R19, R20, R21, R22, R23, R24, R25, R26, R27, R28, R29, R30, R31, R32, R33, R34, R35, R36: 2K2; R_0805_2012Metric_Pad1.20x1.40mm_HandSolder

Connections:
/3V3: J1.3, J1.4, J2.3, J2.4, R2.1, R3.1, R4.1, R5.1, R6.1, R7.1, R8.1, R9.1, R10.1, R11.1, R12.1, R13.1, R14.1, R15.1, R16.1, R17.1, R18.1, R19.1, R20.1, R21.1, R22.1, R23.1, R24.1, R25.1, R26.1, R27.1, R28.1, R29.1, R30.1, R31.1, R32.1, R33.1, R34.1, R35.1, R36.1
/5V: J1.1, J1.2, J2.1, J2.2, R1.1
/BUS_SCL: D4.1 (K), J1.6, J2.6
/BUS_SDA: D3.1 (K), J1.5, J2.5
/GND: D1.1 (K), D2.1 (K), J1.39, J1.40, J2.39, J2.40
/I2C_SCL: D6.1 (K), J1.8, J2.8
/I2C_SDA: D5.1 (K), J1.7, J2.7
/KEY_A: D25.1 (K), J1.27, J2.27
/KEY_ALT: D7.1 (K), J1.9, J2.9
/KEY_B: D26.1 (K), J1.28, J2.28
/KEY_DOWN: D8.1 (K), J1.10, J2.10
/KEY_LEFT: D29.1 (K), J1.31, J2.31
/KEY_RIGHT: D28.1 (K), J1.30, J2.30
/KEY_UP: D9.1 (K), J1.11, J2.11
/KEY_X: D27.1 (K), J1.29, J2.29
/KEY_Y: D30.1 (K), J1.32, J2.32
/LCD_BL: D22.1 (K), J1.24, J2.24
/LCD_CS: D21.1 (K), J1.23, J2.23
/LCD_DC: D19.1 (K), J1.21, J2.21
/LCD_MOSI: D23.1 (K), J1.25, J2.25
/LCD_RES: D20.1 (K), J1.22, J2.22
/LCD_SCK: D24.1 (K), J1.26, J2.26
/PWM_L: D15.1 (K), J1.17, J2.17
/PWM_R: D16.1 (K), J1.18, J2.18
/RESET: D36.1 (K), J1.38, J2.38
/SD_CS: D31.1 (K), J1.33, J2.33
/SD_MISO: D32.1 (K), J1.34, J2.34
/SD_MOSI: D33.1 (K), J1.35, J2.35
/SD_SCLK: D34.1 (K), J1.36, J2.36
/SPI_CS0: D11.1 (K), J1.13, J2.13
/SPI_CS1: D10.1 (K), J1.12, J2.12
/SPI_MISO: D12.1 (K), J1.14, J2.14
/SPI_MOSI: D13.1 (K), J1.15, J2.15
/SPI_SCLK: D14.1 (K), J1.16, J2.16
/UART_RX: D18.1 (K), J1.20, J2.20
/UART_TX: D17.1 (K), J1.19, J2.19
/USR_LED: D35.1 (K), J1.37, J2.37
unnamed: D1.2 (A), R1.2
unnamed: D2.2 (A), R2.2
unnamed: D3.2 (A), R3.2
unnamed: D4.2 (A), R4.2
unnamed: D5.2 (A), R5.2
unnamed: D6.2 (A), R6.2
unnamed: D7.2 (A), R7.2
unnamed: D8.2 (A), R8.2
unnamed: D9.2 (A), R9.2
unnamed: D10.2 (A), R10.2
unnamed: D11.2 (A), R11.2
unnamed: D12.2 (A), R12.2
unnamed: D13.2 (A), R13.2
unnamed: D14.2 (A), R14.2
unnamed: D15.2 (A), R15.2
unnamed: D16.2 (A), R16.2
unnamed: D17.2 (A), R17.2
unnamed: D18.2 (A), R18.2
unnamed: D19.2 (A), R19.2
unnamed: D20.2 (A), R20.2
unnamed: D21.2 (A), R21.2
unnamed: D22.2 (A), R22.2
unnamed: D23.2 (A), R23.2
unnamed: D24.2 (A), R24.2
unnamed: D25.2 (A), R25.2
unnamed: D26.2 (A), R26.2
unnamed: D27.2 (A), R27.2
unnamed: D28.2 (A), R28.2
unnamed: D29.2 (A), R29.2
unnamed: D30.2 (A), R30.2
unnamed: D31.2 (A), R31.2
unnamed: D32.2 (A), R32.2
unnamed: D33.2 (A), R33.2
unnamed: D34.2 (A), R34.2
unnamed: D35.2 (A), R35.2
unnamed: D36.2 (A), R36.2

Notes on the sheet:
D1-D36: LED PLCC-4 3.2x2.8mm

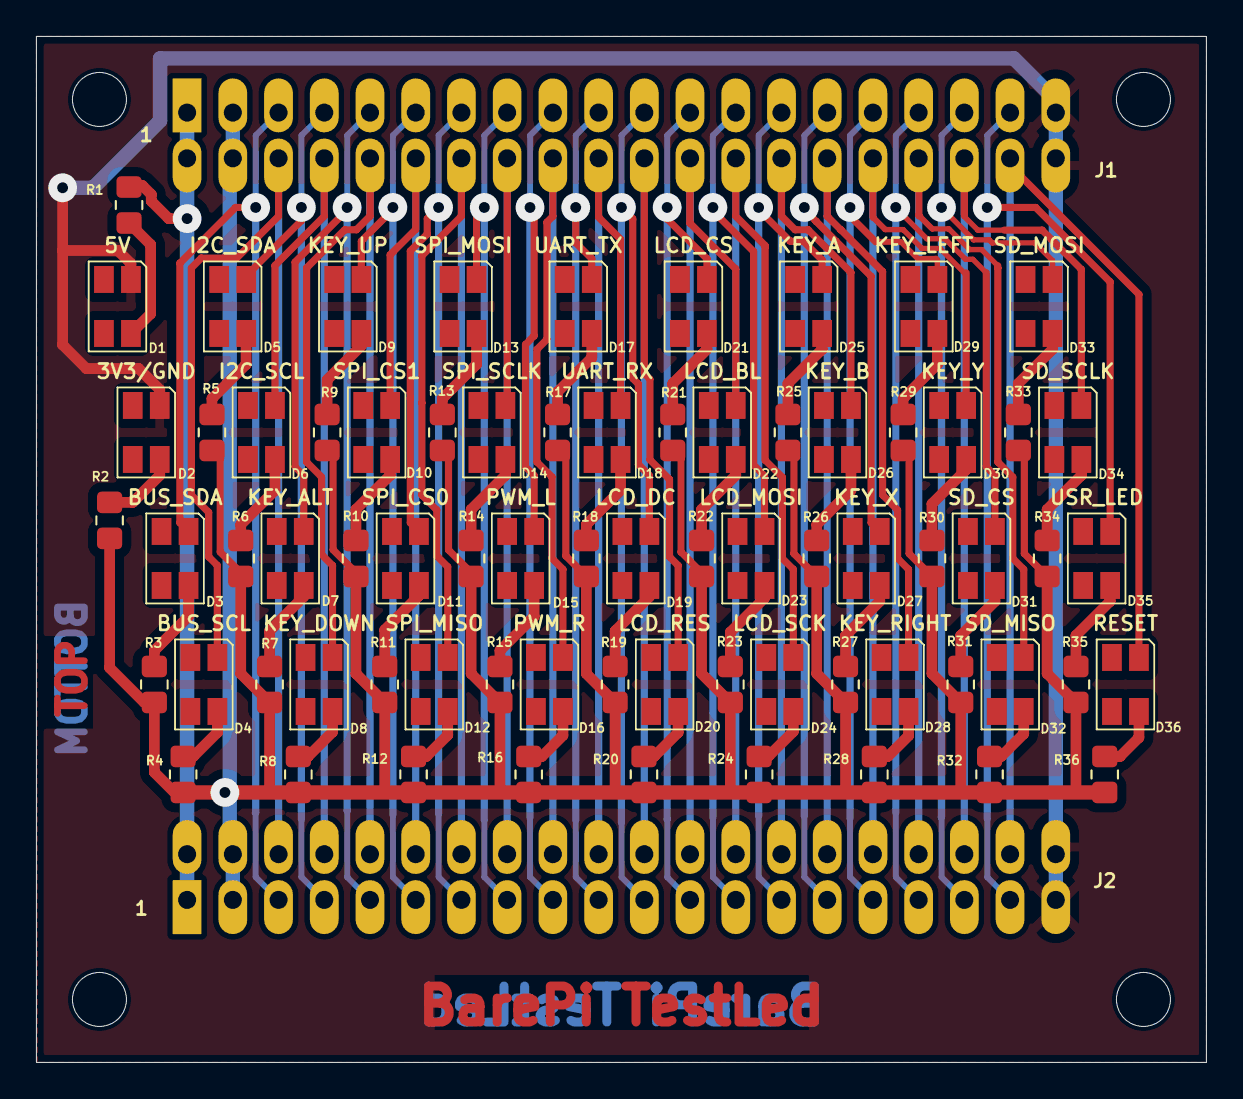
[picture p257: board BarePi_TestLed.kicad_pcb from above]

Board: 2 copper layers, 65.0 x 57.0 mm, 74 parts (0 on the bottom side), 73 nets.
