Panda381/BarePi/PidiPad/KiCAD/BarePi_PidiPad.kicad_pcb

## KiCad design PidiPad/KiCAD/BarePi_PidiPad.kicad_pcb (2026-06-03)

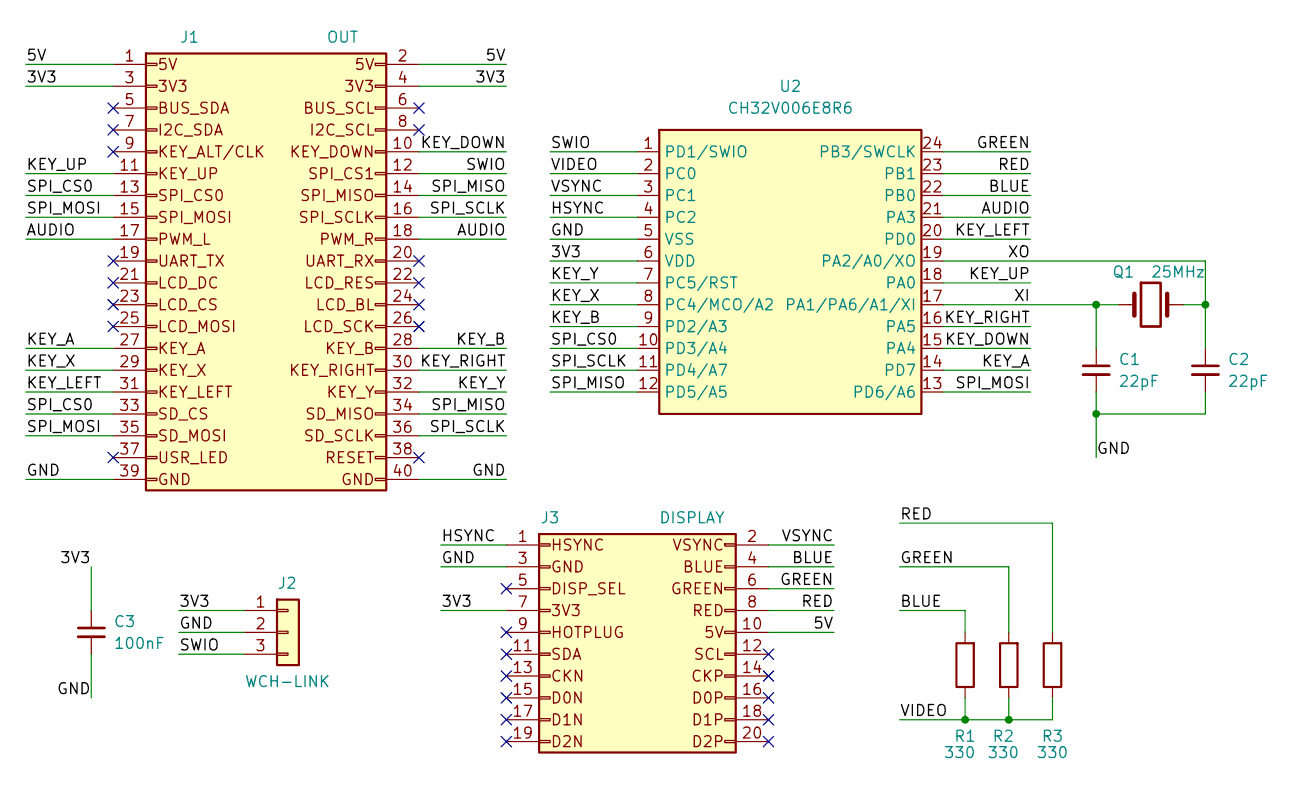
[picture p258: schematic BarePi_PidiPad.kicad_sch]

Parts:
C1, C2: 22pF; C_1206_3216Metric_Pad1.33x1.80mm_HandSolder
C3: 100nF; C_1206_3216Metric_Pad1.33x1.80mm_HandSolder
J1: OUT; Raspberry_OUT_PinSocket_2x20_P2.54mm_Horizontal
J2: WCH-LINK; Raspberry_PinHeader_1x03_P2.54mm_Horizontal
J3: DISPLAY; Raspberry_OUT_PinSocket_2x10_P2.54mm_Horizontal
Q1: 25MHz; Raspberry_Crystal_HC49-4H_Vertical
R1, R2, R3: 330; R_0805_2012Metric_Pad1.20x1.40mm_HandSolder
U2: CH32V006E8R6; Raspberry_QSOP-24_3.9x8.7mm_P0.635mm

Connections:
/3V3: C3.1, J1.3, J1.4, J2.1, J3.7, U2.6 (VDD)
/5V: J1.1, J1.2, J3.10
/AUDIO: J1.17, J1.18, U2.21 (PA3)
/BLUE: J3.4, R1.2, U2.22 (PB0)
/GND: C1.2, C2.2, C3.2, J1.39, J1.40, J2.2, J3.3, U2.5 (VSS)
/GREEN: J3.6, R2.2, U2.24 (PB3/SWCLK)
/HSYNC: J3.1, U2.4 (PC2)
/KEY_A: J1.27, U2.14 (PD7)
/KEY_B: J1.28, U2.9 (PD2/A3)
/KEY_DOWN: J1.10, U2.15 (PA4)
/KEY_LEFT: J1.31, U2.20 (PD0)
/KEY_RIGHT: J1.30, U2.16 (PA5)
/KEY_UP: J1.11, U2.18 (PA0)
/KEY_X: J1.29, U2.8 (PC4/MCO/A2)
/KEY_Y: J1.32, U2.7 (PC5/RST)
/RED: J3.8, R3.2, U2.23 (PB1)
/SPI_CS0: J1.13, J1.33, U2.10 (PD3/A4)
/SPI_MISO: J1.14, J1.34, U2.12 (PD5/A5)
/SPI_MOSI: J1.15, J1.35, U2.13 (PD6/A6)
/SPI_SCLK: J1.16, J1.36, U2.11 (PD4/A7)
/SWIO: J1.12, J2.3, U2.1 (PD1/SWIO)
/VIDEO: R1.1, R2.1, R3.1, U2.2 (PC0)
/VSYNC: J3.2, U2.3 (PC1)
/XI: C1.1, Q1.1, U2.17 (PA1/PA6/A1/XI)
/XO: C2.1, Q1.2, U2.19 (PA2/A0/XO)

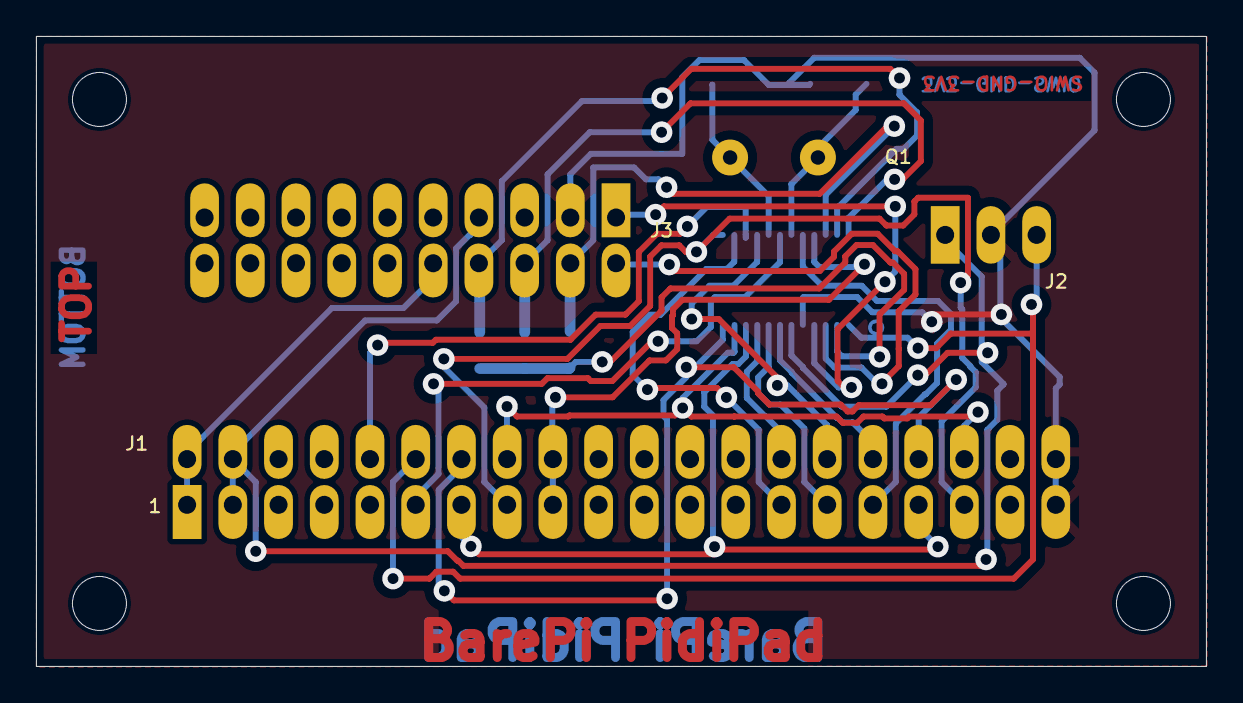
[picture p259: board BarePi_PidiPad.kicad_pcb from above]

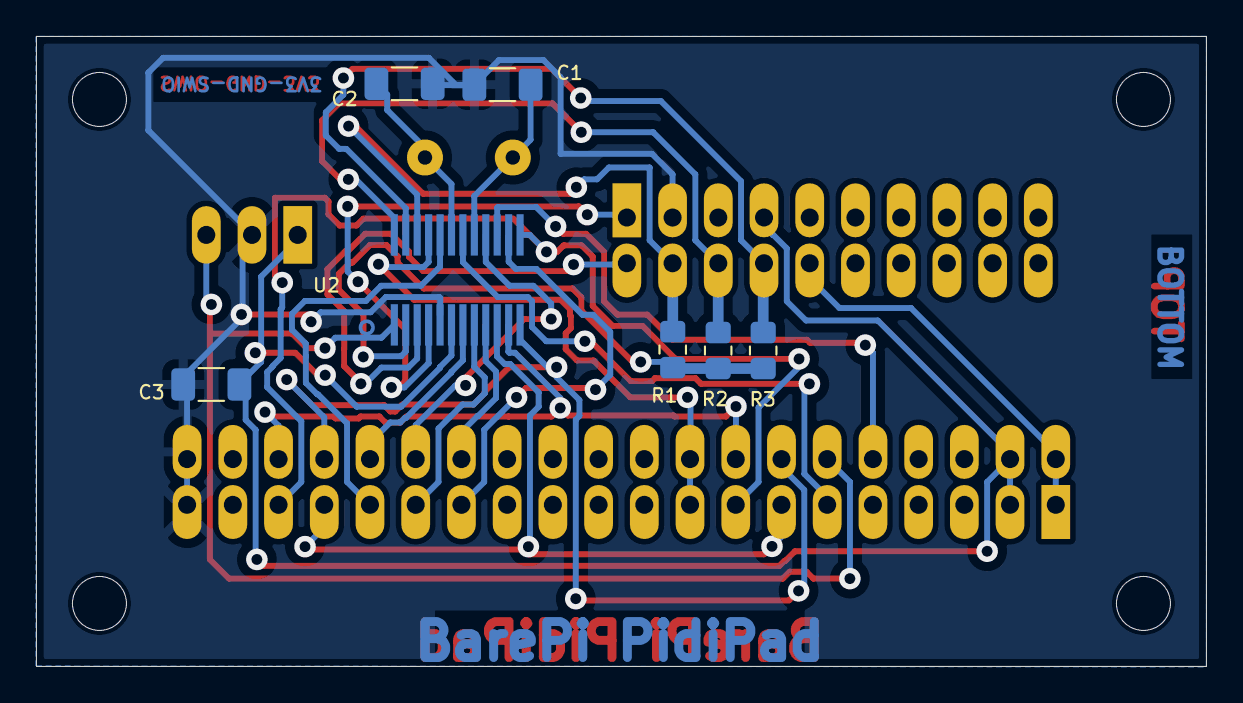
[picture p260: board BarePi_PidiPad.kicad_pcb from below]

Board: 2 copper layers, 65.0 x 35.0 mm, 11 parts (7 on the bottom side), 25 nets.
