Panda381/BarePi/PidiMet/KiCAD/BarePi_PidiMet.kicad_pcb

## KiCad design PidiMet/KiCAD/BarePi_PidiMet.kicad_pcb (2026-06-03)

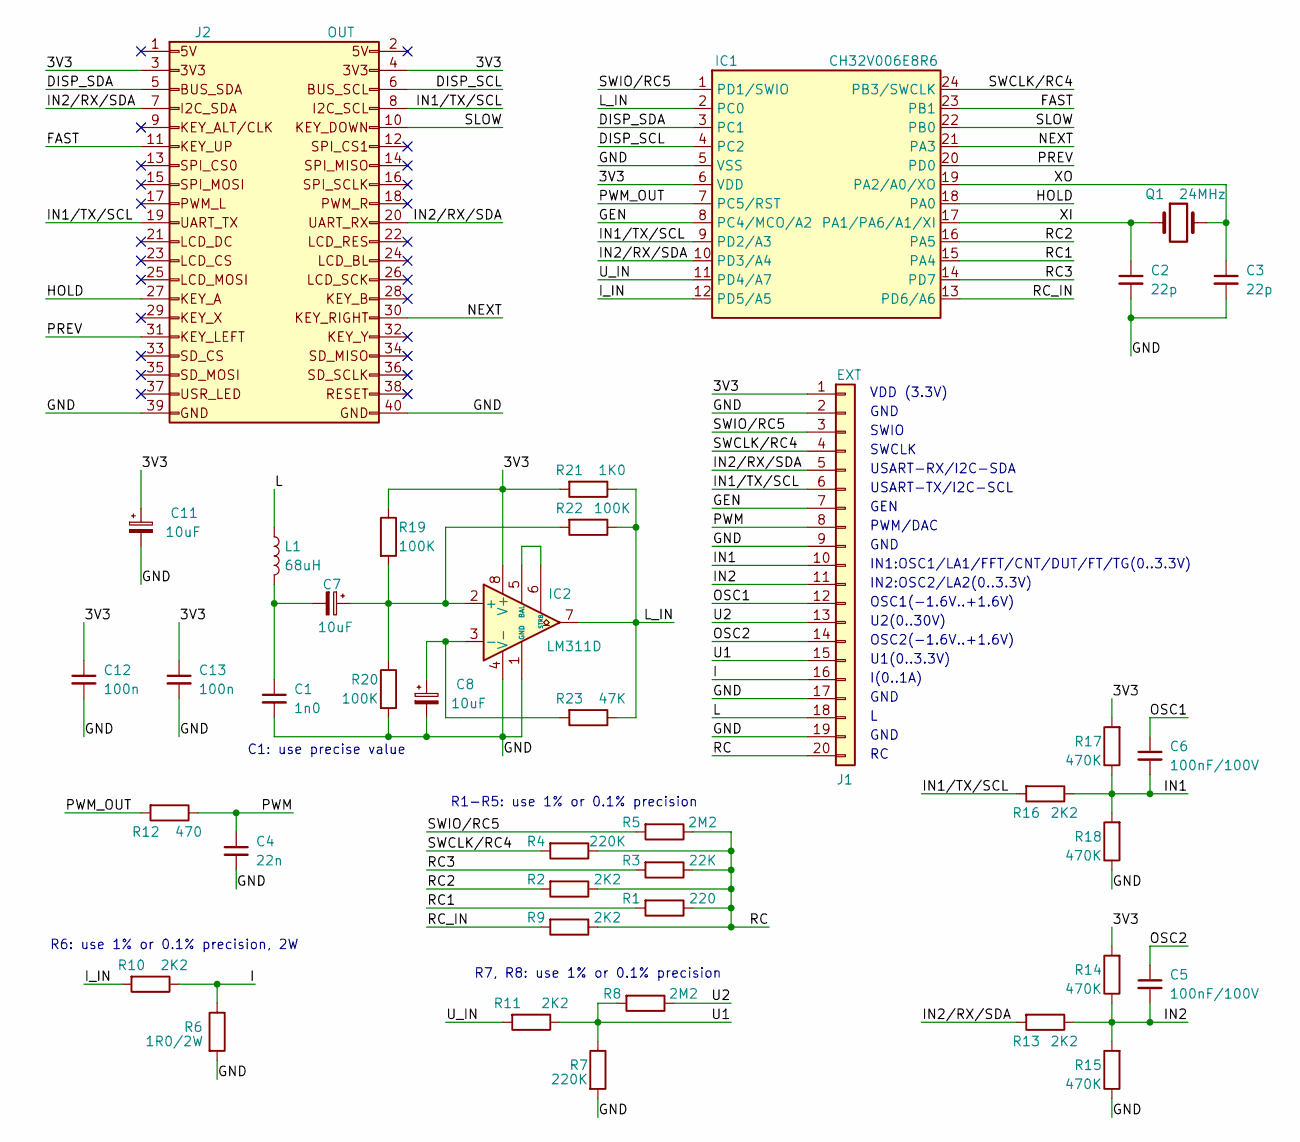
[picture p261: schematic BarePi_PidiMet.kicad_sch]

Parts:
C1: 1n0; C_Axial_L5.1mm_D3.1mm_P10.00mm_Horizontal
C2, C3: 22p; C_1206_3216Metric_Pad1.33x1.80mm_HandSolder
C4: 22n; C_1206_3216Metric_Pad1.33x1.80mm_HandSolder
C5, C6: 100nF/100V; C_1206_3216Metric_Pad1.33x1.80mm_HandSolder
C7, C8, C11: 10uF; CP_EIA-3216-18_Kemet-A_HandSolder
C12, C13: 100n; C_1206_3216Metric_Pad1.33x1.80mm_HandSolder
IC1: CH32V006E8R6; Raspberry_QSOP-24_3.9x8.7mm_P0.635mm
IC2: LM311D; JEITA_SOIC-8_3.9x4.9mm_P1.27mm
J1: EXT; Raspberry_PinHeader_1x20_P2.54mm_Horizontal_rev
J2: OUT; Raspberry_OUT_PinSocket_2x20_P2.54mm_Horizontal
L1: 68uH; L_Axial_L5.0mm_D3.6mm_P10.00mm_Horizontal_Murata_BL01RN1A2A2
Q1: 24MHz; Raspberry_Crystal_HC49-4H_Vertical
R1: 220; R_Axial_DIN0207_L6.3mm_D2.5mm_P7.62mm_Horizontal
R2: 2K2; R_Axial_DIN0207_L6.3mm_D2.5mm_P7.62mm_Horizontal
R3: 22K; R_Axial_DIN0207_L6.3mm_D2.5mm_P7.62mm_Horizontal
R4, R7: 220K; R_Axial_DIN0207_L6.3mm_D2.5mm_P7.62mm_Horizontal
R5, R8: 2M2; R_Axial_DIN0207_L6.3mm_D2.5mm_P7.62mm_Horizontal
R6: 1R0/2W; R_Axial_DIN0411_L9.9mm_D3.6mm_P12.70mm_Horizontal
R9, R10, R11, R13, R16: 2K2; R_0805_2012Metric_Pad1.20x1.40mm_HandSolder
R12: 470; R_0805_2012Metric_Pad1.20x1.40mm_HandSolder
R14, R15, R17, R18: 470K; R_0805_2012Metric_Pad1.20x1.40mm_HandSolder
R19, R20, R22: 100K; R_0805_2012Metric_Pad1.20x1.40mm_HandSolder
R21: 1K0; R_0805_2012Metric_Pad1.20x1.40mm_HandSolder
R23: 47K; R_0805_2012Metric_Pad1.20x1.40mm_HandSolder

Connections:
/3V3: C11.1, C12.1, C13.1, IC1.6 (VDD), IC2.8 (V+), J1.1, J2.3, J2.4, R14.2, R17.2, R19.1, R21.2
/DISP_SCL: IC1.4 (PC2), J2.6
/DISP_SDA: IC1.3 (PC1), J2.5
/FAST: IC1.23 (PB1), J2.11
/GEN: IC1.8 (PC4/MCO/A2), J1.7
/GND: C1.2, C2.2, C3.2, C4.2, C8.2, C11.2, C12.2, C13.2, IC1.5 (VSS), IC2.1 (GND), IC2.4 (V-), J1.2, J1.9, J1.17, J1.19, J2.39, J2.40, R6.2, R7.2, R15.1, R18.1, R20.2
/HOLD: IC1.18 (PA0), J2.27
/I: J1.16, R6.1, R10.1
/IN1: C6.2, J1.10, R16.1, R17.1, R18.2
/IN2: C5.2, J1.11, R13.1, R14.1, R15.2
/I_IN: IC1.12 (PD5/A5), R10.2
/L: J1.18, L1.1
/L_IN: IC1.2 (PC0), IC2.7, R21.1, R22.1, R23.1
/NEXT: IC1.21 (PA3), J2.30
/OSC1: C6.1, J1.12
/OSC2: C5.1, J1.14
/PREV: IC1.20 (PD0), J2.31
/PWM: C4.1, J1.8, R12.1
/PWM_OUT: IC1.7 (PC5/RST), R12.2
/RC: J1.20, R1.1, R2.1, R3.1, R4.1, R5.1, R9.1
/RC1: IC1.15 (PA4), R1.2
/RC2: IC1.16 (PA5), R2.2
/RC3: IC1.14 (PD7), R3.2
/RC_IN: IC1.13 (PD6/A6), R9.2
/SLOW: IC1.22 (PB0), J2.10
/SWCLK/RC4: IC1.24 (PB3/SWCLK), J1.4, R4.2
/SWIO/RC5: IC1.1 (PD1/SWIO), J1.3, R5.2
/U1: J1.15, R7.1, R8.2, R11.1
/U2: J1.13, R8.1
/U_IN: IC1.11 (PD4/A7), R11.2
/XI: C2.1, IC1.17 (PA1/PA6/A1/XI), Q1.1
/XO: C3.1, IC1.19 (PA2/A0/XO), Q1.2
unnamed: C1.1, C7.2, L1.2
unnamed: C7.1, IC2.2 (+), R19.2, R20.1, R22.2
unnamed: C8.1, IC2.3 (-), R23.2
unnamed: IC2.5 (BAL), IC2.6 (STRB)

Notes on the sheet:
OSC1(-1.6V..+1.6V)
GEN
VDD (3.3V)
U2(0..30V)
IN2:OSC2/LA2(0..3.3V)
USART-RX/I2C-SDA
SWIO
R1-R5: use 1% or 0.1% precision
R7, R8: use 1% or 0.1% precision
PWM/DAC
C1: use precise value
USART-TX/I2C-SCL
GND
U1(0..3.3V)
R6: use 1% or 0.1% precision, 2W
OSC2(-1.6V..+1.6V)
I(0..1A)
IN1:OSC1/LA1/FFT/CNT/DUT/FT/TG(0..3.3V)
SWCLK

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
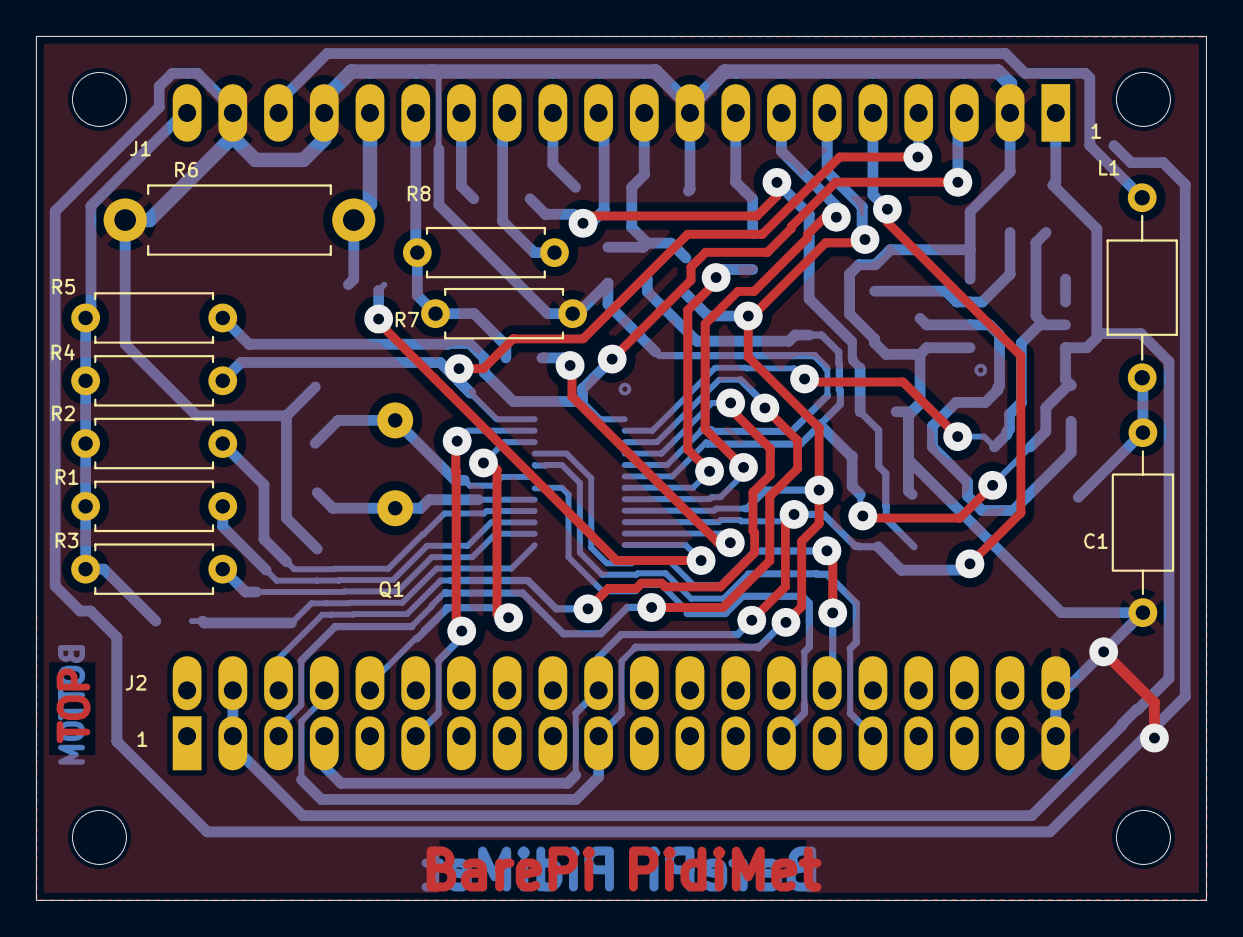
[picture p262: board BarePi_PidiMet.kicad_pcb from above]

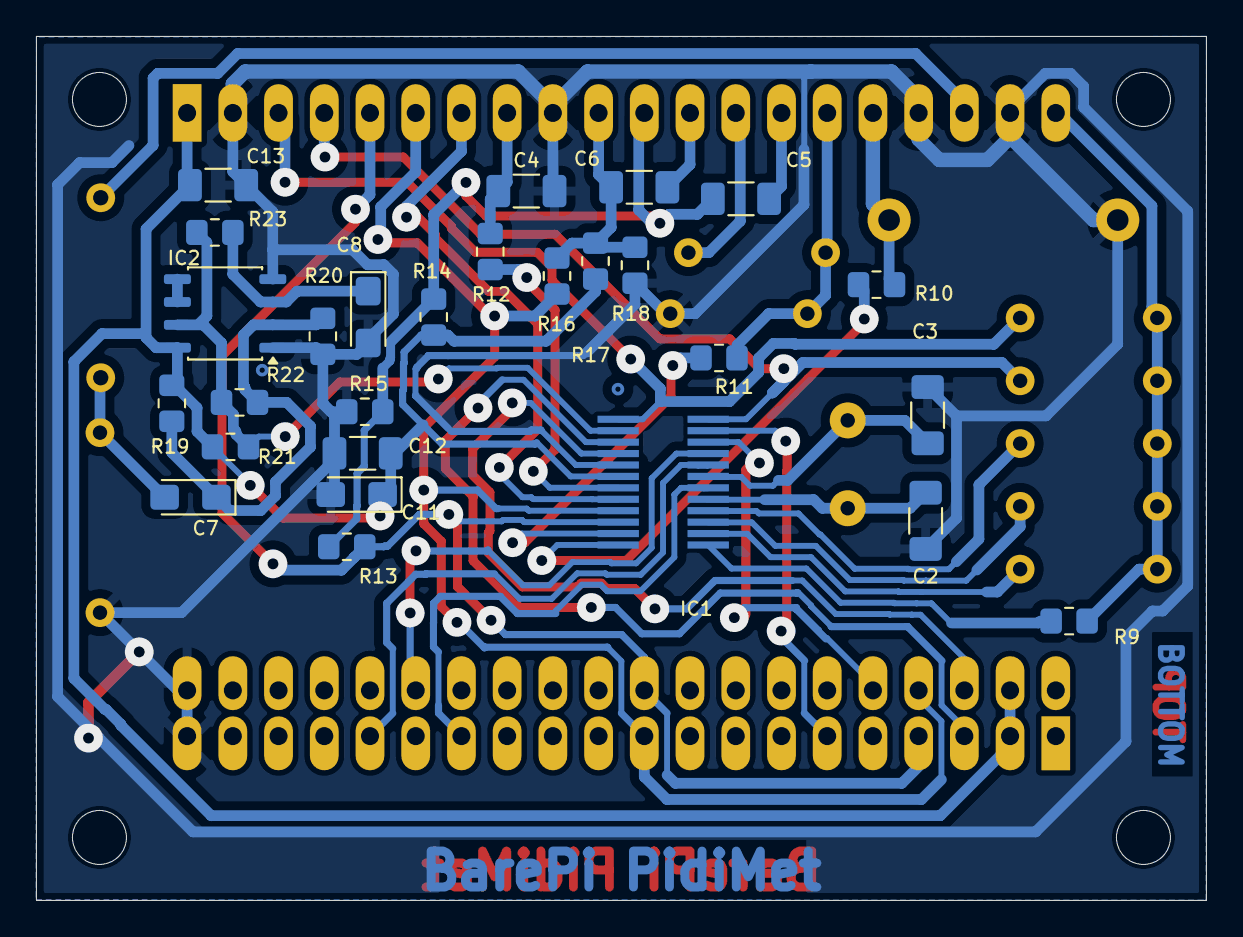
[picture p263: board BarePi_PidiMet.kicad_pcb from below]

Board: 2 copper layers, 65.0 x 48.0 mm, 40 parts (27 on the bottom side), 38 nets.
