Panda381/BarePi/TinyJoypad/KiCAD/BarePi_TinyJoypad.kicad_pcb

## KiCad design TinyJoypad/KiCAD/BarePi_TinyJoypad.kicad_pcb (2026-06-03)

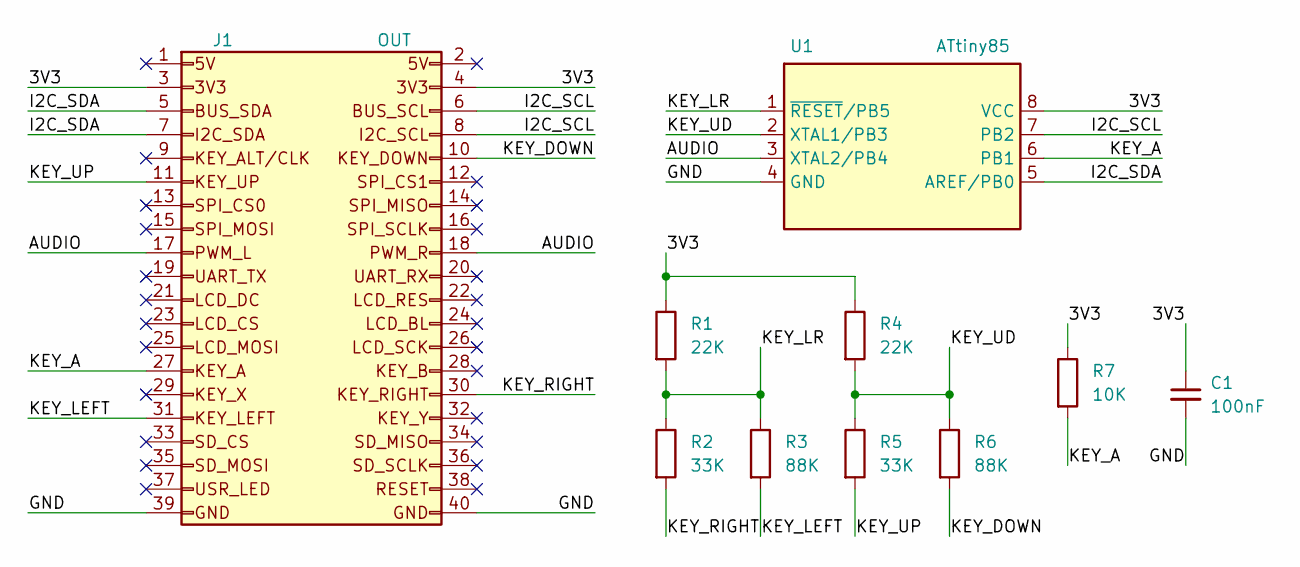
[picture p264: schematic BarePi_TinyJoypad.kicad_sch]

Parts:
C1: 100nF; C_1206_3216Metric_Pad1.33x1.80mm_HandSolder
J1: OUT; Raspberry_OUT_PinSocket_2x20_P2.54mm_Horizontal
R1, R4: 22K; R_1206_3216Metric_Pad1.30x1.75mm_HandSolder
R2, R5: 33K; R_1206_3216Metric_Pad1.30x1.75mm_HandSolder
R3, R6: 88K; R_1206_3216Metric_Pad1.30x1.75mm_HandSolder
R7: 10K; R_1206_3216Metric_Pad1.30x1.75mm_HandSolder
U1: ATtiny85; Raspberry_DIP-8_W7.62mm_Socket_LongPads

Connections:
/3V3: C1.1, J1.3, J1.4, R1.1, R4.1, R7.1, U1.8 (VCC)
/AUDIO: J1.17, J1.18, U1.3 (XTAL2/PB4)
/GND: C1.2, J1.39, J1.40, U1.4 (GND)
/I2C_SCL: J1.6, J1.8, U1.7 (PB2)
/I2C_SDA: J1.5, J1.7, U1.5 (AREF/PB0)
/KEY_A: J1.27, R7.2, U1.6 (PB1)
/KEY_DOWN: J1.10, R6.2
/KEY_LEFT: J1.31, R3.2
/KEY_LR: R1.2, R2.1, R3.1, U1.1 (~RESET/PB5)
/KEY_RIGHT: J1.30, R2.2
/KEY_UD: R4.2, R5.1, R6.1, U1.2 (XTAL1/PB3)
/KEY_UP: J1.11, R5.2
