Panda381/BarePi/TinyJoypad/KiCAD/BarePi_TinyJoypad.kicad_pcb

## KiCad design TinyJoypad/KiCAD/BarePi_TinyJoypad.kicad_pcb (continued)

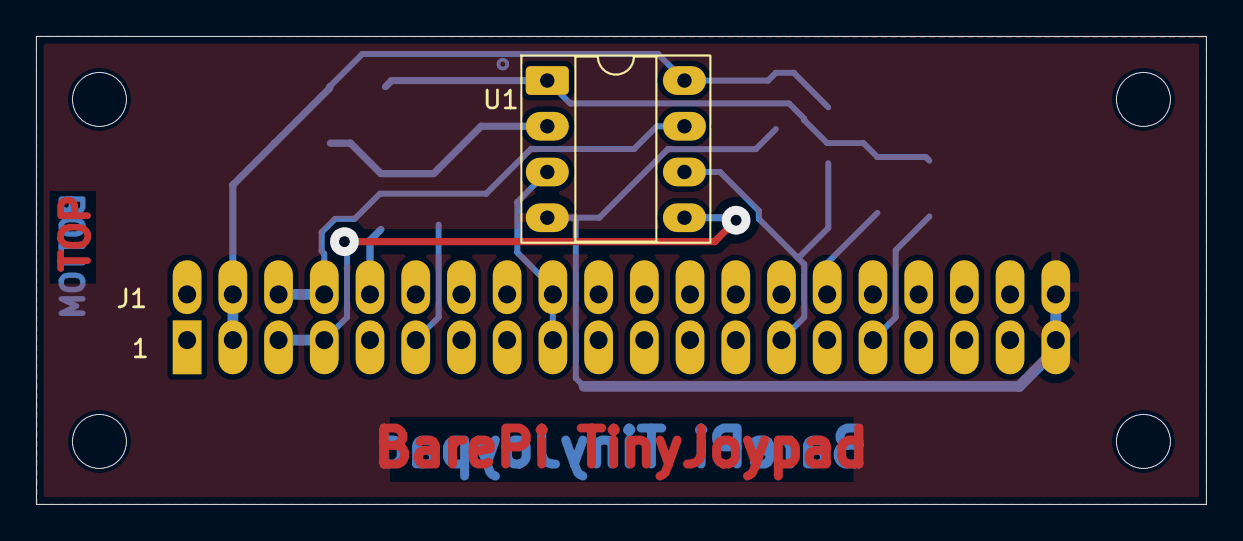
[picture p265: board BarePi_TinyJoypad.kicad_pcb from above]

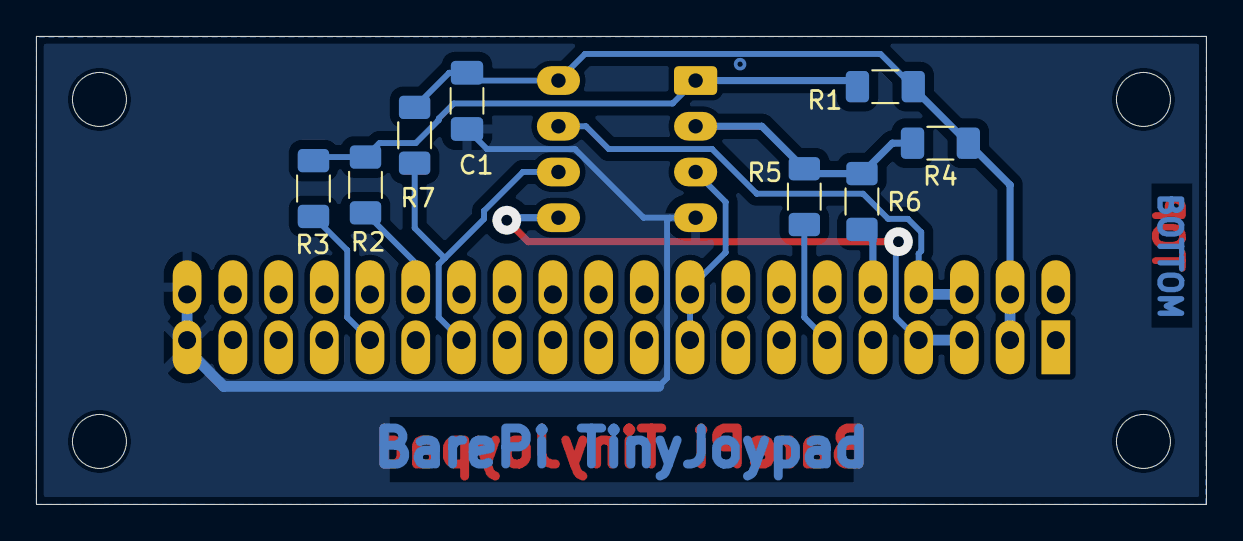
[picture p266: board BarePi_TinyJoypad.kicad_pcb from below]

Board: 2 copper layers, 65.0 x 26.0 mm, 10 parts (8 on the bottom side), 12 nets.
