Panda381/BarePi/DispHDMI/KiCAD/BarePi_DispHDMI.kicad_pcb

## KiCad design DispHDMI/KiCAD/BarePi_DispHDMI.kicad_pcb (2026-06-03)

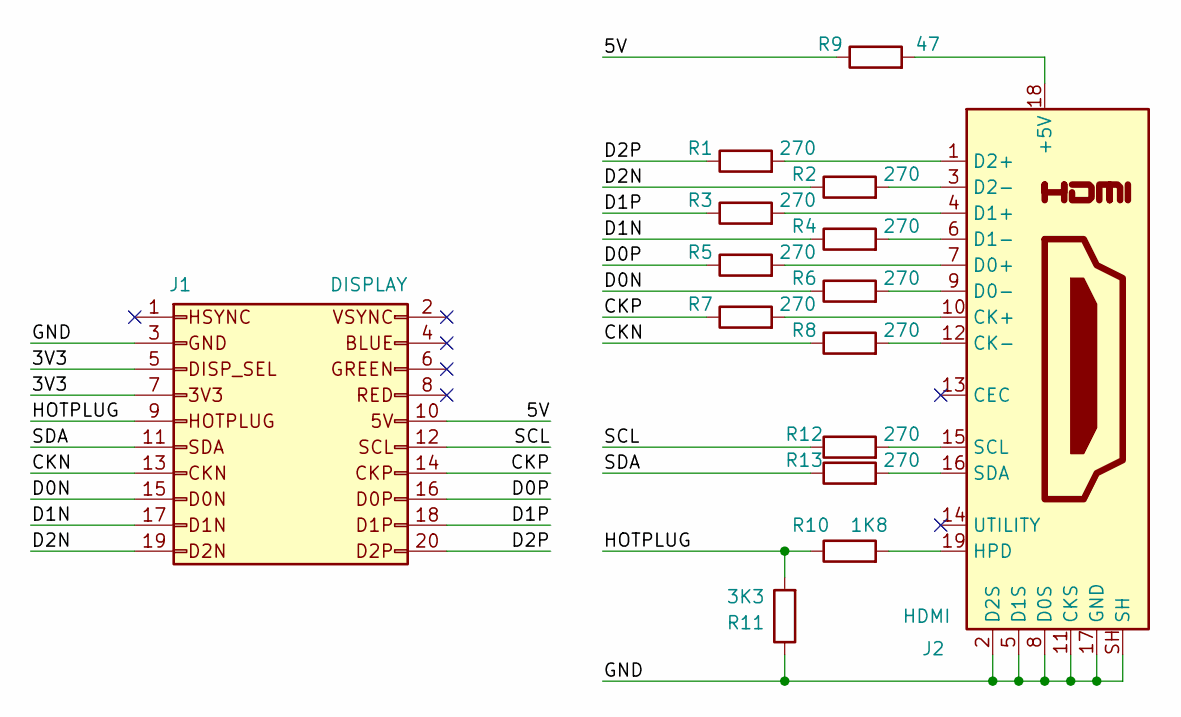
[picture p267: schematic BarePi_DispHDMI.kicad_sch]

Parts:
J1: DISPLAY; Raspberry_IN_PinHeader_2x10_P2.54mm_Horizontal
J2: HDMI; Raspberry_HDMI_A_Molex_208658-1001_Horizontal
R1, R2, R3, R4, R5, R6, R7, R8, R12, R13: 270; R_0805_2012Metric_Pad1.20x1.40mm_HandSolder
R9: 47; R_0805_2012Metric_Pad1.20x1.40mm_HandSolder
R10: 1K8; R_0805_2012Metric_Pad1.20x1.40mm_HandSolder
R11: 3K3; R_0805_2012Metric_Pad1.20x1.40mm_HandSolder

Connections:
/3V3: J1.5, J1.7
/5V: J1.10, R9.1
/CKN: J1.13, R8.1
/CKP: J1.14, R7.1
/D0N: J1.15, R6.1
/D0P: J1.16, R5.1
/D1N: J1.17, R4.1
/D1P: J1.18, R3.1
/D2N: J1.19, R2.1
/D2P: J1.20, R1.1
/GND: J1.3, J2.2 (D2S), J2.5 (D1S), J2.8 (D0S), J2.11 (CKS), J2.17 (GND), J2.SH, R11.1
/HOTPLUG: J1.9, R10.1, R11.2
/SCL: J1.12, R12.1
/SDA: J1.11, R13.1
unnamed: J2.18 (+5V), R9.2
unnamed: J2.10 (CK+), R7.2
unnamed: J2.12 (CK-), R8.2
unnamed: J2.7 (D0+), R5.2
unnamed: J2.9 (D0-), R6.2
unnamed: J2.4 (D1+), R3.2
unnamed: J2.6 (D1-), R4.2
unnamed: J2.1 (D2+), R1.2
unnamed: J2.3 (D2-), R2.2
unnamed: J2.19 (HPD), R10.2
unnamed: J2.15 (SCL), R12.2
unnamed: J2.16 (SDA), R13.2

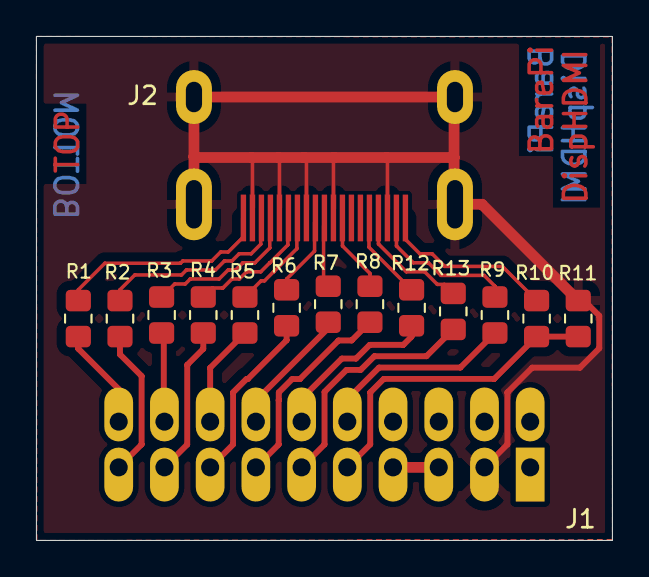
[picture p268: board BarePi_DispHDMI.kicad_pcb from above]

Board: 2 copper layers, 32.0 x 28.0 mm, 15 parts (0 on the bottom side), 26 nets.
