Panda381/BarePi/DispVGA/KiCAD/BarePi_DispVGA.kicad_pcb

## KiCad design DispVGA/KiCAD/BarePi_DispVGA.kicad_pcb (2026-06-03)

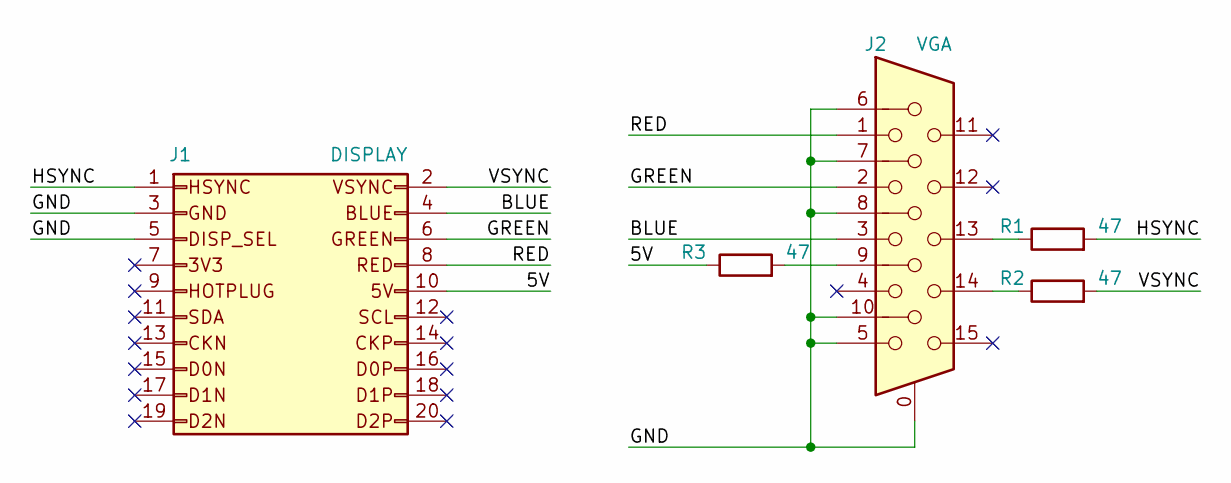
[picture p269: schematic BarePi_DispVGA.kicad_sch]

Parts:
J1: DISPLAY; Raspberry_IN_PinHeader_2x10_P2.54mm_Horizontal
J2: VGA; Raspberry_DSUB-15-HD_Socket_Horizontal
R1, R2, R3: 47; R_0805_2012Metric_Pad1.20x1.40mm_HandSolder

Connections:
/5V: J1.10, R3.1
/BLUE: J1.4, J2.3
/GND: J1.3, J1.5, J2.0, J2.5, J2.6, J2.7, J2.8, J2.10
/GREEN: J1.6, J2.2
/HSYNC: J1.1, R1.2
/RED: J1.8, J2.1
/VSYNC: J1.2, R2.2
unnamed: J2.9, R3.2
unnamed: J2.13, R1.1
unnamed: J2.14, R2.1

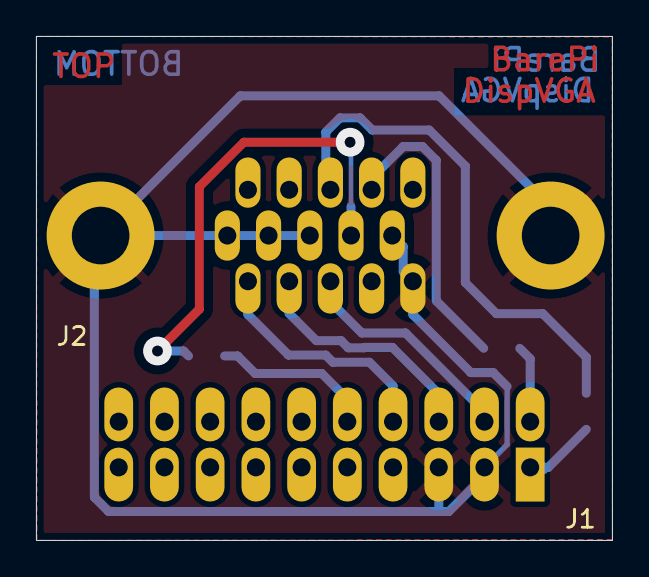
[picture p270: board BarePi_DispVGA.kicad_pcb from above]

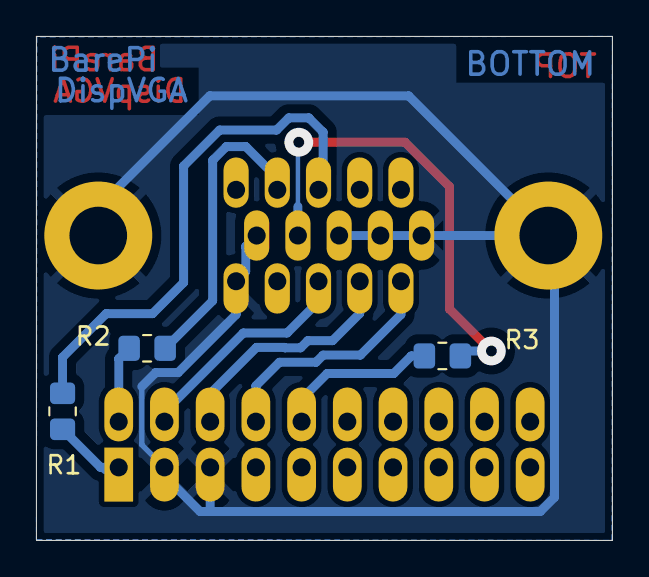
[picture p271: board BarePi_DispVGA.kicad_pcb from below]

Board: 2 copper layers, 32.0 x 28.0 mm, 5 parts (3 on the bottom side), 10 nets.
